lakewoodphone/tesla-lin-chip/hardware/tesla-dual-lin-rev-a/build/quote/jlcpcb-mini-order-2026-05-31/drc-routed-report.txt

** Drc report for tesla-dual-lin-rev-a.kicad_pcb **
** Created on 2026-05-31T14:52:18 **
** Report includes: Errors, Warnings, Exclusions **

** Found 0 DRC violations **

** Found 0 unconnected pads **

** Found 0 Footprint errors **

** Ignored checks **
    - Footprint has no courtyard defined
    - Track endpoint not centered on via
    - Tuning profile track geometries
    - Footprint doesn't match symbol's footprint filters
    - Footprint component type doesn't match footprint pads
    - Footprint doesn't match copy in library

** End of Report **
