lakewoodphone/tesla-lin-chip/BENCH_EVIDENCE.md

# No-Car Bench Evidence

_Updated: May 27, 2026._

This file records the strongest bench-only evidence collected before touching a car. The goal is to prove the APGDT001 -> TJA1021 -> level shifter -> XIAO receive chain, parser, checksum handling, candidate-ID handling, anti-nag replay sequence, and secretary API telemetry path.

**Repository default firmware is passive (`field_passive`).** Active injector firmware with BLE config is explicit via `bench_active_ble` or `chip_lab_active`. In active lab mode, XIAO generates anti-nag frames on UART1 TX with runtime model switching (`model:x`, `model:3`, `model:y`), BLE configuration via "TeslaAntiNag" service, and double-click toggle. See `ACTIVE_INJECTOR.md`.

## Hardware Under Test

- Host: `ZABZ-TECH` desktop
- XIAO: ESP32-C3 on `COM4`, USB VID/PID `303A:1001`
- APGDT001: USB LIN analyzer, VID/PID `04D8:0A04`
- LIN transceiver: TJA1021 module
- Bench LIN baud: `19200`
- Receive path: APG LIN -> TJA1021 LIN/RX -> level shifter -> XIAO D3/GPIO5
- Active TX path: XIAO D2/GPIO4 -> level shifter LV2/HV2 -> TJA1021 TX
- Power: APG VBAT and TJA1021 VIN tied to bench 12V, common ground, SLP high

## Full Evidence Suite

Command:

```powershell
cd C:\Users\ezabz\Code\xiao-lin-bench
.\tools\bench-evidence-suite.ps1 `
  -VehicleId tesla-bench-full-20260526 `
  -ComPort COM4 `
  -Baud 19200 `
  -BootWaitSeconds 2 `
  -PerFrameTimeoutMs 1600 `
  -DelayMs 75
```

Result:

```text
Bench evidence complete: 80/80 exact matches, observed=80, apgFailures=0
```

Phase breakdown:

| Phase | Cases | Observed | Exact Match |
|---|---:|---:|---:|
| baseline | 3 | 3 | 3 |
| candidate | 2 | 2 | 2 |
| checksum | 2 | 2 | 2 |
| id-sweep | 64 | 64 | 64 |
| antinag | 9 | 9 | 9 |

What this proves:

- XIAO receives and decodes every raw LIN ID from `0x00` through `0x3F` on the isolated bench.
- Protected PID parity validates for every sweep case.
- Enhanced checksums validate on normal frames.
- Classic checksum validation is proven on diagnostic `0x3C`.
- Model X control frames on `0x0C` decode correctly for idle, up, down, and neutral.
- Model 3/Y candidate IDs `0x1A` and `0x1B` decode cleanly as bench candidates.
- Anti-nag UP/DOWN replay plus neutral end frame decodes exactly.
- The USB serial fallback path posts parsed frames to the secretary API even while XIAO WiFi is unavailable.

Generated local artifacts are under ignored `logs/`:

```text
logs\bench-evidence-20260526_211956\bench-evidence-20260526_211956.md
logs\bench-evidence-20260526_211956\bench-evidence-20260526_211956.csv
logs\bench-evidence-20260526_211956\bench-evidence-20260526_211956.json
logs\bench-evidence-20260526_211956\xiao-serial-20260526_211956.log
logs\bench-evidence-20260526_211956\apg-send-20260526_211956.log
```

Secretary API verification:

```powershell
curl "http://localhost:8002/api/v1/lin-stats?vehicle=tesla-bench-full-20260526&limit=10000" | python -m json.tool
```

Observed API result:

```text
total_frames=80
bad_checksum=0
bad_parity=0
unique_ids=64
```

## Quick Evidence Suite

Command:

```powershell
.\tools\bench-evidence-suite.ps1 `
  -Quick `
  -VehicleId tesla-bench-quick-20260526 `
  -ComPort COM4 `
  -Baud 19200 `
  -BootWaitSeconds 3 `
  -PerFrameTimeoutMs 1800
```

Result:

```text
Bench evidence complete: 32/32 exact matches, observed=32, apgFailures=0
```

Use the quick suite before field work when time is short. Use the full suite after wiring or parser changes.

## Standalone Anti-Nag Replay

Command:

```powershell
cmd /c %WINDIR%\SysWOW64\WindowsPowerShell\v1.0\powershell.exe `
  -STA -NoProfile -ExecutionPolicy Bypass `
  -File tools\antinag-replay.ps1 `
  -Id 0x0C `
  -Repeat 2 `
  -DelayMs 150 `
  -NeutralFrames 2
```

Result:

```text
Replay complete - 6 frames sent
```

The replay script now launches the APG sender as a fresh 32-bit PowerShell child process per frame. That avoids NetworkAnalyser state leakage and fixes the earlier final-neutral failure.

## New Bench Tools

| Tool | Purpose | Vehicle-safe? |
|---|---|---|
| `tools/bench-evidence-suite.ps1` | Runs baseline, candidate, checksum, raw ID sweep, and anti-nag no-car tests; writes CSV/JSON/Markdown evidence and posts to secretary | No, transmits |
| `tools/serial-to-lin-events.ps1` | Bridges XIAO USB serial decoded frames into `POST /api/v1/lin-events` when WiFi is unavailable | Passive if APG/vehicle is passive |

## Active Injection Status (May 27, 2026)

- Active Model X bench TX is validated on the isolated bench.
- Working firmware break generation: half-baud UART `0x00` break, then normal LIN baud for sync/PID/data/checksum.
- Fixed physical fault: D2 -> level shifter LV2 jumper was disconnected. With `txd:low`, XIAO D2, LV2, and HV2/module TX measured near 0V.
- `model:x` + `antinag:start` produced >100 XIAO self-received/ring-buffer frames on ID `0x0C` with enhanced checksums and parity OK.
- Representative ring evidence:

```text
ID=0x0C PID=0x4C [8B] data: 11 04 00 00 00 00 C0 00 | chk=DD enhanced parity=OK
ID=0x0C PID=0x4C [8B] data: 0F 04 00 00 00 00 C0 02 | chk=DD enhanced parity=OK
ID=0x0C PID=0x4C [8B] data: 10 00 00 00 00 00 C0 0A | chk=D8 enhanced parity=OK
```

NetworkAnalyser event/display passive capture still logged zero rows for XIAO-generated frames during this session, even while XIAO self-receive parsed valid active frames. This is now characterized as a NetworkAnalyser event-layer limitation for externally generated bench frames, not a wiring failure.

`tools/active-bench-proof.ps1` now automates this active self-receive proof and saves a log plus Markdown summary under `logs/`.

### Evening revalidation, 2026-05-27

The latest bench work is summarized in `docs/bench-revalidation-2026-05-27.md`.

- `tools/build-all-envs.ps1` passed for all firmware environments.
- `bench_active_ble` flashed successfully to the physical XIAO on `COM4`.
- BLE advertising was fixed and verified: `cmd: BLE advertising=yes`, with the expected service and characteristic UUIDs. The root cause was an invalid too-fast NimBLE advertising interval that produced `rc=3` / `BLE_HS_EINVAL`.
- Active Model X self-receive proof passed again after APG reseat: `logs\active-bench-proof-20260527_211924.md`.
- Representative proof frames used realistic non-zero payload bytes and validated with enhanced checksum/parity OK:

```text
ID=0x0C PID=0x4C [8B] data: 11 04 10 00 00 00 C0 00 | chk=CD enhanced parity=OK
ID=0x0C PID=0x4C [8B] data: 0F 04 08 02 00 00 C0 02 | chk=D3 enhanced parity=OK
```

- Final XIAO state after the run was safe: `armed=no`, `running=no`, `faults=0`, `lockout=no`, `badChk=0`, `badPid=0`.
- APGDT001 recovered after physical reseat: Windows reports `CM_PROB_NONE`, passive APG transmit works, and raw PICkitS initialization works.
- Quick passive APG -> XIAO validation passed: `logs\xiao-bench-validation-20260527_211238.log`.
- Full passive evidence suite passed again: `logs\bench-evidence-20260527_211310\bench-evidence-20260527_211310.md` with 80/80 exact matches, observed=80, apgFailures=0.
- `tools\active-apg-raw-proof.ps1` now preflights APG raw monitor initialization before active TX, forces `mode:always` during capture to avoid duty-cycle quiet windows, then stops output, runs `safe:off`, and restores `mode:duty`.

## APG Known-ID Raw Observer Proof (May 27, 2026)

The APG does see the XIAO active bench frames at the raw USART buffer layer. `monitor-apg-lin-bus.ps1 -RawFallback` bypasses the NetworkAnalyser event parser, polls `PICkitS.Basic.Retrieve_USART_Data`, scans for 8-byte payload + checksum windows, validates against the assumed raw ID, and writes normal CSV rows with `source=raw`.

Command:

```powershell
powershell -NoProfile -ExecutionPolicy Bypass -File tools\active-apg-raw-proof.ps1 -ComPort COM4 -Baud 19200 -DurationSeconds 6 -MinFrames 8 -ConfirmBenchIsolation
```

Result:

```text
CSV: logs\lin-capture-20260527_212130.csv
XIAO TX lines observed: 41
APG raw rows observed: 11
PASS: APG raw fallback captured 11 checksum-valid known-ID frames.
```

Representative APG raw CSV rows:

```text
ID=0x0C PID=0x4C [8B] data: 0F 04 00 00 00 00 C0 0D source=raw error=0 baud=19200
ID=0x0C PID=0x4C [8B] data: 11 04 00 00 00 00 C0 08 source=raw error=0 baud=19200
ID=0x0C PID=0x4C [8B] data: 0F 04 00 00 00 00 C0 0B source=raw error=0 baud=19200
```

## Remaining No-Car Limits

- The bench can prove parser correctness, checksum behavior, APG send behavior, telemetry plumbing, and XIAO self-received active injection on the isolated bench.
- It cannot identify actual Model 3/Y steering IDs without passive vehicle capture.
- It cannot prove Tesla accepts any anti-nag sequence. Vehicle work must start passive only.
- Generic vehicle discovery still needs normal passive capture because raw fallback requires a known ID. The active Model X bench observer path is proven with APG raw fallback.
- If the APGDT001 returns to Windows failed-start state, recover it before APG-dependent validation; the current post-reseat state is healthy and proven.
