lakewoodphone/tesla-lin-chip/CAPTURE_LOG.md

vehicle_id,model,capture_date,car_day_laptop,notes
tesla-model-x-moti,Model X,2026-05-17,laptop,First successful passive capture - SW white wire seated
tesla-bench-quick-20260526,Bench,2026-05-26,desktop ZABZ-TECH,Quick no-car suite passed 32/32 exact matches and posted 32 USB-serial frames to secretary
tesla-bench-full-20260526,Bench,2026-05-26,desktop ZABZ-TECH,Full no-car suite passed 80/80 exact matches across raw IDs 0x00-0x3F with 0 checksum/parity failures
tesla-model-3-unknown,Model 3,2026-05-26,not-yet,Candidate discovery needed - IDs 0x1A/0x1B suspected
tesla-model-y-unknown,Model Y,2026-05-26,not-yet,Same as 3 - verify IDs independently
