lakewoodphone/tesla-lin-chip/logs/active-bench-proof-20260527_134529.md

# Active Bench Proof 20260527_134529

- Port: COM4
- Model: x
- Duration seconds: 6
- Active acknowledged: True
- Stop acknowledged: True
- TX lines observed: 90
- Valid Model X ring frames: 256
- Bad checksum/parity stats seen: False
- Result: PASS

## Notes

This is isolated-bench evidence only. It uses XIAO self-receive/ring validation because APG passive monitor did not log XIAO-generated active frames during the May 27 validation session.

## Logs

- Text log: C:\Users\ezabz\Code\xiao-lin-bench\logs\active-bench-proof-20260527_134529.log
