lakewoodphone/tesla-lin-chip/logs/sessions/20260528_204047-car-passive-tesla-model-3-20260528/preflight-car-passive-20260528_204050.md

# Hardware Preflight 20260528_204050

- Mode: car-passive
- Created: 2026-05-28T20:40:50
- Result: FAIL
- Failures: slp_high, rx_path, com_port_free, apg_present

| Check | Result |
|---|---|
| 12v_present | 15V |
| common_ground | y |
| slp_high | no |
| lin_idle_voltage | no |
| rx_path | no |
| tx_path | no |
| tx_physical_state | no |
| com_port_free | no |
| apg_present | no |
| notes | no |
