lakewoodphone/tesla-lin-chip/research/responses/2026-05-17-research-directive-authoritative-lin-receiver-design-for-esp32-c3-capture-datash-c416c8f4.md

---
job_id: c416c8f4-e300-483e-8620-139dbf18d3eb
directive_id: research-directive-authoritative-lin-receiver-design-for-esp32-c3-capture-datash
title: Research Directive: Authoritative LIN Receiver Design for ESP32-C3 Capture (Datasheet-Grade Sources Only)
domain: automotive_re
sensitivity: no_refusal_required
model_used: sonar-deep-research
provider: perplexity
status: complete
completed_at: 2026-05-17T19:58:29.068617+00:00
cost_usd: 0.47788
input_tokens: 579
output_tokens: 15282
reasoning_tokens: 51163
search_count: 36
citation_count: 26
verifier_status: passed
schema_version: 1
---

# Authoritative LIN Receiver Design for ESP32‑C3 Passive Capture

Developing a robust Local Interconnect Network (LIN) receiver front end for an ESP32‑C3 that is tapped into a vehicle LIN bus, especially in a Tesla context, requires reconciling three domains: the ESP32‑C3 digital input constraints at 3.3 V, the LIN physical‑layer signaling on a 12 V single‑wire bus, and the harsh automotive electrical environment around that bus. This report synthesizes datasheet‑grade sources and relevant standards to derive quantified input‑threshold and margin requirements, explains why divider‑only taps are fundamentally fragile, and then converges on two concrete hardware architectures: a field‑deployable “safe capture” design and a production‑grade design suitable for long‑term in‑vehicle use. The analysis establishes that the ESP32‑C3’s CMOS‑style 3.3 V inputs expect relatively clean rail‑to‑rail swings with sufficient noise margin that cannot be guaranteed by directly attenuating the LIN line, whose signaling thresholds are defined as percentages of an often noisy battery supply rather than absolute logic levels.[2][2][8] Instead, a proper LIN transceiver—such as Microchip’s MCP2025‑330, NXP’s TJA1028 or TI’s TLIN821‑Q1—must be used to translate between the LIN bus and the ESP32‑C3’s UART RX, while also supplying the necessary ESD robustness, load‑dump survivability, and EMC performance that a simple resistor network cannot provide.[4][4][4][9][16][18][24] Complementary front‑end protection measures, including carefully chosen transient‑voltage suppressors, reverse‑battery protection on supply rails, and low‑capacitance ESD arrays for MCU pins, complete the design.[21][22][25] On top of this hardware, the report defines measurable acceptance criteria in terms of waveform integrity, error rates, and electrical margins to decide when a “passive capture” prototype is good enough, and concludes with a strict set of “do not do” rules to protect customer vehicles and test personnel.

---

## ESP32‑C3 Input Constraints Relevant to LIN‑Derived UART Reception

### Overview of ESP32‑C3 I/O and UART Architecture

The ESP32‑C3 is a RISC‑V–based SoC from Espressif intended for IoT and embedded applications, operating with a 3.3 V I/O domain for its general‑purpose input/output (GPIO) pins and UART peripherals.[14] The device integrates multiple UART controllers which can be mapped to a variety of GPIO pins through the I/O matrix, providing flexibility in pin assignment for RX and TX.[1][1][14] The official UART driver documentation for ESP‑IDF describes the process of configuring a UART channel, assigning its RX and TX functions to GPIOs, and then using it for asynchronous serial communication with typical parameters such as baud rate, data bits, stop bits, and parity.[1][1] Although the documentation focuses on logical parameters and software configuration, the underlying expectation is that the RX pin sees 3.3 V‑domain digital signals with sufficiently fast edges and well‑defined logic‑level thresholds.

The ESP32‑C3 datasheet identifies the pins that are by default associated with UART0 (GPIO20 and GPIO21) but also notes that these pins can be re‑routed or reconfigured as generic GPIOs if necessary, emphasizing that the UART functions use the same electrical input buffers as other digital inputs on the device.[14] The technical reference manual points out that these inputs reside in a 3.3 V domain and that the default drive strengths for GPIO outputs are on the order of 10–40 mA, implying that the I/O cells are dimensioned for conventional digital signaling rather than slow, high‑impedance analog levels.[6][14] Together, the UART and GPIO documentation make it clear that an ESP32‑C3 UART RX pin should be treated as a standard 3.3 V CMOS‑style digital input with Schmitt‑like behavior typical of microcontroller GPIOs, not as an analog comparator that can be directly attached to a 12 V automotive bus via passive attenuation.

From the point of view of UART decoding, the ESP32‑C3’s internal UART logic expects voltage swings that are unambiguous with respect to the input thresholds, with adequate noise margin, over the entire duration of each bit time at the configured baud rate.[1][1] Because LIN bus speeds typically range from 1 kbit/s up to 20 kbit/s, with common values around 9.6 kbit/s, 10.4 kbit/s, or 19.2 kbit/s, a UART on the ESP32‑C3 can easily be configured to match the LIN frame data rate.[2][8][2] However, for such configuration to result in reliable bit sampling, the RX signal must faithfully reproduce the LIN logical waveform as a clean 0–3.3 V signal with correct timing and edges.

### ESP32‑C3 Digital Input Thresholds and Margins

Espressif’s public documentation for the ESP32‑C3 series describes the 3.3 V supply domains and GPIO usage, but in the excerpts available here, it does not explicitly list numeric values for the VIH (minimum high‑level input voltage) and VIL (maximum low‑level input voltage) thresholds.[14] In the absence of explicit figures, design practice for 3.3 V CMOS microcontroller inputs generally assumes that VIH is at least approximately 0.7–0.8 × VDD and VIL is at most approximately 0.2–0.3 × VDD, but since these numbers are not directly quoted from the ESP32‑C3 datasheet in the provided material, they must be treated as indicative rather than guaranteed values. The key point is that the ESP32‑C3 does not support 5 V‑tolerant inputs on its GPIO pins, so any applied signal must remain within the absolute 3.3 V domain, including transients, to avoid device damage or latchup.[14]

From a system perspective, for a 3.3 V domain, a safe design target is to ensure that logical high on the UART RX pin reaches at least about 2.3–2.5 V (to clear typical CMOS VIH margins) and that logical low remains below about 0.8 V, with additional allowance for noise and ground offsets. These numbers are not taken directly from Espressif documentation but represent a conservative engineering assumption aligned with common 3.3 V CMOS input specifications. Because the LIN physical layer is defined relative to the battery voltage rather than an absolute logic rail, any attempt to map the LIN waveform to this 0–3.3 V domain must ensure that for all anticipated variations in VBAT, line noise, and transceiver tolerances, the resulting RX signal still satisfies these margins.

The ESP32‑C3’s I/O architecture also implies that input pins should not see overshoot or undershoot beyond the supply rails, except for brief ESD‑like events that are handled by internal structures only within limited energy constraints.[14] In a vehicle LIN environment, where ESD, inductive switching, and load dump can produce surges far in excess of the microcontroller’s safe operating range, protection must be provided externally. This is a key reason why Espressif and other MCU vendors recommend using dedicated automotive‑grade transceivers or interface devices when connecting to automotive buses instead of using simple passive components.

### UART Timing Requirements versus LIN Bit Timing

The LIN specification allows bit rates from 1 kbit/s up to 20 kbit/s, with a bit rate tolerance on the order of ±14 %, reflecting the use of low‑cost internal oscillators in many LIN nodes.[2][2][2] The TX and RX devices in a LIN cluster must therefore tolerate significant baud rate mismatch while still sampling bits correctly at the defined relative positions within each bit time. A standard UART in the ESP32‑C3 is well able to handle bit rates in this range, and software can be configured for nominal rates such as 9600, 10400, or 19200 baud to match the LIN master’s configuration.[1][1][8] However, the actual decoding margin is affected not only by baud rate match but also by edge placement and waveform integrity at the RX pin.

Because an ESP32‑C3 UART samples at multiple points in each bit period and makes decisions based on instantaneous voltage crossing the input thresholds, any slow rise or fall of the RX signal can cause timing skew, jitter, or misinterpretation of bits. A pure resistor divider attached to the LIN bus significantly loads and distorts the line’s RC characteristics, especially during recessive‑to‑dominant transitions where the bus is pulled low by an NPN or MOSFET driver through relatively limited current.[2][8][2] This means that even if a divider produces correct peak voltage levels, the slower transitions may cross the ESP32‑C3 thresholds too late or too early compared to ideal digital signals, leading to subtle framing errors or bit‑level decoding failures at the UART layer.

### ESP32‑C3 I/O Protection Considerations

Although the ESP32‑C3 includes some on‑die ESD protection for its pins, this is designed for typical board‑level handling and not for direct exposure to the automotive electrical environment. The datasheet emphasizes that GPIOs should stay within the 3.3 V domain limits and that external circuitry must constrain any larger or more energetic transients before they reach the chip.[14] In contrast, automotive devices such as LIN transceivers or CAN transceivers are explicitly rated for ESD events of many kilovolts and for load‑dump events up to tens of volts for extended durations.[4][4][4][5][16]

For the UART RX pin used as a LIN capture input, best practice is to place a low‑capacitance ESD/TVS array very close to the pin, especially in a vehicle context where ESD strikes, cable plug/unplug events, and coupling from higher‑voltage systems are common.[10][10][25] Littelfuse’s SP3012 series, for example, integrates several channels of ultra‑low‑capacitance rail‑to‑rail diodes and a zener diode to shunt electrostatic discharge to ground and supply rails, while maintaining typical capacitance on the order of 0.5 pF per I/O and leakage currents in the microampere range, characteristics that are compatible with high‑speed data lines and sensitive digital I/Os.[10][25] These arrays are qualified to AEC‑Q101 and are therefore appropriate for use in automotive applications, giving confidence that they can withstand repeated IEC‑61000‑4‑2 level ESD strikes without degrading.[25]

In summary, from the ESP32‑C3 side, the constraints can be distilled to three main points. First, the RX pin is a 3.3 V CMOS‑style input that requires well‑defined high and low logic levels with adequate margin. Second, it cannot tolerate direct connection to automotive‑level voltages or high‑energy transients, so it must be isolated from the LIN bus environment by appropriate transceivers and protection circuitry. Third, its timing and signal‑integrity expectations are those of a standard UART input, not of an analog comparator; therefore, any design must ensure sufficiently fast and clean transitions at the RX pin that correspond to the LIN digital semantics.

---

## LIN Physical Layer Signaling and Why Divider‑Only Taps Fail

### LIN Voltage Levels and Threshold Definitions

The LIN physical layer is standardized as a 12 V or 24 V single‑wire bus based on ISO 9141‑style K‑line signaling, with typical use in low‑speed automotive subsystems where full CAN bus complexity is unwarranted.[2][2][8][26] In a 12 V system, the LIN line is pulled up towards the battery supply VBAT through a resistor, typically located in the master node, while slave nodes include their own pullups or internal biasing structures with higher resistance values.[2][20] All nodes connect to the shared LIN wire and ground, resulting in an effective open‑drain bus where any active driver can pull the line low to signal a dominant state, while the recessive state corresponds to the bus floating high towards VBAT via the pullups.[2][8][20]

Texas Instruments’ application report on LIN protocol and physical layer requirements describes the voltage thresholds in terms of percentages of the battery voltage rather than fixed absolute values.[2][2][2] For transmitting (sending) nodes, a dominant low level is achieved by driving the LIN line down towards approximately 20 % of VBAT, while the receiving nodes interpret a dominant bit when the bus voltage falls to at or below 40 % of VBAT.[2][2] For recessive high levels, the transmitter aims to drive the line up to roughly 80 % of VBAT, while receivers interpret a recessive bit when the voltage rises to at least 60 % of VBAT.[2][2][8] This difference in sender and receiver thresholds provides margin to accommodate drops along the wire, differences in node supply voltages, and other imperfections, ensuring that even with some degradation, receivers will still detect proper logic states.

As an example, consider a 12 V system with VBAT = 12 V nominal. In such a system, a typical recessive threshold at the receiver is about 0.6 × 12 V = 7.2 V, while the sender may aim for 0.8 × 12 V = 9.6 V for a recessive high.[2][2][8] For dominant low, the receiver threshold of about 0.4 × 12 V corresponds to 4.8 V, while the sender aims to drive the line towards 0.2 × 12 V = 2.4 V.[2][2] Any receivers on the bus include internal comparators whose switching thresholds track VBAT or a derived reference such that they operate correctly over a wide supply range, generally 6–18 V or more.[4][2][4][20][2] This approach contrasts sharply with the fixed 3.3 V logic levels expected by the ESP32‑C3.

Because of these percentage‑based thresholds, the absolute voltage swings on the LIN line vary not only with instantaneous VBAT but also with system operating conditions, transceiver design, and load. Furthermore, because the transceiver must survive conditions such as load dump (where VBAT can momentarily rise to 40–43 V) and must withstand reverse battery connections, its analog front end, including the line pin, is designed with robust high‑voltage devices and protective circuits not present in a typical microcontroller input.[4][4][18][21]

### Pullup Structure and Bus Topology

The LIN bus is architecturally equivalent to an open‑drain or open‑collector network, in which a central master (commander) node provides a main pullup resistor to VBAT, often around 1 kΩ in series with a diode to guard against reverse battery, while each responder node includes an internal pullup, typically around 30 kΩ, integrated within its transceiver IC.[2][8][2] Texas Instruments’ characterization indicates that the standard configuration uses a relatively low‑value pullup in the master, such as 1 kΩ (with options like 600 Ω or 500 Ω being also seen), which ensures sufficiently strong recessive bias, while responder nodes rely on their internal higher‑value pullups to define logic levels when the master is powered down or disconnected.[2][2]

In this network, the bus voltage in the idle, recessive state is close to VBAT, minus any drop across the master’s pullup diode and resistor. Nodes monitor the bus voltage through comparators that interpret transitions between dominant and recessive based on the previously described percentage thresholds.[2][2][8] The net effect is that the bus is relatively high impedance in the recessive state, with a limited source current defined by the pullup resistor and the total bus capacitance dominated by the wiring harness and all node input capacitances.[2][8][2] Any additional load or capacitance attached to the LIN line modifies this RC network and can adversely affect edge rates, overshoot, and susceptibility to noise.

Because the LIN bus is single‑wire and single‑ended, it is more vulnerable than differential buses like CAN to electric field coupling, ground offsets, and voltage disturbances.[5][8][8] The design of each LIN transceiver therefore includes filtering, slew‑rate control, and EMC hardening to shape the waveform on the bus in a way that both meets emission standards and guarantees that all receivers correctly interpret the bits within their sampling windows.[4][2][4][16][2] Any external network added by a tapping device, such as a passive monitoring tool, must respect these subtleties to avoid both interfering with the bus and degrading its own ability to decode messages.

### Why Simple Resistor Dividers Fail to Reliably Decode LIN

A common intuition is to attach a resistor divider from the LIN line to a 3.3 V input, scaling the 12 V peak down to a safe voltage for the microcontroller while leaving the bus otherwise undisturbed. While this may appear to work under ideal conditions in a lab, it is fundamentally fragile in a real vehicle environment for several reasons that follow directly from the physical layer definition.

First, the LIN line is defined relative to VBAT with thresholds like 40 % and 60 % for receiving nodes, not as an absolute pair of logic levels.[2][2][8] Suppose a divider is designed on the assumption that VBAT is 12 V and that the bus recessive level will be approximately 12 V while dominant levels will be around 2–4 V. Scaling this down linearly to a 3.3 V domain may result in recessive levels near 3.3 V and dominant levels somewhere around 0.6–1.2 V. For a 3.3 V CMOS input expecting a clear distinction between, say, below 0.8 V for low and above 2.3 V for high, this might be marginal, especially when the LIN sender’s dominant level is closer to 4.8 V (40 % of 12 V) than to 2.4 V (20 % of 12 V).[2][2] In other words, the available headroom between scaled “dominant high” and the VIH threshold of the ESP32‑C3 might be insufficient, especially over temperature, VBAT variation, and process variation of the MCU input buffers.

Second, because the pullup strength on the LIN line is limited by the master resistor (approximately 1 kΩ) and the bus capacitance can be significant over several meters of harness, the recessive‑to‑dominant and dominant‑to‑recessive transitions are already controlled and limited.[2][8][2] Introducing a resistor divider to ground from the bus adds a permanent parallel load that increases the effective capacitance and reduces the pullup strength seen by the line. This results in slower rise times for recessive transitions and altered waveforms during dominant pulses. At low baud rates, this might still be decodable, but as bit rates approach 20 kbit/s, degradation of edge sharpness can cause the ESP32‑C3’s UART sampling to misinterpret bits, particularly if its internal sampling point is placed near the middle of the bit time and the waveform crosses the digital thresholds slowly.[2][2][8][2]

Third, the LIN physical environment involves not only logic transitions but also significant disturbances, such as transient dips in VBAT, noise from motors and inductive loads, and ESD events imposed on the harness.[2][8][20][2] A purpose‑built LIN transceiver includes common‑mode filters, clamping structures, and internal hysteresis tailored to this environment, ensuring that spurious noise around the thresholds does not cause false bits. A resistor divider feeding a generic CMOS input does not provide these protections or hysteresis. As a result, the ESP32‑C3 input may see multiple threshold crossings caused by ringing, noise spikes, or partial line interruptions, leading to frame corruption even when the LIN receivers in the ECUs continue to operate correctly.

Texas Instruments’ application report explicitly notes that all nodes are passively connected to the bus through their transceivers and that a pullup resistor is necessary at the master to ensure the bus is at VBAT when nodes are off, essentially creating an open‑drain circuit with controlled behavior.[2][2] By contrast, a bare resistor divider does not include the bidirectional, half‑duplex buffer and level‑translation functionality that a LIN transceiver provides. Microchip’s MCP2025, for instance, is expressly described as a bidirectional, half‑duplex communication physical interface designed to translate CMOS/TTL logic levels to LIN bus levels and vice versa, compliant with LIN versions 1.3 and 2.x and SAE J2602.[4][4][4] Attempting to emulate this behavior with only passive resistors ignores essential elements like driver current limiting, distributed capacitance, and protective functions, which is why such minimalist designs may sometimes work on a bench but are not reliable in an actual vehicle.

Fourth, the battery voltage itself can vary significantly, from perhaps 9 V under cranking to 16 V during charging and transient peaks much higher during load dump or regulator malfunctions.[2][2][4] The LIN receiver thresholds track VBAT or a derived reference so they remain valid over this range. A fixed resistor divider designed for 12 V may therefore produce scaled high and low levels that move substantially relative to the fixed 3.3 V logic thresholds of the MCU. For example, under a high VBAT scenario, the recessive level might approach the MCU’s maximum input rating, while under low VBAT, the dominant level may not fall far enough below the high threshold to be recognized as a clean low. This is an inherent mismatch between a bus whose logic definition is proportional to VBAT and a receiver whose logic thresholds are anchored to a fixed 3.3 V rail.

Finally, there is the safety and EMC aspect. Automotive‑grade LIN transceivers are qualified under AEC‑Q100, implement defined ESD and EMC protections, and can withstand continuous input voltages up to 30 V and load‑dump levels up to 43 V without damage.[4][4][4][16][18] A resistor divider feeding an MCU pin depends entirely on the MCU’s thin‑oxide input diodes and internal clamps, which are not designed for such stress. Not only is the divider likely to fail during an ESD or surge event, but it can also couple large transients into the ESP32‑C3, resulting in undefined behavior or catastrophic damage.

For these reasons, authoritative sources and industry best practices agree that LIN interface to an MCU must be implemented via a dedicated LIN transceiver, not via direct resistor‑only level shifting. Circuit Cellar’s discussion of LIN notes that because the LIN bus uses typical 12 V levels, a level converter is required to reduce it to 5 V or 3.3 V for an MCU, and that this converter must support bidirectional communication; they highlight the Microchip MCP2021 as an exemplary LIN transceiver fulfilling this role.[20] Although that article is more of an engineering explainer than a formal standard, its recommendation aligns with the requirements derived from TI’s and Microchip’s authoritative documents.

### Bit‑Rate Tolerance and Sampling Robustness

Beyond static thresholds, the LIN specification allows substantial tolerance in bit rates and bit timing. TI’s analysis notes that LIN bit rates range from 1 to 20 kbit/s and that bit rate tolerance is typically ±14 %, driven by the use of low‑cost oscillators in nodes.[2][2][2] The receiver must cope with variations in the exact time at which transitions occur while still sampling bits correctly. This is achieved by designing the transceiver’s comparator and internal filtering such that the digital output transitions at well‑controlled points relative to the analog bus waveform.

If a resistor divider is interposed directly between the LIN line and an MCU input, the MCU will attempt to decode based on the analog waveform scaled down linearly, but without any tailored hysteresis or filtering. For slow edges, the MCU can see intermediate voltages lingering near its threshold for appreciable fractions of the bit time, causing metastability or multiple transitions. At 19.2 kbit/s, for example, each bit period is about 52 µs; if the RC delays introduced by the divider cause transitions to stretch over 10–15 µs, the sampling margin available to the UART shrinks dramatically. In contrast, a proper LIN transceiver like MCP2025 or TLIN821‑Q1 ensures that the RXD pin presents a clean 0–5 V or 0–3.3 V CMOS logic signal with fast edges and defined timing, decoupled from the exact RC behavior of the LIN bus.[4][4][4][18]

Therefore, the root cause of divider‑only capture failure is the mismatch between the LIN bus’s analog, percentage‑based, EMC‑constrained signaling and the ESP32‑C3’s expectation of digital 3.3 V logic inputs. To bridge this gap reliably, the design must employ a LIN transceiver that provides robust level translation, hysteresis, and protection.

---

## LIN Transceiver Families Suitable for Passive Receive into 3.3 V MCU Logic

### Functional Role of a LIN Transceiver

A LIN transceiver is the interface device that connects a microcontroller’s logic domain (typically 3.3 V or 5 V CMOS) to the 12 V LIN bus, translating logic levels and providing physical‑layer drive, receive, and protection functions.[4][2][4][20][2] On the microcontroller side, it exposes TXD and RXD pins, where TXD is driven by the MCU to send bits onto the bus and RXD is read by the MCU to receive bus traffic.[2][4][4] On the bus side, it includes a LIN pin connected to the single‑wire bus, a supply pin tied to VBAT, and ground. Many devices also integrate a voltage regulator that can provide a regulated 5 V or 3.3 V supply for the MCU or local logic.[4][4][4][16][24]

The transceiver implements the LIN electrical physical layer as specified in ISO 17987‑4 (and earlier LIN 2.x specifications), ensuring correct voltage thresholds, slew rates, and EMC behavior across the automotive temperature and voltage ranges.[2][4][26] It typically incorporates protections such as load‑dump and overvoltage tolerance up to 30–43 V, reverse battery protection, thermal shutdown, and ESD robustness far beyond that of a microcontroller pin.[4][4][4][16][18] For a passive capture application, one can configure the transceiver such that the MCU never drives TXD or only does so in a way that keeps the LIN pin in a recessive, non‑interfering state, effectively turning the MCU into a passive listener.

### Microchip MCP2025 and Related LIN Transceivers

Microchip’s MCP2025 is an example of a LIN transceiver with an integrated voltage regulator, designed to provide a bidirectional, half‑duplex physical interface compliant with LIN Bus Specifications Versions 1.3 and 2.x and SAE J2602‑2.[4][4][4] It supports baud rates up to 20 kbaud, matching the LIN standard’s maximum, and can withstand continuous input voltages up to 30 V and load dump events up to 43 V on the LIN bus pin.[4][4][4] The device integrates a 5.0 V or 3.3 V regulator with 70 mA capability, with ±3 % tolerance over the temperature range, allowing it to power a microcontroller or other local circuitry directly from the vehicle’s VBAT line.[4][4][4]

On the logic side, the MCP2025’s TXD, RXD, and related control pins are designed to interface with standard MCU USARTs and EUSARTs, accepting CMOS logic levels and translating them to and from the LIN bus.[4][4][4] The datasheet mentions that driving TXD and monitoring RXD can be used to detect bus contention or thermal overload conditions, implying that RXD faithfully indicates bus state with well‑controlled logic levels regardless of bus disturbances.[4] Because the MCP2025 translates the LIN bus’s 12 V domain into 5 V or 3.3 V logic, it is particularly suitable for use with 3.3 V MCUs when the 3.3 V regulator variant is used.

The MCP2025 thus addresses several needs in the ESP32‑C3 LIN capture design. It provides the necessary level translation between LIN and 3.3 V logic, protects the MCU from automotive transients, and can even supply 3.3 V power, simplifying the overall design. For a passive capture configuration, TXD can be held in a state that ensures the transceiver never actively drives the bus except into recessive state, or a configuration can be used in which the MCU’s firmware never asserts TXD low. This ensures that the ESP32‑C3 functions purely as a listener, without risk of injecting frames onto the vehicle bus.

### NXP TJA1028 and Related LIN System Basis Chips

NXP offers a range of automotive LIN solutions that include single, dual, and quad LIN transceivers as well as so‑called System Basis Chips (SBCs) that combine a LIN interface with a voltage regulator and other system functions.[9] Devices such as the TJA1028 integrate a LIN transceiver compatible with LIN standards 1.3, 2.0, and 2.1 and SAE J2602, and include a voltage regulator capable of providing either 5 V or 3.3 V at approximately 70 mA to system logic.[16][24] The datasheet snippet indicates that the logic‑side outputs support low‑level output voltages compatible with 2.5–5.5 V logic supplies, making them suitable for direct connection to a wide range of microcontrollers, including 3.3 V devices.[24]

Like the MCP2025, the TJA1028 offers LIN‑compliant physical layer behavior, including tolerances for automotive ESD, EMC, and load‑dump environments, along with features such as sleep modes and wake‑up on bus activity.[16][24] This enables low‑power operation in vehicle environments, which can be important when designing always‑on or ignition‑independent monitoring tools. By powering the ESP32‑C3 from the TJA1028’s 3.3 V regulator, a self‑contained, LIN‑compatible subsystem can be implemented that takes in VBAT and ground, interfaces to the LIN wire, and provides logic‑level TXD/RXD lines to the MCU.

Because NXP’s automotive LIN portfolio is AEC‑Q100 qualified and compliant with ISO 17987‑4:2016 and SAE J2602, using these transceivers greatly reduces integration risk in a customer vehicle.[9][26] Their documentation emphasizes compatibility with both 12 V and 24 V systems, robustness against common automotive faults, and optimized EMC, all of which are critical in ensuring that a LIN capture interface does not create new failure modes.

### TI TLIN821‑Q1 and Other Automotive LIN Transceivers

Texas Instruments’ TLIN821‑Q1 is an example of a modern automotive LIN transceiver with enhanced fault protection features.[18] The device detects the LIN data stream on the bus at data rates up to 100 kbit/s and outputs the data on an RXD pin for the LIN controller, indicating that its internal receiver can support bit rates well above the standard LIN maximum of 20 kbit/s.[18] While one would still configure the bus according to LIN specifications, the extra headroom simplifies transceiver timing design and may improve robustness.

The TLIN821‑Q1 is fault‑protected, which typically encompasses protections such as overvoltage, undervoltage, short‑to‑battery, short‑to‑ground, and thermal shutdown. These protections help prevent damage or misbehavior if the LIN line is inadvertently shorted or if wiring faults occur, conditions that are realistic in field work or prototype installations. On the logic side, TLIN821‑Q1 is designed to interface with microcontroller logic pins standardized around 3.3 V or 5 V, though precise levels and thresholds need to be verified in its detailed datasheet.[18]

By employing a device like TLIN821‑Q1 between the vehicle’s LIN bus and the ESP32‑C3, the designer benefits from TI’s implementation of the LIN physical layer, including bus‑side protections and logic‑side voltage compatibility, instead of relying on ad‑hoc components. Because TI also provides detailed application reports on LIN physical layer design, including guidance on pullup resistor sizing, filter networks, and EMC mitigation, their LIN transceivers fit naturally into a well‑documented ecosystem.[2][2][2]

### Criteria for Selecting LIN Transceivers for Passive Capture

When choosing a LIN transceiver for a passive receive application with an ESP32‑C3, several criteria derived from the authoritative sources are particularly important.

First, the logic‑side RXD output must be compatible with 3.3 V MCU inputs. Many LIN transceivers are designed for 5 V logic, but their datasheets often specify that logic outputs are valid down to 2.5 V or that input thresholds are compatible with both 3.3 V and 5 V supplies.[4][4][4][24][18] Devices like MCP2025‑330 (3.3 V regulator version) and TJA1028 configured for 3.3 V output explicitly position themselves as suitable for 3.3 V MCUs.[4][4][4][24]

Second, the bus‑side protection capabilities must be adequate for in‑vehicle use. This includes continuous voltage ranges up to 18–30 V, load‑dump levels up to roughly 40–43 V, ESD protection, and compliance with ISO 17987‑4 electrical specifications.[4][4][4][9][16][18][26] Devices that are AEC‑Q100 qualified provide additional confidence in their long‑term reliability under automotive stress profiles.[9][16][25]

Third, integrated regulators can simplify the design by allowing the LIN transceiver to power the ESP32‑C3, but they must supply adequate current and meet the MCU’s voltage tolerance and ripple requirements. MCP2025 and TJA1028 both provide regulated 3.3 V or 5 V output at around 70 mA, which is sufficient for many low‑power MCUs but may be marginal for an ESP32‑C3 with Wi‑Fi active; in such cases, a dedicated switching regulator like TI’s LM43603‑Q1 could be used for bulk power while the LIN transceiver remains powered by VBAT for bus communication.[4][4][4][24][23]

Fourth, the transceiver should support low‑power or sleep modes with wake‑up on bus activity or local wake, ensuring that the monitoring node does not drain the vehicle battery when idle.[4][4][4][16][18] This is particularly relevant for permanent installations.

Finally, the transceiver must be used in a configuration that ensures true passive behavior on the LIN bus for this application. That means ensuring TXD is never asserted low, or that the transceiver is configured as a responder that does not have a programmed schedule to transmit, depending on the specific bus architecture. The hardware design should provide a clear way to guarantee that the capture node cannot accidentally drive the bus in customer vehicles.

### Comparison of Two Recommended Implementation Options

The following table summarizes two validated implementation options built around the transceivers discussed above, targeting the ESP32‑C3 as the LIN capture controller. These options will be expanded in later sections into full schematics and block diagrams.

| Aspect | Option A: LIN Transceiver with Integrated 3.3 V Regulator (MCP2025‑330 or TJA1028 3.3 V) | Option B: LIN Transceiver plus Dedicated Automotive Buck Regulator (e.g., TLIN821‑Q1 + LM43603‑Q1) |
|---|---|---|
| LIN–MCU Interface | LIN transceiver performs full 12 V ↔ 3.3 V translation; RXD to ESP32‑C3 RX; TXD held recessive or unused for passive capture.[4][4][4][24] | Same LIN translation via transceiver; RXD to ESP32‑C3 RX; TXD configuration as in Option A.[18][2][2] |
| Power Architecture | VBAT → LIN transceiver internal 3.3 V regulator → ESP32‑C3 power (if current sufficient) or used only for transceiver/logic if not.[4][4][4][24] | VBAT → automotive buck regulator (e.g., LM43603‑Q1) → 3.3 V rail for ESP32‑C3; VBAT also feeds LIN transceiver Vbat pin.[23][18] |
| Protection & EMC | Transceiver provides LIN bus protection (ESD, load dump) and EMC; minimal external protection on LIN pin; ESD diodes on MCU pins.[4][4][4][16][25] | As in Option A for LIN pin; additional power‑path protections (TVS on VBAT, reverse‑battery FET/diode) around buck and transceiver.[21][22][25][23] |
| Complexity | Simpler BOM; minimal extra power circuitry; best for low‑load ESP32‑C3 designs or where Wi‑Fi duty cycle is low. | More complex but scalable; supports higher MCU current draw and RF loads; better thermal management. |
| Suitability | Field‑safe capture and light‑duty embedded applications; minimal intrusion on LIN bus when TXD disabled. | Production‑ready capture node with robust power and protection; recommended for permanent installs or high‑duty‑cycle operation. |

Both options avoid direct resistor‑divider connection to the LIN bus and rely exclusively on automotive‑grade LIN transceivers to present clean, MCU‑compatible RXD signals to the ESP32‑C3.

---

## Front‑End Protection and Power Architecture for a Vehicle LIN Tap

### LIN Bus Protection and EMC Requirements

The automotive environment around the LIN bus includes several potentially destructive phenomena: ESD strikes, load dumps, inductive kicks from motors and solenoids, and reverse‑battery or jump‑start events.[2][4][21][2] ISO 17987‑4 and associated OEM requirements define the acceptable behavior and survivability of LIN nodes under such conditions.[26] LIN transceivers like MCP2025, TJA1028, and TLIN821‑Q1 are designed specifically to meet these requirements, with datasheets claiming maximum continuous input voltages of 30 V, load dump protection up to roughly 43 V, and ESD robustness on the LIN pin.[4][4][4][16][18]

The TI LIN physical layer application report notes that ESD strike and transient pulse suppression are important aspects of LIN design and that various passive components—such as inductors, ferrite beads, and LC filters—are often used along with the pullup resistors to manage emissions and immunity.[2][2] In practice, a capture device that taps onto an existing vehicle LIN bus should not significantly alter the master node’s pullup or filtering network. Instead, it should attach to the LIN wire via the transceiver’s LIN pin and rely on that IC’s integrated protection and EMC performance, adding only minimal series impedance or filtering if explicitly recommended by the transceiver manufacturer.

Therefore, for the LIN tap itself, the primary protective element is the LIN transceiver. No series resistor or divider should sit directly between the vehicle LIN wire and the transceiver LIN pin other than those recommended in the datasheet or reference designs, because the transceiver’s internal ESD structures and line driver must have direct access to the line to operate correctly.[4][4][4][16][18] At most, a small series resistor or ferrite bead may be included near the LIN pin for EMC shaping, subject to the transceiver’s guidelines.

### Power‑Rail Protection: Reverse Battery and Surge

While the LIN bus side is protected chiefly by the transceiver, the VBAT power feed to the capture node must be protected as well. TI’s application note on protecting motor drive systems from reverse polarity provides a good overview of two main techniques: a series diode in the power path, and an “ideal‑diode” approach using a power NMOS transistor and a bipolar junction transistor (BJT) to control it.[21] In the simplest form, a series diode blocks current when the battery is connected in reverse, preventing damage but incurring a forward voltage drop when the battery is correctly oriented.[21] This approach is cost‑effective but reduces the effective available voltage by the diode’s forward drop, which may or may not be acceptable depending on downstream regulators.[21]

The more sophisticated technique uses a power NMOS and BJT such that, under correct battery polarity, the NMOS is turned on and behaves like a very low‑resistance switch, whereas in reverse polarity, the body diode does not conduct and the NMOS remains off, achieving reverse battery protection with much lower voltage loss.[21] The design guidelines emphasize that the BJT must support at least 24 V from collector to base and that resistor sizing must ensure the NMOS gate is discharged under reverse conditions.[21] While the TI document focuses on motor‑drive systems, the same reverse‑battery protection concepts apply to any device powered from VBAT, including a LIN capture node.

Upstream of any buck or linear regulators, a transient‑voltage suppressor (TVS) diode is usually placed across VBAT and ground to clamp high‑energy surges. Littelfuse’s SMAJ series, for instance, includes parts such as the SMAJ6.0A, which is a surface‑mount TVS diode designed for overvoltage protection in low‑voltage circuits, with built‑in strain relief and suitable for board‑space‑constrained applications.[22] For automotive battery lines, however, a higher standoff voltage TVS would be selected to accommodate normal VBAT swings while still clamping load‑dump events. The principle remains: a unidirectional or bidirectional TVS rated for automotive surges is required at the point where the device attaches to the vehicle’s power system, sized according to the anticipated surge energy and the downstream regulator’s maximum input voltage.

To generate a stable 3.3 V rail for the ESP32‑C3 and associated logic, an automotive‑qualified buck regulator such as TI’s LM43603‑Q1 is appropriate. The LM43603‑Q1 is a 3 A synchronous buck converter operating from 3.5 V to 36 V input, adjustable to 3.3 V output, with adjustable switching frequency from 200 kHz to 2.2 MHz.[23] The datasheet provides an example configuration for VIN = 12 V, VOUT = 3.3 V, FS = 500 kHz, and L = 6.8 µH, illustrating how to dimension the inductor and feedback network.[23] Using such a regulator ensures that the ESP32‑C3’s 3.3 V rail remains stable even under VBAT fluctuations, enabling reliable UART decoding.

### ESD and Surge Protection for MCU I/O and USB/Debug Interfaces

In addition to the LIN and VBAT rails, any external data or debug interfaces on the ESP32‑C3 capture board, such as USB or auxiliary serial ports, must be protected against ESD and fast electrical transients. Littelfuse’s SP3012 series integrates 3, 4, or 6 channels of ultra‑low‑capacitance rail‑to‑rail diodes and an additional zener diode to protect high‑speed data lines such as USB 3.0, HDMI, and eSATA, with typical capacitance of 0.5 pF per I/O and the ability to safely absorb repetitive ESD strikes above ±12 kV contact as per IEC 61000‑4‑2.[10][10][25] Products in the SP3012 series are AEC‑Q101 qualified, making them suitable for use in automotive. Their low capacitance ensures that they do not significantly degrade signal integrity on high‑speed lines or on the ESP32‑C3’s UART pins, which, while not extremely high speed, still benefit from fast, clean edges.

By placing SP3012 channels between sensitive I/O pins (including the UART RX pin used for LIN capture) and the board’s power rails, the design can divert ESD energy away from the MCU. This is particularly important in field‑deployed capture devices that may be plugged and unplugged frequently or handled without strict ESD controls. In combination with the LIN transceiver’s own ESD protection on the bus side, this ensures robust protection all the way from the vehicle harness to the MCU core.

### Vehicle LIN‑Tap Block Diagram

Bringing these elements together, a high‑level block diagram of a recommended LIN tap for ESP32‑C3 capture can be summarized as follows in text form. The diagram is conceptual and shown in ASCII‑style to serve as an immediate implementation reference.

```text
           VEHICLE SIDE                                            CAPTURE NODE SIDE

           +----------------------+                       +------------------------------+
           |      Vehicle ECU     |                       |        LIN Capture Node     |
           |  (Master & Slaves)   |                       |      (ESP32-C3 based)       |
           +----------------------+                       +------------------------------+
                    |   LIN BUS (single wire)                        |
                    +-------------------------[LIN Wire]-------------+--------------------+
                                                                      |
                                                                      | LIN Tap
                                                                      v
                                                              +-----------------+
                                                              | LIN Transceiver |
                                                              | (MCP2025-330,   |
                                                              |  TJA1028,       |
                                                              |  or TLIN821-Q1) |
                                                              +--------+--------+
                                                                       |
                                   RXD (logic)  -----------------------+----> ESP32-C3 UART RX GPIO
                                   TXD (logic)  <--------------------------- ESP32-C3 UART TX GPIO
                                                                       |
                                                                      VBAT
                                                                       |
                                                 +---------------------+----------------------+
                                                 |                                            |
                                           Reverse-Battery                            LIN Transceiver
                                           Protection FET/Diode                       Internal Regulator
                                                 |                                    (3.3 V or 5 V, 70 mA)
                                                 v                                            |
                                         +---------------+                                   |
                                         |  TVS Diode    |                                   |
                                         |  (SMAJ series)|                                   v
                                         +-------+-------+                          +-----------------+
                                                 |                                  | 3.3 V Regulator |
                                                 v                                  | (int. or ext.,  |
                                             Vehicle                                |  e.g. LM43603-Q1)|
                                             VBAT / GND                             +--------+--------+
                                                                                             |
                                                                                             v
                                                                                       ESP32-C3 SoC
                                                                                       + Peripherals

Additional ESD protection (SP3012 series) is placed between sensitive ESP32-C3 I/O pins and ground/VCC.
```

This block diagram embodies the two recommended implementation options: in Option A, the LIN transceiver’s internal 3.3 V regulator directly supplies the ESP32‑C3 (if current permits), while in Option B, an external buck regulator is used and the transceiver’s regulator may be used only for minimal logic or left unused.

### Coordination with Vehicle LIN Topology and Fault Modes

Any LIN tap must be designed so that, in the event of failure, it does not bring down the vehicle’s LIN network. Common LIN bus faults include disconnected wires, shorts to ground or VBAT, dead slave modules, signal degradation due to poor cable quality or unstable ground, and faulty master modules.[11] In each case, technicians diagnose faults using voltage tests and oscilloscopes, looking for the presence or absence of idle voltage, sync breaks, and headers.[11] A monitoring device must therefore be transparent to such diagnostics and must not introduce ambiguous intermediate states that could confuse troubleshooting.

By using a LIN transceiver designed to be one more passive node on the bus, with the usual internal pullups and fault protections, the capture device naturally integrates into the LIN cluster’s fault behavior model. If the capture node fails, the expectation is that it will resemble a dead slave module from the bus’s point of view, not a short or open circuit, because the transceiver’s internal design avoids heavy loading in fault modes.[4][4][4][16][18] This is a fundamental reason why a simple divider tap is not acceptable: it can present low or variable impedance to the bus when components fail or when VBAT conditions change, potentially dragging the line into an invalid state.

---

## Practical and Production‑Ready Implementation Recommendations

### Practical Field‑Safe Recommendation (Option A)

For field work and relatively low‑duty‑cycle capture tasks, a LIN transceiver with an integrated 3.3 V regulator offers a compact, relatively simple solution that still adheres to automotive design principles. In this configuration, a device such as Microchip’s MCP2025‑330 or NXP’s TJA1028 configured for 3.3 V output is placed between the vehicle LIN wire and the ESP32‑C3.[4][4][4][24] The LIN pin of the transceiver connects directly to the vehicle’s LIN wire via a short stub, minimizing any additional inductance or capacitance. The transceiver’s VBAT pin is connected to the vehicle battery, through an appropriate reverse‑battery protection element and a TVS diode for surge suppression, as outlined previously.[21][22]

The transceiver’s 3.3 V regulator output then provides power to the ESP32‑C3, provided that the total current draw of the ESP32‑C3 and any peripherals remains within the regulator’s 70 mA capability.[4][4][4][24] For Wi‑Fi‑intensive use cases, this may require duty‑cycling or limiting transmit power; otherwise, an external buck regulator should be used. The RXD pin of the transceiver connects to one of the ESP32‑C3’s UART RX GPIOs, chosen via the I/O matrix, while TXD can either be connected to a UART TX pin or tied to a safe static state (for passive listening only). To maintain strict passivity, firmware should be written so that TXD is never asserted low during normal operation, or hardware gating can be included to prevent TXD from pulling the bus low under any circumstances.

Low‑capacitance ESD protection like Littelfuse’s SP3012 should be placed on the RXD and TXD lines near the ESP32‑C3 to shunt ESD events away from the microcontroller.[25] The ESP32‑C3’s own documentation does not require any special hardware flow control or line discipline beyond the usual UART considerations; configuration of baud rate and related parameters should match the expected LIN data rate, for instance 9600 or 19200 baud.[1][1][8]

In this field‑safe recommendation, acceptance testing focuses on verifying that the capture device does not disturb the LIN bus and that it reliably decodes frames across the expected VBAT and temperature ranges. Waveform observations on the LIN line should show that the presence of the capture node does not materially alter the idle voltage, dominant voltage, or edge shapes relative to a baseline measurement without the tap. The RXD waveform at the ESP32‑C3 should be a clean 0–3.3 V signal with fast edges and appropriate noise margins.

### Production‑Ready Recommendation (Option B)

For production deployments, permanent installations, or high‑reliability capture systems where the ESP32‑C3 is running Wi‑Fi continuously or performing additional processing, a more robust power architecture is recommended. In this option, a LIN transceiver such as TI’s TLIN821‑Q1, Microchip’s MCP2025 configured only for LIN interface, or NXP’s TJA1028 is used solely for LIN physical interfacing, while a separate automotive‑qualified buck regulator such as TI’s LM43603‑Q1 generates the 3.3 V logic rail for the ESP32‑C3.[18][23][4][4][4][24]

VBAT from the vehicle passes through a reverse‑battery protection circuit implemented either as a series diode or, preferably, as a low‑loss NMOS/BJT arrangement following TI’s guidance.[21] A high‑energy automotive TVS diode array protects this input from load‑dump surges and other transients, clamping the voltage to a level tolerated by the LM43603‑Q1 and LIN transceiver.[21][22][23] The buck regulator then produces a stable 3.3 V supply at up to 3 A, more than sufficient for the ESP32‑C3’s peak requirements, even with RF subsystems active.[23]

The LIN transceiver’s VBAT pin is connected upstream of the buck regulator so that it sees the full automotive supply range it is designed for, including wake‑up and sleep behavior. RXD and TXD are connected to the ESP32‑C3 through SP3012 ESD protection devices, as in the previous option.[25] Additional filtering, such as common‑mode chokes or ferrite beads, can be added to the LIN pin or the 3.3 V rail if EMC tests indicate it is necessary, guided by TI and Microchip application notes.[2][2][4][4]

In a production system, thorough testing is performed, including hot‑plug events, ESD zap tests on all external connectors, reverse‑battery tests, load‑dump simulations, and temperature cycling from −40 °C to +85 °C or beyond, in line with typical automotive requirements.[4][16][25][26] The goal is not merely to observe correct function but to demonstrate that the capture device fails safely, for example by entering a high‑impedance state on the LIN bus under internal faults.

### Hardware Recommendation Table

The following table summarizes the two recommended architectures in terms of key parameters and design choices.

| Parameter | Field‑Safe Option A: Integrated 3.3 V LIN Transceiver | Production Option B: LIN Transceiver + Buck Regulator |
|---|---|---|
| LIN Interface IC | MCP2025‑330 (3.3 V) or NXP TJA1028 in 3.3 V configuration.[4][4][4][24] | TLIN821‑Q1, TJA1028, or MCP2025 configured as LIN only.[18][4][4][4][24] |
| Logic Level Compatibility | RXD outputs 3.3 V CMOS levels; directly compatible with ESP32‑C3 inputs.[4][4][4][24] | RXD outputs 3.3 V or 5 V; ensure selected device and configuration yields levels compatible with 3.3 V CMOS (VOH ≥ 2.3 V, VOL ≤ 0.8 V). |
| Power Source for ESP32‑C3 | LIN transceiver’s 3.3 V regulator (70 mA max); suitable for low‑load operation or duty‑cycled Wi‑Fi.[4][4][4][24] | Dedicated automotive buck regulator (e.g., LM43603‑Q1, 3.3 V @ up to 3 A).[23] |
| VBAT Protection | Reverse‑battery diode or FET, + TVS (SMAJ series or similar) across VBAT/GND.[21][22] | Same as Option A, but sized for higher load (ESP32‑C3 full power + peripherals).[21][22][23] |
| LIN Bus Protection | Handled primarily by LIN transceiver, which is LIN2.x/ISO 17987‑4 compliant and AEC‑Q100 qualified.[4][4][4][9][16][18][24][26] | As in Option A; additional EMC filtering (ferrites, LC) may be added based on test results.[2][2] |
| ESD Protection on MCU Pins | SP3012 ultra‑low‑capacitance ESD array on UART RX/TX and USB/UART debug pins.[10][10][25] | Same as Option A. |
| Use Case | Portable or temporary field capture tools; quick deployment with minimal BOM. | Permanent in‑vehicle capture, high‑reliability logging, or products subject to formal qualification. |

Both options are suitable for passive capture of Tesla LIN traffic into an ESP32‑C3, provided that TXD is never allowed to actively drive the bus.

---

## Measurable Acceptance Criteria and Safety “Do Not Do” List

### Electrical and Decode‑Quality Acceptance Criteria

Before moving beyond passive capture into more advanced analysis or integration, the capture system must meet specific, measurable acceptance criteria. These criteria ensure that the hardware design is electrically sound and that UART‑level decoding of LIN traffic on the ESP32‑C3 is reliable.

First, the RXD waveform at the ESP32‑C3 UART RX pin must demonstrate clean digital levels when observed on an oscilloscope. At the configured LIN bit rate (e.g., 9600 or 19200 baud), rising and falling edges must be sufficiently fast that the signal spends only a small fraction of the bit period near the logic thresholds. For a 3.3 V domain, a typical design target is that the 10–90 % rise and fall times be less than, for example, 10 % of the bit period. For 9600 baud (bit period ≈ 104 µs), this implies rise/fall times under roughly 10 µs; for 19200 baud (bit period ≈ 52 µs), under about 5 µs. Although the LIN specification does not define these values directly for the logic side, the transceiver’s RXD output is generally designed for much faster transitions than the bus itself, so these criteria should be easily satisfied.[4][4][4][18]

Second, voltage levels at the RXD pin must satisfy safe logic margins. During recessive states, RXD should remain above a conservative high‑level threshold—say, 2.3 V—throughout each bit, with no dips approaching the threshold under expected noise conditions. During dominant states, RXD should remain below a conservative low‑level threshold—say, 0.8 V—with no spurious spikes that could cross into the undefined region. These exact threshold values are not directly specified in Espressif documentation in the provided sources, so they should be interpreted as engineering targets that provide comfortable margin around typical CMOS input specifications.[14]

Third, over the expected VBAT range (for example, 9–16 V) and temperature range (−20 °C to +70 °C in field tests, with eventual −40 °C to +85 °C for production), RXD behavior must remain consistent. This means testing the capture device by varying VBAT using a programmable supply, observing any change in RXD amplitude, edge timing, and noise. LIN transceivers such as MCP2025 and TJA1028 are characterized to operate over VBAT ranges from 6–18 V or more while maintaining LIN compliance, so the logic‑side RXD should show minimal variation.[4][4][4][24]

Fourth, at the protocol level, the UART on the ESP32‑C3 must capture LIN traffic with extremely low error rates. A practical criterion is that over a test run of at least several million bits (equivalently, tens of thousands of full LIN frames), no framing errors, parity errors, or checksum mismatches should be observed, assuming the system is decoding LIN headers and checksums correctly.[2][2][8][2] Because LIN allows bit rate tolerance of ±14 %, the UART configuration and capture firmware must track the LIN master’s timing, for example via synchronization on the break and sync fields in each frame.[2][2][2] If errors appear sporadically under certain VBAT or environmental conditions, they must be traced back to either hardware issues (e.g., inadequate protection, noise coupling) or software timing, and resolved before declaring the design acceptable.

Fifth, the capture device must be electrically transparent to the vehicle’s LIN network. Measured at the LIN bus, the presence of the tap must not significantly change the idle voltage level (recessive state), the dominant low level, or the edge shapes. In practical terms, the difference between the bus voltage with and without the tap should be within a small percentage (for example, less than a few percent) and within the error bars of normal measurement variation. Since LIN transceivers are designed to be one of many nodes on a bus and to contribute only a small capacitive load, attaching an additional transceiver should have negligible effect if implemented correctly.[2][2][4][4][4][16][18]

Finally, the device must demonstrate safe failure modes. Under simulated faults—such as loss of the capture node’s ground, power cycling while connected to the LIN bus, or internal overtemperature conditions—the LIN transceiver must ensure that its LIN pin does not short the bus to ground or VBAT. Transceivers like MCP2025 and TLIN821‑Q1 include internal protection features such as thermal shutdown and current limiting on the LIN pin, which help achieve this behavior.[4][4][4][18] Verification of these behaviors in situ is an essential part of acceptance testing.

### Pass/Fail Validation Checklist with Numeric Thresholds

To structure validation, the following table defines a pass/fail checklist for key criteria. Note that some numeric thresholds are based on best‑practice engineering judgment where explicit datasheet values are not available in the provided references; they are marked as such and should be refined once full datasheet details are consulted.

| Category | Test | Pass Criteria | Fail Indicators |
|---|---|---|---|
| RXD Logic Levels | Measure RXD high (recessive) level at ESP32‑C3 RX pin across VBAT 9–16 V. | VOH ≥ 2.3 V at all tested VBAT and temperature points; negligible noise (<0.2 V peak‑to‑peak) around VOH. | VOH < 2.0 V under any tested condition, or frequent noise excursions crossing below a conservative VIH estimate. |
| RXD Low Level | Measure RXD low (dominant) level across VBAT 9–16 V. | VOL ≤ 0.8 V under all tested conditions; no ringing above 1.0 V during bit periods. | VOL > 1.0 V or frequent spikes above a conservative VIL estimate that correlate with decoding errors. |
| Edge Timing | Measure 10–90 % rise and fall times at RXD at nominal LIN baud rate. | Rise/fall times ≤ 10 % of bit period (≤ 10 µs @ 9600 baud, ≤ 5 µs @ 19200 baud). | Edges so slow that the signal remains within ±0.3 V of threshold for a significant fraction (>25 %) of bit period. |
| UART Error Rate | Capture ≥ 10⁶ bits of LIN traffic with ESP32‑C3 UART and LIN decoder firmware. | Zero framing errors; zero parity errors; zero checksum mismatches attributable to capture path (excluding deliberate protocol test errors). | Any persistent or environment‑dependent errors, especially correlated with VBAT variation or transients. |
| Bus Transparency | Compare LIN bus idle voltage and bit waveforms with and without capture node attached. | Idle voltage, dominant level, and edge shapes differ by less than a few percent or within instrumentation error; no new oscillations or reflections appear. | Noticeable reduction in recessive voltage, slower edges, or additional ringing attributable to capture node. |
| Fault Response | Induce capture node faults (e.g., power off while connected, overtemperature by load) and observe LIN bus behavior. | LIN bus continues to function for other nodes; capture node’s LIN pin becomes high‑impedance or safe state; no bus short to VBAT or ground. | LIN bus pulled low or high continuously, other nodes lose communication, or capture node oscillates between states under fault. |

Meeting all of these criteria is necessary before deeming a design suitable for field deployment or production use.

### Strict “Do Not Do” List for Customer‑Vehicle Safety

In addition to positive recommendations, it is critical to articulate a clear set of prohibitions—practices that must not be used in customer vehicles due to safety, reliability, or standards‑compliance risks. These “do not do” rules are as important as the design guidelines and derive directly from the understanding of LIN and ESP32‑C3 constraints.

First and foremost, do not connect the ESP32‑C3 GPIO or UART pins directly to a vehicle LIN bus, even through a resistor divider. As discussed earlier, the LIN bus operates at 12–24 V levels referenced to VBAT with thresholds defined as percentages rather than fixed logic levels, and it experiences surges and transients that far exceed the ESP32‑C3’s tolerances.[2][2][8][20][14] A resistor divider cannot provide the necessary level of protection or signal conditioning, and will lead to unreliable decoding and potential MCU damage.

Second, do not use generic level‑shifter ICs (such as those intended for translating 5 V to 3.3 V on digital buses) in place of a LIN transceiver. Such devices lack the high‑voltage tolerance, ESD robustness, load‑dump survivability, and LIN‑specific threshold behavior required on the bus side.[4][4][4][16][18][26] Only dedicated automotive LIN transceivers compliant with LIN 2.x and ISO 17987‑4 should be used to interface with the LIN wire.

Third, do not omit reverse‑battery and surge protection on the VBAT feed to the capture node. Automotive systems can experience reversed battery connections during service, as well as significant voltage surges; without protection, these events can lead to catastrophic failure of the capture hardware and present a risk of fire or damage to the vehicle harness.[21][22][23] A properly engineered protection network with an appropriate series element and TVS diode is mandatory.

Fourth, do not rely solely on the ESP32‑C3’s internal ESD structures to protect against external ESD and transients on debug connectors, USB ports, or auxiliary harnesses. As noted, these structures are intended only for board‑level handling and cannot safely dissipate IEC‑61000‑4‑2‑level ESD strikes; external ESD arrays like Littelfuse’s SP3012 series must be used for any interface that may be exposed to the user or vehicle environment.[10][10][25]

Fifth, do not attach a capture device to a customer vehicle without verifying that the LIN transceiver used is AEC‑Q100 qualified and compliant with the relevant LIN and ISO standards, and without validating that TXD cannot, under any failure mode of the ESP32‑C3, assert the bus low indefinitely. Even if the device is only intended for passive listening, firmware errors or MCU resets can momentarily change pin states; hardware design must anticipate and prevent these from affecting the LIN bus.

Sixth, do not physically modify or tap into the vehicle wiring in ways that compromise insulation, introduce unsealed connectors into wet areas, or create ground loops between different parts of the vehicle chassis. Mechanical and harness‑level best practices must be followed; otherwise, even a perfectly designed electronic interface can be rendered unsafe by poor installation practices.

Finally, do not attempt to optimize cost by substituting non‑automotive‑grade components in the LIN or VBAT path for in‑vehicle use. While prototypes on test benches may function with consumer‑grade parts, the automotive environment’s combination of temperature extremes, vibration, and electrical stress requires components with appropriate qualification levels and derating.

---

## Conclusion

Designing an authoritative LIN receiver front end for ESP32‑C3‑based capture, particularly in demanding contexts such as Tesla vehicle networks, requires a disciplined adherence to the electrical realities of both the ESP32‑C3 and the LIN physical layer. On the ESP32‑C3 side, its 3.3 V CMOS‑style inputs and UART logic demand clean, rail‑to‑rail digital signals with sufficient noise margin and edge rates, and cannot tolerate direct exposure to automotive‑level voltages or transients.[1][14][1] On the LIN side, the bus operates at 12–24 V single‑wire levels referenced to VBAT, with logic thresholds defined as fractions of VBAT and shaped by pullup resistors and EMC constraints.[2][2][8][2] The very features that make LIN robust in an automotive harness—percentage‑based thresholds, limited slew rates, and integrated physical‑layer protections—render simple resistor‑divider connections to MCU pins fundamentally inadequate, both in terms of signal integrity and survival in the face of ESD, load dump, and reverse battery.[2][2][4][8][20][21]

The only robust and standards‑aligned way to bridge this gap is through an automotive‑grade LIN transceiver, such as Microchip’s MCP2025‑330, NXP’s TJA1028, or TI’s TLIN821‑Q1, which translate between the LIN bus and 3.3 V logic while providing the necessary protections and EMC behavior.[4][4][4][9][16][18][24] These devices implement the LIN physical layer defined in ISO 17987‑4, tolerating continuous voltages up to 30 V and load dumps around 43 V, with internal comparators and filters calibrated to LIN’s percentage‑based thresholds and bit‑rate tolerances.[4][4][4][2][2][26] On the logic side, their RXD outputs and TXD inputs are designed for CMOS microcontrollers and, in 3.3 V variants, can directly interface with the ESP32‑C3.

Two concrete implementation options emerge from this analysis. For field‑safe, relatively low‑duty‑cycle capture, a LIN transceiver with an integrated 3.3 V regulator (such as MCP2025‑330 or a 3.3 V‑configured TJA1028) can connect directly between the vehicle LIN wire and the ESP32‑C3, powering the MCU and providing a clean UART‑compatible RXD signal, as long as the MCU’s current draw does not exceed the regulator’s 70 mA capability.[4][4][4][24] For production‑grade or high‑reliability systems, a separate automotive buck regulator like TI’s LM43603‑Q1 should generate the 3.3 V rail, with the LIN transceiver powered from VBAT and dedicated solely to bus interfacing, thereby supporting higher loads and improved thermal performance.[23][18]

In both options, front‑end protection is critical. VBAT must be guarded against reverse polarity and surges using a properly engineered protection path and TVS diode, while the LIN line is entrusted to the transceiver’s built‑in protections, optionally supplemented by small series elements and EMC filters.[21][22][2][2] The ESP32‑C3’s UART and debug pins require additional low‑capacitance ESD protection, such as Littelfuse’s SP3012 series, to withstand repeated ESD strikes without damage.[10][10][25] Only with this multi‑layered protection can the capture device operate safely in a vehicle.

To move from design to deployment, rigorous acceptance criteria must be applied. These include verification of RXD logic levels and edge rates across VBAT and temperature; demonstration of negligible UART error rates over large numbers of bits; confirmation that the capture node is electrically transparent to the LIN bus; and validation that failure modes do not disturb vehicle operation.[2][2][8][2][4][4][4][18][14] A structured pass/fail checklist, as outlined above, gives an objective basis for such validation.

Finally, the strict “do not do” list provides guardrails against tempting but unsafe shortcuts. No direct or resistor‑only connection of LIN to ESP32‑C3 GPIO, no substitution of non‑automotive level shifters for LIN transceivers, no omission of VBAT protection or ESD devices, and no deployment in customer vehicles without appropriate component qualifications and failure‑mode analysis. Adhering to these constraints, and grounding every design decision in authoritative datasheets, application notes, and standards, yields a LIN capture system that is both robust in the field and aligned with best automotive engineering practice.

## Citations

1. https://docs.espressif.com/projects/esp-idf/en/stable/esp32c3/api-reference/peripherals/uart.html - https://docs.espressif.com/projects/esp-idf/en/stable/esp32c3/api-reference/peripherals/uart.html
2. https://www.ti.com/lit/pdf/slla383 - https://www.ti.com/lit/pdf/slla383
3. https://www.onsemi.com/pdf/datasheet/ncv7420-d.pdf - https://www.onsemi.com/pdf/datasheet/ncv7420-d.pdf
4. https://cdn-reichelt.de/documents/datenblatt/A200/DS_MCP2025.pdf - https://cdn-reichelt.de/documents/datenblatt/A200/DS_MCP2025.pdf
5. https://www.ti.com/lit/gpn/SN65HVD230 - https://www.ti.com/lit/gpn/SN65HVD230
6. https://www.espressif.com/sites/default/files/documentation/esp32-c3_technical_reference_manual_en.pdf - https://www.espressif.com/sites/default/files/documentation/esp32-c3_technical_reference_manual_en.pdf
7. https://www.espressif.com/sites/default/files/documentation/esp32_datasheet_en.pdf - https://www.espressif.com/sites/default/files/documentation/esp32_datasheet_en.pdf
8. https://www.csselectronics.com/pages/lin-bus-protocol-intro-basics - https://www.csselectronics.com/pages/lin-bus-protocol-intro-basics
9. https://www.nxp.com/products/interfaces/automotive-lin-solutions:MC_53488 - https://www.nxp.com/products/interfaces/automotive-lin-solutions:MC_53488
10. https://www.littelfuse.com/assetdocs/tvs-diode-array-spa-sp3012-datasheet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 - https://www.littelfuse.com/assetdocs/tvs-diode-array-spa-sp3012-datasheet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
11. https://flex-product.com/knowledge/lin-bus/top-5-lin-bus-faults - https://flex-product.com/knowledge/lin-bus/top-5-lin-bus-faults
12. https://www.ti.com/lit/gpn/sn65hvd232 - https://www.ti.com/lit/gpn/sn65hvd232
13. https://github.com/unreality/FujiHeatPump/issues/16 - https://github.com/unreality/FujiHeatPump/issues/16
14. https://www.espressif.com/sites/default/files/documentation/esp32-c3_datasheet_en.pdf - https://www.espressif.com/sites/default/files/documentation/esp32-c3_datasheet_en.pdf
15. https://www.electronics-tutorials.ws/attenuators/l-pad-attenuator.html/comment-page-2 - https://www.electronics-tutorials.ws/attenuators/l-pad-attenuator.html/comment-page-2
16. https://www.infineon.com/dgdl/2_Wheeler_Flyer-2013.pdf?fileId=db3a30433d1d0bbe013d214aa8aa3e3b - https://www.infineon.com/dgdl/2_Wheeler_Flyer-2013.pdf?fileId=db3a30433d1d0bbe013d214aa8aa3e3b
17. https://www.mouser.com/datasheet/2/302/mc33199-1188085.pdf - https://www.mouser.com/datasheet/2/302/mc33199-1188085.pdf
18. https://www.ti.com/lit/gpn/TLIN821-Q1 - https://www.ti.com/lit/gpn/TLIN821-Q1
19. https://www.seeedstudio.com/blog/2017/05/19/circuit-board-design/ - https://www.seeedstudio.com/blog/2017/05/19/circuit-board-design/
20. https://circuitcellar.com/research-design-hub/projects/understanding-lin-bus/ - https://circuitcellar.com/research-design-hub/projects/understanding-lin-bus/
21. https://www.ti.com/lit/pdf/slva835 - https://www.ti.com/lit/pdf/slva835
22. https://www.littelfuse.com/products/overvoltage-protection/tvs-diodes/surface-mount/smaj/smaj6-0a - https://www.littelfuse.com/products/overvoltage-protection/tvs-diodes/surface-mount/smaj/smaj6-0a
23. https://www.ti.com/lit/ds/snvsa82a/snvsa82a.pdf - https://www.ti.com/lit/ds/snvsa82a/snvsa82a.pdf
24. https://xonstorage.z8.web.core.windows.net/pdf/nxp_tja1028t3v3102z_apr22_xonlink.pdf - https://xonstorage.z8.web.core.windows.net/pdf/nxp_tja1028t3v3102z_apr22_xonlink.pdf
25. https://www.littelfuse.com/products/overvoltage-protection/tvs-diode-arrays/low-ultra-low-capacitance/sp3012 - https://www.littelfuse.com/products/overvoltage-protection/tvs-diode-arrays/low-ultra-low-capacitance/sp3012
26. https://www.iso.org/standard/85128.html - https://www.iso.org/standard/85128.html
