lakewoodphone/tesla-lin-chip/research/directives/046-esp32c3-native-usb-cdc-platformio-windows-reliability.md

# Research Directive: ESP32-C3 Native USB CDC Reliability on Windows (PlatformIO Field Workflow)

**Directive ID**: 046-esp32c3-native-usb-cdc-platformio-windows-reliability  
**Date Issued**: 2026-05-17  
**Requestor**: ezabz  
**Priority**: High  
**Category**: embedded-tooling / platformio / windows / esp32

---

## Context

Device: Seeed Studio XIAO ESP32-C3 (native USB-Serial/JTAG), COM6 (`VID_303A PID_1001`).

Observed behavior during field debug:

- firmware sometimes flashes but monitor initially shows no Serial
- reset triggers CDC re-enumeration and monitor disconnect behavior
- PlatformIO stub upload path can be unreliable in this setup
- direct esptool `--no-stub` at 115200 is currently the stable flashing path

Current known-good configuration includes:

- `-DARDUINO_USB_MODE=1`
- `-DARDUINO_USB_CDC_ON_BOOT=1`
- `monitor_dtr = 0`
- `monitor_rts = 0`

Need formalized best-practice for repeatable field operations on Windows.

---

## Questions

1. What are the canonical PlatformIO + Arduino-ESP32 settings for ESP32-C3 native USB CDC logging and reset/upload stability on Windows?
2. What are known failure modes with monitor open/close, DTR/RTS toggles, and COM re-enumeration for native USB ESP32-C3 boards?
3. What is the recommended upload fallback sequence when normal upload fails (including BOOT/RST procedure and no-stub esptool)?
4. Should applications log through `Serial`, `USBSerial`, or another API under current Arduino-ESP32 versions, and under which compile flags?
5. What field-safe logging fallback should be used if native USB CDC is temporarily unreliable?

---

## Required Output

Return:

1. A "known-good" `platformio.ini` template for XIAO ESP32-C3 on Windows.
2. A failure-mode troubleshooting ladder in strict operator order.
3. A standard flashing command recipe (normal and fallback).
4. Firmware-side logging patterns that survive reconnect churn.
5. A compact runbook that a technician can execute under time pressure.

Prefer official docs/issues from Espressif, PlatformIO, and Seeed.
