lakewoodphone/tesla-lin-chip/research/directives/054-nrf5340-firmware-protection-anti-cloning-anti-abuse.md

---
title: nRF5340 firmware protection, anti-cloning, and anti-abuse architecture for compact dual-LIN BLE board
date: 2026-05-29
requester: Eliyahu Zabrowsky
status: draft
---

# Research Directive: nRF5340 Firmware Protection, Anti-Cloning, and Anti-Abuse Architecture

## Context

We are designing a compact single-board bench-only dual-LIN BLE research fixture for Tesla Model 3/Y steering-wheel LIN work. The preferred hardware path is a custom PCB around a certified nRF5340 module, primarily u-blox NORA-B106/NORA-B1, with Ezurio BL5340 as the main alternate. The board includes two automotive LIN transceivers, protected 12V input, keyed connectors, USB-C, SWD, physical mode/arm controls, BLE provisioning, signed DFU, and VIN/test-fixture binding.

The owner has a new hard safety and product-security requirement:

- A third party must not be able to simply plug into the board and read/copy the firmware.
- The board must require activation/provisioning over BLE/USB with the right codes.
- It should bind to an authorized fixture/car label and be hard to clone or repurpose.
- It must be difficult to abuse on public roads or use as a generic active vehicle-control device.
- Safety controls should be realistic and layered, not hand-wavy.

The system is bench-only. Do not research or propose ways to bypass Tesla security, unlock vehicles, or attack vehicle networks. Focus on legitimate embedded product protection, firmware IP protection, anti-cloning, signed update, secure provisioning, and anti-abuse controls.

Use exactly two analysis lenses:

1. Compass: embedded security/product architecture lens focused on realistic threat model, MCU protections, secure boot/DFU, key lifecycle, manufacturing provisioning, and clone resistance.
2. Gemini: hardware/manufacturing/safety lens focused on physical debug access, SWD locks, service/recovery flow, tamper evidence, physical arm gates, connector strategy, bench-only limits, and operational safety.

## Questions To Answer

1. What nRF5340 security features are available and relevant for firmware readout protection and clone resistance?
   - SWD/JTAG/debug lock/readout protection mechanisms.
   - APPROTECT / ERASEPROTECT / CTRL-AP behavior if applicable.
   - Secure boot support, MCUboot, TF-M/Trusted Firmware-M, CryptoCell, KMU, UICR, OTP or device identity options.
   - Whether u-blox NORA-B1 and Ezurio BL5340 expose/support these features.

2. What is the practical threat model?
   - Casual user plugging in USB/SWD.
   - Competent electronics hobbyist with SWD tools.
   - Firmware update package extraction.
   - Cloning one board to another.
   - Physical invasive lab attacks/glitching/decap.
   - Malicious road-use repurposing.

3. What controls should Rev A implement?
   - Production provisioning sequence.
   - Per-device keys and secrets.
   - Signed firmware and signed config/profile packages.
   - BLE proof-of-possession and admin bonding.
   - VIN/test-fixture binding design.
   - Debug lock and service unlock policy.
   - Secure logs/event counters.
   - Hardware TX default-off gates.
   - Physical mode/arm/service interlocks.
   - Bench-only enforcement.

4. What controls are not realistic or not enough?
   - Why encryption alone is not sufficient.
   - Why readout protection is not absolute against invasive attacks.
   - Why VIN binding must be operator-provisioned and should not scrape vehicle networks.
   - Why no software lock can guarantee road-use prevention without physical/operational constraints.

5. Produce a concrete architecture recommendation for Rev A and Rev B.
   - Required board features.
   - Required bootloader/security configuration.
   - Manufacturing/provisioning steps.
   - BLE/USB activation flow.
   - Binding/rebinding flow.
   - Recovery/unbrick flow without weakening protection.
   - Test checklist.

## Desired Output

Return a concise but thorough report with:

- Executive recommendation.
- Threat model table.
- nRF5340/NORA-B1/BL5340 feature summary with citations.
- Required Rev A security controls.
- Recommended provisioning and activation flow.
- Bench-only anti-abuse controls.
- Limits/residual risk.
- Concrete doc-ready requirements that can be copied into the board architecture docs.
