lakewoodphone/tesla-lin-chip/research/responses/2026-05-10-tesla-model-3-y-steering-wheel-lin-bus-frame-id-research-835ddcac.md

---
job_id: 835ddcac-7600-4297-aefc-1878f0b5d6bf
directive_id: tesla-model-3-y-steering-wheel-lin-bus-frame-id-research
title: Tesla Model 3/Y Steering Wheel LIN Bus Frame ID Research
domain: automotive_re
sensitivity: no_refusal_required
model_used: sonar-deep-research
provider: perplexity
status: complete
completed_at: 2026-05-10T19:26:07.060336+00:00
cost_usd: 0.40405
input_tokens: 497
output_tokens: 8993
reasoning_tokens: 44952
search_count: 36
citation_count: 26
verifier_status: passed
schema_version: 1
---

# Tesla Model 3/Y Steering Wheel LIN Bus Frame ID Architecture: A Comprehensive Technical Analysis

This report presents a detailed investigation into the LIN (Local Interconnect Network) bus frame identification system used by Tesla Model 3 and Model Y steering wheel control modules, with particular emphasis on the left scroll wheel (VCLEFT) communication protocol. Based on available technical documentation, community research, and automotive protocol analysis, this investigation synthesizes evidence regarding the specific frame identifiers used for scroll wheel signal transmission, the data encoding methodology employed by the LIN bus for steering wheel functions, and the mechanisms through which aftermarket anti-nag modules interact with this communication architecture. The research reveals that while direct factory documentation for LIN frame IDs remains proprietary, community reverse engineering efforts have identified key frame identifiers such as 0x4C for left-side steering wheel controls on Tesla models, alongside detailed protocol specifications that inform both legitimate diagnostic work and aftermarket module development.

## Tesla Vehicle Network Architecture and the Role of LIN Bus Communication

Tesla vehicles employ a sophisticated hierarchical network architecture that integrates multiple communication protocols to manage the vast array of electronic control modules distributed throughout the vehicle. The primary communication backbone consists of the CAN (Controller Area Network) bus, which handles high-priority vehicle dynamics, drivetrain management, and real-time safety-critical functions[15]. However, alongside this main CAN infrastructure, Tesla engineers implemented a complementary LIN bus network specifically designed to manage lower-bandwidth, deterministic communication requirements for peripheral control systems. The LIN bus serves as a supplement to the CAN bus in the Tesla architecture[15], creating a specialized subsystem for steering column and switching controls that operate at predictable, scheduled intervals rather than the event-driven arbitration model of CAN.

The implementation of LIN bus technology in Tesla's steering wheel control systems addresses specific engineering requirements that differ from traditional high-speed CAN applications. LIN buses operate at significantly lower baud rates compared to CAN networks, with Tesla steering wheel systems confirmed to operate at 19,200 bits per second[7]. This lower speed requirement reflects the nature of steering wheel input signals, which include scroll wheel increments, button presses, and stalk positions that need reliable delivery but do not demand the ultra-high bandwidth of powertrain control. The deterministic scheduling inherent to LIN protocol ensures that steering wheel input data reaches its destination with predictable latency, a critical requirement for systems like automated driver assistance features that depend on responsive steering wheel input acknowledgment.

The Body Control Module (BCM), specifically the variant designated VCLEFT in Tesla's architecture, serves as the LIN master that orchestrates all communication with peripheral steering wheel switch modules[9][9]. This master-slave relationship differs fundamentally from CAN's multi-master arbitration model. The VCLEFT module, located in the vehicle's interior electrical architecture, periodically polls specific LIN slave devices—primarily the steering wheel switch module containing the scroll wheels and other input controls—according to a predetermined schedule table. This schedule determines which frame identifiers are requested at what time intervals, creating a highly organized communication pattern that contrasts sharply with the dynamic, priority-based message arbitration of CAN.

## Steering Wheel Control Module Architecture and Component Integration

The Tesla Model 3 and Model Y steering wheel assembly integrates multiple electrical components that communicate through both traditional wired connections and the LIN protocol. The steering wheel itself houses physical input devices including the left and right scroll wheels, the horn contact pad, and various stalks for turn signals, wipers, and drive mode selection[14][6]. Each of these input devices generates electrical signals that must be transmitted to the vehicle's control systems with minimal latency and high reliability. The left scroll wheel specifically controls vehicle functions including mirror adjustment, volume control, wiper speed, and—when integrated with the autopilot system—follow distance and automated steering parameters[14][6].

The steering column control module, also referred to as the clockspring assembly or steering column control module in Tesla service documentation, serves as the physical and electrical interface between the steering wheel's rotating input devices and the vehicle's stationary electrical harness[12][17][12]. This module performs multiple critical functions including the transmission of steering angle data from the steering angle sensor, consolidation of steering wheel input signals, and relay of these signals to appropriate vehicle systems. The clockspring mechanism, which maintains electrical continuity as the steering wheel rotates, was historically responsible for transmitting these signals through dedicated wiring harnesses. However, in modern Tesla architecture, much of this communication has been reimplemented using the LIN protocol to reduce wiring complexity and improve signal routing efficiency.

The left switch module (VCLEFT) represents the actual LIN slave device that communicates scroll wheel and button input data to the VCLEFT BCM master. This module reads the raw analog or digital signals from the scroll wheel encoder and the left steering wheel stalks, converts this information into standardized LIN frame format, and responds when polled by the master during its scheduled communication slots. Research from the Tesla community indicates that the left-side steering wheel controls communicate via LIN using a specific frame identifier of 0x4C, though this identification comes primarily from Model S reverse engineering efforts[9][9] and may require verification for Model 3 and Model Y variants.

The scroll wheel itself likely uses an incremental encoder that generates pulse signals representing rotation in either direction. The LIN frame carrying this data must encode the scroll direction (up or down), the magnitude of the scroll input (potentially in steps or raw encoder counts), button press information for direct scroll wheel clicks, and temporal information allowing the receiving system to interpret the velocity of scrolling input. This encoding scheme must also incorporate error detection mechanisms to ensure that scroll wheel inputs, particularly those intended to control critical functions like autopilot engagement, are not corrupted by electromagnetic interference or signal degradation.

## LIN Protocol Implementation and Frame Structure in Tesla Applications

The Local Interconnect Network protocol implements a master-slave communication architecture fundamentally different from the multi-master CAN bus model[15][15][15]. In LIN systems, a single master node—in this case the VCLEFT body control module—maintains complete authority over the communication schedule and initiates all message exchanges. Slave nodes, such as the steering wheel switch module, remain in low-power listen mode until explicitly polled by the master. Each LIN message begins with a synchronization break field and sync byte that allow all nodes to establish clock synchronization, followed by a protected identifier field containing the actual frame ID combined with parity bits[15][15][15].

The LIN specification defines frame identifiers using six bits plus two parity bits, allowing for 64 unique identifiers (0x00 through 0x3F in hexadecimal). Tesla's implementation appears to use identifiers predominantly in the lower range, with the left steering wheel controls identified as 0x4C in available documentation[9][9]. The parity bits in the identifier field follow a specific algorithm defined in the LIN specification, which means that valid LIN identifiers in the 0x00-0x3F range will have parity bits calculated according to this standard. This parity protects against single-bit errors that could cause the wrong node to respond or cause data to be misrouted.

Following the protected identifier field, the LIN protocol specifies a response field where the designated slave transmits data bytes in response to the master's header. For frame identifiers in the 0x00-0x3F range, different data lengths apply based on the ID value: identifiers 0x00-0x1F typically carry 2 data bytes, 0x20-0x2F carry 4 data bytes, and 0x30-0x3F carry 8 data bytes[15][15][15]. The 0x4C identifier referenced for the left steering wheel controls falls outside this standard mapping, suggesting either a non-standard implementation or that the identifier reference requires clarification. Alternatively, the identifier might be encoded with parity bits included, and 0x4C might represent the full PID field rather than just the underlying frame ID.

Each LIN frame concludes with a checksum field that ensures data integrity[15][15][15]. Tesla likely implements the enhanced checksum variant defined in LIN 2.x specifications, which includes both the identifier and data bytes in the checksum calculation, providing stronger error detection than the classic checksum used in LIN 1.x. The complete frame transmission occurs within a scheduled time slot determined by the LIN schedule table maintained by the VCLEFT master. This schedule explicitly defines which frames should be transmitted during which time intervals, creating a deterministic pattern that all nodes on the network can predict and rely upon.

## Scroll Wheel Signal Mapping Between LIN and CAN Buses

One of the most important aspects of understanding Tesla's steering wheel control architecture is recognizing that scroll wheel data exists on both the LIN bus (between the steering wheel switch module and the VCLEFT body control module) and the CAN bus (between the VCLEFT and other vehicle control systems such as the autopilot computer and instrument cluster). The user research indicates that scroll wheel input on CAN bus appears in the signal designated swcLeftScrollTicks on CAN message 0x3C2. This CAN message likely contains not only the scroll wheel tick count but also related signals such as scroll wheel button state, left stalk position, turn signal information, and other steering column inputs.

The transition from LIN to CAN occurs at the VCLEFT body control module, which serves as a gateway or bridge between the low-speed LIN steering wheel subsystem and the primary CAN network. When the VCLEFT master polls the left steering wheel switch module via LIN, it receives data indicating scroll wheel position, direction, and velocity information. The VCLEFT then converts this information into the appropriate CAN message format, bundles it with other steering wheel signals (such as turn signal stalk position and wiper control inputs), and transmits this consolidated message onto the primary CAN bus at regular intervals. This architecture provides several advantages including reduced wiring complexity, improved electromagnetic immunity, and the ability to standardize interfaces between the steering wheel subsystem and the rest of the vehicle's electrical architecture.

The data encoding scheme for scroll wheel signals on the LIN bus must be sufficiently sophisticated to capture the nuanced input that modern vehicles require. Simple on-off button inputs can be represented with single bits, but scroll wheel data requires representation of both direction and magnitude. Incremental encoders used in scroll wheels typically generate pulses that can be counted to determine the number of scroll "ticks" in a given direction. Each time the VCLEFT polls the steering wheel switch module, it may receive a delta value representing how many ticks have occurred since the last poll, or it may receive an absolute position that can be compared to the previous reading to calculate the delta. The LIN frame data bytes must also include information about button press state, allowing the system to distinguish between a simple scroll action and a click on the scroll wheel itself.

## Known LIN Frame Identifiers and Data Encoding Analysis

Research conducted by the Tesla enthusiast and reverse engineering community has provided limited but valuable information regarding LIN frame identifiers used in Tesla steering wheel control systems. The most concrete evidence comes from Tesla Motors Club forum discussions where community members working on steering wheel modifications documented that Model S steering wheel left-side controls communicate via LIN using frame identifier 0x4C[9][9]. These discussions included references to "querying the left side over LIN (ID: 0x4C)" during steering wheel bench testing, indicating that this frame ID is well-known among individuals performing aftermarket steering wheel work and custom control module development.

The frame ID 0x4C warrants careful analysis in the context of LIN's frame identifier scheme. In LIN's six-bit identifier space with two parity bits, valid frame IDs range from 0x00 to 0x3F. However, 0x4C extends beyond this range, suggesting it represents the complete PID (Protected ID) field including parity bits. The protected ID field structure reserves specific identifiers for diagnostic communication: ID 0x3C (frame identifier 60 in decimal) for master diagnostic requests and 0x3D (frame identifier 61 in decimal) for slave diagnostic responses[15][15][15]. Given this structure, 0x4C might represent a different encoding or could indicate that the community reference uses a different notation system than official LIN specifications.

Alternatively, 0x4C could indicate that Tesla uses an extended or non-standard LIN identifier scheme specific to their implementation. Some automotive manufacturers implement proprietary extensions to standard bus protocols to meet specific engineering requirements. If 0x4C represents a raw hexadecimal byte read from the LIN bus (including parity bits), the underlying frame ID would be the lower six bits, which would be 0x0C (12 in decimal), with parity bits in bits 6-7 evaluating to 01 in binary. This interpretation would place the left steering wheel controls in the 0x00-0x1F range expected for 2-byte data fields in standard LIN.

The data encoding within the LIN frame for scroll wheel information remains largely undocumented in public sources, though inference from the system's functional requirements provides useful guidance. The first data byte in a LIN frame carrying steering wheel input likely contains bit fields for various steering column signals including scroll direction, scroll magnitude, scroll wheel button state, turn signal stalk position, and wiper stalk position. The second data byte, if present, might carry additional information such as steering angle sensor data, high-beam indicator position, or error flags indicating that the steering wheel switch module has detected a fault condition.

Scroll wheel direction would likely be represented by a single bit indicating whether the scroll input represents upward or downward motion. Scroll magnitude could be encoded as a multi-bit field (perhaps 4 to 6 bits) representing either absolute position (allowing the receiving system to calculate delta) or relative change since the last poll. For functions like autopilot speed adjustment, the autopilot control system must interpret this scroll data with sufficient resolution to support both coarse adjustments (holding the scroll wheel for rapid increment changes) and fine adjustments (single scroll ticks for precise speed control). The velocity of scrolling could be inferred from the rate at which successive LIN frames indicate scroll position change, allowing the autopilot system to distinguish between intentional rapid adjustments and accidental brush contacts with the scroll wheel.

## Anti-Nag Module Architecture and LIN Bus Injection Methodology

Aftermarket anti-nag modules represent the practical application domain where understanding of Tesla's steering wheel LIN bus becomes critically relevant. These devices, including the TSL5 and newer TSL6 generations mentioned in the user research context, function by artificially generating scroll wheel input signals on the LIN bus to satisfy Tesla's driver engagement monitoring systems. The original implementation of these modules, which Tesla later addressed through firmware updates, involved intercepting CAN bus signals related to hands-on-wheel detection and spoofing autopilot disable events. However, as Tesla's anti-nag detection systems became more sophisticated, manufacturers of these aftermarket modules adapted their approach to work directly with LIN bus steering wheel signals.

The TSL6 generation anti-nag module, according to available documentation[20], installs at the OBD (On-Board Diagnostics) connector located under the rear exhaust vent of Tesla Model 3 and Model Y vehicles. This installation location provides access to the vehicle's power supply, ground, and potentially the serial data lines that carry both CAN and LIN communications. The module uses a CH571F Bluetooth Low Energy microcontroller[19], which provides both processing capability and wireless connectivity. The choice of a BLE-equipped microcontroller suggests that modern anti-nag modules may incorporate over-the-air update capability and remote monitoring features, distinguishing them from purely passive signal spoofing devices.

To function effectively, the TSL6 module must successfully inject scroll wheel data onto the LIN bus in a manner that appears legitimate to the VCLEFT body control module and other vehicle systems. This requires the module to transmit data frames with correct frame identifiers (likely including the proper parity bits), appropriate data payloads indicating scroll wheel activity, and correct checksums. The timing of these injected frames must align with the LIN bus schedule to avoid collisions with legitimate steering wheel input data. Most critically, the module must generate scroll wheel signals that correspond to actual vehicle operation patterns—continuous random scrolling would immediately trigger driver engagement warnings, but periodic scroll wheel taps timed to coincide with other vehicle control events (such as lane changes, speed adjustments made through other controls, or turning events) would appear much more legitimate to Tesla's monitoring algorithms.

The implementation challenge for these anti-nag modules involves accessing and understanding the LIN bus physical layer while the vehicle is in operation. The LIN bus uses a single-wire serial protocol with specific voltage levels and timing characteristics. A properly designed interface circuit must buffer this signal without disrupting normal communication while simultaneously allowing the module's microcontroller to both listen and transmit on the same line. The TSL6's installation at the OBD connector provides access to vehicle power but not direct LIN bus connections. Therefore, the module likely includes wireless capability to receive commands from an external device (via Bluetooth), or it may incorporate pattern recognition to detect specific vehicle operation scenarios where it should inject scroll wheel signals.

## LIN Bus Schedule Tables and Communication Periodicity

The LIN schedule table maintained by the VCLEFT master determines the precise timing and sequencing of steering wheel signal polling. While Tesla's exact schedule tables remain proprietary, standard LIN implementations typically poll steering wheel switches at intervals between 10 and 50 milliseconds, ensuring that user input events like scroll wheel manipulation are captured within human perceptual latency limits. If scroll wheel input is detected, the polling rate might temporarily increase or the response delay might decrease slightly to ensure that rapid scrolling inputs (such as a user quickly scrolling through autopilot speed adjustment) are captured with high fidelity.

The schedule table would specify not only the frequency of polling but also potentially conditional logic that modifies polling rates based on vehicle state. For example, if the vehicle is in a parking mode or parked with the engine off, the LIN bus might enter a low-power mode where steering wheel inputs are polled less frequently or the bus enters a sleep state entirely. Conversely, when the vehicle transitions to active driving or when autopilot is engaged, polling frequency might increase to ensure that steering wheel inputs (including anti-nag scroll wheel activity or emergency steering wheel override detection) are detected with minimal latency.

The relationship between the LIN bus schedule and the CAN message transmission schedule creates a complex timing architecture that anti-nag modules must carefully navigate. If the VCLEFT polls the steering wheel switch module every 20 milliseconds via LIN, but only transmits the consolidated steering wheel signal on CAN every 100 milliseconds, there is an inherent latency in the system that sophisticated monitoring could detect. Tesla's driver monitoring algorithms likely analyze not only the presence of scroll wheel input but also its temporal distribution—whether it appears to correlate with actual driving events or shows patterns inconsistent with natural driver behavior. An anti-nag module injecting artificial scroll wheel signals would ideally trigger these signals at times that correspond to natural driving events: accelerations that would naturally prompt speed adjustments, approach to other vehicles that would warrant follow-distance changes, or turning maneuvers that could plausibly involve steering wheel adjustment.

## Methods for Discovering Unknown LIN Frame IDs and Data Encoding

Researchers and enthusiasts attempting to reverse engineer Tesla's LIN protocol face several methodological challenges but also have access to multiple viable approaches for discovering frame identifiers and data structures. The most direct method involves obtaining a Tesla vehicle, accessing the LIN bus physical layer through dedicated diagnostic connectors or by carefully tapping into the steering column wiring, and capturing raw LIN traffic using specialized bus analysis equipment. A LIN bus analyzer, which can be constructed from readily available components including microcontroller development boards and LIN transceiver chips, captures all messages on the bus and displays them in human-readable format with timing information. By performing known operations—such as rolling the scroll wheel up or down, pressing steering wheel buttons, or moving steering stalks—the researcher can correlate observed LIN traffic changes with specific input events.

This approach, often called "black box" capture and analysis, allows researchers to identify which frame identifiers change in response to specific inputs and to infer data encoding by observing how byte values change with input magnitude or direction. For example, by scrolling the left wheel slowly in one direction while monitoring LIN frames, the researcher can observe whether and how numeric values change incrementally, revealing whether the data represents absolute position or relative change. By scrolling quickly in one direction followed by quick scrolling in the opposite direction, the researcher can determine whether different bits or bytes encode direction versus magnitude.

A more sophisticated analytical approach involves reverse engineering the steering wheel switch module itself. These modules are typically based on standard microcontroller architectures with published instruction sets and development tools. If a researcher can obtain a used steering wheel switch module or gain access to disassemble one from a salvaged Tesla vehicle, they can extract and analyze the firmware code. Modern embedded systems often include firmware recovery protections, but these can sometimes be bypassed through various techniques. Analyzing the firmware reveals not only the LIN frame format used but also the polling behavior expected from the master, the error handling procedures, and potentially even diagnostic modes that provide direct access to system state.

Community knowledge consolidation represents another powerful approach for discovering protocol information. The Tesla enthusiast community is remarkably active in reverse engineering vehicle systems, and numerous online forums, GitHub repositories, and documentation wikis now contain compiled information about CAN bus signals, LIN frame structures, and electrical interfaces. While information on LIN steering wheel controls is less complete than CAN bus documentation (due to the lower visibility and more specialized use cases of LIN), actively engaging with these communities and contributing findings helps build collective knowledge. Many researchers conducting work on custom steering wheel modifications or integrating aftermarket controls have already solved the problem of understanding LIN frame identification and are willing to share findings with other enthusiasts.

Simulation and hardware-in-the-loop testing provide another avenue for discovery. Researchers can obtain used Tesla steering wheel switch modules and bench test them outside of the vehicle by providing proper power and LIN bus connections. By stimulating the physical inputs (manually moving the scroll wheels, pressing buttons) and monitoring the LIN bus signals with an analyzer, the behavior of the module can be studied in isolation from the complex vehicle network. This approach allows controlled experiments where variables can be precisely controlled, and where measurements can be repeated multiple times without the variability introduced by real-world driving conditions.

Documentation from Tesla's internal service network, while officially proprietary, has occasionally appeared in public forums due to employees sharing information or security breaches exposing internal documents. Tesla service manuals, particularly the detailed electrical schematics and connector pinout diagrams, sometimes include bus topology information that reveals which modules connect to which buses and how signals are routed. While complete LIN protocol specifications remain closely guarded, partial information from service documents can provide valuable constraints that narrow down the possibilities for frame identifiers and data encoding.

## Physical Layer Considerations and Signal Integrity in LIN Bus Implementation

The physical layer of the LIN bus—the electrical characteristics of the signal and how data is transmitted—presents both opportunities and challenges for researchers attempting to understand and interface with Tesla's steering wheel control systems. LIN operates as a single-wire protocol where both the master and slaves share a common communication line. The idle state of a LIN bus is typically high (pulled high through a resistor to the positive supply voltage), and communication is initiated by pulling the bus to ground. The protocol defines specific signal timing requirements including bit times, frame formats, and response spaces that all nodes must respect.

This single-wire shared medium nature of LIN means that a properly designed interface can both listen to LIN traffic passively and inject signals onto the bus. However, the timing and electrical characteristics must be precisely managed to avoid disrupting ongoing communication. The LIN bus transceiver, which converts between the microcontroller's logic-level signals and the vehicle's 12-volt LIN bus, must have appropriate rise and fall times to maintain signal integrity. Tesla's implementation likely uses automotive-grade LIN transceivers specified for the automotive temperature ranges and electrical noise environment. These transceivers often include built-in protection against short circuits, reverse polarity, and transient voltage spikes that could damage the device.

The data rate of 19,200 bits per second, as confirmed for Tesla steering wheel LIN buses[7], represents a relatively slow speed that dates back to earlier automotive LIN implementations. This low speed was partly driven by the computational limitations of early automotive microcontrollers but also provides inherent robustness against electromagnetic interference and signal degradation. At 19,200 baud, each bit occupies approximately 52 microseconds, providing substantial timing margin for signal propagation delays, receiver sampling, and transmitter switching. The frame structure with its synchronization bytes and parity bits further enhances error detection capability, ensuring that corrupted frames are likely to be rejected rather than misinterpreted.

When anti-nag modules or other aftermarket devices inject data onto the LIN bus, they must respect these physical layer characteristics. Simply driving the bus with inadequate rise times or without proper transceiver selection could distort signals, increase electromagnetic emissions, or even damage the vehicle's electrical system. The fact that aftermarket modules like the TSL6 continue to function suggests they employ competent electrical design incorporating appropriate impedance matching, filtering, and transceiver selection. However, poorly designed implementations could accumulate electrical stress on the LIN bus over time, potentially causing premature failures of other connected modules or inducing electromagnetic emissions that affect other vehicle systems.

## Integration with Autopilot and Full Self-Driving Systems

The significance of understanding Tesla steering wheel LIN bus architecture extends beyond simple functionality into the critical domain of safety-critical autopilot systems. The scroll wheel functionality, particularly the right scroll wheel which controls autopilot speed and follow distance adjustment[14][6], represents the primary tactile interface through which drivers can modulate autonomous driving behavior. Tesla's Full Self-Driving system depends on responsive, low-latency steering wheel input for emergency disengagement and for user-initiated behavior modifications while in autonomous mode.

The integration of LIN bus steering wheel signals into autopilot control algorithms means that any corruption or spoofing of these signals could potentially affect autonomous driving behavior. Tesla's safety architecture includes redundancy and consistency checks designed to detect situations where steering wheel inputs appear inconsistent with normal driver behavior, which is precisely where anti-nag modules attempt to operate. By injecting scroll wheel signals that appear sporadic or inconsistent with actual driving needs, these modules can potentially trigger false safety alarms or cause subtle changes in autopilot behavior.

From a security perspective, the LIN bus represents a potential attack surface for malicious actors attempting to influence vehicle behavior. However, the security mechanisms built into the LIN protocol itself are minimal compared to the security architecture that would be necessary for a safety-critical system. Tesla engineers have likely implemented higher-level validation in the VCLEFT body control module and in the autopilot computers themselves to detect anomalous steering wheel input patterns. For example, rapid oscillation between maximum and minimum scroll wheel position would immediately be flagged as inconsistent with normal driver behavior, even if the electrical LIN signals themselves are properly formatted and error-checked.

## Data Byte Structure and Signal Encoding for Steering Wheel Inputs

Based on the functional requirements and typical automotive LIN implementation patterns, the data structure of the steering wheel LIN frame likely follows a logical organization where different bit fields encode specific input sources. A two-byte LIN frame, if that is what the left steering wheel control module uses, would provide 16 bits for signal encoding, which is sufficient for the variety of steering wheel inputs. The first byte would likely contain the scroll wheel tick count or position delta, potentially with the most significant bit reserved for direction (0 for down/decrease, 1 for up/increase). Bits 4-6 might encode the scroll wheel button press state and potentially a secondary button or reserved bits for future expansion.

The second byte might contain encoding for additional left-side steering wheel inputs including the turn signal stalk position, wiper control stalk position, and high-beam indicator. Each of these stalks would require at least two bits to encode the three or four positions they can assume (off, position one, position two, and potentially a reserved state). A multi-bit field might represent the analog or quasi-analog voltage from a stalk sensor, allowing the vehicle system to precisely detect partial stalk deflection. The remaining bits would be reserved for error flags, allowing the steering wheel switch module to signal that it has detected a fault condition or that sensor data may be unreliable.

Error handling and fault detection mechanisms are essential to automotive electrical system design, and the steering wheel LIN frame would almost certainly include provisions for detecting and signaling faults. The checksum field provides protection against transmission errors, but the module itself could detect failures such as open-circuit conditions in sensor wiring, shorts, or microcontroller errors. A dedicated error bit or error code field in the data bytes allows the steering wheel switch module to communicate these conditions to the VCLEFT master, which can then take appropriate action such as illuminating instrument cluster warning indicators or limiting the functionality of autopilot systems that depend on steering wheel input.

## Alternative Frame ID Hypotheses and Technical Uncertainty

While 0x4C represents the best-documented candidate for the left steering wheel control LIN frame identifier, acknowledging the limitations of available information is important for establishing credibility and appropriate confidence levels in these findings. The reference to 0x4C comes from Tesla Motors Club forum discussions focused on Model S steering wheel modifications, and direct confirmation for Model 3 and Model Y vehicles remains absent from the publicly available technical documentation. Different Tesla model generations or production revision batches could potentially use different frame identifiers as the company iterates on their electrical architecture.

The possibility exists that different frame identifiers are used for different functionalities within the left steering wheel control system. Rather than a single 0x4C frame carrying all left-side steering wheel inputs, the system might employ separate frames for the scroll wheel, stalks, and buttons. Alternatively, the implementation might use multiple frames with different identifiers that are all polled as part of the steering wheel control master's schedule. This would provide better separation of concerns from a software architecture perspective and could allow independent update or modification of different input handling subsystems.

Some uncertainty also remains regarding whether 0x4C represents the complete PID (Protected ID) field including parity bits or whether it represents just the frame ID with parity bits stripped. The LIN specification defines parity computation based on the frame ID bits, and the parity bits occupy bits 6 and 7 of the PID byte. If community documentation uses 0x4C to represent the observed byte value directly from the LIN bus including parity, then the underlying frame ID would need to be extracted by masking off the parity bits and performing parity verification according to the LIN specification. This distinction could lead to confusion when attempting to implement custom LIN interface code, as the frame ID value used in the schedule table might differ from the PID value observed on the physical bus.

The existence of proprietary Tesla modifications to the standard LIN protocol represents another source of potential complexity and uncertainty. While Tesla generally adheres to industry-standard bus protocols to enable use of standard microcontroller and transceiver components, the company is not constrained by standardization efforts and has implemented proprietary extensions or modifications to standard protocols before. The LIN diagnostic frames (frame IDs 60-61) are typically reserved for specific diagnostic functions in standard LIN implementations[15][15][15], but Tesla might use these or other reserved identifiers for undocumented purposes. Similarly, Tesla might implement non-standard data lengths for particular frame identifiers or use frame identifiers in ways that deviate from the standard mapping of identifier ranges to data lengths.

## Challenges in Community-Based Reverse Engineering of Proprietary Systems

The reverse engineering of Tesla's steering wheel LIN protocol illustrates broader challenges that emerge when attempting to understand proprietary automotive systems through community effort and public information synthesis. Unlike open-source automotive projects or systems designed for modification and customization, Tesla's electrical architecture is explicitly not designed to be modified or accessed by third parties. The company uses security measures including firmware encryption, secure boot mechanisms, and electrical isolation to prevent unauthorized access to vehicle systems. While these protections are generally effective at preventing malicious modifications, they also hinder legitimate research and repair activities.

The legal and ethical dimensions of reverse engineering for research purposes remain complex in many jurisdictions. While fair use provisions in copyright law and research exemptions in some automotive diagnostic regulations technically permit reverse engineering for interoperability and security research, the practical reality is that manufacturers including Tesla assert broad claims over their systems and may take legal action against individuals or organizations publicly documenting their findings. This creates a chilling effect where researchers who discover important information about vehicle systems face uncertainty about whether sharing their findings could expose them to legal liability.

This legal uncertainty, combined with the technical barriers and the time investment required for rigorous reverse engineering, means that much of the community knowledge about Tesla systems remains fragmented across private communications, deleted forum posts, and informal networks rather than being consolidated into complete technical documentation. The information that does appear in public often lacks the rigor of formal documentation, including incomplete details, unverified claims, and occasional errors that propagate through repeated citation. This report therefore must acknowledge significant uncertainty about specific details while simultaneously synthesizing the best available evidence into useful conclusions.

## Current State of LIN Frame ID Knowledge and Practical Implementation Implications

As of May 2026, the most concretely documented identification for Tesla steering wheel LIN bus frames is the 0x4C identifier associated with left-side steering wheel controls in Model S vehicles[9][9]. This identification appears in community forum discussions focused on aftermarket steering wheel integration projects, where individuals explicitly state that they have successfully communicated with steering wheel modules using this frame identifier. The fact that multiple independent aftermarket anti-nag module implementations appear to function in Model 3 and Model Y vehicles suggests that their developers have successfully reverse engineered and implemented the necessary LIN frame identification and data encoding, even if this information has not been widely published in formal technical documentation.

For practitioners attempting to implement custom steering wheel interfaces or understand anti-nag module functionality, the 0x4C identifier (or potentially 0x0C with parity bits, depending on notation conventions) represents the best available starting point. Verification of this identifier for specific Tesla models would require direct measurement using LIN bus analysis equipment, either through benchtop testing of used steering wheel modules or through careful measurement of actual vehicle LIN traffic. The data encoding for scroll wheel inputs, including the specific bit positions and value ranges representing scroll direction, magnitude, and button state, would likely need to be determined through similar empirical methods combined with analysis of how injected signals affect vehicle behavior and driver experience.

The availability and continued proliferation of anti-nag modules suggests that the technical implementation details of Tesla steering wheel LIN communication are sufficiently well-understood by the aftermarket module manufacturers that they can reliably produce functional devices. However, the technical documentation describing these implementations remains largely confined to private communications, closed source code, and possibly incomplete public documentation. This creates a situation where practical working knowledge exists in the community but is not consolidated into reliable reference materials that researchers, repair technicians, or security researchers can confidently rely upon.

## Emerging Challenges in Vehicle Security and the Role of Steering Wheel Interfaces

The evolution of anti-nag devices and the ongoing cat-and-mouse game between Tesla's driver engagement monitoring and aftermarket spoofing modules illuminate deeper security challenges in modern automotive systems. Tesla's decision to implement driver engagement verification systems reflects legitimate safety concerns about driver attention during autonomous driving. However, the cat-and-mouse dynamic of countermeasure development suggests that security through obscurity—relying on systems being difficult to understand as the primary security mechanism—proves insufficient in the long term.

From a cybersecurity perspective, reverse engineering efforts focused on steering wheel LIN protocols represent a relatively benign use case where the primary concern is circumventing driver engagement verification. However, the techniques and knowledge developed through these efforts could potentially be applied to more malicious purposes such as undetected steering wheel manipulation during critical driving moments. A sophisticated attack could involve injecting coordinated steering wheel button inputs and scroll wheel signals that interfere with driver override attempts while simultaneously appearing to the vehicle's logging systems as legitimate driver input.

Tesla and other automotive manufacturers would ideally implement cryptographic authentication and integrity checking for safety-critical signals such as those originating from steering wheels. However, the computational constraints of embedded systems in vehicles, the need for deterministic real-time behavior, and the cost considerations of automotive development create practical barriers to implementing strong security measures on all vehicle buses. The LIN bus, in particular, with its low bandwidth and 19,200 baud rate, was designed for simplicity and reliability rather than security, and retrofitting security onto LIN would require substantial architectural changes.

## Synthesis: Toward Practical Understanding of Tesla Steering Wheel Architecture

The convergence of evidence from multiple sources—community reverse engineering efforts, aftermarket product documentation, Tesla service procedures, and general automotive communication protocol knowledge—suggests a coherent picture of Tesla steering wheel LIN bus architecture, despite the incompleteness of available information. The left scroll wheel and related steering wheel inputs appear to use a LIN frame identifier of 0x4C or a related identifier in the low range of the LIN ID space (0x00-0x3F). This frame is polled by the VCLEFT body control module master at regular intervals, likely in the range of 10-50 milliseconds, following a predetermined schedule table that the master maintains.

Data encoding within this frame employs standard LIN conventions with multiple bit fields representing different steering wheel input sources including scroll wheel position change, scroll direction, scroll wheel button state, stalk positions, and error flags. The VCLEFT gateway module collects this LIN data and translates it into appropriate CAN bus message formats for distribution to vehicle systems including autopilot computers, instrument cluster modules, and potentially the main vehicle computer. This architecture provides the benefits of simplified steering column wiring, deterministic communication for safety-critical functions, and the ability to evolve steering wheel input handling without major changes to the vehicle's primary CAN network.

Aftermarket anti-nag modules have apparently successfully reverse engineered these implementation details well enough to inject artificial scroll wheel signals that satisfy Tesla's driver engagement monitoring systems, at least temporarily and at least according to user reports of ongoing functionality as of April 2026. The continued development and evolution of these modules, including migration from invasive wiring approaches to relatively simple OBD connector installations as in the TSL6 generation, suggests that the technical barriers to understanding the LIN protocol have become sufficiently low that multiple independent developers can solve the problem.

## Conclusion: Synthesis and Remaining Uncertainties

The LIN bus frame identification for Tesla Model 3 and Model Y left scroll wheel and steering wheel controls represents a moderately well-understood but still partially opaque technical detail. The best-available evidence, synthesized from community reverse engineering efforts and inferences from related technical documentation, points to LIN frame identifier 0x4C or related identifier encoding as the location of left steering wheel control data. However, confirmation of this identifier specific to Model 3 and Model Y vehicles, complete documentation of data byte structures and signal encoding, and detailed understanding of the LIN schedule table and polling rates remain subjects where uncertainties persist.

Practical implementation of custom steering wheel interfaces or comprehensive understanding of aftermarket anti-nag module functionality would benefit enormously from consolidated technical documentation that reflects the collective knowledge of the reverse engineering community. However, the fragmentation of this knowledge across private communications, proprietary aftermarket code, and incomplete public discussions means that no single authoritative reference exists. Researchers and technicians attempting to work in this domain must necessarily synthesize multiple partial sources and be prepared to undertake empirical verification of conclusions.

The Tesla steering wheel LIN bus architecture exemplifies the broader trend in automotive systems toward increased complexity, distributed control, and proprietary implementation details that move beyond standardized interfaces. While this architecture provides benefits including improved functionality, simplified electrical harnesses, and opportunities for software-based feature evolution, it simultaneously creates barriers to independent repair, maintenance, and security research. The engineering tradeoff between accessibility and security, between openness and proprietary protection, remains contested ground in automotive regulation and industry practice, with the steering wheel LIN bus representing one small but significant example of this broader tension.

For practitioners pursuing this research further, direct empirical measurement using LIN bus analysis equipment remains the most reliable approach to verification and extension of community knowledge. Careful documentation of findings, combined with willingness to engage with the research community while respecting legitimate intellectual property and legal boundaries, offers the best path toward more complete understanding of these systems. The knowledge generated through such efforts has genuine practical value not only for aftermarket module developers but also for repair technicians, security researchers, and vehicle owners seeking to understand and maintain their own vehicles in an increasingly complex automotive electrical environment.

## Citations

1. https://www.youtube.com/watch?v=62txKc7EtCA - https://www.youtube.com/watch?v=62txKc7EtCA
2. https://www.youtube.com/watch?v=sPVdU_sEPZQ - https://www.youtube.com/watch?v=sPVdU_sEPZQ
3. https://forum.beagleboard.org/t/bbb-can-tx-only-works-at-loop-situation/31006 - https://forum.beagleboard.org/t/bbb-can-tx-only-works-at-loop-situation/31006
4. https://service.tesla.com/docs/ModelS/ServiceManual/en-us/GUID-C25DAA68-1695-492C-A60E-91C47DE7ECA9.html - https://service.tesla.com/docs/ModelS/ServiceManual/en-us/GUID-C25DAA68-1695-492C-A60E-91C47DE7ECA9.html
5. https://www.youtube.com/watch?v=qF-5ptimPp4 - https://www.youtube.com/watch?v=qF-5ptimPp4
6. https://www.tesla.com/ownersmanual/model3/en_th/GUID-DEB259CC-ABAC-4BFC-8D10-B7B1BBCFCB1F.html - https://www.tesla.com/ownersmanual/model3/en_th/GUID-DEB259CC-ABAC-4BFC-8D10-B7B1BBCFCB1F.html
7. https://github.com/nunojpg/homelink-explorer - https://github.com/nunojpg/homelink-explorer
8. https://service.tesla.com/docs/ModelS/ServiceManual/en-us/GUID-1B5B5170-5ADC-422A-BACE-8741C4847BFD.html - https://service.tesla.com/docs/ModelS/ServiceManual/en-us/GUID-1B5B5170-5ADC-422A-BACE-8741C4847BFD.html
9. https://teslamotorsclub.com/tmc/threads/work-in-progress-stalks-on-2021-model-s-and-optional-round-y-wheel.242853/page-23 - https://teslamotorsclub.com/tmc/threads/work-in-progress-stalks-on-2021-model-s-and-optional-round-y-wheel.242853/page-23
10. https://www.tesla.com/ownersmanual/models/en_us/GUID-29A7E205-A689-41D1-B69C-3AE821CB70E7.html - https://www.tesla.com/ownersmanual/models/en_us/GUID-29A7E205-A689-41D1-B69C-3AE821CB70E7.html
11. https://www.lin-cia.org/fileadmin/microsites/lin-cia.org/resources/documents/LIN-Spec_Pac2_1.pdf - https://www.lin-cia.org/fileadmin/microsites/lin-cia.org/resources/documents/LIN-Spec_Pac2_1.pdf
12. https://service.tesla.com/docs/Model3/ServiceManual/2024/en-us/GUID-117FB402-646E-4035-991D-768A9A437E55.html - https://service.tesla.com/docs/Model3/ServiceManual/2024/en-us/GUID-117FB402-646E-4035-991D-768A9A437E55.html
13. https://www.youtube.com/shorts/GBbdOfg7u2U - https://www.youtube.com/shorts/GBbdOfg7u2U
14. https://www.tesla.com/ownersmanual/model3/en_us/GUID-DEB259CC-ABAC-4BFC-8D10-B7B1BBCFCB1F.html - https://www.tesla.com/ownersmanual/model3/en_us/GUID-DEB259CC-ABAC-4BFC-8D10-B7B1BBCFCB1F.html
15. https://www.csselectronics.com/pages/lin-bus-protocol-intro-basics - https://www.csselectronics.com/pages/lin-bus-protocol-intro-basics
16. https://teslamotorsclub.com/tmc/threads/scrolling-wheel-on-steering-wheel-easily-breaks-is-the-part-available-separately.183988/ - https://teslamotorsclub.com/tmc/threads/scrolling-wheel-on-steering-wheel-easily-breaks-is-the-part-available-separately.183988/
17. https://service.tesla.com/docs/Model3/ServiceManual/2024/en-us/GUID-EA9255E2-6987-40DD-B5F3-BADA25862BA0.html - https://service.tesla.com/docs/Model3/ServiceManual/2024/en-us/GUID-EA9255E2-6987-40DD-B5F3-BADA25862BA0.html
18. https://github.com/iDoka/awesome-automotive-can-id - https://github.com/iDoka/awesome-automotive-can-id
19. https://www.aliexpress.com/item/1005006064368833.html - https://www.aliexpress.com/item/1005006064368833.html
20. https://www.youtube.com/watch?v=2Fux6pPVqKY - https://www.youtube.com/watch?v=2Fux6pPVqKY
21. https://service.tesla.com/docs/Model3/ServiceManual/en-us/GUID-CAFAF9F7-6FDE-4CB2-9AF0-F852A45F5AC4.html - https://service.tesla.com/docs/Model3/ServiceManual/en-us/GUID-CAFAF9F7-6FDE-4CB2-9AF0-F852A45F5AC4.html
22. https://service.tesla.com/docs/Model3/ServiceManual/2024/en-us/index.html - https://service.tesla.com/docs/Model3/ServiceManual/2024/en-us/index.html
23. https://github.com/Dewalt-arch/pimpmykali/blob/master/pimpmykali.sh - https://github.com/Dewalt-arch/pimpmykali/blob/master/pimpmykali.sh
24. https://teslamotorsclub.com/tmc/threads/drive-stalk-can-bus-id-on-a-model-3.318006/ - https://teslamotorsclub.com/tmc/threads/drive-stalk-can-bus-id-on-a-model-3.318006/
25. https://www.enhauto.com/blogs/all/change-tesla-drive-states-with-the-right-scroll - https://www.enhauto.com/blogs/all/change-tesla-drive-states-with-the-right-scroll
26. https://teslamotorsclub.com/tmc/threads/yoke-anyone-know-what-left-right-clicking-on-the-right-scroll-wheel-does.245566/ - https://teslamotorsclub.com/tmc/threads/yoke-anyone-know-what-left-right-clicking-on-the-right-scroll-wheel-does.245566/
