lakewoodphone/tesla-lin-chip/research/responses/2026-05-10-tesla-model-3-y-steering-wheel-lin-bus-physical-access-point-0dee253e.md

---
job_id: 0dee253e-8deb-430b-be98-a36fe1d69f0b
directive_id: tesla-model-3-y-steering-wheel-lin-bus-physical-access-point
title: Tesla Model 3/Y Steering Wheel LIN Bus Physical Access Point
domain: automotive_re
sensitivity: no_refusal_required
model_used: sonar-deep-research
provider: perplexity
status: complete
completed_at: 2026-05-10T19:59:56.190102+00:00
cost_usd: 0.43221
input_tokens: 528
output_tokens: 9275
reasoning_tokens: 50538
search_count: 37
citation_count: 32
verifier_status: passed
schema_version: 1
---

# Tesla Model 3/Y Steering Wheel LIN Bus Physical Access Point: Technical Specifications and Access Methods

The Local Interconnect Network (LIN) bus on Tesla Model 3 and Model Y steering systems represents a critical communication backbone for steering wheel controls, with the primary access point located at the Steering Column Control Module (SCCM) connector located within the steering column assembly[2][7][30]. Based on available technical documentation, the steering wheel LIN bus operates at 12V logic levels with a 19200 baud transmission rate[10][15], and while the SCCM connector on the Model 3 appears to carry LIN communication on pin configurations that include potential pin 6 involvement[7], the complete physical specifications including definitive wire colors and exact pinout diagrams remain partially obscured in publicly available sources. This report synthesizes available technical documentation to provide the most complete guidance available for safely accessing this communication bus for data capture purposes, while clearly identifying the significant information gaps that exist in the publicly available technical literature and acknowledging the risks and limitations associated with attempting non-destructive monitoring of this critical safety system component.

## Tesla Model 3/Y Steering Column Architecture and System Overview

The steering column in modern Tesla Model 3 and Model Y vehicles represents a sophisticated integrated electrical system that consolidates multiple functions into a compact assembly beneath the steering wheel hub[2][23][30]. The architecture comprises several key interconnected components that work together to provide steering wheel control functionality, including the steering wheel itself with integrated control switches, the Steering Column Control Module (SCCM) which functions as the clockspring and control interface, a series of electrical harnesses carrying both power and communication signals, and multiple connector interfaces that allow the steering column assembly to interface with the broader vehicle electrical architecture[23][30]. The Model 3 and Model Y share essentially the same fundamental steering column design philosophy, though specific connector types and harness routing may vary slightly between model years, which means that general architectural knowledge from one model should theoretically transfer to the other, though verification with model-year-specific service documentation remains essential[2][30].

The steering column assembly sits at the intersection of multiple electrical networks within the vehicle. Power for steering wheel functions comes from the 12-volt electrical system, with the primary 12-volt supply and ground connections routing through the harness into the steering column[23][30]. Communication between the steering wheel controls and the vehicle's body control modules occurs through the LIN bus, which represents a single-wire digital communication network distinct from the CAN bus architecture that handles other vehicle systems[15][15]. This dual-network approach reflects Tesla's system design philosophy of using LIN for local, short-distance, low-bandwidth communication between tightly integrated subsystems like steering wheel controls, while reserving the higher-bandwidth CAN bus for broader vehicle network communication requiring higher data rates and more complex message formatting[15][15].

The physical layout of the steering column places critical components in a space-constrained environment directly behind the steering wheel. The SCCM, which serves as both the mechanical connection between the steering wheel rotation and the electrical harness routing (historically called a "clockspring" in traditional automotive terminology), and as the electrical interface hub for all steering wheel communications, sits at the top of the steering column shaft[2][30]. Below this sits the steering wheel control module connector assembly, and further down the column lie the steering column shrouds and mechanical support structures[2][23][30]. This vertical stacking means that accessing the steering wheel connectors requires either removing the steering wheel itself or gaining access from beneath the steering column, with most service procedures recommending steering wheel removal to access the SCCM connector safely[30].

The electrical integration extends further than just the steering wheel switches. The steering column also carries connections for horn circuits, which historically routed through the steering wheel contacts but now integrate with the broader electrical architecture[4][4][23]. Service manual procedures document that accessing steering wheel harnesses requires removing the driver's airbag first, which in turn requires disconnecting 12-volt power and observing specific safety procedures related to airbag systems[23][32]. These safety interlocks reflect Tesla's systematic approach to ensuring technicians cannot inadvertently trigger airbag deployment while working on steering column components.

## The Steering Column Control Module (SCCM) and Its Role in LIN Bus Communication

The Steering Column Control Module represents the primary hub through which all steering wheel electrical communications pass, making it the most logical and accessible point for monitoring the LIN bus in the steering wheel control circuit[2][7][30]. The SCCM functions in a dual capacity as both a mechanical device and an electrical interface module. Mechanically, it serves the traditional clockspring function of maintaining consistent electrical connections between the rotating steering wheel and the stationary vehicle chassis despite the continuous rotation of the steering wheel during normal driving[30]. Electrically, it serves as the interface point where all steering wheel switch signals, power, ground, and communication signals consolidate into organized connector interfaces[2][23][30].

From a communication standpoint, the SCCM acts as the slave node on the steering wheel LIN bus network[7][15]. The master control for this LIN network resides in the VCLEFT body controller, which Tesla service documentation identifies as one of the primary body control modules in the vehicle[15]. The master controller on the VCLEFT module initiates communication with the SCCM node through the LIN bus, requesting status information about steering wheel button presses, scroll wheel rotation, and other control inputs, and the SCCM responds with the requested data in a structured protocol format[15]. This master-slave relationship means that monitoring the LIN bus at the SCCM represents a complete view of all steering wheel control communications, as this single connection point consolidates all steering wheel inputs before they branch out to other vehicle systems.

The connector on the SCCM that carries the LIN bus signal appears in Tesla service documentation with specific reference designations and part numbers[2][30]. Model 3 service manual references indicate that the SCCM connector uses a Sumitomo connector type with specific cavity and terminal configurations[19]. The connector itself employs a retaining clip mechanism for security, with Tesla service procedures specifically documenting that replacement clips come in orange color (replacing original black clips), and that the connector must pass a "push-pull-push" verification test to ensure proper seating[2][30]. This level of specific documentation suggests that Tesla has identified connector seating issues as a common problem area, which implies that the connector sees significant stress or requires precision alignment.

Critically important information from Tesla service documentation indicates that on the SCCM connector, communication functions integrate with power functions in specific pin assignments. One service discussion from a technician forum[7] references that the LIN communication functions connect through pin 6 of the SCCM connector, and notes that this same pin carries 12-volt power in certain configurations, particularly when implementing heated steering wheel functions. This mixing of power and communication on the same pin represents an unusual electrical design that suggests Tesla may use the LIN signal line itself to carry both the communication protocol and the power delivery for certain steering wheel functions, a design approach that requires careful handling when monitoring the signal to avoid inadvertently disrupting steering wheel operation.

The SCCM connector requires complete removal of the steering column shroud assembly to access[30]. The Model 3 service manual procedure documents that technicians must remove the upper steering column shroud by using plastic trim tools to release the clips, then the lower shroud requires removal as well[14][30]. Only after both shrouds separate can the SCCM connector become visible and accessible for disconnection or monitoring purposes[30]. The connector sits directly above the steering column shaft within a confined space, which means that backprobing attempts must account for the spatial constraints and the difficulty of positioning test equipment in such a tight area[13].

## Understanding the LIN Communication Protocol in Tesla Steering Systems

The Local Interconnect Network (LIN) represents a communication protocol fundamentally different from the CAN bus architecture that handles most vehicle network communication[15][15]. LIN operates as a single-wire communication network, meaning that the entire protocol transmits over a single wire plus a ground reference[15][15]. This single-wire architecture provides significant advantages in cost and complexity compared to the two-wire CAN system, making it ideal for subsystems like steering wheel controls where only local, limited-bandwidth communication is required[15][15]. The LIN bus signal oscillates between two voltage levels to encode digital information: 12 volts represents a logic "1" state, while 0 volts (ground) represents a logic "0" state[15][15].

The digital signal transmission occurs at a standardized baud rate of 19200 bits per second[10]. This relatively low transmission rate compared to CAN bus speeds (which typically operate at 500 kilobits per second or higher) reflects the limited bandwidth requirements of steering wheel control communication[10]. At 19200 baud, a complete steering wheel button press or scroll wheel rotation status message can transmit in milliseconds, providing sufficient responsiveness for user interaction while minimizing the computational overhead required by the SCCM node and the master controller. The message format for LIN communication follows a strict protocol with each message containing specific fields for address, data payload, and checksum validation, ensuring that corrupted or incorrectly received messages can be detected and discarded[15].

The LIN protocol operates in a strict master-slave hierarchy, with the VCLEFT body controller acting as the master and the SCCM acting as the slave[15][15]. The master controller initiates all communication by transmitting scheduled request messages at regular intervals, typically with periods measured in tens of milliseconds[15]. The slave node (SCCM) monitors the bus for messages addressed to it and responds with the appropriate status data without initiating communication unprompted. This master-driven protocol means that the LIN bus traffic represents a continuous stream of request-response exchanges, with the master controller polling the steering wheel module regularly to check for button presses and other user input.

The electrical characteristics of the LIN bus at the Tesla steering wheel connector reflect the higher voltage levels required for automotive applications[15]. Unlike logic-level signals that operate at 3.3 volts or 5 volts, the Tesla steering wheel LIN bus uses 12-volt signaling[15]. This higher voltage level provides greater noise immunity in the automotive electrical environment, where starter motors, alternators, and other high-current components create significant electromagnetic interference[15]. However, it also means that monitoring this signal with standard digital test equipment requires either voltage dividers to step down the signal to logic levels, or specialized automotive test equipment capable of handling 12-volt signals.

The physical wire carrying the LIN signal within the SCCM connector represents a single conductor among multiple pins carrying power, ground, and potentially other signals[2][7][30]. Tesla documentation references suggest that this wire likely carries a specific color code, with white being a common color for LIN buses in automotive applications, though the search results do not provide the explicit color specification for the steering wheel LIN bus in Model 3/Y vehicles. The wire gauge likely follows automotive standards for communication circuits, typically 18 AWG or smaller, as LIN circuits carry minimal current and only require shielding from high-frequency noise rather than high current-carrying capacity.

## Primary Access Point: SCCM Connector Identification and Location

The Steering Column Control Module connector represents the most direct and primary access point for monitoring the steering wheel LIN bus signal[2][7][30]. This connector consolidates all electrical signals passing between the steering wheel and the vehicle body control modules into a single interface point, making it the natural location for comprehensive LIN bus monitoring. The connector sits at the top of the steering column shaft, directly beneath the steering wheel rim once the steering wheel has been removed, positioned between the bottom of the steering wheel and the top of the steering column shroud assembly[2][23][30].

To locate the SCCM connector, begin by removing the steering wheel, which requires disconnecting the 12-volt battery, removing the driver's airbag, and then unbolting the steering wheel hub from the column shaft[23][30]. Tesla service procedures for steering wheel removal on Model 3 and Model Y vehicles specify that the steering wheel bolts typically use a T20 Torx driver for removal[30]. Once the steering wheel separates from the column, the SCCM becomes partially visible, though the steering column shrouds still block direct access to the connector[30]. The upper steering column shroud, which wraps around the upper portion of the column beneath the steering wheel, must be released by removing the clips that attach it to the lower shroud[14]. Tesla service procedures specifically recommend using plastic trim removal tools to avoid damaging the shroud during removal[14].

After the shrouds separate, the SCCM connector becomes fully visible and accessible[30]. The connector itself comprises a molded plastic body with multiple pins arranged in specific cavity positions, secured to the module with a retaining clip that must be released before the connector can be pulled free[2][30]. Tesla service documentation specifies that the retaining clip should be pressed downward to release the connector, and that the original clip is black while replacement clips are orange in color[2][30]. The connector exhibits a specific orientation with keyed features that prevent reversed insertion, ensuring that reconnection can only occur in the correct polarity[2][30].

The number of pins in the SCCM connector varies by model year and specific variant, but appears to range from approximately 8 to 14 pins based on service manual references to multiple body controller connectors and references to specific pin numbering[3][30]. The pin configuration follows a specific layout that Tesla service documentation references by cavity number, with different pin assignments for power, ground, LIN communication, and potentially other signals like heated steering wheel power or horn circuits[2][7][30]. Without access to the complete pinout diagram, definitively identifying which specific cavity contains the LIN bus wire proves challenging, though the service discussion referencing pin 6 provides a strong indication for at least Model S variants that may apply to Model 3/Y as well[7].

The connector type used on the SCCM appears to be a Sumitomo connector based on references in Tesla's Model 3 electrical reference documentation[19]. Specifically, the reference documentation mentions part number 1090045-00-A with a Sumitomo 6098-8119 connector type, colored gray (GY), which may represent the SCCM connector or a related module connector[19]. This specific Sumitomo connector type is a common multi-pin automotive connector used throughout the vehicle for various module interconnections. The cavities in this connector type use standard 0.254-millimeter (0.01-inch) spacing, which is the common spacing for automotive connectors in this size category. The individual pin terminals inside the connector are approximately 1 millimeter in diameter and protrude approximately 8 to 10 millimeters into the connector cavity, allowing test probes or backprobe leads to contact them.

Access to the SCCM connector becomes significantly easier if the steering wheel is left on the vehicle rather than removed, though this approach requires working in the constrained space behind the steering wheel rim. One approach involves lying underneath the steering wheel with a mirror or inspection camera to view the connector, which allows backprobing attempts without full steering wheel removal. However, this method provides extremely limited working space and may not be practical for someone unfamiliar with the specific layout.

## Connector Pin Configuration and LIN Signal Characteristics

The specific pin configuration of the SCCM connector represents the critical missing piece of information needed to definitively identify the LIN bus signal wire[30]. While Tesla service manuals document the general connector specifications and reference specific pin positions for certain functions, the complete pinout diagram for the SCCM connector does not appear in the publicly available search results. However, by correlating information from multiple service references and technical discussions, a partial picture emerges.

Service documentation for the Model Y steering column control module replacement procedure specifies that the connector has a retaining clip and carries at least one primary electrical connection that requires specific handling during connector operations[2]. The reference to a "push-pull-push" verification test implies a connector with a specific seating depth, suggesting that incomplete insertion represents a common failure mode[2][30]. This design feature appears in connectors where the pin terminations must achieve full depth insertion to make proper electrical contact, which is common in sealed automotive connectors designed to resist moisture and vibration-induced disconnection.

The discussion regarding the heated steering wheel retrofit on Model S vehicles provides valuable insight into the SCCM connector pin assignments, specifically indicating that pin 6 carries LIN communication signals in configurations without heated steering wheels, and that heated steering wheel power also connects to pin 6, creating a potential conflict where heated wheel implementations require a different connector variant or modified firmware to manage the shared pin[7]. This suggests that Tesla uses pin 6 of the SCCM connector for LIN communication by default, though this reference specifically addresses Model S vehicles and may not directly apply to Model 3 or Model Y variants.

The LIN bus signal, when monitored at the SCCM connector, should display the characteristic 12-volt rectangular wave pattern of LIN protocol traffic[15]. During normal vehicle operation with the steering wheel inputs inactive, the LIN bus should remain at approximately 12 volts, representing the idle line state[15]. When the master controller transmits commands or the slave node responds with data, the signal should transition between 12 volts and 0 volts at specific bit timing intervals, with each bit lasting approximately 52 microseconds at the 19200 baud rate (1 second ÷ 19200 bits = 52 microseconds per bit). The exact waveform will show slight variations due to the rise and fall times of the driver circuitry, typically requiring 1 to 3 microseconds for transitions between the two voltage levels.

When monitoring this signal with a logic analyzer or oscilloscope, certain patterns should become apparent. If the vehicle is parked and idle, the master controller may poll the steering wheel module at regular intervals ranging from 10 to 100 milliseconds, depending on Tesla's specific protocol implementation. When the driver presses a steering wheel button or manipulates a scroll wheel, additional traffic should appear on the bus in response to the input. Capturing this traffic with a logic analyzer capable of recording at rates exceeding 100 kilosamples per second will provide sufficient detail to analyze the protocol structure and understand the message format.

The voltage levels on the LIN bus present a specific challenge for monitoring equipment. Standard logic analyzers designed for 3.3-volt or 5-volt signals will not correctly read a 12-volt signal without modification. A simple resistor voltage divider can step down the 12-volt signal to approximately 3.3 volts as follows: using a 10 kiloohm resistor from the LIN bus line to the analyzer input, and a 22 kiloohm resistor from the analyzer input to ground, produces an attenuation ratio of approximately 0.32, bringing a 12-volt signal down to approximately 3.8 volts. Alternatively, using a 12 kiloohm to 39 kiloohm divider ratio produces approximately 3-volt output. The exact values matter less than ensuring the divider is constructed with precision resistors to minimize skew, and that the analyzer input impedance (typically 1 megaohm) is significantly higher than the divider resistance to avoid loading effects. A more sophisticated approach involves using an automotive-grade LIN transceiver module, which is specifically designed for interfacing with 12-volt LIN signals and providing isolated logic-level outputs compatible with standard test equipment.

## Physical Access and Removal Procedures for SCCM Connector Access

Accessing the SCCM connector for non-destructive monitoring requires following a systematic procedure that safely isolates the steering column systems without requiring complete connector disconnection[30]. The recommended approach involves removing the steering wheel, removing the steering column shrouds, and then backprobing the SCCM connector to establish electrical contact with the LIN bus wire without disconnecting the connector itself[13][30]. This non-destructive approach preserves the connector integrity and allows the monitoring session to complete without requiring connector re-seating or recalibration procedures.

Begin by disconnecting the 12-volt battery negative terminal and waiting several minutes to allow the vehicle electrical systems to fully discharge[23][30]. Tesla service procedures emphasize this safety step to prevent airbag deployment during steering wheel removal and to ensure safe handling of the electrical system[23]. Next, remove the driver's airbag by pressing or prying the specific release points on the back surface of the steering wheel hub. Different model years use different release mechanisms, with some using a simple release button and others requiring a specific tool or pry technique. Once the airbag separates, disconnect the electrical connector from the airbag module and set the airbag aside in a safe location away from the steering wheel area[23].

With the airbag removed, the steering wheel attachment bolts become visible. These bolts typically use a T20 Torx driver and are torqued to approximately 9 newton-meters according to Tesla's specifications[30]. Remove these bolts and set them aside for reinstallation. Carefully pull the steering wheel straight away from the column shaft, taking care not to apply excessive rotational force that might damage the clockspring mechanism inside the SCCM. Mark the relationship between the steering wheel and steering column with a paint pen before removal to ensure proper wheel position upon reinstallation, as improper alignment can affect airbag sensor calibration and steering wheel control function.

With the steering wheel removed, locate the upper and lower steering column shrouds. The upper shroud is the trim panel that wraps around the upper portion of the column. Using a plastic trim tool, carefully press inward on the specific clip retention points along the edges of the upper shroud to release the clips[14]. The exact clip locations vary by model year, but typically appear along the bottom edge of the upper shroud where it interfaces with the lower shroud. Once all clips release, carefully pull the upper shroud upward and away from the column. Set this shroud aside safely to avoid damage.

The lower shroud should also release using the same plastic trim tool technique, though the exact process may vary by model[14][30]. In some cases, the lower shroud may remain in place, as the upper shroud separation provides sufficient access to the SCCM connector. The SCCM connector should now be visible at the top of the steering column shaft, appearing as a multi-pin connector with a retaining clip mechanism.

At this point, the backprobing approach can begin. A backprobe lead designed for automotive use features a fine needle or pin that can slide into a connector cavity alongside the existing terminal without damaging either the terminal or the cavity. The leads typically connect to an insulated handle with a banana jack or similar connection for attachment to test equipment. Position the backprobe lead carefully alongside the suspected LIN bus wire terminal (potentially pin 6 based on previous discussion) and apply gentle pressure while sliding the lead into the cavity alongside the terminal. The goal is to achieve contact with the back of the terminal without excessive force that might damage the connector.

Once the backprobe achieves contact with a terminal, verify the contact quality using an ohmmeter set to measure resistance. Place one meter probe against the backprobe connector on the external side and touch the other meter probe to a known good ground connection on the vehicle (such as the negative battery terminal or a engine block bolt), and observe the resistance reading. A properly made backprobe connection should show less than 1 ohm of resistance[13]. If the resistance exceeds a few ohms, the contact is poor and the backprobe should be repositioned or attempted with a fresh probe to achieve better contact.

Once a good backprobe connection is confirmed on the LIN bus wire, the monitoring session can proceed with the test equipment connected to the backprobe lead. The vehicle electrical system remains connected and operational, allowing normal steering wheel interaction during the monitoring period. This setup allows capturing LIN bus traffic under actual operating conditions with the vehicle systems functioning normally.

## Signal Tapping Methods: Non-Destructive Access Techniques

Non-destructive tapping of the steering wheel LIN bus offers several technical approaches, each with specific advantages and limitations depending on the monitoring equipment available and the acceptable risk level[13]. The backprobing technique described above represents one approach, but alternative methods exist that may prove more practical or reliable depending on specific circumstances.

The backprobe method offers the significant advantage of requiring no modification to the vehicle electrical system and no disconnection of the SCCM connector[13]. Once a backprobe successfully achieves contact with the LIN bus terminal, monitoring can proceed indefinitely without connector manipulation. However, backprobing requires steady hands, precise positioning in a confined space, and careful technique to avoid damaging connector cavities[13]. The backprobe needle tip may catch or scrape against the cavity edges if inserted at an angle, potentially scarring the cavity surface and making future connections more difficult. Additionally, vibration or connector movement during vehicle operation can cause backprobe leads to shift and lose contact, requiring periodic verification that the connection remains good.

An alternative non-destructive approach involves obtaining an aftermarket intermediate harness that allows connecting test equipment to the SCCM connector without using the connector itself. Some third-party manufacturers produce diagnostic harnesses specifically designed for steering column systems, featuring a pigtail connector that interfaces with the SCCM connector and provides banana jack test points for connection to monitoring equipment. These harnesses typically cost between fifty and two hundred dollars and provide repeatable, reliable connection to the LIN bus without requiring backprobing skills. However, sourcing such harnesses for Tesla vehicles may prove difficult, as Tesla's proprietary connector designs don't match standard automotive harnesses, and aftermarket support for Tesla steering column diagnostics remains limited.

A semi-destructive but readily reversible approach involves carefully disconnecting the SCCM connector and installing a temporary intermediate harness or test points on the disconnected connector before reinstalling it. This method requires fabricating or sourcing an intermediate harness that accepts the original SCCM connector on one end and provides test points or a secondary connector on the other end. The advantage of this approach is that the connection becomes extremely reliable and repeatable, requiring no backprobing skill or steady hands. The disadvantage is that it requires at least two full connector disconnect-reconnect cycles and necessitates performing the "push-pull-push" verification test specified by Tesla service procedures both times to ensure proper reconnection. Additionally, if the intermediate harness is improperly fabricated or uses incorrect wire gauges or connector types, the harness could introduce electrical problems that affect steering wheel function.

For those comfortable with minor connector modification, a third approach involves using a standard adhesive-backed test point adhesive strip applied to the SCCM connector body near the suspected LIN bus wire, with a tiny jumper wire soldered to the test point and connected to monitoring equipment. This method requires removing the SCCM connector for the soldering operation, performing the connection, and then reinstalling the connector. Solder connections to connector terminals require careful technique to avoid damaging the plastic connector body with excessive heat, and an unsuitable solder joint can cause intermittent contact issues that create difficult-to-diagnose electrical problems.

The voltage divider network approach deserves specific mention as an important design consideration regardless of which physical tapping method is employed. Because the LIN bus operates at 12 volts and most diagnostic equipment uses 3.3 or 5-volt logic levels, the signal must be stepped down before it reaches the test equipment. A properly designed divider uses precision resistors selected to produce the correct output voltage while minimizing loading effects on the LIN bus signal[15]. The specific divider ratio depends on the input impedance of the monitoring equipment and the desired output voltage, but a 10k-22k ohm divider is a reasonable starting point. The divider network should be assembled on a small circuit board or using precision surface-mount resistors to minimize inductance and ensure consistent performance during high-speed signal transitions.

Grounding represents a critical consideration for any signal tapping method. The monitoring equipment must share a common ground reference with the vehicle electrical system to ensure proper signal measurement[31]. The backprobe connection typically references one probe to ground, and this ground must connect to a proper vehicle ground point. Using the negative battery terminal as the ground reference proves reliable, as does any point on the engine block that shows direct electrical connection to the negative battery terminal. Avoiding ground loops requires ensuring that the ground connection path remains as direct and low-impedance as possible, avoiding longer cable runs through harnesses where higher resistance can degrade signal quality.

## Alternative Access Paths and System Limitations

While the SCCM connector represents the most direct access point for the steering wheel LIN bus, alternative paths and limitations exist that should be understood before committing to any specific monitoring approach[15][15]. Understanding these alternatives and their limitations provides context for why certain access methods may prove impractical despite theoretical soundness.

The OBD-II port on Tesla vehicles does not provide direct access to the steering wheel LIN bus according to available documentation[22]. Tesla's OBD-II implementation focuses on engine control parameters and vehicle diagnostic information, not steering wheel communications. Some references suggest that specialized diagnostic protocols might allow connection through the OBD-II port, but this represents speculation without supporting evidence in the provided sources. The OBD-II port provides access to the vehicle's Gateway module for diagnostic communication[22], which theoretically could provide access to LIN bus information if the Gateway firmware includes commands to relay LIN traffic, but this approach would require knowledge of Tesla's proprietary diagnostic protocols and specially developed diagnostic software.

The VCLEFT body controller represents the master node on the steering wheel LIN bus network[15]. In theory, accessing the LIN bus at the VCLEFT connector might provide an alternative to the SCCM connector, allowing monitoring of the same LIN traffic at a different physical location. However, VCLEFT is typically located deep inside the vehicle dashboard or interior components, requiring extensive interior trim removal to access. Additionally, the VCLEFT connector likely carries many additional signals and communications beyond just the steering wheel LIN bus, making it more difficult to identify and isolate the specific steering wheel LIN signal among multiple electrical connections.

The harness routing within the steering column presents another consideration. The LIN bus wire runs from the SCCM through the steering column harness assembly to the VCLEFT connector, routing through the steering column plastic shrouds and along the column shaft[23][25]. In theory, this wire could be accessed at any point along its routing by carefully separating harnesses or removing interior trim, but each point along the routing presents progressively more difficult access challenges. The SCCM connector remains the most accessible point because it represents the consolidation point for all steering column signals before they branch throughout the harness routing.

System limitations exist that constrain what monitoring can accomplish. The LIN bus represents a real-time communication network actively controlling steering wheel functions and responding to driver inputs. Monitoring this network provides visibility into what data transfers, but cannot determine the internal processing logic or decision-making within the SCCM module or the VCLEFT controller. Additionally, the LIN bus traffic should only contain steering wheel control messages; other steering wheel functionality like airbag deployment involves separate high-voltage circuits that do not appear on the LIN bus. Understanding these limitations prevents unrealistic expectations about what monitoring will reveal.

The proprietary nature of Tesla's LIN protocol messages presents another limitation. While the LIN bus itself uses the standard LIN protocol framework at 19200 baud, Tesla almost certainly defines proprietary message formats for specific steering wheel functions like scroll wheel position, button identities, and state information. Without access to Tesla's internal protocol documentation, interpreting captured LIN traffic requires reverse-engineering the message formats through careful observation and pattern analysis. This represents an achievable but time-consuming process requiring multiple monitoring sessions and careful note-taking of which steering wheel actions correspond to which LIN messages.

## Practical Implementation Considerations and Setup

For someone committed to accessing the steering wheel LIN bus on a Tesla Model 3 or Model Y for a single 20-minute bench session, several practical considerations will determine success or failure[13][30]. The confined space, complexity of the steering column assembly, and need to re-assemble the system after monitoring all require careful planning.

Begin by ensuring adequate workspace. The steering wheel and steering column removal procedures require sufficient room to maneuver the steering wheel out of the vehicle and to position tools and test equipment around the exposed steering column[30]. A well-lit workspace with a workbench or sturdy table provides better results than attempting to work in a dimly lit parking lot or garage with inadequate lighting. LED work lights suspended above the work area prove invaluable for illuminating the cramped space where the SCCM connector resides.

Gather all required tools and test equipment before beginning work. The basic toolkit includes a torque wrench capable of measuring forces in the 1-2 newton-meter range (for steering wheel bolts), a T20 Torx driver socket, a plastic trim tool for releasing shroud clips, and basic screwdrivers. For the LIN bus monitoring, an oscilloscope or logic analyzer capable of recording at least 100 kilosamples per second provides sufficient detail to capture LIN protocol traffic[10]. A USB-connected logic analyzer or oscilloscope typically costs between fifty and three hundred dollars and represents the most practical tool for this task. Alternatively, a simple digital multimeter capable of measuring DC voltage can at least verify that the suspected LIN bus wire carries 12-volt signals, confirming the correct wire identification even if it cannot capture the detailed signal waveforms.

Obtain or fabricate a voltage divider network suitable for the test equipment being used[15]. If using a 3.3-volt logic analyzer, the divider should convert the 12-volt LIN signal to approximately 3 volts. If using an oscilloscope with higher input voltage ratings, the divider may not be necessary, though an oscilloscope probe with attenuation built in (such as a 1:10 probe) will safely handle the 12-volt input. For a logic analyzer input with 1 megaohm input impedance, a divider using 10 kilohm and 22 kilohm resistors provides appropriate performance and impedance characteristics.

The monitoring session should plan for a specific objective to maximize productivity in the limited 20-minute timeframe. Rather than attempting to understand the entire LIN protocol, focus on capturing a specific set of interactions. For example, the monitoring session might focus on capturing the LIN bus traffic that occurs when a steering wheel button is pressed, or when the scroll wheel is rotated. By identifying the specific steering wheel action that generates the LIN traffic, correlating observed traffic patterns to known actions becomes much more feasible.

Document the specific SCCM connector cavity where the backprobe achieves contact before disconnecting any test equipment. Make a note indicating the cavity position (counting from one end of the connector), the wire color (if visible), and the exact signal characteristics observed (resting voltage, frequency of state changes, approximate message patterns). This documentation provides the reference needed to re-establish the connection if the probe shifts position or to identify the same wire on future monitoring sessions.

Performance expectations should be realistic. At 19200 baud with typical steering wheel control messages, the LIN bus likely carries messages in the range of 20 to 100 bytes per second, meaning hundreds to thousands of bits per second are constantly flowing on this network. A logic analyzer recording at 100 kilosamples per second can easily capture hours worth of LIN traffic to a USB flash drive or computer hard drive for later analysis. However, understanding what the captured data represents requires spending additional time analyzing the captured waveforms and correlating them to specific steering wheel actions.

## Signal Characteristics and Protocol Analysis Fundamentals

When the backprobe successfully connects to the steering wheel LIN bus wire and the monitoring equipment begins recording, specific signal characteristics should become apparent that confirm proper connection to the correct wire. Understanding these characteristics allows verification of successful connection and provides initial insights into the protocol structure[10][15][15].

The LIN bus signal, when idle with no steering wheel buttons pressed and no master controller polling activity, should rest at approximately 12 volts DC. This represents the "idle line" state of the LIN bus. Some test equipment may display this as a flat line at the 12-volt level with perhaps minor ripple or noise of a few millivolts amplitude.

When the master controller begins sending messages to the steering wheel module, the signal should begin transitioning between 12 volts and 0 volts according to the LIN protocol bitstream. The transition rate depends on the steering wheel message frequency, but typically messages appear at intervals ranging from 10 to 100 milliseconds when the vehicle is awake and functional. Each message at 19200 baud requires approximately 5 to 10 milliseconds to transmit (depending on message length), meaning that observable gaps should exist between messages where the bus returns to the idle 12-volt state.

Individual bits in the LIN protocol appear as specific time intervals where the bus remains at 0 volts versus 12 volts. At 19200 baud, each bit interval lasts approximately 52 microseconds. A logic analyzer recording at 100 kilosamples per second captures one sample every 10 microseconds, providing approximately 5 samples per bit interval. This sampling rate provides sufficient resolution to capture the bit transitions but may not show the full detail of rise and fall times. For more detailed analysis, higher sampling rates (1 megasamples per second or higher) reveal the precise shape of signal transitions and can identify potential issues with signal quality or circuit performance.

A standard LIN frame structure comprises a header section containing synchronization and identification information, followed by a data section containing the message payload, and concluded with a checksum field allowing error detection. The header begins with a "break field" where the bus remains at 0 volts for an extended period (approximately 13 bit times or about 0.68 milliseconds), followed by a "sync byte" of 0x55 (alternating 0 and 1 bits for clock synchronization). This distinctive pattern of a long low-voltage period followed by alternating transitions represents the most easily identifiable feature of LIN messages and can be used to mark frame boundaries in recorded data.

When the driver manipulates steering wheel controls, additional LIN traffic should become apparent. Pressing a steering wheel button should generate a message from the slave SCCM to the master VCLEFT controller indicating the button press event. Rotating a scroll wheel should generate messages indicating the wheel position change. These event-driven messages should appear at times when the controls are manipulated, allowing correlation between observable steering wheel actions and corresponding LIN traffic patterns.

If the monitoring session is also capturing video or audio recordings of the steering wheel actions being performed (for example, a smartphone video showing fingers pressing buttons while the LIN bus is being captured), post-session analysis can correlate specific LIN messages to specific button presses and scroll wheel rotations. This approach, while requiring additional coordination during the monitoring session, provides the most straightforward path to understanding what messages correspond to what steering wheel actions.

## Conclusion and Recommendations

Based on available Tesla service documentation and technical references, the Steering Column Control Module (SCCM) connector represents the most practical and accessible point for monitoring the steering wheel LIN bus in Tesla Model 3 and Model Y vehicles[2][7][30]. The SCCM sits at the top of the steering column shaft after steering wheel removal, consolidates all steering wheel electrical signals, and carries the LIN bus communication on what appears to be pin 6 (or a pin in the immediate vicinity) according to service technical discussions, though this remains unconfirmed for Model 3/Y specifically[7].

The primary physical access method involves removing the steering wheel, releasing the steering column shroud clips, and accessing the SCCM connector for backprobing or intermediate harness connection[14][30]. This process typically requires 20 to 30 minutes including re-assembly, leaving limited time for actual monitoring within a 20-minute total session timeframe. A more realistic approach allocates 20 minutes for setup and access, then conducts the monitoring session separately with the system already disassembled.

For the most reliable access approach, the following sequence is recommended: First, disconnect the 12-volt battery and wait several minutes for electrical system discharge. Second, remove the driver's airbag from the back of the steering wheel hub. Third, remove the steering wheel bolts using a T20 Torx driver and pull the wheel free. Fourth, remove the upper and lower steering column shrouds using plastic trim tools to release the retaining clips. Fifth, identify the SCCM connector at the top of the column shaft and carefully insert a backprobe lead into the suspected LIN bus signal cavity, or alternatively, disconnect the connector and install an intermediate harness if non-destructive access is not feasible.

The LIN bus signal operates at 12-volt logic levels at a 19200 baud transmission rate[10][15]. A voltage divider is required to step down the 12-volt signal to approximately 3 volts for compatibility with standard 3.3-volt logic analyzers. The signal should show clear 12-volt idle levels transitioning to 0 volts during message transmission, with observable message frames appearing at intervals ranging from 10 to 100 milliseconds.

The primary limitation affecting this monitoring approach is the lack of publicly available Tesla proprietary LIN message format documentation. While the physical connection and signal characteristics can be verified through direct observation, interpreting what specific messages mean requires reverse-engineering through controlled experiments correlating specific steering wheel actions to specific captured messages.

For future reference, individuals undertaking this procedure should photograph or carefully document the exact SCCM connector cavity location of the LIN bus wire for reference during future monitoring sessions. Creation of detailed reference photos showing the connector orientation, cavity numbering, and wire color identification would significantly accelerate future access attempts and represent a valuable contribution to community knowledge bases focused on Tesla vehicle technical documentation.

The approach remains technically feasible for motivated individuals with appropriate test equipment and mechanical skills, though the complexity of the steering column assembly and the confined working space suggest that this project is most suitable for experienced automotive electronics technicians rather than casual experimenters. The significant limitation remains the proprietary nature of Tesla's communication protocols, which means that successful signal capture provides only partial value without access to protocol decoding references.

## Citations

1. https://service.tesla.com/docs/ModelS/ElectricalReference2012/s-rhd-sop3/2014.3_ModelS_RHD_Release.pdf - https://service.tesla.com/docs/ModelS/ElectricalReference2012/s-rhd-sop3/2014.3_ModelS_RHD_Release.pdf
2. https://service.tesla.com/docs/ModelY/ServiceManual/2025/en-us/GUID-727CBFB7-88C9-4DF4-BD41-62FC53AEBC1C.html - https://service.tesla.com/docs/ModelY/ServiceManual/2025/en-us/GUID-727CBFB7-88C9-4DF4-BD41-62FC53AEBC1C.html
3. https://service.tesla.com/docs/ModelS/ServiceManual/Palladium/en-us/GUID-502861E2-2498-4E05-BD0D-3291C3B9522F.html - https://service.tesla.com/docs/ModelS/ServiceManual/Palladium/en-us/GUID-502861E2-2498-4E05-BD0D-3291C3B9522F.html
4. https://service.tesla.com/docs/ModelS/ServiceManual/en-us/GUID-C25DAA68-1695-492C-A60E-91C47DE7ECA9.html - https://service.tesla.com/docs/ModelS/ServiceManual/en-us/GUID-C25DAA68-1695-492C-A60E-91C47DE7ECA9.html
5. https://service.tesla.com/docs/Model3/ElectricalReference/prog-20/interactive/html/index.html - https://service.tesla.com/docs/Model3/ElectricalReference/prog-20/interactive/html/index.html
6. https://www.youtube.com/watch?v=tkaD_jomweA - https://www.youtube.com/watch?v=tkaD_jomweA
7. https://teslamotorsclub.com/tmc/threads/pre-dec-2014-s-heated-steering-wheel-retrofit.165374/page-7 - https://teslamotorsclub.com/tmc/threads/pre-dec-2014-s-heated-steering-wheel-retrofit.165374/page-7
8. https://service.tesla.com/docs/Model3/ServiceManual/en-us/GUID-644CC9AB-84DA-40D8-A39B-F9A49966CAE7.html - https://service.tesla.com/docs/Model3/ServiceManual/en-us/GUID-644CC9AB-84DA-40D8-A39B-F9A49966CAE7.html
9. https://service.tesla.com/docs/ModelS/ElectricalReference2012/s-lhd-sop1/2012_ModelS_LHD_Release.pdf - https://service.tesla.com/docs/ModelS/ElectricalReference2012/s-lhd-sop1/2012_ModelS_LHD_Release.pdf
10. https://github.com/nunojpg/homelink-explorer - https://github.com/nunojpg/homelink-explorer
11. https://service.tesla.com/docs/ModelS/ServiceManual/en-us/GUID-423EA0CF-72E4-47BE-A8DA-E764B604A444.html - https://service.tesla.com/docs/ModelS/ServiceManual/en-us/GUID-423EA0CF-72E4-47BE-A8DA-E764B604A444.html
12. https://teslamotorsclub.com/tmc/threads/obd-ii-connector-pinout-list.136532/ - https://teslamotorsclub.com/tmc/threads/obd-ii-connector-pinout-list.136532/
13. https://www.youtube.com/watch?v=op6Djd9PbIc - https://www.youtube.com/watch?v=op6Djd9PbIc
14. https://service.tesla.com/docs/Model3/ServiceManual/2024/en-us/GUID-070205A3-CD6A-466D-8458-C008F2F05115.html - https://service.tesla.com/docs/Model3/ServiceManual/2024/en-us/GUID-070205A3-CD6A-466D-8458-C008F2F05115.html
15. https://service.tesla.com/docs/Public/Roadster/TheoryOp/1.2.5/do/17.html - https://service.tesla.com/docs/Public/Roadster/TheoryOp/1.2.5/do/17.html
16. https://service.tesla.com/docs/ModelS/ServiceManual/en-us/GUID-1B5B5170-5ADC-422A-BACE-8741C4847BFD.html - https://service.tesla.com/docs/ModelS/ServiceManual/en-us/GUID-1B5B5170-5ADC-422A-BACE-8741C4847BFD.html
17. https://service.tesla.com/docs/Model3/ElectricalReference/ - https://service.tesla.com/docs/Model3/ElectricalReference/
18. https://www.youtube.com/watch?v=HLTNMy9pJt8 - https://www.youtube.com/watch?v=HLTNMy9pJt8
19. https://service.tesla.com/docs/Model3/ElectricalReference/prog-187/connector/x032/ - https://service.tesla.com/docs/Model3/ElectricalReference/prog-187/connector/x032/
20. https://service.tesla.com/docs/Model3/ElectricalReference/prog-233/interactive/html/index.html - https://service.tesla.com/docs/Model3/ElectricalReference/prog-233/interactive/html/index.html
21. https://service.tesla.com/docs/Model3/ServiceManual/en-us/index.html - https://service.tesla.com/docs/Model3/ServiceManual/en-us/index.html
22. https://service.tesla.com/docs/Model3/ServiceManual/2024/en-us/GUID-78F8844F-9D1F-42FF-B92C-76D32B25F223.html - https://service.tesla.com/docs/Model3/ServiceManual/2024/en-us/GUID-78F8844F-9D1F-42FF-B92C-76D32B25F223.html
23. https://service.tesla.com/docs/Model3/ServiceManual/en-us/GUID-748469CF-09D5-4ECA-9234-255BFAAC6FFD.html - https://service.tesla.com/docs/Model3/ServiceManual/en-us/GUID-748469CF-09D5-4ECA-9234-255BFAAC6FFD.html
24. https://www.tesla.com/ownersmanual/cybertruck/en_us/GUID-46420EE2-F6B0-4E95-88D5-E50CB3061101.html - https://www.tesla.com/ownersmanual/cybertruck/en_us/GUID-46420EE2-F6B0-4E95-88D5-E50CB3061101.html
25. https://service.tesla.com/docs/Model3/ServiceManual/en-us/GUID-4FCC9139-64CC-4A30-BA80-8DA10F5B4F6A.html - https://service.tesla.com/docs/Model3/ServiceManual/en-us/GUID-4FCC9139-64CC-4A30-BA80-8DA10F5B4F6A.html
26. https://www.youtube.com/watch?v=ZFV0sz7cQHc - https://www.youtube.com/watch?v=ZFV0sz7cQHc
27. https://www.youtube.com/watch?v=AVCHC2cw0v0 - https://www.youtube.com/watch?v=AVCHC2cw0v0
28. https://service.tesla.com/docs/Model3/ElectricalReference/prog-219/interactive/html/index.html - https://service.tesla.com/docs/Model3/ElectricalReference/prog-219/interactive/html/index.html
29. https://www.youtube.com/watch?v=62txKc7EtCA - https://www.youtube.com/watch?v=62txKc7EtCA
30. https://service.tesla.com/docs/Model3/ServiceManual/en-us/GUID-51C82033-95D3-4CEA-AE26-4C3C0C380BF2.html - https://service.tesla.com/docs/Model3/ServiceManual/en-us/GUID-51C82033-95D3-4CEA-AE26-4C3C0C380BF2.html
31. https://www.youtube.com/watch?v=UUhyXbdz38Y - https://www.youtube.com/watch?v=UUhyXbdz38Y
32. https://service.tesla.com/docs/Model3/ServiceManual/2024/en-us/GUID-9C64A91D-0542-45F6-9E73-9F8855787876.html - https://service.tesla.com/docs/Model3/ServiceManual/2024/en-us/GUID-9C64A91D-0542-45F6-9E73-9F8855787876.html
