lakewoodphone/tesla-lin-chip/research/responses/2026-05-17-2025-tesla-model-x-sccm-lin-passive-capture-access-physical-access-points-lin-wi-03cb52ea.md

---
job_id: 03cb52ea-7cf1-4930-b56e-e6f3e96decdb
directive_id: 2025-tesla-model-x-sccm-lin-passive-capture-access-physical-access-points-lin-wi
title: 2025 Tesla Model X SCCM LIN passive capture access: physical access points, LIN wire identification, and safety constraints for passive capture.
domain: general
sensitivity: standard
model_used: sonar-deep-research
provider: perplexity
status: complete
completed_at: 2026-05-17T16:47:39.445242+00:00
cost_usd: 0.43601
input_tokens: 178
output_tokens: 12528
reasoning_tokens: 53596
search_count: 30
citation_count: 25
verifier_status: passed
schema_version: 1
---

# Passive LIN-Bus Capture on a 2025 Tesla Model X Steering Column Control Module: Architecture, Access Points, Signal Identification, and Safety Constraints

The 2025 Tesla Model X employs a networked electronics architecture in which the Steering Column Control Module (SCCM) is integrated into a broader low‑voltage communication system that includes Controller Area Network (CAN) and Local Interconnect Network (LIN) segments.[9][1][23] For an engineer or researcher seeking to passively observe LIN communication to or from the SCCM—without transmitting onto the bus—the problem decomposes into three tightly coupled questions: where one can physically access the wiring in a modern Tesla, how to determine which conductor actually carries LIN traffic, and what electrical, functional‑safety, and cybersecurity constraints must govern such a measurement so that it remains both technically valid and safe. This report synthesizes open Tesla service documentation, generic LIN‑bus physical‑layer references, and safety/security literature to provide a structured, technically detailed view of passive SCCM‑LIN capture on a late‑model Tesla Model X. The discussion is framed explicitly for legitimate diagnostic, research, and validation use in a controlled environment, and emphasizes that any practical implementation must be anchored in vehicle‑specific schematics and formal safety practices rather than informal experimentation.[6][10][15]  

## 1. Architectural Context: LIN in Tesla and the Role of the SCCM

### 1.1 LIN as a subordinate network in modern vehicles

Local Interconnect Network is a low‑cost, low‑speed serial bus standardized in ISO 17987 and widely used in modern vehicles to connect simple actuators and sensors such as door locks, window lifts, mirror modules, and seat controls.[1][1][23] In contrast to CAN’s multi‑master differential bus, LIN has a single master node that schedules all communication and up to fifteen slave nodes, forming what is typically described as a LIN cluster.[1][1][23] Each node contains at least a microcontroller with a serial interface and a LIN transceiver; the master node is usually a larger ECU that also acts as a gateway to the vehicle’s main CAN backbone.[1][9][1] The physical layer is notably simple: a single communication conductor plus ground, operated at the vehicle’s low‑voltage supply level, usually 12 V, with bitrates from 1 to 20 kbit/s and typical lengths on the order of a few meters.[1][9][1][23]  

The single‑wire, battery‑referenced signaling of LIN brings substantial cost and complexity reductions in body electronics compared with CAN, because it eliminates the need for twisted pairs and termination resistors and allows a large number of low‑pin‑count devices to share one shared line.[1][1][22][23] However, the same attributes that reduce cost also constrain LIN’s domain of application: the protocol’s single‑master architecture introduces a single point of failure, the single‑ended line is more susceptible to electromagnetic interference than CAN’s differential pair, and the error‑handling and diagnostic capabilities are comparatively modest.[1][1][22][23] Consequently, LIN is deliberately confined to systems whose failure is considered inconvenient rather than safety‑critical, such as windows, mirror actuation, interior climate control flaps, or seat adjustment, while braking, powertrain, and airbag systems remain on higher‑integrity networks.[1][19][23]  

From a signaling standpoint, LIN uses dominant and recessive levels that correspond to low and high voltages on the single bus line relative to ground, rather than complementary levels on a pair of wires.[9][1][22] The master node side of the bus includes an external pull‑up resistor on the LIN line, typically near 1 kΩ in series with a diode to the vehicle battery, that biases the bus high when no node is driving it.[1][22][23] Each slave node integrates a much weaker internal pull‑up, around 20–30 kΩ, to avoid excessive current draw while still ensuring the node’s input stages have a defined bias.[1][22] When any node transmits a dominant bit, the LIN transceiver effectively pulls the bus down toward ground, overriding the pull‑up and thus encoding a logic 0. When no node drives the line, the pull‑up returns the bus to a high, recessive level, encoding a logic 1.[1][22]
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
