lakewoodphone/tesla-lin-chip/photos/IMG_0225.jpg

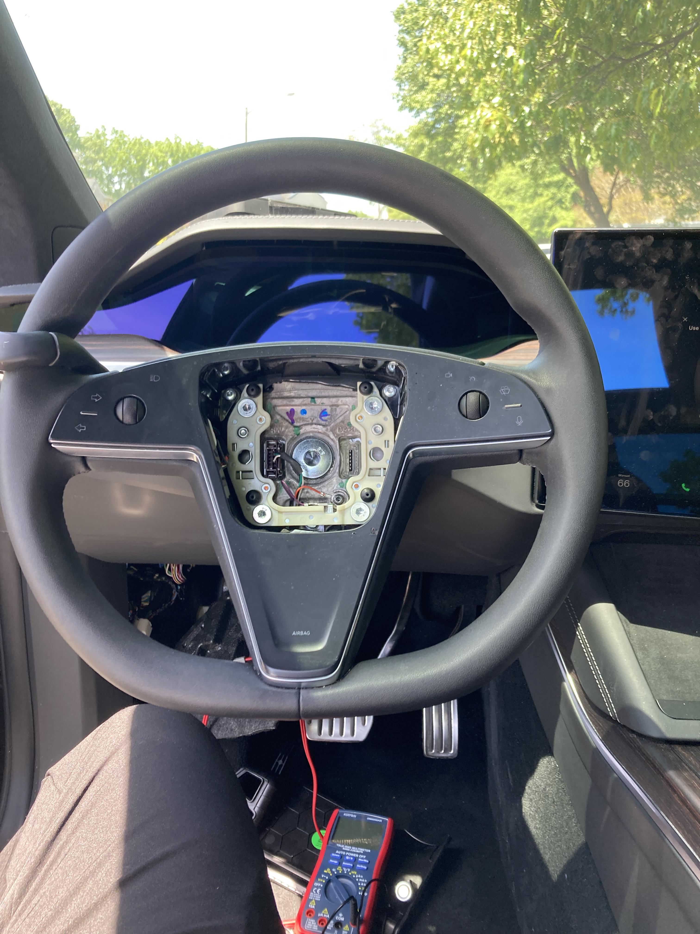
photos/IMG_0225.jpg
