lakewoodphone/tesla-lin-chip/photos/IMG_0227.jpg

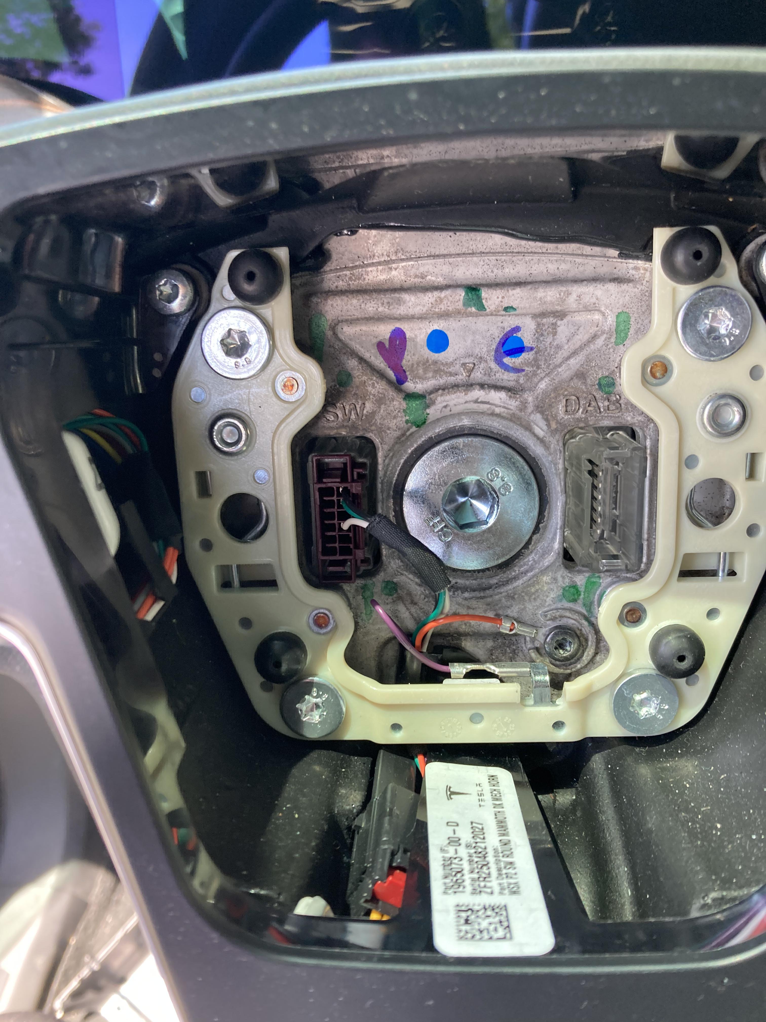
photos/IMG_0227.jpg
