lakewoodphone/tesla-lin-chip/photos/IMG_0229.jpg

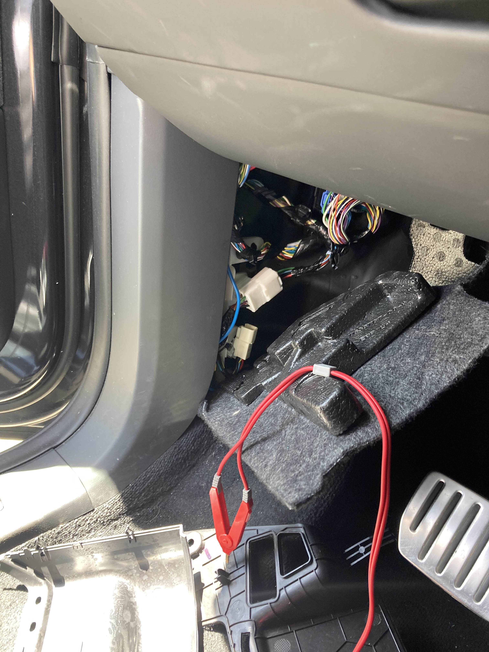
photos/IMG_0229.jpg
