lakewoodphone/tesla-lin-chip/photos/IMG_0230.jpg

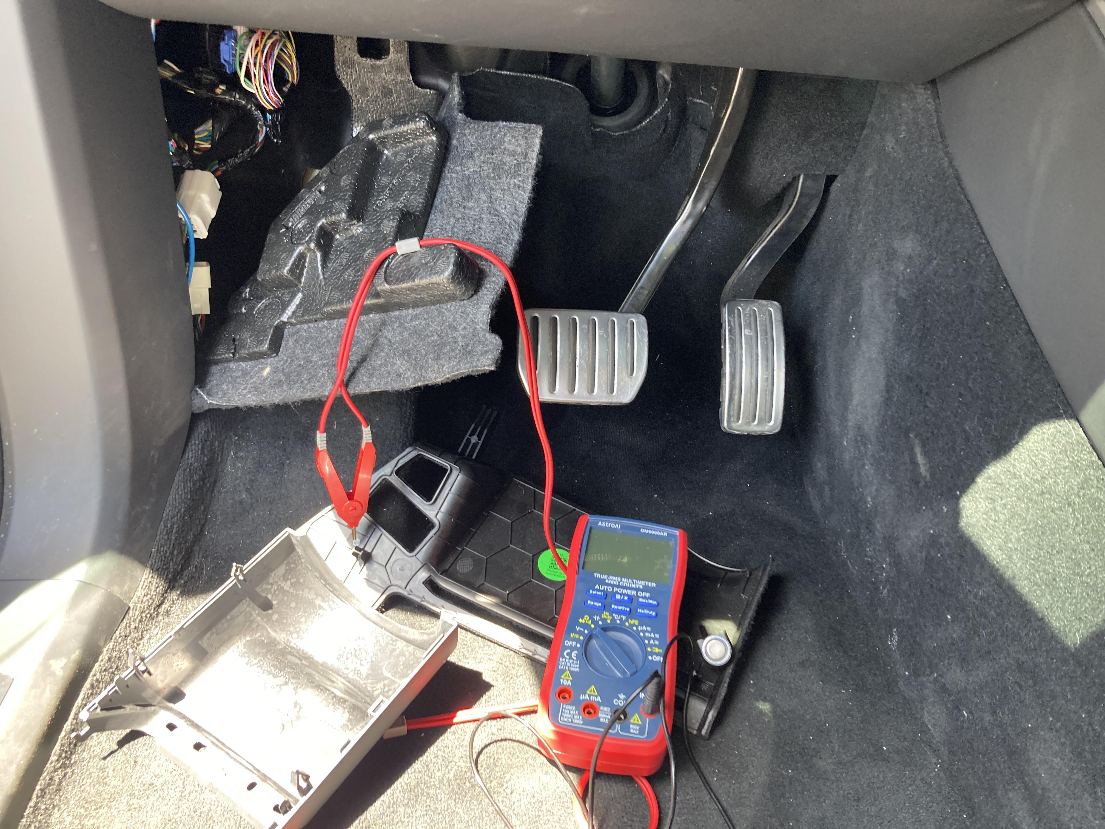
photos/IMG_0230.jpg
