lakewoodphone/tesla-lin-chip/photos/IMG_0231.jpg

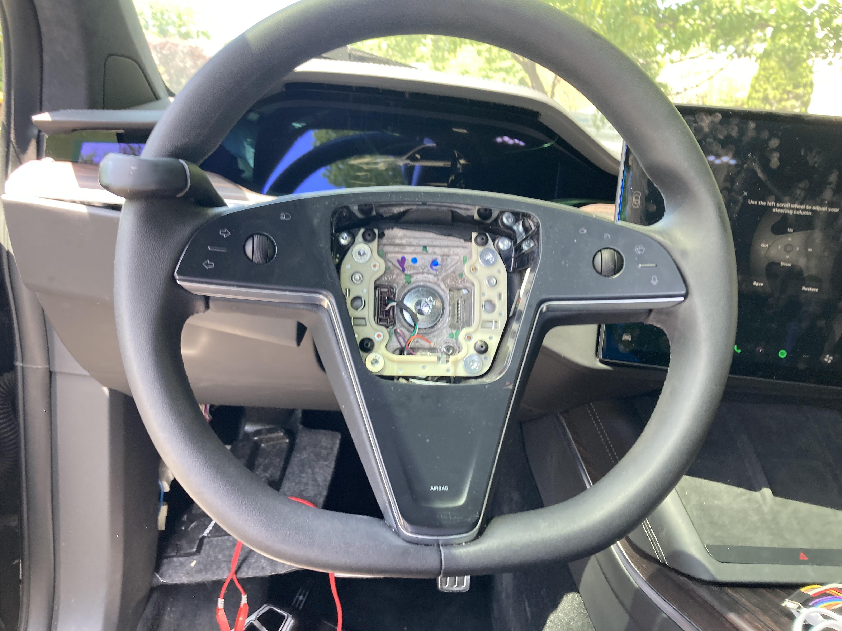
photos/IMG_0231.jpg
