lakewoodphone/tesla-lin-chip/photos/IMG_0232.jpg

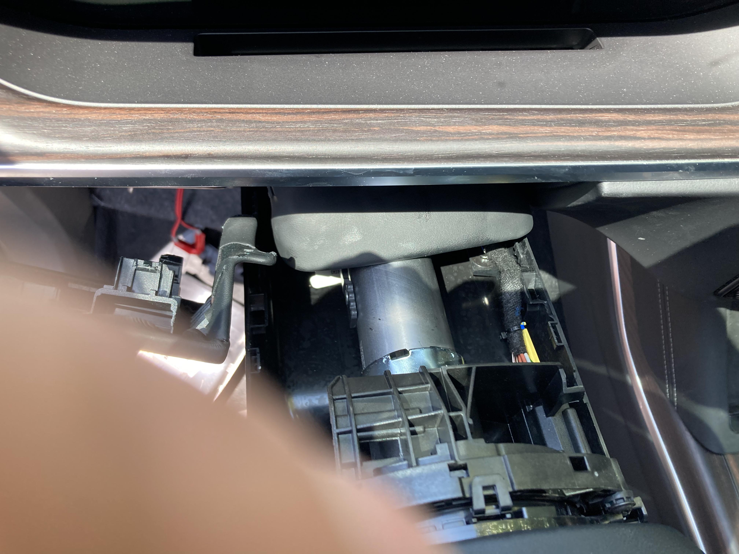
photos/IMG_0232.jpg
