lakewoodphone/tesla-lin-chip/research/directives/019-tesla-purchase-due-diligence.md

# Research Directive 019: Tesla Model 3 Purchase Due Diligence

**Date:** 2026-04-27
**Priority:** URGENT — same-day car purchase decision support
**Decision Window:** The owner is trying to buy a car this week and may proceed today if the target passes due diligence.
**Research Mode:** External research team, independent analysis. Teams have no prior context; this directive is self-contained.
**Primary Question:** Should the owner buy Easterns stock `169193`, a 2020 Tesla Model 3 Standard Range Plus with Enhanced Autopilot listed, and what must be verified before purchase?

---

## Executive Summary

The owner wants a Tesla and is excited by the Tesla driver-assistance stack. This preference is real value, not a novelty. A cheap mainstream sedan should not automatically outrank a viable Tesla unless the Tesla has material hidden risk.

The current target is a **2020 Tesla Model 3 Standard Range Plus** at Easterns Automotive Group of Temple Hills:

- **VIN:** `5YJ3E1EA2LF805901`
- **Stock:** `169193`
- **Dealer:** Easterns Automotive Group of Temple Hills, 4809 St Barnabas Road, Temple Hills, MD 20748
- **Listing / Roadster URL:** `https://express.easterns.com/express/used/5YJ3E1EA2LF805901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`
- **Roadster checkout state:** Account is created and MFA verified; checkout deal `51566497` reached pickup/delivery. Do not proceed into credit, ID, payment, or final purchase commitment without owner approval.
- **Price signal as of 2026-04-27 17:15 UTC:** `$20,750` Easterns special price; `$23,298` Roadster pay-cash total on the vehicle page.
- **Mileage:** `42,888 mi`
- **History shown by Roadster:** Clean CARFAX, CARFAX One-Owner.
- **Software/features shown by listing:** Enhanced Autopilot, Active Cruise Control, Navigation System, heated front seats, memory seat, 18-inch Aero wheels.
- **Dealer text on page:** Advertised price valid for 24 hours starting 6:00 AM Monday, April 27, 2026. Processing fee is `$799` in Virginia and Maryland and is not required by law. Website listings may not reflect real-time availability.
- **Dealer warranty claim:** Easterns mentions a 7-day return policy and complimentary 30 day / 1,000 mile warranty, but terms need verification.

The team’s job is to give a fast, evidence-based buy/no-buy recommendation and a checklist of final gates. Focus on what could make this a good buy, what could make it a trap, what credits/incentives are actually available in April 2026, whether the Tesla software package should have resale value, and whether the price is strong enough without assuming credits that no longer exist.

---

## Current State And Constraints

### Current Purchase State

The car is not bought yet. The account/checkout path is staged, but the final gates remain unresolved.

The owner’s buying system has already sent Easterns/Alex Salazar a written serious-buyer follow-up saying the buyer is in checkout and ready to continue if Easterns confirms:

1. Enhanced Autopilot is a paid package on the car and will remain after ownership/Tesla-account transfer.
2. There are no mandatory add-ons/protection plans beyond listed tax/title/registration/fees.
3. Easterns can process any available used clean vehicle credit at point of sale if the car and buyer qualify.

As of the latest refresh, Easterns has not yet answered those gates.

### Communication Constraints

- No live phone call with Easterns has happened.
- No completed voice conversation with any Tesla seller/dealer has happened in this current Tesla buy lane.
- Do not assume any phone-call representations exist. All usable evidence is from listings, Roadster checkout/page text, Gmail, Google Voice text, or future written dealer confirmation.
- The operating rule is written-first only. The AI assistant must not call dealers because a voice call could reveal that it is an AI. A human/owner call is allowed only if the lane is already qualified and worth live human time.
- External research teams should **not contact dealers or submit forms**. Research only. The owner’s buying agent will handle dealer communication.

### Owner Preferences

- The owner would be genuinely excited to buy a Tesla.
- Tesla Full Self-Driving / Enhanced Autopilot / Tesla driving-stack value should be treated as real value in the recommendation.
- The owner still cares about not getting trapped by hidden fees, software that disappears after transfer, warranty/battery issues, or weak resale.
- The owner wants a practical buy recommendation, not a generic EV essay.

---

## Critical Credit / Incentive Issue To Verify First

The research team must verify current federal, state, utility, and dealer incentives before making any net-price recommendation.

Initial IRS baseline found on 2026-04-27:

- IRS Used Clean Vehicle Credit page says the **Previously-Owned Clean Vehicle Credit is not available for vehicles acquired after Sept. 30, 2025**.
- The same IRS page says that, for eligible purchases acquired on or before Sept. 30, 2025, the credit was 30% of sale price up to `$4,000`, for a used EV bought from a licensed dealer for `$25,000` or less, subject to buyer income and other restrictions.
- IRS seller/dealer requirements page says clean vehicle credits are not available for vehicles acquired after Sept. 30, 2025, while some reporting remains open for prior eligible transactions.

Because today is **April 27, 2026**, do **not** assume the federal used clean vehicle credit exists. Treat the `$4,000` used EV credit as likely unavailable unless the team finds a legally reliable current exception that applies to this exact purchase date.

Research must answer:

1. Is any federal used clean vehicle credit available for a used Tesla acquired in April 2026?
2. If not, what exact law/change ended it, and what source proves it?
3. Are there any New Jersey, Maryland, utility, insurance, charging, registration, sales-tax, or dealer-specific incentives available for a **used** EV purchase in April 2026?
4. Does New Jersey impose normal sales tax on this used EV in April 2026, or is there still any zero-emission sales tax exemption/phase-out benefit?
5. Does the sale price test, if any credit exists, include dealer doc/processing fees such as Easterns’ `$799` fee?
6. If the federal credit is gone, does this car still look like a strong buy at approximately `$23,298` pay-cash total?

---

## Vehicles To Analyze

### Primary Target: Easterns Stock `169193`

**2020 Tesla Model 3 Standard Range Plus**
VIN `5YJ3E1EA2LF805901`, stock `169193`, Easterns Temple Hills.

Known facts from Roadster page:

- `$20,750` Easterns special price
- `$23,298` pay-cash total shown on refreshed vehicle page
- `42,888 mi`
- Clean CARFAX
- CARFAX One-Owner
- Enhanced Autopilot listed
- RWD, 1-speed automatic
- White exterior, black interior
- EPA estimate shown: 148 city / 132 highway / 141 average MPGe
- Processing fee disclosure: `$799` in Virginia and Maryland, not required by law
- Pickup at Easterns Temple Hills; delivery options vary by ZIP
- Optional protection plans visible: vehicle service contract, GAP, ceramic protection. These must remain optional.

Open gates:

- Confirm paid Enhanced Autopilot remains after Tesla-account transfer.
- Confirm no mandatory add-ons/protection plans.
- Confirm exact itemized out-the-door total for Lakewood, NJ `08701`.
- Confirm whether any current credit/incentive exists and whether dealer can process it.
- Confirm current availability and ability to hold/claim the car.
- Confirm battery/drive-unit warranty dates and remaining coverage.
- Confirm battery health/range estimate and whether any high-voltage battery, drive-unit, charging, water intrusion, suspension, or title/service issues exist.

### Backup Target: Easterns Stock `169314`

**2023 Tesla Model 3 Standard Range / Standard Range Plus**, Easterns Laurel.
VIN `5YJ3E1EA8PF508735`, stock `169314`.

Known facts:

- Roadster total purchase price previously extracted: `$26,844.65` to `08701`
- Breakdown included `$23,950` price, `$1,641.15` NJ tax, `$391.50` DMV, `$20` electronic filing, `$23` lien, `$799` processing, `$20` temp tag
- Listing and Easterns page say Enhanced Autopilot
- Lower mileage/newer than `169193`
- Worse value unless the primary car fails or there are major battery/resale advantages

### Other Easterns Inventory To Consider If Relevant

- `169302` / VIN `5YJ3E1EA5MF977163`: 2021 Model 3 SR+, Enhanced Autopilot listed, `$20,590` list, `$23,262` online pay-cash total, `46,417 mi`, gray interior. Could be a serious alternative if 2021 refresh/LFP/heat pump/battery chemistry materially improves value versus `169193`.
- `168439` / VIN `5YJ3E1EA2LF741214`: 2020 Model 3 SR+, `$19,490` list, `$22,089` pay-cash total, `53,427 mi`, but does not list Enhanced Autopilot. Lower priority unless software package on `169193` fails.
- `169130` / VIN `5YJ3E1EA1PF661716`: 2023 Model 3 SR+, Enhanced Autopilot listed, `$21,950` list, `$24,712` online pay-cash total, `58,659 mi`. Higher miles than `169314`; evaluate only if it has a better confirmed software/credit situation.

### Non-Easterns Tesla Backup

Automotive Avenues stock `61610A`, VIN `5YJ3E1EB4LF790696`: 2020 Tesla Model 3 Long Range AWD, listed `$22,995`, available per Melissa Dixon, costs are listed price plus `$799` title/doc plus tax and DMV. Dealer reply indicates this vehicle does **not** have FSD and that FSD generally must be bought by the new buyer / subscriptions do not transfer. It is a practical Long Range AWD backup, not the primary software-stack deal.

---

## Research Questions

### 1. Is Stock `169193` A Good Buy At The Current Price?

Provide a market-comps analysis for a 2020 Tesla Model 3 Standard Range Plus with about 43k miles, clean one-owner history, and Enhanced Autopilot listed.

Use current sources such as Cars.com, Autotrader, CarGurus, Edmunds, KBB, Tesla used inventory, Recurrent, Carfax listings, and any wholesale/auction indicators you can access. Separate retail ask, dealer retail, private party, trade-in, and wholesale signals when possible.

Answer:

- Is `$20,750` list / approximately `$23,298` pay-cash total objectively strong, average, or weak?
- What is a fair buy price and a walk-away price?
- How much should Enhanced Autopilot add to market value, if it truly transfers?
- How much should one-owner / Clean CARFAX / 42,888 miles add or subtract?
- What comparable cars are better buys within 250 miles of Lakewood, NJ right now?

### 2. What Credits, Incentives, Tax Treatment, Or Rebates Are Available In April 2026?

Answer with citations and exact eligibility rules:

- Federal used clean vehicle credit: available or ended?
- Federal new clean vehicle credit: irrelevant to used purchase, but mention if there is any edge case.
- New Jersey EV incentives/rebates/sales-tax exemptions for used EVs in April 2026.
- Maryland/DC/Virginia dealer-side or registration incentives that could matter for an NJ buyer purchasing from a Maryland dealer.
- Utility, insurance, charging, toll, registration, or local incentives that matter for ownership cost.
- Whether any incentive requires the buyer to take delivery by a deadline, register in a specific state, or use a participating dealer.
- Whether any dealer fee or add-on could destroy eligibility if a credit exists.

### 3. Will Enhanced Autopilot Transfer And Retain Value?

This is the highest-risk non-price issue. The listing says Enhanced Autopilot, but buyer value depends on it remaining after ownership/Tesla-account transfer.

Research:

- Tesla policy and observed real-world behavior for Enhanced Autopilot and Full Self-Driving transfer on used Teslas sold by non-Tesla dealers.
- Difference between paid EAP/FSD attached to the vehicle, subscription status, trial status, and listing mistakes.
- How a buyer can verify the package before purchase: in-car screens, Tesla app/account, window sticker, service menu, software page, screenshots, dealer documentation, or Tesla support.
- Whether a dealer’s written statement is enough, or whether a screenshot from the car/account is needed.
- Whether Tesla can remove EAP/FSD after ownership transfer if it was listed by a third-party dealer.
- How much resale value EAP adds in practice in 2026, and whether buyers pay for it.

Deliver a yes/no gate: what exact proof must we get before relying on EAP value?

### 4. Battery, Warranty, And Mechanical Risk

For a 2020 Model 3 Standard Range Plus, determine:

- Original battery/drive-unit warranty length and mileage cap for this trim.
- Expected remaining battery/drive-unit warranty in April 2026 for VIN `5YJ3E1EA2LF805901`, assuming normal original in-service date patterns.
- Whether 2020 SR+ uses LFP or NCA/NMC chemistry in the US, and why that matters for longevity, charging habits, winter range, and resale.
- Expected real-world range today at 42,888 miles.
- How to estimate battery health before purchase: Tesla screen rated range, service mode, Recurrent report, Tessie/TeslaFi history, charging behavior, DC fast charge exposure, or dealer-provided data.
- Known 2020 Model 3 issues: control arms/suspension, water intrusion, cabin noise, heat pump absence, chrome/pre-refresh interior, charging port, 12V battery, tires, brakes, touchscreen/MCU, Autopilot hardware version.
- Recalls/open service campaigns to check by VIN.

### 5. Total Cost Of Ownership And Financing/Cash Tradeoff

Analyze likely ownership cost over 2 and 4 years:

- Insurance in NJ for a 2020 Model 3 SR+ versus Sonata/Elantra fallback.
- Tires, alignment, suspension, brakes, 12V/low-voltage battery, charging accessories.
- Home charging assumptions versus Supercharging.
- Depreciation and likely resale/trade-in after 2 years and 4 years.
- Cash purchase versus financing at Roadster’s illustrative terms (`$500` down, 84 months, 6.99% APR, `$346.59/month`).
- Whether buying a cheaper older SR+ is better than paying more for a newer 2021/2023 Tesla with LFP/heat pump/warranty advantages.

### 6. Resale Value And Exit Risk

Estimate realistic resale/trade-in/private-party value for `169193` after:

- 12 months / about 55k miles
- 24 months / about 65k miles
- 48 months / about 85k miles

Assess the effect of:

- 2020 pre-refresh status versus 2021+ refresh
- Standard Range Plus versus Long Range AWD
- Enhanced Autopilot if transferable
- Battery warranty remaining or expired
- Clean one-owner history
- EV market depreciation and Tesla price cuts
- Lack of federal used EV credit in 2026, if confirmed

Answer plainly: if the owner needs to resell quickly, how much downside risk is there?

### 7. Dealer / Contract / Fee Risk

Identify what to be careful with before clicking further in checkout:

- Mandatory add-ons, protection plans, ceramic coating, GAP, VSC, theft/etch, LoJack, reconditioning, delivery, or financing-only pricing.
- Whether Easterns’ `$799` processing fee is included in the displayed total and whether it affects any incentive calculation.
- Whether delivery to NJ changes total, registration, taxes, or return rights.
- Whether the 7-day return policy allows full unwind or only exchange/store credit; mileage/condition limits; delivery/pickup costs; credit/refund timing.
- Whether the 30 day / 1,000 mile warranty excludes EV battery/drive unit or only covers limited items.
- Whether “every car available at every location” means they can move it closer before purchase, after deposit, or only after paperwork.
- Whether deposit/order/checkout step is refundable.
- Whether final written buyer’s order must show no optional products and preserve the advertised price.

### 8. Should We Buy `169193`, Switch To A Different Easterns Tesla, Or Wait?

Compare `169193` with `169314`, `169302`, `168439`, and Automotive Avenues `61610A`.

Answer:

- Best buy if EAP transfers.
- Best buy if EAP does not transfer.
- Best buy if no federal/state credit exists.
- Best buy if the owner values Long Range AWD more than EAP.
- Best buy if resale protection is the top priority.
- Best buy if total cash outlay and downside risk are the top priority.

---

## Required Deliverables

Return a concise but evidence-rich memo with these sections:

1. **Recommendation:** Buy / buy only if specific gates pass / do not buy / switch target.
2. **Decision Matrix:** Score `169193`, `169314`, `169302`, `168439`, and `61610A` across price, software confidence, warranty/battery, resale, credit eligibility, and dealer risk.
3. **Credit/Incentive Finding:** Exact current federal/state/local credit status with citations. Explicitly state whether the April 2026 federal used clean vehicle credit is available or not.
4. **EAP Verification Standard:** Exact proof we must obtain before relying on Enhanced Autopilot value.
5. **Buyer’s Order Red Flags:** What line items/contract terms should stop the purchase.
6. **Max Price Guidance:** Recommended max all-in cash price for `169193` with EAP confirmed, and max all-in cash price if EAP does not transfer.
7. **Resale Outlook:** Expected resale/trade-in ranges at 1, 2, and 4 years, with assumptions.
8. **Final Questions For Dealer:** A short list of questions the buying agent should ask in writing. Keep this list minimal and decision-changing only.
9. **Citations:** Links and quotes/summaries for all credit rules, Tesla transfer-policy claims, market comps, warranty rules, and resale estimates.

Use confidence labels for each major finding: **High / Medium / Low**. If a source is forum-based or anecdotal, label it as such.

---

## Constraints And Safety Rules

- Do not contact Easterns, Automotive Avenues, Tesla, or any dealer/seller. Research only.
- Do not submit lead forms, credit forms, insurance forms, financing applications, deposits, or purchase commitments.
- Do not assume the `$4,000` used EV credit exists. Verify it first.
- Do not assume Enhanced Autopilot transfers just because a listing says it exists.
- Do not recommend relying on verbal dealer promises. Written confirmation or objective proof is required.
- Do not recommend a live call unless written channels fail and the lane is strong enough for the owner himself to call.
- Do not ignore the owner’s Tesla preference; weigh it explicitly against risk and resale.
- Do not over-optimize for theoretical resale if the current deal is genuinely under-market and usable.

---

## Useful Source Targets

Start with these source categories:

- IRS used clean vehicle credit page and dealer requirements page.
- Treasury / IRS FAQs on 2025 clean vehicle credit termination.
- New Jersey Treasury / MVC / Charge Up New Jersey / utility incentive pages.
- Tesla used vehicle warranty and Model 3 warranty documentation.
- Tesla account/software transfer discussions from Tesla official docs where available, plus Tesla Motors Club / Reddit / forums only as anecdotal support.
- Market listings from Cars.com, Autotrader, CarGurus, Edmunds, KBB, Tesla used inventory, Carfax, Recurrent.
- Model 3 known-issues resources from Tesla Motors Club, NHTSA recalls, CarComplaints, Consumer Reports, and reputable EV ownership guides.
- Easterns/Roadster page evidence for the specific VIN/stock, but treat dealer page data as provisional until confirmed in writing.

---

## Background Documents Included For Process Context

The standard external-research bundle includes the five persistent background documents below. They explain the owner’s personal secretary system and why this request is being delegated, but the vehicle decision must be answered from this directive and external automotive/tax sources.

1. `docs/research/background/01-system-overview.md`
2. `docs/research/background/02-architecture-infrastructure.md`
3. `docs/research/background/03-backend-engine.md`
4. `docs/research/background/04-integrations-dashboard.md`
5. `docs/research/background/05-current-state-roadmap.md`

---

## Expected Bottom Line

The output should let the buying agent answer this in plain English:

> “Given the real current credits, market price, EAP transfer risk, battery/warranty status, dealer fees, and resale outlook, should Eliyahu buy this exact Tesla today, and what must be true before we click further?”
