lakewoodphone/tesla-lin-chip/research/responses/019-tesla-purchase-due-diligence-synthesis.md

# Response Synthesis 019: Tesla Model 3 Purchase Due Diligence

**Date:** 2026-04-27
**Directive:** `docs/research/directives/019-tesla-purchase-due-diligence.md`
**External inputs reviewed:**

- `C:\Users\ezabz\Code\tutor\compass_artifact_wf-5a4e68c9-61a7-4bee-b768-043f58b753ec_text_markdown.md`
- `C:\Users\ezabz\Code\tutor\Tesla Model 3 Purchase Due Diligence.txt`

## Bottom Line

Do **not** buy Easterns stock `169193` at the current `$23,298` Roadster cash signal as a clean buy-now decision. Treat it as **conditional / negotiation only**.

Both external reports agree on the most important economics:

- The federal used clean vehicle credit is not available for an April 2026 purchase.
- New Jersey's ZEV sales-tax exemption is gone; expect full NJ sales tax.
- The car is a 2020 pre-refresh Model 3 SR+ with NCA battery chemistry and no heat pump.
- Enhanced Autopilot must be verified from the actual in-car Tesla software screens; dealer listing text is not enough.
- Mandatory add-ons, protection packages, duplicate fees, or vague return/warranty terms should kill the deal.

The reports differ on price tolerance. One says `169193` is an average/fair conditional buy up to roughly `$23,500` OTD if permanent EAP is verified and the buyer's order is clean. The stricter report says to switch targets unless Easterns drops the total to about `$21,800` and writes EAP/no-add-ons into the deal.

Given the owner's stated goal to buy this week without getting trapped, use the stricter operating rule:

> **Switch target by default. Keep `169193` alive only if Easterns confirms permanent EAP with screenshots, no add-ons, clean NJ OTD, and a materially better price.**

## New Decision Rule For `169193`

Proceed only if all gates pass:

1. **EAP proof:** timestamped in-car screenshot from this VIN showing `Enhanced Autopilot: Included Package` or equivalent permanent included-package language.
2. **No add-ons:** written buyer's order has only vehicle price, one doc/processing fee, NJ tax, title/registration/DMV, and no mandatory protection products.
3. **No credit assumption:** numbers must work without the federal `$4,000` used EV credit and without NJ sales-tax exemption.
4. **Battery/warranty proof:** original in-service date, remaining battery/drive-unit warranty, rated range at 100%, tread depth, and no obvious suspension/control-arm issue.
5. **Price:** target all-in cash price around `$21,800`; do not exceed the current `$23,298` signal without explicit owner approval after EAP proof and buyer's order review.

## Preferred Pivot

Search immediately for a better Tesla lane:

- 2021+ Model 3 Standard Range / SR+ with heat pump and preferably LFP battery.
- Clean title, no accidents, under roughly `$24k` list or under roughly `$26k` all-in.
- In-state NJ options preferred to reduce tax/title/friction and avoid Easterns return-policy risk.
- Explicit EAP/FSD is valuable, but 2021+ hardware/battery/warranty can outrank a 2020 EAP listing if the software is not proven.

The stricter report specifically mentions possible better in-state comps around Little Egg Harbor and Rockaway, NJ. These should be located and verified before committing to Easterns `169193`.

## Dealer Questions To Use If Keeping `169193` Alive

Keep the ask short and decision-changing:

1. Please send today's in-car screenshot for VIN `5YJ3E1EA2LF805901` at Controls > Software > Additional Vehicle Information showing whether Enhanced Autopilot is an included paid package.
2. Please send the itemized buyer's order to `08701`, with no protection packages, LoJack, ceramic, GAP, VSC, theft etch, reconditioning, or other mandatory add-ons.
3. Please confirm the original in-service date, remaining Tesla battery/drive-unit warranty, current tread depth, and rated range at 100% charge.
4. If the above is clean, what is the best all-in cash price? The current number only works for us if the software is proven and the contract is clean.

## Practical Recommendation

Do not click deeper into Roadster checkout, submit credit, upload ID, pay deposit, or commit funds on `169193` yet.

The next move is to pursue better 2021+ / in-state Tesla options while keeping Easterns warm as a fallback/negotiation lane. If Easterns responds with hard EAP proof and a clean buyer's order, then re-evaluate against live alternatives.
