lakewoodphone/tesla-lin-chip/research/responses/2026-05-18-urgent-tesla-lin-bench-mock-and-parts-research-ndate-2026-05-18-n-nwe-are-return-6242f52c.md

---
job_id: 6242f52c-723b-4e96-8ea3-65252ec0fc1a
directive_id: urgent-tesla-lin-bench-mock-and-parts-research-ndate-2026-05-18-n-nwe-are-return
title: Urgent Tesla LIN Bench Mock And Parts Research\nDate: 2026-05-18\n\nWe are returning a 2025 Tesla Model X today after passive steering-wheel LIN captures. We need to order parts so we can fully build the LIN interface and mock the LIN network on the bench without needing the Tesla back. Research practical orderable hardware and required pre-return vehicle measurements/data. Known facts: LIN bus 19200 bps; ID 0x0C/PID 0x4C; 8 data + enhanced checksum; vehicle low-voltage rail measured about 15.4V; white SW wire is LIN, green LV power, black ground; target MCU is Seeed XIAO ESP32-C3 3.3V UART; cheap TJA1021 TTL-UART-to-LIN module candidate exists on Amazon B0F31584W1; avoid CAN modules. Produce concise recommendations: parts to order, bench mock topology, what readings/captures/photos to take before vehicle leaves, and safety warnings. Prefer authoritative manufacturer/datasheet facts where possible.
domain: automotive_re
sensitivity: no_refusal_required
model_used: sonar-deep-research
provider: perplexity
status: complete
completed_at: 2026-05-18T17:37:14.435313+00:00
cost_usd: 0.4655
input_tokens: 376
output_tokens: 13309
reasoning_tokens: 60824
search_count: 30
citation_count: 29
verifier_status: passed
schema_version: 1
---

# Designing a Bench LIN Mock for a Tesla Steering-Wheel Network Using XIAO ESP32‑C3 and TJA1021‑Class Transceiver

Before the vehicle is returned, you have a narrow window to capture the electrical, protocol, and physical details required to reproduce the steering‑wheel LIN network on the bench. The goal is to use a Seeed XIAO ESP32‑C3 as a 3.3 V LIN master controller, a 12–15 V bench supply to emulate the vehicle low‑voltage rail, and an automotive‑grade LIN transceiver such as the NXP TJA1021 (or its pin‑compatible MC33662 family) as the LIN physical layer. The Tesla steering‑wheel module then operates on the bench as a LIN slave. The key findings are that the XIAO ESP32‑C3 provides a suitable 3.3 V UART and GPIO environment for a software LIN master implementation[1], the TJA1021‑class transceivers are explicitly specified as LIN 2.x/ISO 17987 compliant with up to 20 kBd speed, 12 V system operation, integrated slave termination, and 3.3 V compatible logic interfaces[2][11], and the LIN electrical topology requires a single‑wire bus with a defined master pull‑up network and per‑node 30 kΩ pull‑ups with a series diode for slaves[19][27][7]. To reconstruct the Tesla environment, you should measure the effective LV rail at the steering‑wheel module under operating conditions (you have already seen approximately 15.4 V), confirm that the LIN bus runs at 19.2 kbit/s (which is within the LIN‑legal 1–20 kbit/s range and a documented “fast” LIN rate[3][19]), record full frame traces (including break, sync 0x55, PID 0x4C, eight data bytes and enhanced checksum) for all relevant driver inputs, and document connector pinouts and module part numbers via high‑resolution photographs. With these data in hand, you can order a TJA1021 or MC33662‑based breakout, a suitable 12–15 V supply, protection components, and measurement tooling, and then build a safe bench topology where the XIAO ESP32‑C3 speaks LIN as master, the transceiver handles 12 V physical signaling, and the Tesla steering‑wheel electronics behave identically to in‑vehicle, all without needing further access to the car. Throughout, you should treat the steering‑wheel area as airbag‑adjacent, respect low‑voltage and ESD precautions, ensure you never back‑feed any Tesla wiring from the bench, and validate your bench setup incrementally with scoped waveforms before attempting full control of the module.

## Context and Objectives

The immediate practical objective is to continue work on a reverse‑engineered Tesla steering‑wheel LIN interface after the 2025 Model X leaves your possession. You have already performed passive captures on the steering‑wheel LIN bus, confirmed basic parameters for at least one frame of interest (19200 bps, ID 0x0C with protected ID 0x4C, eight data bytes plus enhanced checksum), and identified the low‑voltage wiring to the steering‑wheel electronics, where the white wire carries the LIN signal, the green wire is low‑voltage power, and the black wire is ground. The measured low‑voltage supply in the vehicle is approximately 15.4 V, consistent with a 12 V nominal automotive system under charge. The question now is how to translate these empirical observations into a self‑contained laboratory bench mock that lets you continue development, testing, and experimentation with the steering‑wheel module without the vehicle.

To achieve this, the bench environment must minimally replicate three aspects of the vehicle: the electrical supply conditions at the steering‑wheel module connector; the LIN physical‑layer characteristics, including idle and dominant voltages, slew rates, and termination; and the LIN protocol timing and content as seen by the module. For electrical supply, this means using a 12–15 V regulated bench source with adequate current capacity and proper over‑current protection. For the LIN physical layer, it implies using a dedicated LIN transceiver compliant with ISO 17987 / LIN 2.x, operating in a 12 V system, providing a bidirectional single‑wire interface and built‑in slave pull‑up, and translating between 12 V bus levels and 3.3 V logic suitable for the Seeed XIAO ESP32‑C3 microcontroller[2][11][19]. For protocol behavior, it requires implementing a LIN master schedule on the XIAO’s UART, generating correct breaks, sync bytes, protected IDs, and enhanced checksums, and matching the bus speed used in the vehicle[3][12][19].

In addition to identifying the correct bench topology, you must immediately decide what to measure, capture, and photograph in the time remaining with the car. This is critical because any ambiguity in wiring, missing message types, undocumented wake‑up behavior, or unmeasured supply properties could later block the bench reproduction. For example, LIN nodes can participate in sleep and wake‑up sequences, and the module’s wake behavior may depend on ignition state or CAN gateway messages. LIN frames are composed of a break field, a sync field 0x55, and a protected ID for the header, followed by a response of up to eight data bytes and a checksum, usually an enhanced checksum in LIN 2.x[12][19]. Confirming which IDs appear, at what cadence, and which data bits map to which steering‑wheel functions will determine how complete your bench mock can be.

The constraints on hardware selection are also clear. You have specified a Seeed XIAO ESP32‑C3 as the target MCU. This mini‑board integrates the Espressif ESP32‑C3 SoC with a 32‑bit RISC‑V core up to 160 MHz, on‑chip 400 KB SRAM, 4 MB flash, and Wi‑Fi/BLE radios[1]. It exposes one UART, one I²C, and one SPI along with 11 GPIO pins and several ADC channels[1]. Importantly, its logic domain is 3.3 V; the board’s 3.3 V pin can source up to approximately 700 mA from the onboard regulator, and the UART TX/RX pins are clearly marked (D6 as GPIO21 for TX, D7 as GPIO20 for RX)[1]. This makes it straightforward to drive a LIN transceiver whose digital pins are specified as compatible with both 3.3 V and 5 V logic[2][11]. You have also identified an inexpensive TJA1021‑based TTL‑to‑LIN module available via a retail marketplace; this is a reasonable candidate for the bench build as long as it uses an authentic, compliant transceiver and exposes TXD/RXD pins referenced to 3.3–5 V logic, plus LIN, VBAT, and ground.

Within this context, the report will first review the relevant aspects of LIN and the XIAO ESP32‑C3, then outline a robust bench topology, propose a concrete set of parts to order, specify the exact in‑vehicle measurements and captures you should prioritize before returning the Tesla, and conclude with safety guidance and a recommended validation sequence.

## Technical Background: LIN, Physical Layer, and Target Hardware

### LIN protocol and frame structure

The Local Interconnect Network (LIN) is a low‑cost automotive serial network standardized as ISO 17987 and described in detail by major semiconductor and test‑equipment manufacturers[19][27][12]. LIN was conceived as a complement to the higher‑performance CAN bus, targeting simple, low‑bandwidth, non‑safety‑critical functions such as door locks, seat controls, window lifts, and many steering‑wheel button assemblies. In such contexts, the cost of full CAN nodes would be prohibitive, whereas LIN can be implemented with a single wire, modest microcontrollers, and minimal transceiver circuitry. LIN uses a master‑slave topology in which there is exactly one master node and one or more slave nodes; the master arbitrates bus access by transmitting headers that grant each slave the opportunity to respond with data in predefined time windows[19][21].

At the logical level, a LIN frame is the basic unit of communication on the bus[12][19]. It comprises two major phases: the header, always transmitted by the master, and the response, transmitted by a slave or by a master’s own slave task, depending on message direction[12]. The header begins with a break field consisting of at least 13 dominant bits (logical zeros on the bus) followed by at least one recessive bit as a break delimiter[12]. This extended low interval serves as a clear start‑of‑frame marker that all nodes can detect, even with relaxed timing tolerances. After the break, the master transmits a synchronization field, defined as a single byte 0x55, whose pattern of alternating zeros and ones allows slave nodes to measure the bit timing and adjust their local baud‑rate generators[12][3]. Following the sync comes the identifier field, or ID, which is 6 bits wide and then combined with two parity bits to form an 8‑bit protected identifier (PID). The two parity bits, P0 and P1, are calculated from specific ID bits per the LIN specification to form a simple parity check that can detect certain bit errors in the ID field[12][19].

After the header is transmitted, the designated responder for that ID transmits the response field, consisting of a data payload of 1, 2, 4, or 8 bytes and a checksum byte[12][19]. LIN 2.x introduced the enhanced checksum, which covers the protected ID as well as the data bytes, whereas the earlier “classic” checksum covered only data bytes[12][16][19]. Enhanced checksums are now standard for all frames except a few legacy diagnostic frames. From the data you have, the frame of interest uses eight data bytes and an enhanced checksum, consistent with typical modern in‑vehicle LIN 2.x use[19][12]. LIN uses a UART‑compatible framing format at the bit level, specifically NRZ data, 8 data bits, no parity, and one stop bit (8N1), with a baud‑rate range typically from 9600 to 19200 bit/s[3]. Application notes show that LIN can tolerate up to around ±5 % deviation between nominal and actual baud rates due to the sync field’s periodic resynchronization[3].

Crucially for your bench mock, the master is responsible for the schedule that determines which IDs are transmitted and how often. Typical LIN masters periodically send headers for each “unconditional” frame in a schedule table, ensuring deterministic update rates for each signal[12][19]. The slave nodes do not spontaneously transmit; instead, they react when their configured IDs appear in a header. This design implies that to fully mock the Tesla steering‑wheel module on the bench, your XIAO ESP32‑C3 must reproduce the relevant headings for ID 0x0C (PID 0x4C) and any other IDs that the module expects, even if you only care about capturing responses from a subset of them. Understanding which IDs are present in the cluster, and which ones are critical for wake‑up, keep‑alive, or reporting, is therefore an important pre‑return data‑collection task.

### Physical layer and voltage levels

The LIN physical layer is defined around a single‑wire bus that carries both recessive and dominant states as analog voltage levels referenced to the system supply voltage and ground[19][27]. All nodes connect in parallel to the LIN line (often called LIN or BUS) and share a common supply voltage line, VBAT, typically 12 V in light vehicles or 24 V in heavy vehicles, plus a common ground. For 12 V LIN networks, the bus operates between ground and approximately VBAT, but the actual bus supply VSUP can deviate due to wiring drops and local regulation[19][27]. To maintain a defined idle state, nodes include pull‑up networks between LIN and VBAT. Inside each LIN node, the LIN and VBAT lines are usually connected by a relatively weak pull‑up resistor (around 30 kΩ) in series with a diode[19][27]. This arrangement ensures that if a node loses power, the diode prevents current back‑feeding from the LIN bus into the node’s VBAT domain, and the weak resistance prevents excessive current draw when multiple nodes are powered down[19]. In addition to these per‑node pull‑ups, the master node implements a stronger pull‑up, typically around 1 kΩ in series with a diode, from VBAT to LIN[19][7][27]. This strong pull‑up keeps the bus in a recessive high state when no node is driving a dominant low, improving noise immunity and guaranteeing that the recessive level is close to VBAT.

The key voltages defining logical states are asymmetric between transmitters and receivers, which is intentional to provide noise margins. In a 12 V LIN system, a transmitter must drive the bus low enough that the bus voltage is below approximately 20 % of VBAT to ensure a dominant logic 0 at the receiver, while a receiver must interpret a bus voltage below 40 % of VBAT as a dominant logic 0[27][19]. For recessive highs, a transmitter is expected to drive the bus above about 80 % of VBAT, while receivers must recognize anything above about 60 % of VBAT as a recessive logic 1[27][19]. For a nominal 12–15 V system, this means dominant lows on the order of a few volts above ground or less, and recessive highs approaching 9–12+ V, well above typical digital logic thresholds. Because of this wide swing and the need for robust EMI performance and ESD protection, LIN transceivers such as the NXP TJA1021 and NXP/Freescale MC33662 integrate level shifting, wave‑shaping, and protection structures, presenting 3.3/5 V‑compatible digital pins to the microcontroller while directly driving the single‑wire bus to 12 V levels[2][11][27].

The TJA1021, for example, is described as an interface between a LIN commander or responder protocol controller and the physical bus[2][2]. It is compliant with LIN 2.x and ISO 17987‑4:2016 for 12 V systems, supports baud rates up to 20 kBd in its /20 and B variants, and provides low electromagnetic emission and high immunity[2]. The transceiver’s TXD pin accepts the transmit data stream from the microcontroller, which is then converted into a bus signal with optimized slew rate and wave‑shaping driving the LIN output pin[2]. The RXD pin returns the received data back to the microcontroller, representing recessive bus levels as logic high and dominant bus levels as logic low[2]. NXP’s datasheet explicitly notes that the digital input levels are compatible with devices powered at 3.3 V and 5 V, eliminating the need for separate level‑shifting when interfacing with a 3.3 V MCU like the XIAO ESP32‑C3[2]. The MC33662 series, which is pin‑compatible with the TJA1021, similarly supports 12 V LIN 2.0/2.1/2.2/2.2A and provides digital inputs compatible with 3.3 V and 5.0 V without external components[11]. Both families incorporate integrated slave termination resistors and offer different variants optimized for 10.4 kBd or 20 kBd, aligning with the documented LIN range of 1–20 kbit/s and the typical common choices of 9.6, 10.4, and 19.2 kbit/s[11][3][19].

In terms of bus termination, authoritative notes from NI and TI clarify that LIN cables themselves require no external termination resistors, because each node is internally terminated at the transceiver[7][27]. In a slave node, the bus is typically pulled up from LIN to VSUP through the aforementioned 30 kΩ resistor and a series diode; this is usually integrated within the transceiver package[7][19][27]. The master node, however, requires an external network: a roughly 1 kΩ resistor and series diode between the LIN bus and VSUP, with this stronger pull‑up often selectively enabled in some lab equipment via software[7][19]. In practice, when you create a master node on the bench using a transceiver module, you either rely on the module to provide this master termination network or you attach your own 1 kΩ plus diode from your 12–15 V supply to the LIN line, carefully matching polarities and reference points per the transceiver data sheet and reference designs[2][11][27]. Since your target bench network will likely consist of one master (your bench MCU plus transceiver) and one Tesla steering‑wheel slave node, ensuring correct implementation of the master‑side pull‑up is critical to reproduce proper recessive voltages and bus idle behavior.

### The XIAO ESP32‑C3 as LIN master controller

The Seeed Studio XIAO ESP32‑C3 is a compact development board exposing the capabilities of the Espressif ESP32‑C3 SoC, which implements a RISC‑V 32‑bit single‑core CPU with a four‑stage pipeline up to 160 MHz[1]. The board provides 400 KB of SRAM and 4 MB of on‑chip flash in a 21 x 17.8 mm package, making it suitable for embedded and IoT applications. It supports IEEE 802.11 b/g/n Wi‑Fi and Bluetooth Low Energy 5.0, though these are not directly required for LIN interfacing. In terms of I/O, the XIAO ESP32‑C3 offers one UART, one I²C port, one SPI port, 11 multifunctional GPIOs that can serve as PWM outputs, and 4 ADC channels[1]. The board includes a linear (or switch‑mode, depending on revision) regulator providing 3.3 V to the ESP32‑C3 and to a 3V3_OUT pin, which Seeed documentation indicates can source up to around 700 mA for external circuits[1]. Power input can be through a 5 V VIN pin or via a single‑cell Li‑ion interface at around 3.7–3.8 V; the XIAO includes a charging circuit with typical charge currents of several hundred milliamps[1].

The relevant pins for your LIN application are the UART pins and general GPIOs, which must interface with the LIN transceiver’s TXD and RXD pins. The XIAO ESP32‑C3 maps its UART0 signals to D6 and D7, where D6 corresponds to GPIO21 / U0TXD (UART transmit) and D7 corresponds to GPIO20 / U0RXD (UART receive)[1]. These pins are brought out on the board edge and can be used with Arduino‑style “Serial1” or custom UART mappings in the ESP32 environment. On closely related Seeed XIAO ESP32‑S3 boards, documentation demonstrates how to configure additional hardware serial ports and remap their RX/TX pins using the HardwareSerial class, with examples showing mapping of TX to D6 and RX to D7, or mapping to other digital pins by specifying GPIO numbers[18]. Although that particular example concerns the ESP32‑S3 variant, the underlying approach of using the ESP32 family’s flexible UART pin routing remains applicable and is well supported in Espressif’s Arduino core.

Most importantly, the XIAO’s digital I/O is strictly 3.3 V tolerant. The board’s documentation identifies the 3V3_OUT pin as the regulated output and indicates that you can draw up to 700 mA from it, while cautioning that inputs and outputs are referenced to this 3.3 V domain[1]. This fits the TJA1021 and MC33662 families, which explicitly support 3.3 V compatible digital input thresholds[2][11]. This means that you can drive the transceiver’s TXD pin directly with the XIAO’s UART TX, and you can connect the RXD pin back to the XIAO’s UART RX, without additional level shifting, provided that both devices share a common logic ground. The XIAO’s 5 V VIN pin can be used purely to power its onboard 3.3 V regulator from USB or another 5 V source; it should not be tied directly to the vehicle’s 12–15 V rail, which must instead power the LIN transceiver’s VBAT pin and the Tesla steering‑wheel module. Using the XIAO as the LIN master’s protocol controller, you will generate LIN headers over the UART at 19200 bps, including software‑generated breaks and enhanced checksums, and rely on the TJA1021‑class transceiver to perform the analog interfacing to the 12–15 V LIN bus.

## Hardware Architecture for the Bench LIN Mock

### Choice and configuration of LIN transceiver

For a robust bench topology, the LIN transceiver must meet several criteria: it must be compliant with LIN 2.x and ISO 17987‑4 for 12 V systems, support 19.2 kbit/s operation, offer 3.3 V compatible digital interfaces, and handle common automotive conditions like load dump and ESD. The NXP TJA1021 series is a strong candidate, widely used in industry and well documented in its data sheet[2][2]. It is explicitly advertised as a LIN 2.x/ISO 17987‑4:2016 (12 V) and SAE J2602 compliant transceiver, with variants optimized up to 20 kBd baud rate, passive behavior when unpowered, very low electromagnetic emission, high electromagnetic immunity, and integrated termination resistor for LIN responder applications[2]. The TJA1021’s TXD input receives the microcontroller’s transmit data stream, turning it into single‑wire bus signaling with controlled slew rates on the LIN output, while the RXD output returns received data to the microcontroller, mapping recessive bus levels to logic high and dominant bus levels to logic low[2]. The device includes modes such as Normal, Sleep, and Standby, with very low current in Sleep and wake‑up detection via bus activity or local inputs[2]. For your bench mock, you will operate the transceiver in Normal mode most of the time, optionally exploring Sleep and Wake‑up behavior if the Tesla module expects certain wake sequences.

An alternative is the NXP/Freescale MC33662, whose data sheet emphasizes that it is suited for automotive bus systems and is compliant with LIN 1.3 through 2.2A, SAE J2602‑2, and ISO 17987‑4:2016 for 12 V[11]. It offers variants optimized for 20 kbit/s normal baud or specialized faster baud selections, includes active bus wave shaping, sustains high ESD levels on LIN, WAKE, and VSUP pins, provides high EMI immunity, and supports low standby current in Sleep mode[11]. Importantly, it notes that digital inputs are compatible with both 5.0 V and 3.3 V logic without external components, which reduces design complexity when using 3.3 V MCUs like the XIAO ESP32‑C3[11]. The MC33662 is pin‑to‑pin compatible with TJA1021, meaning that any breakout board or module designed for TJA1021 can often be re‑populated with MC33662 variants if necessary, although for your use a TJA1021‑based module is perfectly adequate as long as it is genuine.

In practice, you propose to use an off‑the‑shelf TTL‑to‑LIN module advertised as using the TJA1021. Such modules typically expose a VBAT pin (for 7–18 V supply), a LIN pin, a ground reference, and logic pins labeled TXD and RXD for UART interfacing. To integrate them into your bench setup, you will power VBAT from your 12–15 V bench supply (not from the XIAO), connect ground to the common ground shared with both the steering‑wheel module and the XIAO, connect LIN to the white wire that goes to the Tesla module’s LIN input, and wire TXD/RXD to the XIAO’s UART pins. You should verify, by referencing the module’s PCB or seller documentation, that the module is intended for 3.3–5 V logic; however, the underlying TJA1021/MC33662 digital levels are by design 3.3 V friendly[2][11], so if the module does not introduce incompatible level shifting, direct connection is safe.

An important configuration aspect concerns whether the module implements master‑side strong pull‑up termination. As discussed earlier, a LIN master needs an external 1 kΩ resistor and series diode between VSUP and LIN, whereas slaves rely on weaker 30 kΩ pull‑ups integrated in the transceiver[7][19][27]. Some lab‑oriented LIN interface boards expose a jumper or software setting to enable master termination, as seen in NI’s XNET LIN products, which allow the 1 kΩ pull‑up and diode to be enabled or disabled via software[7]. Many TJA1021 breakout modules targeted at Arduino or generic MCU usage hard‑wire the master termination network, thereby making them permanent masters. Others may be configured as either masters or slaves depending on link options. Because your bench network will contain only one master and one slave, and you are implementing the master yourself, it is acceptable and even preferable for your transceiver module to include the 1 kΩ plus diode between VBAT and LIN, so the Tesla module sees the expected bus idle voltage and bias.

### Power supply architecture and protection

The bench mock must replicate the electrical boundary conditions of the Tesla steering‑wheel LIN cluster, which in your observations features a low‑voltage rail around 15.4 V at the steering‑wheel module. This is consistent with a charging 12 V system, where alternator or DC‑DC converter outputs often sit between 13.5 and 15.5 V depending on temperature, state of charge, and load. LIN standards and transceiver data sheets typically specify an operating range for VBAT or VSUP from about 5.5 V up to 18 V, with transient handling for load dump and other conditions[2][11][27]. For example, the TJA1021 is specified for VBAT between 5.5 V and 18 V in normal operation, with typical datasheet curves given at VBAT = 12 V[2][2]. The MC33662 similarly supports 12 V LIN, handling up to 40 V during load dump and withstanding ESD surges of 15–25 kV on different pins[11]. In the bench, you do not need to reproduce extreme load‑dump conditions; instead, you want a stable, clean DC supply mimicking 12–15 V behavior.

To this end, an adjustable lab power supply that can output in the 12–16 V range with at least several amperes of current capability is ideal. High‑powered supplies based on 12 V server PSUs or commercial bench supplies can provide this, with some designs allowing software‑controlled adjustment of output voltage between 1 and 12 V[15]. For example, Power‑One FNP600 or FNP850 modules used in IT equipment provide 12 V output rails at tens of amperes and can be controlled via a microcontroller interface on a custom PCB that includes an MCU, display, and remote sense connections[15]. While you do not necessarily need such high current for a steering‑wheel module—which likely draws well under an ampere—you benefit from the robustness and stable regulation of these PSU‑based solutions. Alternatively, a conventional laboratory bench supply with adjustable output, foldback current limiting, and over‑voltage protection can be used. In all cases, your wiring between supply, transceiver module, and Tesla steering‑wheel module should be fused close to the supply, with a moderate fast‑acting automotive blade fuse (for example, 2–5 A) in series with the positive rail to mitigate the risk of a short in the module or wiring.

On the low‑voltage logic side, the XIAO ESP32‑C3 board must be powered at 5 V on its VIN pin or via USB; it includes its own regulator for 3.3 V[1]. That 3.3 V rail can be used to power any logic‑level accessories such as a logic analyzer input buffer or status LEDs, but it should not power the LIN transceiver’s VBAT pin, which must see 12–15 V. However, the transceiver’s digital supply is usually derived internally, and its TXD/RXD pins are referenced to its own ground and thresholded to tolerate 3.3 V logic directly without separate VDDIO rails[2][11]. Care must be taken that the transceiver module does not try to draw too much current from a 3.3 V logic reference pin; if it exposes a VCC pin labeled 3.3–5 V, that is typically a logic supply input or output for its onboard level‑shifting, not the 12 V VBAT for the bus. Therefore, you must carefully inspect the module’s documentation or PCB labeling to connect VBAT only to your 12–15 V bench rail and use the module’s VCC pin, if present, appropriately with the XIAO’s 3.3 V output.

Because LIN bus levels can swing close to the full automotive supply, and transceivers must handle large ESD discharge events[11][27], you should also practice ESD precautions in your lab when handling the Tesla steering‑wheel module unmounted from the vehicle. On the bench, the steering‑wheel module’s low‑voltage power pins should be connected to your bench supply with correct polarity, and the ground of this setup must be tied to the ground of the XIAO and the transceiver. Under no circumstances should the XIAO’s ground be left floating relative to the 12–15 V domain, because the TXD/RXD logic signaling then becomes undefined and may exceed device ratings. To further protect the XIAO from accidental exposure to the high‑voltage bus, you might interpose series resistors or opto‑isolated logic‑level conversion modules, though the core requirement for LIN is that the microcontroller does not directly see the 12–15 V bus.

### Bench network topology and terminations

On the bench, the LIN network topology will be simple: one master node composed of the XIAO ESP32‑C3 and the TJA1021‑class transceiver module, and one slave node composed of the Tesla steering‑wheel electronics that you have removed or reproduced. This is consistent with LIN’s design as a single‑master, multiple‑slave bus[19][3]. The physical wiring can be described as a three‑wire harness: LIN bus line, low‑voltage power supply (green wire in your vehicle), and ground (black wire). In the vehicle you have identified the white wire as LIN, green as LV power, and black as ground; these mappings must be rigorously documented through photos and continuity tests before the vehicle is returned, because they will govern how you wire your bench harness.

In terms of termination, you will rely on the master node’s strong pull‑up and the slave node’s internal termination. As TI and NI’s documentation indicates, LIN bus cables do not require additional external termination, because each node incorporates the necessary pull‑ups and the signalling is not differential but single‑ended to VBAT and ground[7][27]. The master’s 1 kΩ with diode network between LIN and VBAT ensures that the bus sits in a recessive high state when idle, while the slave’s weaker 30 kΩ plus diode feedback into VBAT prevents loading and back‑feeding[19][7][27]. Since TJA1021 and MC33662 transceivers for slave configurations often integrate this resistor, and board‑level master nodes implement the external strong network, you must verify whether your transceiver module includes the master network. If it does not, you can add a discrete 1 kΩ resistor and diode between your bench 12–15 V rail and the LIN line, oriented such that current flows from VBAT into LIN when the diode is forward‑biased, consistent with LIN reference designs[2][11][27]. The Tesla module should then behave as a normal slave, with its internal 30 kΩ plus diode providing additional but much smaller pull‑up strength.

The logical topology also requires that the master send headers at the correct baud rate and times. You already know that the bus speed is 19200 bps, which is within the typical upper end of the LIN range and supported by transceivers rated to 20 kBd[3][2][11][19]. ESP32’s UART hardware can be reliably configured for 19200 bps, 8N1 framing. Generating the LIN break field may require non‑standard UART usage, because a LIN break is longer than a normal start bit and involves at least 13 bit times of dominant low[12][3]. Common techniques include lowering the UART baud rate for a single 0x00 character to generate a long low pulse, then restoring the normal baud for sync and data, or directly driving the transceiver’s TXD line low via a GPIO for the appropriate duration outside of UART control. Application notes on LIN‑over‑USART demonstrate methods for automatic baud‑rate detection and break detection using timer capture units and interrupts[3], and similar techniques can be used on ESP32 if you wish to implement full LIN compliance. For your bench mock, where you are the only master and have a single known slave, a pragmatic solution is acceptable: generate a break with a TXD‑line‑low pulse of at least 13 bit periods at 19200 bps (which is about 676 microseconds), then send the standard 0x55 sync byte, protected ID 0x4C, and then read or write the eight data bytes and enhanced checksum.

The Tesla steering‑wheel module is likely passive in the sense that it does not drive the bus except when responding to polled IDs. This means your bench master must periodically send the header for ID 0x0C, and possibly others, to elicit responses and maintain module readiness. If the Tesla LIN cluster contains multiple nodes in the steering column in the real vehicle, you may need to emulate the presence or frames of other nodes to fully wake and operate the module you have removed. For example, if the module expects a certain wake‑up frame on another ID to transition out of Sleep, you will need to generate that on the bench as well. Consequently, your pre‑return captures should include power‑up sequences, sleep/wake cycles, and a log of all active LIN IDs on the bus, not just 0x0C, so that you can later emulate at least the subset that appears causally related to the steering‑wheel module’s behavior.

## Practical Parts Selection and Procurement Plan

### Core communication chain: MCU, transceiver, cabling

With the target topology defined, you can now identify specific categories of parts to order for the bench build. At the core is the communication chain: the Seeed XIAO ESP32‑C3 microcontroller board, the TJA1021‑class LIN transceiver module, and appropriate cabling and connectors to mate with the Tesla steering‑wheel module harness. Because you already own or have selected the XIAO ESP32‑C3, its specifications govern the logic domain and UART interface. As noted earlier, the XIAO provides a UART mapped by default to D6 (TX) and D7 (RX)[1], powered at 3.3 V from an onboard regulator that can source up to approximately 700 mA[1]. This is more than sufficient to power the digital side of a LIN transceiver module, which typically draws only a few mA for its digital control logic; the high‑current domain for the LIN bus is explained by the VBAT pin, powered from your 12–15 V bench supply[2][11].

The LIN transceiver module you referenced, a TJA1021‑based TTL‑to‑LIN adapter, should be chosen in a variant that exposes separate pins for the bus’s VBAT supply and the module’s logic interface (TXD/RXD/VCC). It is important to verify that the module is not designed as a USB LIN analyzer with isolated logic levels beyond your control, but rather as a simple breakout board for embedding in a microcontroller system. If the module expects a VCC of 3.3–5 V, you can drive that from the XIAO’s 3V3_OUT, while powering VBAT from the bench supply and sharing a common ground. The LIN pin then connects to the Tesla module’s LIN wire via a bench harness. To maintain flexibility and avoid permanently modifying the Tesla harness, you may wish to create a mating connector or pigtail using a salvaged Tesla steering‑wheel harness or an intermediate connector assembly that can be plugged into the back of the steering‑wheel module on the bench.

To complement the communication path, you will also want a USB isolation strategy or at least USB surge protection for the XIAO when used on the bench. Since the LIN bus sits at 12–15 V and can generate ESD or inductive spikes, grounding and shield routing must be carefully considered. However, because the TJA1021 and MC33662 families are designed to withstand up to 15–25 kV ESD on relevant pins and to survive load dumps up to 40 V[11][27], most of the harshness of the automotive environment is contained within the transceiver and the Tesla module. On the bench, your static environment is usually much more benign; nonetheless, following standard ESD handling and using a grounded wrist strap when touching the steering‑wheel module is prudent.

### Power, protection, and measurement accessories

A complete bench build needs more than just MCU and LIN transceiver. It must include a reliable power source, basic wiring protection, and measurement and analysis tools. For power, an adjustable DC bench supply set to around 14.5–15.0 V for nominal operation, with the ability to step down to 12.0–13.0 V for margin testing, matches your observed ~15.4 V in‑vehicle rail[27][19]. As long as the supply can provide a few amperes and has accurate current limiting, it will safely power both the Tesla steering‑wheel module and the LIN transceiver VBAT. While you could in theory adapt a high‑power server PSU as described in hobbyist projects that repurpose Power‑One FNP600/FNP850 modules with custom microcontroller control boards[15], a commercial bench supply with adjustable output, front‑panel current control, and clear numeric readouts is more straightforward. Alternatively, a 12 V automotive battery coupled with a DC‑DC converter to fine‑tune the voltage could be used, though at the cost of bulk and reduced control.

Protection devices should include an inline automotive fuse on the positive LV rail to the Tesla module, as well as optional resettable polyfuses on the transceiver’s VBAT input. The fuse rating must exceed the expected normal current of the steering‑wheel module (which you should measure in the vehicle with a DC clamp meter or by reading bench supply current once it is on the bench) but be low enough to blow quickly under short‑circuit conditions. A 2–5 A fast‑acting fuse is a reasonable starting point for a steering‑wheel module that likely draws less than an ampere. Additionally, simple transient voltage suppressor (TVS) diodes rated for automotive 12 V rails can be added across VBAT and ground near the module to clamp any unexpected spikes, though your controlled bench supply and the internal protection of both the Tesla module and transceiver should already mitigate most such risks.

Measurement tools are equally important. A basic digital multimeter is necessary to verify supply voltages, polarity, continuity, and fuse health. Automotive electronics tutorials highlight using a DMM in DC volts mode to verify constant and ignition‑switched 12 V rails, checking that the ignition line drops to 0 V when the vehicle is off[29]. In your context, the DMM will be used on the bench to confirm that your supply is at the intended 14–15 V, that the Tesla module’s power pins are wired correctly, and that the LIN bus idle voltage matches expectations (above about 60 % of VBAT)[19][27]. To analyze LIN waveforms and confirm protocol correctness, a logic analyzer or digital oscilloscope with LIN decode capability is strongly recommended. Vendors such as Tektronix offer protocol decode software for LIN that, in combination with an automotive trigger module, can transform an oscilloscope into a tool that captures and decodes LIN messages[22]. Setup typically involves connecting probes to the LIN line, configuring the bus type as LIN, and setting the bit rate to match the target bus, e.g., 19200 bps, after which the application can display decoded frames and their fields[22]. More compact tools like the Saleae logic analyzer also offer LIN protocol analyzers for digital captures[21]. Having at least one such tool on the bench will allow you to validate that the XIAO’s UART output indeed produces valid LIN breaks, sync bytes, IDs, data, and checksums as recognized by the Tesla module.

Finally, for reverse‑engineering and step‑by‑step control of vehicle LIN networks, there are specialized LIN bus daughter boards and analyzers that can sniff and replay LIN frames by connecting 12 V, ground, and the LIN signal wire to the device and then using PC software to monitor traffic in real time[8]. Demonstrations show using such boards in real vehicles to sniff LIN traffic, correlate frame IDs with actuator actions (like lights or washer systems), and then replay captured frames to control actuators[8]. While you already have some passive captures, ordering or re‑using such a tool could complement your XIAO‑based bench setup, especially if you later want to confirm that your bench environment conforms to actual in‑vehicle behavior.

The summary of core components for the bench could be expressed as follows:

| Subsystem | Example component | Key requirements and rationale |
|---|---|---|
| MCU and logic | Seeed Studio XIAO ESP32‑C3 | 3.3 V RISC‑V MCU with UART on D6/D7; provides 3.3 V logic supply and Wi‑Fi/BLE for future remote control or logging[1]. |
| LIN transceiver | TJA1021‑based TTL‑to‑LIN module or MC33662‑based breakout | LIN 2.x/ISO 17987 compliant, 12 V system, up to 20 kBd, integrated slave termination, 3.3 V compatible digital interfaces[2][11]. |
| Power supply | Adjustable DC bench supply, 0–20 V, ≥3 A | Emulates 12–15 V automotive rail; current limiting and numeric readout; optionally built using server PSU modules as in high‑power lab supply projects[15]. |
| Protection | Automotive fuse holder with 2–5 A blade fuses; optional TVS diodes | Limits fault current to Tesla module; clamps transients on VBAT; improves safety. |
| Measurement | Digital multimeter; logic analyzer or DSO with LIN decode | Verifies voltages and currents[29]; captures and decodes LIN waveforms at 19200 bps[22][21]. |
| Cabling and fixtures | Harness pigtails, breadboard or proto‑board, screw terminals | Provides robust connections between XIAO, transceiver module, power supply, and Tesla steering‑wheel module. |

This table is illustrative rather than exhaustive, but it encapsulates the main categories of hardware you should have in hand to continue your development without the vehicle available.

## Vehicle‑Side Data Collection Before Return

### Electrical measurements to replicate supply and loading

Before the vehicle leaves, you must capture electrical measurements that will allow you to accurately emulate the conditions at the steering‑wheel module on the bench. The first and most important measurement is the low‑voltage supply as it appears at the module. You have already measured roughly 15.4 V on the relevant green wire in at least one operating state; you should confirm whether this voltage changes with ignition state, drive state, HVAC load, or other factors. Using a DMM in DC volts mode, measure the voltage between the green wire (LV power) and black wire (ground) with the vehicle in several states: fully off (no key or card present), accessory mode, drive mode, and any specific mode in which steering‑wheel functions are heavily used. Car audio tutorials on DMM usage emphasize verifying that ignition‑switched wires drop to 0 V when the car is off, while constant wires remain at 12 V or above[29]. In your case, it is plausible that the steering‑wheel module is powered from a constant LV rail that remains live for monitoring, or from an ignition‑switched rail that goes off in deep sleep. Recording these behaviors will inform what you must do with your bench supply to reproduce module wake‑up and sleep cycles.

The second key electrical measurement is the LIN bus idle voltage and swing under normal operation. With the DMM or oscilloscope, measure the voltage of the white LIN wire relative to ground when the bus is idle (no visible activity, or at least between frames), and when the bus is active, capturing min and max voltages. LIN specifications and application notes suggest that recessive high levels should be above 60–80 % of VSUP, while dominant low levels should be below 20–40 % of VSUP[27][19]. Thus, in a 15.4 V system, you might expect recessive near 12–15 V and dominant near 0–5 V. Confirming these values in the Tesla environment ensures that your bench master with its transceiver and termination network is configured correctly. If your measured idle voltage is significantly lower than 60 % of VBAT, it might indicate additional loading, nonstandard termination, or measurement error; replicating such conditions on the bench could require adjusting your pull‑up network.

Third, if time and access allow, measure the steering‑wheel module’s current consumption under typical and peak loads. This could be done with an inline current measurement using a clamp meter around the green wire or by inserting a calibrated shunt resistor and measuring voltage drop. Even an approximate number will help you select appropriate bench fuses and confirm that your bench supply’s current limit setpoint is above normal consumption. If the module draws, for example, 0.1 A at idle and 0.3 A with all buttons active and backlighting on, a 1 A limit would be sufficient. If it draws more, you will adjust accordingly. Having these current profiles will also allow you to detect abnormal behavior on the bench, where an unexpectedly high current draw could signal miswiring or internal module faults.

### Protocol captures and semantic labelling

Your earlier work includes passive steering‑wheel LIN captures, but to build a fully functional bench mock you should extend and structure these captures carefully. The protocol documentation from NI and others makes clear that every LIN frame on the bus starts with a break field, followed by sync 0x55, and an ID field that is combined with parity bits to form a protected ID[12][19]. The ID’s lower six bits represent the raw message ID, while the upper two bits carry parity. In your case, you have confirmed an ID 0x0C with PID 0x4C, which is consistent with the LIN parity algorithm. Each response for ID 0x0C consists of 8 data bytes and an enhanced checksum that covers the protected ID and these data bytes[12][19]. Tools like online checksum calculators can be used later to validate captured data[16].

On the vehicle, you should capture sequences of frames around specific driver actions. For instance, press each steering‑wheel button individually and record the corresponding LIN traffic. Reverse‑engineering tutorials for LIN networks in real vehicles demonstrate how to enter sniffing mode on a LIN analyzer, capture all frames, then correlate frame IDs and data bytes with actuator actions like turning lights on or off or triggering the washer pump[8]. The same principle applies here: you want to know which bits or bytes in the ID 0x0C frame change when, for example, you press the left turn signal, the right turn signal, flash high beams, adjust wipers, navigate menus, use scroll wheels, etc. For each such action, record not only the changed bytes but also the context: which ID responded, whether the frame is initiated by the master at fixed intervals or in response to CAN commands, and how long the change persists. You should also log baseline traffic with no button activity, to see which frames are periodic “keep‑alive” or status frames and which are event‑driven.

In addition to ID 0x0C, scan for other LIN IDs in use on the same bus. A complete view of the bus can reveal whether the steering‑wheel module also participates in other frames as publisher or subscriber, including possible diagnostics or configuration frames. The NI description of LIN frames refers to various frame types, including unconditional frames (normal periodic data), sporadic frames (master‑to‑slave data when needed), event‑triggered frames (where multiple slaves can respond), diagnostic frames, and reserved frames[19]. While Tesla’s implementation details are proprietary, patterns in the traffic can show whether your module expects other IDs or whether ID 0x0C is its sole communication path. Capturing several minutes of traffic during typical use, then decoding and grouping frames by ID, will let you see update intervals, frame lengths, and response behavior. Logic analyzers such as Saleae’s can decode LIN frames after you specify the bit rate and identify the break and sync fields[21]. Tektronix’s CAN/LIN decode software for DSOs similarly allows capturing and decoding LIN packets by configuring the channel source, bus type, and bit rate, then running a measurement that displays decoded frame details[22]. Use whichever tool you have on hand to annotate your captures in real time or saved offline.

Semantic labelling is just as important as raw binary data. For each captured frame type of interest, note the mapping between byte and bit positions and specific controls. For example, “byte 3 bit 2 goes high when left turn signal is latched on,” or “byte 1 increments as a counter each frame, regardless of button state.” You can use this mapping later to build a bench control interface where you or your software can interpret the steering‑wheel module’s responses. If time is limited, prioritize mapping all safety‑related and critical user‑interface functions (turn signals, high beam, wipers) before mapping infotainment controls.

### Physical documentation: connectors, harness, and module metadata

Finally, you should thoroughly document the physical layer of the steering‑wheel module and its connections. This includes taking high‑resolution photographs of the steering‑wheel module from all angles, with particular focus on the low‑voltage connector, pin labels, and any embossed or printed part numbers, QR codes, or barcodes. These identifiers can later be cross‑referenced with online parts databases or service documentation to find additional information about the module’s expected environment. Tesla’s own service manuals for other components, such as the high‑voltage controller, emphasize the importance of correctly handling wiring harnesses, connector levers, and ground straps, and of noting that some connectors have very little slack[17]. While the steering‑wheel module is low‑voltage, the same principle applies: improper handling of its harness or connectors may damage delicate pins or strain limited wire slack, so thorough documentation reduces the need for rework.

You should also capture clear images or hand sketches of the connector pinout, including which pin corresponds to the white LIN wire, the green LV power wire, and the black ground wire. If possible, identify any additional pins that may carry other signals, such as wake lines, diagnostics, or redundant grounds. Use a DMM in continuity mode to map the harness wires to connector pins and confirm color‑to‑pin mapping. It is advisable to mark the harness and module with non‑destructive tags or labels that indicate orientation and pin numbering. Once the vehicle is gone, these physical references will be your only guide when wiring the module on the bench.

Because Tesla vehicles often integrate multiple functions in single assemblies and may share or repurpose harnesses, documenting the relationships between steering‑wheel LIN wiring and the rest of the vehicle harness is also helpful. For example, some enthusiasts have documented connecting Model S steering‑wheel panels on a workbench and querying specific sub‑panels over LIN at particular IDs (such as ID 0x4C) based on harness reverse‑engineering[9]. They observe that certain control panels are simple resistor matrices while others (such as gear selectors) use more complex hall effect sensing and LIN communication[9]. This illustrates that even within the steering‑wheel area, different components may have very different electrical interfaces. For your Model X steering‑wheel module, your earlier identification of the white/green/black wires as LIN, LV power, and ground respectively should be complemented by confirming whether any other wires are present, whether they carry CAN, discrete signals, or additional power rails, and whether they must be connected for the LIN module to operate normally.

## Safety, Risk Management, and Validation Strategy

### Low‑voltage and airbag‑related precautions

Working in the steering‑wheel area of a modern vehicle entails safety risks beyond those of ordinary low‑voltage electronics because of the presence of airbags and the proximity of steering controls to critical driving functions. Airbag systems store significant energy in capacitors and pyrotechnic actuators, and accidental deployment can cause serious injury. While your work has focused on the low‑voltage LIN wiring for the steering‑wheel controls, the general rule in automotive service manuals is to adhere to all safety procedures for nearby systems and to disconnect and wait an appropriate time after power removal before working on airbag‑related components[17]. Tesla’s own high‑voltage controller service procedures emphasize that only technicians trained in high‑voltage awareness and wearing appropriate PPE should handle high‑voltage components, and that connectors often have little slack, requiring careful manipulation[17]. Although your steering‑wheel work does not directly involve the high‑voltage battery, these cautions underscore the need for methodical, cautious handling.

On the bench, the main hazard is low‑voltage shock and fire. A 12–15 V rail, even if not usually lethal, can source considerable current from a bench supply or automotive battery and can cause wire overheating, connector melting, or fire if miswired. Therefore, fusing the positive LV line to the Tesla steering‑wheel module is essential, and verifying correct wiring with a DMM before energizing the system is prudent. Additionally, the XIAO ESP32‑C3’s inputs are rated for 3.3 V; connecting them directly to the 12–15 V rail, even through moderate resistance, can damage the microcontroller. Discussions on electronics forums emphasize that although series resistors can limit current into protection diodes on MCU pins, they do not substitute for proper voltage regulation or division when interfacing to higher voltages[25]. For logic input sensing, voltage dividers or dedicated regulators are required to reduce 12 V signals down to within 3.3 V limits, while power supplies for 3.3 V rails must be handled by integrated regulators[25]. In your LIN setup, you avoid this issue by never letting the XIAO see the 12–15 V bus directly; all interface is through the TJA1021‑class transceiver, with its digital pins staying within safe logic levels[2][11].

ESD handling is another relevant safety concern. LIN transceivers and automotive modules are hardened against ESD and EMI, with MC33662 advertising ESD immunity of at least 15 kV on LIN, 20 kV on WAKE, and 25 kV on VSUP pins[11]. Nevertheless, small steering‑wheel sub‑PCBs, MCU pins, and connectors may not share the same level of robustness. On the bench, you should discharge yourself, use grounded work surfaces if possible, and avoid touching exposed component leads except when unavoidable. When connecting and disconnecting the Tesla module from the bench supply, always power down first, and never hot‑plug if you suspect the module’s connectors are not designed for live insertion.

### Bring‑up and validation on the bench

Once you have the Tesla steering‑wheel module on the bench, the XIAO ESP32‑C3 wired to the TJA1021‑class transceiver module, and your 12–15 V supply connected through fuses and a power switch, you should proceed with a cautious bring‑up sequence. Initially, power the XIAO from USB only, leaving the 12–15 V supply off. Verify that the XIAO boots, that serial communication from your development PC to the board works, and that you can toggle its UART TXD pin and read from its RXD pin in a loopback configuration. Then, with the LIN transceiver module connected to the XIAO and ground shared, but with the Tesla module still disconnected, power VBAT on the transceiver from your bench 12–15 V supply. Use your logic analyzer or DSO to probe the transceiver’s LIN pin and verify that, with no Tesla module attached, the bus sits at a recessive high level close to VBAT, as expected from the master’s 1 kΩ plus diode pull‑up network[19][7][27]. If the bus idle voltage is significantly lower than VBAT, inspect your termination network and module configuration.

Next, implement a minimal LIN master routine on the XIAO. This routine should generate a periodic frame with the correct bit rate and structure: a break (13+ bit times of dominant low), a sync byte 0x55, and the protected ID 0x4C, followed by dummy data bytes and a correct enhanced checksum[12][3][16]. Calculate the checksum using LIN formulas or an online calculator[16], ensuring compatibility with LIN 2.x. With the Tesla module still disconnected, observe the LIN waveform on your scope and confirm that the timing and voltage levels match expectations for a LIN master: clearly discernible break, correct 0x55 pattern, and eight data bytes plus checksum at 19200 bps. Oscilloscope decode packages like Tektronix’s TDSVNM show how to configure the instrument to interpret LIN bit streams and display decoded fields based on user‑specified bit rates and thresholds[22]. Use such tools if available to ensure your master implementation is syntactically correct before introducing the Tesla module.

Once you are confident in your master’s behavior, power down the bench, connect the Tesla steering‑wheel module’s LIN, LV power, and ground to the transceiver and bench supply, double‑check polarity and continuity, and then bring the system up again. Initially, run the master at a very low polling rate, sending only periodic ID 0x0C headers and watching for any responses from the Tesla module on the LIN line. The presence of any valid response with the correct data and checksum is a strong indicator that your supply, wiring, and transceiver are correctly configured. From there, you can start sending simulated button‑press sequences or interrogating the module based on your in‑vehicle captures. Specialized LIN data loggers and analyzers show that once the LIN speed, activation frames, and IDs are correctly specified, replaying captured frames on a bench or off‑vehicle node can reliably reproduce actuator behavior[8][20]. You will be applying the same principle, but with a custom MCU‑based master instead of a commercial analyzer.

Throughout this process, keep a log of each configuration change and result. If the Tesla module fails to respond, consider whether in‑vehicle there were additional wake‑up sequences, such as CAN messages or other LIN IDs, that preceded module activity. The LIN specification includes Sleep and Wake‑up behavior whereby a node can be driven into low‑power mode and then woken by a specific bus pattern or wake pin signal[19][27]. If your earlier captures included power‑up sequences, you can replicate those on the bench, sending any observed pre‑0x0C frames at startup to coax the module into an active state. In the absence of such details, methodical experimentation, guided by your captures, will eventually reveal the minimal necessary handshake.

## Conclusion

For your purposes—continuing Tesla steering‑wheel LIN reverse‑engineering work without the vehicle—it is both feasible and practical to construct a bench LIN mock centered on a Seeed XIAO ESP32‑C3 and an automotive‑grade LIN transceiver such as NXP’s TJA1021 or the pin‑compatible MC33662. The XIAO provides a capable 3.3 V microcontroller with a hardware UART and GPIOs suitable for implementing a software LIN master, while the TJA1021‑class transceiver translates between the XIAO’s logic levels and the 12–15 V single‑wire LIN bus used by the Tesla module[1][2][11]. By powering the transceiver and the steering‑wheel module from a regulated 12–15 V bench supply, using appropriate fusing and protection, and ensuring correct termination (master 1 kΩ plus diode pull‑up and integrated slave 30 kΩ pull‑ups in each node), you can faithfully recreate the electrical environment prescribed by the LIN specification and observed in the vehicle[19][27][7].

Before returning the vehicle, it is essential to collect a comprehensive set of measurements and observations. These include verifying the low‑voltage supply behavior at the steering‑wheel module under various vehicle states, confirming LIN idle and dominant voltage levels, and measuring approximate current draw of the module to guide bench fuse selection. Equally crucial are detailed protocol captures for all relevant LIN IDs—especially ID 0x0C with protected ID 0x4C at 19200 bps—and semantic mapping of data bytes to driver actions, following techniques demonstrated in LIN tutorials where sniffed frames are correlated with actuator changes and then replayed[8][12][19]. Finally, thorough physical documentation of the module, connectors, harness, and wire color‑to‑pin assignments through photographs and continuity tests will prevent wiring ambiguities on the bench.

Once these data are secured and suitable parts are ordered—XIAO ESP32‑C3, TJA1021‑class transceiver module, adjustable 12–15 V bench supply, fuses, DMM, and ideally a logic analyzer or DSO with LIN decode—you can bring up the bench environment incrementally. Start by validating the XIAO and transceiver behavior in isolation, then introduce the Tesla module under controlled conditions, always respecting low‑voltage safety and ESD precautions. The rich body of LIN documentation from semiconductor vendors and test‑equipment manufacturers provides a solid reference for expected electrical and protocol behavior at each step[2][11][19][27][12]. With this approach, you will be able to continue decoding, simulating, and ultimately controlling the steering‑wheel LIN module entirely off‑vehicle, preserving development momentum long after the 2025 Model X has been returned.

## Citations

1. https://wiki.seeedstudio.com/XIAO_ESP32C3_Getting_Started/ - https://wiki.seeedstudio.com/XIAO_ESP32C3_Getting_Started/
2. https://www.nxp.com/docs/en/data-sheet/TJA1021.pdf - https://www.nxp.com/docs/en/data-sheet/TJA1021.pdf
3. https://www.infineon.com/dgdl/Infineon-AN205324_FR_CY91460_LIN-USART-ApplicationNotes-v03_00-EN.pdf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 - https://www.infineon.com/dgdl/Infineon-AN205324_FR_CY91460_LIN-USART-ApplicationNotes-v03_00-EN.pdf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
4. https://teslamotorsclub.com/tmc/threads/downgrading-headlights-how-do-i-read-lin-signals.253307/page-2 - https://teslamotorsclub.com/tmc/threads/downgrading-headlights-how-do-i-read-lin-signals.253307/page-2
5. https://www.youtube.com/watch?v=rXAZBHpzm8g - https://www.youtube.com/watch?v=rXAZBHpzm8g
6. https://www.mouser.com/c/semiconductors/interface-ics/lin-transceivers/?series=TJA1021 - https://www.mouser.com/c/semiconductors/interface-ics/lin-transceivers/?series=TJA1021
7. https://www.ni.com/docs/en-US/bundle/trc-8546-getting-started/page/termination-resistors.html - https://www.ni.com/docs/en-US/bundle/trc-8546-getting-started/page/termination-resistors.html
8. https://www.youtube.com/watch?v=lMymTyLS0mo - https://www.youtube.com/watch?v=lMymTyLS0mo
9. https://teslamotorsclub.com/tmc/threads/work-in-progress-stalks-on-2021-model-s-and-optional-round-y-wheel.242853/page-23 - https://teslamotorsclub.com/tmc/threads/work-in-progress-stalks-on-2021-model-s-and-optional-round-y-wheel.242853/page-23
10. https://www.aliexpress.com/i/1005005772796484.html - https://www.aliexpress.com/i/1005005772796484.html
11. https://www.nxp.com/docs/en/data-sheet/MC33662.pdf - https://www.nxp.com/docs/en/data-sheet/MC33662.pdf
12. https://www.ni.com/docs/en-US/bundle/ni-xnet/page/lin-frame-format.html - https://www.ni.com/docs/en-US/bundle/ni-xnet/page/lin-frame-format.html
13. https://keenlab.tencent.com/en/whitepapers/Experimental_Security_Research_of_Tesla_Autopilot.pdf - https://keenlab.tencent.com/en/whitepapers/Experimental_Security_Research_of_Tesla_Autopilot.pdf
14. https://forum.arduino.cc/t/arduino-lin-using-software-serial/1082451 - https://forum.arduino.cc/t/arduino-lin-using-software-serial/1082451
15. https://www.mattmillman.com/projects/building-an-extremely-high-powered-1-12v-lab-power-supply-on-the-cheap/ - https://www.mattmillman.com/projects/building-an-extremely-high-powered-1-12v-lab-power-supply-on-the-cheap/
16. https://linchecksumcalculator.machsystems.cz - https://linchecksumcalculator.machsystems.cz
17. https://service.tesla.com/docs/ModelX/ServiceManual/Palladium/en-us/GUID-70A86EC2-4187-4152-BD2F-11982A234CD4.html - https://service.tesla.com/docs/ModelX/ServiceManual/Palladium/en-us/GUID-70A86EC2-4187-4152-BD2F-11982A234CD4.html
18. https://wiki.seeedstudio.com/xiao_esp32s3_pin_multiplexing/ - https://wiki.seeedstudio.com/xiao_esp32s3_pin_multiplexing/
19. https://www.csselectronics.com/pages/lin-bus-protocol-intro-basics - https://www.csselectronics.com/pages/lin-bus-protocol-intro-basics
20. https://www.csselectronics.com/pages/lin-bus-data-logger - https://www.csselectronics.com/pages/lin-bus-data-logger
21. https://www.saleae.com/support/protocol-analyzers/learn-digital-protocols/local-interconnect-network-lin - https://www.saleae.com/support/protocol-analyzers/learn-digital-protocols/local-interconnect-network-lin
22. https://download.tek.com/manual/TDSVNMReference.pdf - https://download.tek.com/manual/TDSVNMReference.pdf
23. https://www.linengineering.com/resources/wiring-diagrams - https://www.linengineering.com/resources/wiring-diagrams
24. https://store.diagnosticinnovations.com/usblink.aspx - https://store.diagnosticinnovations.com/usblink.aspx
25. https://forum.arduino.cc/t/reducing-12v-to-3-3v/432339 - https://forum.arduino.cc/t/reducing-12v-to-3-3v/432339
26. https://forum.arduino.cc/t/voltage-sensor-analog-with-esp32/953852 - https://forum.arduino.cc/t/voltage-sensor-analog-with-esp32/953852
27. https://www.ti.com/lit/pdf/slla383 - https://www.ti.com/lit/pdf/slla383
28. https://www.youtube.com/watch?v=BeZd4gBuL28 - https://www.youtube.com/watch?v=BeZd4gBuL28
29. https://www.youtube.com/watch?v=929Qb7sGk50 - https://www.youtube.com/watch?v=929Qb7sGk50
