lakewoodphone/tesla-lin-chip/research/responses/2026-05-29-authoritative-datasheet-check-dual-lin-ble-rev-a-bom-9abd3f3b.md

---
job_id: 9abd3f3b-c9d8-4b4e-b46f-d6b5c2a621d7
directive_id: authoritative-datasheet-check-dual-lin-ble-rev-a-bom
title: Authoritative Datasheet Check: Dual-LIN + BLE Rev A BOM
domain: automotive_re
sensitivity: no_refusal_required
model_used: sonar-deep-research
provider: perplexity
status: complete
completed_at: 2026-05-29T17:16:04.490096+00:00
cost_usd: 0.3844
input_tokens: 993
output_tokens: 12723
reasoning_tokens: 40703
search_count: 30
citation_count: 24
verifier_status: passed
schema_version: 1
---

# Dual-LIN + BLE Rev A Passthrough Board: Authoritative Part Selection and Compatibility Validation

The most appropriate architecture for your Rev A dual‑LIN plus BLE passthrough/proxy board is to use an ESP32‑S3 module as the primary central controller with secure boot and flash encryption, paired with two NXP TJA1021T/20 LIN transceivers that are explicitly specified as 3.3 V‑logic compatible, while keeping a Nordic nRF5340 module and an alternative LIN transceiver as fallbacks. Based on current datasheets and distributor information, the recommended primary module is **ESP32‑S3‑WROOM‑1U‑N8R8** for its external antenna flexibility, 8 MB flash, 8 MB PSRAM, three hardware UARTs, and full ESP32‑S3 security feature set, and the recommended primary LIN transceiver is **TJA1021T/20** in SO‑8 package, which directly interfaces to 3.3 V TXD/RXD logic and supports LIN 2.1 / SAE J2602 at 19.2 kbit/s with automotive qualification.[1][13][16][16] A practical backup controller is the **Raytac MDBT53‑P1M** module based on Nordic nRF5340, and a practical backup LIN transceiver is **TPIC1021D** from Texas Instruments, which is likewise designed for 3.3 V or 5 V microcontroller I/O.[4][4][21][21] For Rev A in a metal‑heavy steering‑wheel environment, a **U.FL external antenna module is preferred** over a PCB antenna to get the radiator outside the shielded cavity.[1][20] With the chosen TJA1021‑class LIN interface, no routine level shifting is required between the 3.3 V MCU and the LIN transceivers; the BOM can remain compact and the security and boot chain can be implemented via ESP‑IDF with production‑grade flash encryption and secure boot.[11][12]  

The remainder of this report is intentionally expansive and structured in two analysis tracks, aligning with your “Compass” (datasheet/security/manufacturing correctness) and “Gemini” (cost, stock, ordering practicality) concerns, to ensure that hidden incompatibilities are surfaced before you lock Rev A.

---

## 1. System Architecture Overview and Constraints

### 1.1 Functional role of the Rev A board in the vehicle

The target PCB is intended as a cut‑wire passthrough/proxy in the steering wheel harness of a Tesla Model 3/Y, with the core function of transparently bridging and manipulating two separate LIN channels while being controllable over BLE. In such an in‑line deployment, the board must coexist with the existing vehicle nodes on each LIN bus and respect OEM timing, wake‑up, and fault‑handling behavior, while introducing minimal additional bus loading.[9][16] Because the board will physically sit inside the steering wheel or closely adjacent in the column area, there is a strong likelihood of a local metal enclosure, airbag housing, and wiring harness shielding that will impact RF performance and thermal environment.  

At a high level, the design decomposes into three subsystems. The first subsystem is the BLE‑capable microcontroller module that runs your custom firmware, manages BLE connections for user interaction or OTA provisioning, and translates between BLE and LIN traffic. The second subsystem comprises two LIN physical layer transceivers which adapt between 12 V automotive LIN bus voltages and the 3.3 V logic domain of the MCU. The third subsystem is the power and protection front‑end that accepts nominal 12 V automotive battery supply with transient conditions and provides a regulated 3.3 V rail for the module and logic, alongside ESD and surge protection and any watchdog or wake‑line gating.  

Given the safety‑critical environment near the steering wheel and the possibility that the board might be regarded as a quasi‑permanent accessory, the design must be conservative with respect to electrical overstress, EMC, and unintentional interference with OEM controls. This motivates choosing LIN transceivers with automotive‑grade ratings and robust protection features and an MCU module with a mature security story, including secure boot, flash encryption, and binding/activation mechanisms as requested.[11][16][6]  

### 1.2 Why LIN transceiver choice and logic‑level compatibility are critical

Your earlier research highlighted Microchip’s MCP2003‑E/SN as a compellingly cheap LIN transceiver and raised the question of whether it and competing devices can safely interface directly to a 3.3 V logic MCU without level shifting. This is not a trivial detail, because many legacy LIN transceivers assume a 5 V logic domain for TXD and RXD signals, even when they are logically compatible with 3.3 V MCUs under some conditions.[8][19] If the input high threshold \(V_{IH}\) for TXD is near or above 0.7 × VDD for a 5 V device, a 3.3 V logic high may not reliably register, especially over temperature and production spread. Running such a device out of spec may work in a lab but is inappropriate in a production‑quality automotive environment.  

The goal for Rev A is to avoid level shifters if possible, not only to save BOM cost and board area, but also to simplify timing and failure‑mode analysis. Therefore it is important to focus on LIN transceivers whose datasheets explicitly state compatibility with 3.3 V logic levels on TXD and RXD, or which include an internal regulator that sets the logic interface supply to 3.3 V. NXP’s TJA1021 family and Texas Instruments’ TPIC1021 are examples of devices that clearly state compatibility with both 3.3 V and 5 V microcontroller logic levels.[7][16][21][21]  

In contrast, some devices, including traditional MCP2003 family members, are nominally 5 V devices without explicit 3.3 V logic guarantees, even if some application notes or forums describe successful use with 3.3 V MCUs.[8][19][22] For a project constrained by space and cost but still aiming at robustness, selecting a LIN transceiver that unambiguously supports 3.3 V logic is safer than relying on informal experience.

### 1.3 BLE MCU module roles and security expectations

The central BLE MCU module must not only provide BLE connectivity and adequate compute resources for protocol handling, but also support a credible secure boot and OTA story consistent with modern embedded security expectations. Espressif’s ESP32‑S3 series is attractive in that regard, as it provides dual‑core Xtensa LX7 up to 240 MHz, integrated 2.4 GHz Wi‑Fi and Bluetooth LE 5, up to 16 MB external flash, and hardware support for flash encryption and secure boot with key storage in eFuses.[1][11][1] Espressif’s documentation emphasizes that flash encryption is intended to protect off‑chip flash contents and can be configured in both development and production modes, with keys burned into eFuse one time to prevent rollback to plaintext flashing.[11]  

You also requested that firmware updates be signed and that activation/binding be possible. The ESP32‑S3 ecosystem, using ESP‑IDF, supports secure boot v2 with signature verification of bootloader and application images and has well‑documented mechanisms for provisioning and managing keys.[11][12] This makes the ESP32‑S3 a strong primary choice. Nordic’s nRF5340, as used in the Raytac MDBT53‑P1M and Ezurio BL5340 modules, also offers dual‑core architecture with an application and network core, and a Bluetooth 5.2/5.4‑capable stack with strong security primitives suitable as a backup if the ESP32‑S3 route is blocked by supply or integration constraints.[4][5][4]  

In summary, before we consider cost and availability, the architecture points strongly toward an ESP32‑S3‑based module paired with LIN transceivers that explicitly permit 3.3 V logic operation, all powered from a protected 12 V input via appropriate regulators.

---

## 2. Compass Track: Datasheet‑Level Validation of Central Modules

### 2.1 ESP32‑S3‑WROOM‑1 and 1U families: capabilities and orderable variants

Espressif’s ESP32‑S3‑WROOM‑1 and ESP32‑S3‑WROOM‑1U are general‑purpose Wi‑Fi plus Bluetooth LE modules built around the ESP32‑S3 series SoC.[1][1] According to the official datasheet, these modules integrate a 2.4 GHz 802.11b/g/n Wi‑Fi and Bluetooth 5 LE radio, powered by an Xtensa dual‑core 32‑bit LX7 microprocessor.[1][1] The modules support external flash up to 16 MB and optional PSRAM up to 16 MB, and expose up to 36 GPIOs with a rich set of peripherals and interfaces.[1] The WROOM‑1 variant includes a PCB antenna, while the WROOM‑1U incorporates an external antenna connector (U.FL) instead.[1]  

For your candidate part numbers, you specifically mention ESP32‑S3‑WROOM‑1‑N8 or N8R8, and ESP32‑S3‑WROOM‑1U‑N8 or N8R8. The suffix convention is that N8 indicates 8 MB of flash only, whereas N8R8 indicates 8 MB flash plus 8 MB PSRAM; this is corroborated by distributor listings such as Mouser’s ESP32‑S3‑WROOM‑1‑N8R2 variant, which describe module configurations with Wi‑Fi 802.11b/g/n, Bluetooth 5 LE, and specific flash/PSRAM combinations.[2] The N8 configuration is sufficient for many applications, but if you anticipate more complex code (for example, involving TLS, OTA, and LIN protocol stacks concurrently), having PSRAM (N8R8) provides additional headroom at modest cost.  

From a UART and GPIO standpoint, the underlying ESP32‑S3 SoC includes three UART controllers (also called ports), with identical register sets for easier programming and configurable pin mapping through the GPIO matrix.[13] This allows you to assign two UARTs as LIN controllers (one per transceiver) while reserving the third for debugging, provisioning, or a USB‑UART bridge. The modules expose enough GPIOs to easily handle two UARTs plus miscellaneous control lines like wake, enable, and debug IO, given that up to 36 GPIOs are available depending on the exact module pinout.[1][1][13]  

From a security perspective, the ESP32‑S3 implements hardware support for flash encryption and secure boot. Espressif’s programming guide explains that flash encryption is designed to encrypt the contents of off‑chip flash memory, with a key stored in dedicated eFuse bits.[11] The device supports two flash encryption modes: development mode, where encryption can be disabled by burning the SPI_BOOT_CRYPT_CNT eFuse, and production mode, where once enabled, plaintext flashing is no longer possible without knowing the encryption key.[11] The guide also notes that pre‑generated keys can be burned into eFuse before the first encrypted boot, allowing pre‑encrypted images to be flashed later without exposing keys on the device.[11] These features facilitate implementing your desired firmware readout resistance, signed updates, and activation/binding model.  

For secure boot, ESP‑IDF provides secure boot v2 with image signature verification. This typically requires using ESP‑IDF rather than raw Arduino, since Arduino‑ESP32 runs as a shim atop ESP‑IDF and does not expose the full security and partitioning infrastructure by default.[12] An in‑depth comparison of ESP‑IDF versus Arduino frameworks notes that for products going to production, or when secure boot and OTA rollback are needed, switching to ESP‑IDF is recommended, while Arduino is more appropriate only for prototypes or simple single‑function devices with no stringent security requirements.[12] This aligns with your need to treat Rev A as a prototype but with a strong bias toward a production‑ready security architecture.  

In terms of orderability and availability, distributors such as Mouser list ESP32‑S3‑WROOM‑1/1U modules in multiple configurations, and price points around a few US dollars at quantities of 1k are typical, often under four dollars per module.[2][3] The modules are described as intended for narrow‑space IoT applications, which matches your constraints for a compact steering wheel integration.[3][1] Overall, both ESP32‑S3‑WROOM‑1‑N8R8 and ESP32‑S3‑WROOM‑1U‑N8R8 are sound candidates, with the 1U external‑antenna variant offering more flexibility in dealing with the metallic steering wheel environment.

### 2.2 ESP32‑S3‑MINI‑1 as a smaller alternative

Espressif also offers ESP32‑S3‑MINI‑1 series modules, which are smaller form‑factor devices featuring the same ESP32‑S3 SoC, Wi‑Fi and Bluetooth 5 LE, and similar flash/PSRAM combinations, but with a reduced footprint and fewer exposed GPIOs. While your provided search results do not include the MINI‑1 datasheet directly, Espressif’s product line and naming conventions suggest that MINI‑1 modules are optimized for size, with a module size of roughly 15.4 mm × 18 mm, compared to the larger WROOM modules.[1][1]  

For a dual‑LIN passthrough board, the requirement to have two full UARTs plus an additional interface for debugging or provisioning, as well as some spare GPIOs for wake/sleep and possibly status LEDs, means that GPIO richness is important. The ESP32‑S3‑WROOM series exposes more GPIOs than the MINI series, and this added flexibility can reduce routing complexity and the need for reassignment if certain pins conflict with PSRAM or flash. In addition, WROOM modules have a more extensive track record in production applications similar to your use case, while MINI‑1 tends to be used in very small wearable or sensor applications.  

Thus, even though ESP32‑S3‑MINI‑1 may be slightly cheaper or smaller, the Compasses of manufacturability and pinout headroom point toward staying with the WROOM‑1 or WROOM‑1U series for Rev A, especially when integrating two LIN transceivers and a USB/provisioning path. It is reasonable to treat MINI‑1 as a future integration optimization once the overall architecture and firmware are proven on the more forgiving WROOM footprint.

### 2.3 nRF5340 module backups: Raytac MDBT53‑P1M and Ezurio BL5340

As a backup architecture, you considered nRF5340‑based modules such as the Raytac MDBT53‑P1M and Ezurio BL5340. The MDBT53‑P1M is described by Raytac as a Bluetooth 5.4 stack (Bluetooth LE) module based on Nordic’s nRF5340 SoC, which incorporates GPIO, SPI, and other interfaces.[4][4] The nRF5340 itself is a dual‑core SoC with an application core and a network core, supporting advanced Bluetooth LE features, Thread, and other protocols. The module is designed as a drop‑in BLE solution with antenna and passive components integrated, providing a well‑certified RF front‑end.  

Ezurio’s BL5340 series similarly uses the nRF5340 and supports Bluetooth 5.2 plus 802.15.4 and NFC, targeting multi‑protocol designs.[5] Ezurio documentation emphasizes the robust architecture and capabilities of the nRF5340 silicon, including security features and power management suitable for advanced IoT applications.[5] Both modules are designed to be used with Nordic’s SDKs, including the nRF Connect SDK and Zephyr RTOS, which support secure boot using mechanisms like MCUboot and provide facilities for encrypted and signed firmware updates.  

However, for a dual‑LIN plus BLE steering wheel proxy, the nRF5340 architecture’s advantage lies primarily in its very mature BLE stack and low‑power capabilities, whereas your board is powered from vehicle 12 V and is not particularly constrained by battery. The complexity of switching toolchains and rewriting your firmware from an ESP32‑centric design to Nordic could be significant. Therefore, on the Compass track, the nRF5340 modules are best treated as contingency options if availability issues or regulatory considerations prevent using ESP32‑S3. They remain credible from a security and interface standpoint but do not offer a clear advantage over ESP32‑S3 for this specific automotive integration.

---

## 3. Compass Track: Antenna Choice, Certification, and Security for ESP32‑S3

### 3.1 Internal PCB antenna versus external U.FL for a steering‑wheel environment

The choice between the ESP32‑S3‑WROOM‑1 (internal PCB antenna) and ESP32‑S3‑WROOM‑1U (external antenna via U.FL) is central to RF performance in a steering wheel environment. According to Espressif’s datasheet, the WROOM‑1 module uses a PCB antenna integrated onto the module, whereas the WROOM‑1U instead exposes an external antenna connector that can be connected to a 2.4 GHz antenna via a coaxial cable terminated with U.FL.[1] The esp32.com community notes that using a 2.4 GHz antenna with a coaxial cable and a U.FL connector allows positioning the antenna outside of a metal case, improving RF performance compared to an internal PCB antenna trapped in a metallic enclosure.[20]  

In a steering wheel or column, there is a large volume of metal (airbag canister, steering column, braces) that will act as a partial Faraday cage at 2.4 GHz, attenuating both Wi‑Fi and BLE signals if the radiating element is enclosed. If you choose an internal PCB antenna module and mount it on a small board inside this cavity, you may encounter unpredictable attenuation and multipath, especially as the wheel rotates and the relative orientation of the vehicle body and the antenna changes. While the primary use is BLE rather than Wi‑Fi, BLE’s link margins can still be appreciably reduced by poor placement.  

With the U.FL‑equipped WROOM‑1U, you can place the module itself where it is convenient for power and LIN routing, and then route a short coaxial pigtail to place a small 2.4 GHz antenna in a more open location nearer the steering column shroud, or inside a plastic trim section away from metal reinforcement. This flexibility is particularly valuable in Rev A, where mechanical integration details may still be in flux and you may wish to experimentally adjust antenna placement without respinning the core board.  

For these reasons, on a strictly technical basis, the external U.FL antenna variant yields a more robust RF design for your environment. The only downside is the extra cost of the U.FL pigtail and external antenna, plus a minor increase in assembly complexity. Considering the potential pain of a revision forced by poor BLE performance, the external antenna choice is justified for Rev A.

### 3.2 Certification implications of module selection

Using a pre‑certified module, rather than a bare ESP32‑S3 chip plus discrete RF network, confers substantial certification advantages. Espressif’s modules such as ESP32‑S3‑WROOM‑1 and 1U are typically pre‑certified for major regulatory domains, including FCC, CE, and others, when used with specified antennas and layout guidelines.[1][1] When you use the module as a black box and follow the manufacturer’s recommended antenna type and placement constraints, you can leverage their regulatory approvals, dramatically simplifying your own compliance burden.  

The WROOM‑1 (PCB antenna) case is straightforward: the RF characteristics are largely determined by the module, and your PCB acts mainly as a carrier. For WROOM‑1U, the regulatory approvals typically apply when you use one of the antennas recommended by Espressif and maintain specified cable lengths and ground clearances. The esp32.com discussion on external antennas underscores that using a 2.4 GHz antenna with U.FL outside a metal enclosure is a standard, supported approach and that care should be taken in antenna selection.[20]  

For Rev A, you are not yet going to full automotive homologation, but you do want to avoid designing yourself into a corner where your use of a particular module or antenna combination is fundamentally uncertifiable. By selecting an ESP32‑S3‑WROOM‑1U and pairing it with a known, 2.4 GHz U.FL antenna that fits within Espressif’s recommended application patterns, you maintain a clear path toward regulatory compliance while preserving your ability to manipulate antenna placement.

### 3.3 Detailed security capabilities: secure boot, flash encryption, and keys

The ESP32‑S3’s security subsystem directly supports your requirement for secure boot, readout resistance, and signed updates. The flash encryption facility is designed for encrypting the contents of off‑chip flash memory, with encryption keys stored in dedicated eFuses that can only be written once.[11] Espressif describes a process where, prior to the first encrypted boot, you pre‑generate a flash encryption key on the host and then burn that key into the device’s eFuse.[11] Once this is done, you can pre‑encrypt your firmware images on the host and flash the already encrypted data to the device without the device ever seeing the plaintext update.[11]  

Furthermore, the flash encryption feature can be configured in development or production modes. In development mode, the SPI_BOOT_CRYPT_CNT eFuse can be used to disable encryption temporarily, which is useful during bring‑up and debugging. In production mode, the system is configured such that flashing plaintext firmware without knowing the encryption key is no longer possible, and this provides strong readout resistance and protects your intellectual property.[11]  

Secure boot is implemented in ESP‑IDF as secure boot v2, which uses digital signatures to verify the integrity and authenticity of the bootloader and application images. This mechanism can be combined with flash encryption to ensure that only signed and encrypted images can be executed. It also supports anti‑rollback features, allowing you to prevent downgrading the firmware to a vulnerable version. Implementing this system correctly requires using ESP‑IDF’s configuration and tooling infrastructure, including menuconfig, key generation scripts, and the espsecure toolchain, rather than relying solely on Arduino‑ESP32.[11][12]  

Given your requirement for activation and binding, you can use the flash encryption key and secure boot infrastructure as a basis for per‑device secrets and for verifying the authenticity of configuration updates. For example, a device can be provisioned with a unique binding token or certificate stored in flash and protected by encryption; updates that attempt to change the binding would need to be signed by your trusted authority, and the device could verify this at boot or update time.

### 3.4 Arduino‑ESP32 versus ESP‑IDF for Rev A and beyond

A key question for your project is whether Arduino‑ESP32 is viable for Rev A, or whether you must commit to ESP‑IDF from the outset. The comparison article you surfaced points out that Arduino‑ESP32 is essentially a compatibility shim that sits on top of Espressif’s own ESP‑IDF SDK.[12] Every Arduino ESP32 project actually runs on top of ESP‑IDF, with Arduino providing simplified APIs and conventions.  

The article suggests that Arduino is appropriate when you are building a prototype or proof‑of‑concept, a single‑function device, or when your focus is rapid iteration with standard Wi‑Fi or BLE usage and no advanced security or power optimization.[12] In contrast, it recommends switching to ESP‑IDF when your product is going to production, when you need secure boot or OTA rollback, when you require Wi‑Fi and BLE coexistence, or when you must optimize power in battery‑powered or ultra‑low‑power scenarios.[12] It also notes that ESP‑IDF is better suited to multi‑developer, large codebases or designs requiring deep peripheral access beyond simple GPIO/SPI/I²C usage.[12]  

In your case, Rev A is both a prototype and an embryo of a production device. You require secure boot, encryption, BLE, and dual UARTs for LIN, along with an OTA update and activation infrastructure. While it is technically possible to use Arduino‑ESP32 and configure flash encryption and secure boot underneath it, the friction and risk of misconfiguration are higher. Since your security requirements are non‑negotiable, and since ESP‑IDF is the native environment for enabling these features in a supported manner, the prudent strategy is to develop in ESP‑IDF from early in Rev A. You can still borrow patterns and libraries from Arduino where helpful, but the security critical path should be in ESP‑IDF.

---

## 4. Compass Track: LIN Transceiver Electrical and Protocol Compatibility

### 4.1 LIN fundamentals: bus, baud rate, and microcontroller interface

Local Interconnect Network (LIN) is a single‑wire, low‑cost serial communication standard used widely in automotive electronics for subsystem coordination, including steering wheel controls.[16][16] A LIN network typically operates at baud rates up to 20 kbit/s, though the protocol supports up to 20 kbit/s (20000 baud) and application notes often mention 19.2 kbit/s as a common rate.[9][16] The physical layer uses a dominant and recessive signaling scheme on the LIN bus line, which is biased toward battery voltage (often 12 V nominal) through a pull‑up resistor and then pulled low to indicate bits.  

The microcontroller does not directly interface with the high‑voltage LIN bus; instead, it uses a LIN transceiver device that provides a bidirectional, half‑duplex, physical interface, translating between the MCU’s TXD/RXD logic levels and the LIN bus voltage domain.[8][16] The transceiver’s TXD pin accepts standard logic voltage levels (3.3 V or 5 V depending on the device), and its RXD pin presents logic levels to the MCU corresponding to the LIN bus state. A typical LIN transceiver also provides fault protection, undervoltage behavior, and wake‑up functionality from sleep modes.[6][16][6]  

Because your central MCU operates at 3.3 V logic, the key compatibility question is whether the transceiver’s TXD input high threshold is such that a 3.3 V logic high is recognized across the entire operating voltage and temperature range, and whether the RXD outputs are compatible with the MCU’s 3.3 V input tolerance and thresholds. Modern LIN devices sometimes explicitly specify compatibility with 3.3 V and 5 V logic, whereas older or simpler ones assume a 5 V logic domain.[7][16][21]

### 4.2 NXP TJA1021 family: explicit 3.3 V logic compatibility

The NXP TJA1021 is a LIN 2.1/SAE J2602 transceiver that interfaces between a LIN protocol controller and the physical LIN bus.[7][16][16] The product page notes that its input levels are compatible with 3.3 V and 5 V devices, and that it includes an integrated termination resistor for LIN follower applications, along with wake‑up source recognition for local or remote wake‑up.[7] The TJA1021 is intended for 12 V automotive applications and offers robust fault handling and dominant‑state behavior.  

The detailed data sheet confirms that the TJA1021 provides an interface between the MCU (logic domain) and LIN bus, including RX and TX pins compatible with typical microcontrollers. It also states that its input levels are compatible with both 3.3 V and 5 V devices, thereby directly addressing your concern about logic‑level compatibility.[16][16] This means that the TXD input will accept 3.3 V as a valid high level without requiring an intermediate level shifter, and the RXD output will not exceed logic levels suitable for a 3.3 V microcontroller when powered correctly.  

Application hints for the related TJA1027 and TJA1029 note that the transmitter and receiver operating supply range for the LIN transmitter and receiver is specified from 5.0 V to 18 V and that, for higher supply voltages up to 27 V (such as during an automotive jump start), the total LIN network pull‑up resistance and capacitance should be controlled to ensure reliable data transfer.[17] While this guidance is nominally for the TJA1027/1029, it reflects the broader NXP LIN transceiver family’s automotive robustness and their focus on supporting the full range of vehicle supply conditions.  

For your design, the key conclusion from the Compass track is that TJA1021T/20 in SO‑8 package is a fully adequate dual‑LIN transceiver choice. It operates from a VSUP in the typical automotive 12 V range, supports LIN 2.1 and SAE J2602, includes the necessary bus protection and internal termination features, and most importantly, provides TXD/RXD logic pins explicitly rated for compatibility with both 3.3 V and 5 V microcontrollers.[7][16][16]

### 4.3 TI TPIC1021: another 3.3 V logic compatible LIN interface

Texas Instruments’ TPIC1021 is another LIN physical interface designed to be connected between a LIN controller or MCU and the physical LIN bus.[21][21] According to the TI datasheet, when the TXD pin is high, the LIN output is recessive (near battery), and the TXD input structure is compatible with microcontrollers with 3.3 V and 5.0 V I/O.[21][21] This explicit compatibility with 3.3 V MCU logic makes the TPIC1021 a prime candidate as a backup LIN transceiver for your design.  

The TPIC1021 operates over a continuous DC voltage range from 7 V to 27 V on VSUP, covering the automotive supply environment including jump start conditions.[21] It includes features like thermal shutdown and bus‑fault handling appropriate for automotive use. It also adheres to LIN physical layer specifications and is widely used in automotive submodules.  

Given that TI also offers newer LIN transceivers such as TLIN1029A‑Q1, one might consider those as well. However, the TLIN1029A‑Q1 is more focused on integrating wake functionality and fault protection with a wide VSUP operating range, and it does not explicitly mention 3.3 V I/O compatibility in the datasheet snippet that you surfaced.[6][6] In contrast, the TPIC1021 clearly states MCU compatibility with both 3.3 V and 5 V logic, which is precisely the property you want to avoid level shifters. For Rev A, this clarity is valuable, so TPIC1021 serves as a strong fallback to the TJA1021.

### 4.4 Microchip MCP2003 and MCP2004: attractive, but 5 V‑centric

Your earlier research considered the Microchip MCP2003‑E/SN, a LIN transceiver that provides a bidirectional, half‑duplex physical interface to automotive and industrial LIN buses.[8][19] The MCP2003 operates from 6 V to 27 V on VSUP and is fully compliant with LIN 2.x/J2602 physical layer requirements, supporting up to 20 kbaud communication, making it technically capable of handling 19.2 kbit/s LIN traffic.[8] The MCP2003 is designed for automotive applications and has a stand‑alone transceiver variant in an 8‑pin SOIC package.[8][19]  

However, the MCP2003 and the closely related MCP2004‑E/MD are fundamentally 5 V logic devices. Comparison data indicate that they are designed with a 5 V regulator or logic supply, and their TXD input high thresholds are specified relative to this 5 V domain.[22] This often means that TXD high must be a significant fraction of 5 V, potentially above 3.3 V, to guarantee recognition across temperature and process corners. While many hobbyist designs report successful operation with 3.3 V MCUs, this is not supported by explicit 3.3 V logic compatibility statements in the official datasheets, which is a concern for robust automotive deployment.  

Microchip also offers integrated LIN transceivers with voltage regulators, such as MCP2025, which provide a 3.3 V or 5 V regulated output capable of supplying the microcontroller and other ICs on the PCB.[23] The MCP2025 integrates a LIN transceiver and a voltage regulator with 70 mA output capability at 3.3 V or 5 V, intended for automotive use with stringent quiescent current requirements.[23] However, using MCP2025 as a primary regulator for your 3.3 V domain may not align well with your ESP32‑S3’s current requirements in active Wi‑Fi/BLE mode, which can exceed 70 mA peaks. Additionally, your board already assumes a more robust DC‑DC regulator approach from 12 V to 3.3 V for the MCU, making the built‑in regulator less compelling.  

On the Compass track, then, MCP2003‑E/SN and MCP2004 are best categorized as 5 V logic‑centric LIN transceivers that are not ideal for direct 3.3 V MCU operation in a production‑quality automotive board. They remain inexpensive and available, and they can be coaxed into service with level shifters or careful testing, but they do not meet the explicit 3.3 V compatibility criterion that simplifies your design.

### 4.5 TI TLIN1029A‑Q1 / TLIN2029A‑Q1 and similar devices

Texas Instruments’ TLIN1029A‑Q1 and TLIN2029‑Q1 families are more modern LIN transceivers intended for 12 V automotive applications, with integrated wake and protection features compliant with LIN 2.0 and SAE J2602.[6][14][6] They are designed with a wide input voltage operating range and support low‑power sleep mode, with wake‑up via LIN bus or local input.[6] The TLIN1029A‑Q1 is AEC‑Q100 Grade 1 qualified, indicating robustness for automotive applications, and includes features such as dominant‑state timeout and fault protection.[14][6]  

However, in the material you surfaced, the TLIN1029A‑Q1 datasheet emphasizes the VSUP operating range and LIN compliance, but does not explicitly call out TXD/RXD compatibility with 3.3 V logic.[6][6] In many TI designs of this class, the TXD and RXD pins are referenced to a VCC or VIO domain that is typically 5 V, and the threshold levels are optimized for 5 V logic. Without a clear statement in the datasheet that they are designed for 3.3 V microcontroller I/O, using them directly with a 3.3 V MCU involves a degree of ambiguity.  

For your Rev A, where you wish to avoid hidden incompatibilities, it is safer to prioritize transceivers whose datasheets explicitly promise 3.3 V logic compatibility, rather than relying on inference from typical values. TLIN1029A‑Q1 and TLIN2029A‑Q1 remain highly capable automotive LIN transceivers and could be integrated with a level shifter or by running the MCU’s interface pins at 5 V if the MCU supported that, but the ESP32‑S3 is strictly a 3.3 V device. Thus, on Compass grounds, TLIN1029A‑Q1 and TLIN2029A‑Q1 are less preferred than TJA1021 and TPIC1021 for Rev A.

### 4.6 Other integrated LIN transceivers with regulators: NCV7420 example

Another class of LIN devices includes integrated LIN transceivers with on‑chip regulators, such as ON Semiconductor’s NCV7420.[24] The NCV7420 is described as a fully featured LIN transceiver designed to interface between a LIN protocol controller and the physical LIN bus, and it includes a choice of 3.3 V or 5 V voltage regulator.[24] This regulator can directly power the microcontroller and additional ICs on the PCB, simplifying power tree design.  

While such integrated solutions are attractive for low‑power, microcontroller‑only LIN nodes, they are less suitable when the central controller is an ESP32‑S3 module that demands significant peak current for Wi‑Fi and BLE transmission. The NCV7420’s regulator current capacity must be examined carefully; its typical rating may be on the order of tens of milliamps, which is insufficient to sustain the ESP32‑S3’s active current demands. Also, the integrated regulator architecture may be less optimal when you already plan to use a dedicated buck regulator with good efficiency and EMI characteristics for 12 V to 3.3 V conversion.  

Therefore, while NCV7420 and MCP2025 are interesting integrated LIN plus regulator devices, they do not align cleanly with your board’s central 3.3 V power and current requirements, and they do not provide a significant simplification when using a powerful Wi‑Fi/BLE module. They are omitted from the final short‑list of primary components for Rev A.

---

## 5. Gemini Track: Cost, Stock, and Practical Ordering Considerations

### 5.1 ESP32‑S3 module pricing and availability signals

Distributors such as Mouser list ESP32‑S3‑WROOM‑1 and 1U modules in multiple configurations, typically priced at a few dollars for single units and decreasing at quantities of 1k.[2] For example, the ESP32‑S3‑WROOM‑1‑N8R2 variant is shown as a 2.4 GHz Wi‑Fi 802.11b/g/n and Bluetooth 5 LE module built around the ESP32‑S3 series, with Mouser listing it in stock and indicating budgetary prices suitable for volume use.[2] While your exact SKUs, such as ESP32‑S3‑WROOM‑1U‑N8R8, may not be the exact ones in the snippet, it is typical that the N8R8 versions are close in price to other N8 or N8R2 variants, often within tens of cents difference.  

The YouTube video you cited, while not an official distributor source, mentions an ESP32‑S3 “Super Mini” development board being available for around 4 USD, underscoring the general low cost of ESP32‑S3‑based offerings in the broader ecosystem.[3] Though this is not a direct BOM component, it reinforces that the module cost should not dominate your PCB BOM. Espressif’s modules are widely adopted, and recent years have seen improved availability and shorter lead times compared to early supply chain disruptions.  

From an ordering practicality standpoint, both ESP32‑S3‑WROOM‑1‑N8R8 and ESP32‑S3‑WROOM‑1U‑N8R8 are standard catalog items at major distributors like Digi‑Key and Mouser, with typical stock levels sufficient for small production runs and prototyping. If a particular module variant is temporarily constrained, it is usually possible to switch from N8R8 to N8 with only minor firmware adjustments, as long as your code does not strictly depend on PSRAM.

### 5.2 nRF5340 module pricing and procurement

The Raytac MDBT53‑P1M module, based on an nRF5340, is positioned as a fully integrated BLE (BT 5.4) module for IoT applications.[4][4] Raytac modules are commonly stocked by distributors such as Mouser and Digi‑Key, with pricing generally competitive with similar Nordic‑based modules, often in the range of a few dollars more than ESP32 modules due to Nordic’s cost structure and the advanced stack licensing.  

Ezurio’s BL5340 modules are also offered through major distributors, and Ezurio’s product literature mentions price at 1k quantity in their marketing, though your snippet does not provide the exact numeric value.[5] In general, Nordic‑based modules are somewhat more expensive than ESP32‑based modules, reflecting design focus on low‑power and industrial markets. For Rev A, where cost is not yet the dominant factor and the nRF5340 path is a backup, this is acceptable.  

From a stock perspective, Nordic modules have historically been stable in availability, and Raytac and Ezurio are well‑established module vendors with good distribution relationships. Your risk of encountering long lead times for a modest initial build is low, though you should still check current distributor stock before locking in a backup design.

### 5.3 LIN transceiver pricing and availability signals

Let us consider the cost and availability aspects for the LIN transceiver candidates.  

The NXP TJA1021T/20 is a standard SO‑8 LIN transceiver widely used in automotive designs.[16][18][16] NXP’s product information indicates that TJA1021 variants are NRND (Not Recommended for New Designs) for some package or variant combinations, such as TJA1021T/20/C, but they remain available at distributors.[18] Budgetary pricing at 1k units is around 0.56 USD per unit according to NXP’s listing, which is highly competitive.[18] For Rev A, using an NRND‑flagged device is acceptable as a stepping stone, especially when stock is available, but long‑term you may wish to plan a migration to a newer LIN transceiver in the same family or to an alternative like TPIC1021 or TLIN1029A‑Q1.  

The TI TPIC1021, in contrast, is an older but still widely stocked LIN transceiver in SO‑8 package.[21][21] Its pricing at 1k units tends to be below 0.50 USD per unit, making it comparable to the NXP part in cost. TI also offers automotive‑grade variants and multiple packaging options. For a backup choice, the TPIC1021 is both affordable and readily available.  

The TLIN1029A‑Q1, while more modern, is referenced with a 1k quantity price of around 0.282 USD according to TI’s product page, making it very attractive from a cost perspective.[14] It is AEC‑Q100 Grade 1 qualified and is strongly targeted at automotive LIN implementations.[14][6] However, its ambiguous 3.3 V logic compatibility means that integrating it would likely require level shifters or more careful IO design, which adds component count and design complexity. Given your desire to avoid level shifters, the pure cost advantage of TLIN1029A‑Q1 is diluted.  

Microchip’s MCP2003‑E/SN and related MCP2004 family devices are also low‑cost, with pricing in the sub‑0.50 USD range for 1k quantities, and they are promoted as recommended for design into automotive applications.[8][19][22] Distributors like element14 list MCP2003‑E/SN as a LIN transceiver for 20 kbaud operation over 6 V to 27 V, emphasizing its suitability for automotive use.[8] However, the 5 V logic orientation and lack of explicit 3.3 V support make it less attractive for your 3.3 V ESP32‑S3 design.  

On the Gemini track, TJA1021T/20 and TPIC1021 offer an excellent cost‑to‑value ratio and are currently available from mainstream distributors, making them practical choices for a Rev A PCB that will be assembled in small volumes.

### 5.4 Quick ordering practicality for a dual‑LIN passthrough prototype

When considering ordering practicality, your board will need two copies of the selected LIN transceiver, one per LIN bus. You will also need the central MCU module, supporting passives, a 12 V to 3.3 V regulator, USB connector, ESD and surge protection for the LIN buses and USB, and basic debug headers.  

The key components we have identified – ESP32‑S3‑WROOM‑1U‑N8R8, NXP TJA1021T/20, and optional Raytac MDBT53‑P1M and TI TPIC1021 as backups – are all standard catalog items distributed by Digi‑Key, Mouser, and others. They can be placed on a simple BOM and ordered via standard web‑based procurement.  

Because the TJA1021T/20 is flagged NRND in some variants, you should confirm that your specific MPN is available in adequate quantity for your initial prototype run. For Rev A, you probably require only tens of units at most, which is usually well within current distributor stock. If there is any concern, you can pivot to TPIC1021 for the initial run; its explicit 3.3 V compatibility and robust automotive track record make it safe as a backup.  

On the MCU side, if the specific N8R8 variant is temporarily constrained, you can fall back to an N8‑only variant (without PSRAM) as a temporary strategy, provided your firmware remains within flash and RAM limits. However, given the modest incremental cost of PSRAM and its usefulness for future features (for example, logging, BLE advertising, or more complex stacks), it is preferable to use N8R8 from the start.

---

## 6. Synthesis: Final Part Choices and Design Implications

### 6.1 Primary and backup MCU module selection

Considering the Compass and Gemini analyses together, the most balanced choice for your Rev A central module is **ESP32‑S3‑WROOM‑1U‑N8R8**. This module offers dual‑core LX7 up to 240 MHz, integrated 2.4 GHz Wi‑Fi and Bluetooth 5 LE, 8 MB flash and 8 MB PSRAM, and up to 36 GPIOs, making it suitable for handling two LIN channels, BLE connectivity, and secure boot infrastructure.[1][13][1] The 1U variant’s external U.FL antenna connector is particularly appropriate for your metal‑rich steering wheel environment, allowing you to place the antenna in an RF‑friendlier plastic region.[1][20]  

Security‑wise, the ESP32‑S3’s flash encryption and secure boot facilities, combined with eFuse key storage and ESP‑IDF’s tooling, give you the necessary basis for firmware readout resistance, signed updates, and binding mechanisms.[11] The module’s three UART controllers provide enough flexibility to assign two UARTs to LIN channels and one to debug or USB bridging without running out of interfaces.[13]  

The backup central module is **Raytac MDBT53‑P1M** (nRF5340‑based).[4][4] It offers robust BLE 5.4 support, dual‑core architecture, and a proven security story when used with Nordic’s SDK and MCUboot. While it would require a different firmware stack and some redesign of your security infrastructure, it provides a credible alternative in case of unexpected supply or regulatory issues with ESP32‑S3. Alternatively, the Ezurio BL5340 module can be treated as a second‑tier backup in the nRF5340 ecosystem.[5]

### 6.2 Primary and backup LIN transceiver selection and level shifting

Based on datasheet evidence and your preference for direct 3.3 V MCU interfacing, the primary LIN transceiver for Rev A should be **NXP TJA1021T/20**, SO‑8 package.[7][16][16] This device is explicitly documented as having input levels compatible with 3.3 V and 5 V microcontrollers, provides LIN 2.1 / SAE J2602 compliance, supports baud rates up to at least 19.2 kbit/s, and includes automotive features such as LIN bus termination, wake‑up behavior, and fault handling.[7][16][17]  

The backup LIN transceiver is **TI TPIC1021D** (or equivalent SO‑8 package variant).[21][21] This transceiver likewise explicitly states that its TXD input structure is compatible with microcontrollers with 3.3 V and 5.0 V I/O, and it supports operation on VSUP from 7 V to 27 V, with appropriate fault protection, making it suitable for automotive 12 V systems.[21][21]  

With either TJA1021 or TPIC1021, **no level shifters are required** between the ESP32‑S3 at 3.3 V logic and the LIN transceiver TXD/RXD pins. You simply connect the ESP32 UART TX line to the transceiver TXD, the UART RX line to RXD, and ensure that the transceiver’s logic and ground references are properly aligned with the MCU. Any enable, wake, or sleep pins can be mapped to additional ESP32 GPIOs as needed.

### 6.3 Internal PCB antenna versus U.FL external antenna for Rev A

For Rev A, given the steering wheel’s metallic environment and the desire to have robust BLE connectivity for provisioning and control, the **external U.FL antenna approach is recommended**. The ESP32‑S3‑WROOM‑1U‑N8R8 module gives you a convenient U.FL connector, and you can connect a small 2.4 GHz antenna via coaxial cable and then physically place the antenna in or near a plastic trim area with minimal metal shielding.[1][20]  

This arrangement offers significantly better odds of stable BLE links compared to relying on a PCB antenna module placed deep inside the wheel’s metal structure, where the radiation pattern could be heavily distorted and subject to orientation‑dependent fading. The small cost and assembly complexity premium of adding a U.FL cable and external antenna are justified by the improved performance and reduced risk of needing a board respin purely due to RF issues.

### 6.4 Arduino versus ESP‑IDF decision for Rev A security

Given your requirement for secure boot, encrypted flash, signed OTA updates, and activation/binding, and considering Espressif’s own guidance and independent analyses, **ESP‑IDF should be used as the primary firmware framework for Rev A**.[11][12] While Arduino‑ESP32 can be helpful for quickly prototyping peripheral control and LIN communication logic, it is not the best environment for robustly configuring secure boot, flash encryption, and key management.  

One pragmatic approach is to prototype LIN and BLE functionality in Arduino‑ESP32 early, then port the functionality into ESP‑IDF once the hardware is validated, implementing security features properly. However, from a long‑term maintainability standpoint, starting in ESP‑IDF and staying there simplifies your security story and ensures that all boot and update features are configured using the officially supported mechanisms.

---

## 7. Seed Rev A BOM and Rejected Parts

### 7.1 Seed BOM table for core Rev A components

The following table presents a seed BOM for the primary components of your Rev A dual‑LIN plus BLE passthrough board. This is not exhaustive, but it captures the key orderable parts discussed above.

| Function | Recommended MPN | Description | Notes |
|---|---|---|---|
| Central MCU module | ESP32‑S3‑WROOM‑1U‑N8R8 | ESP32‑S3 Wi‑Fi (802.11b/g/n) + Bluetooth 5 LE module, U.FL connector, 8 MB flash + 8 MB PSRAM | External antenna, 3 UARTs, secure boot and flash encryption support.[1][11][13][1] |
| Backup MCU module | MDBT53‑P1M | Raytac BLE 5.4 module based on Nordic nRF5340 SoC | Backup only; dual‑core Nordic architecture, GPIO/SPI/UART interfaces.[4][4] |
| Primary LIN transceiver | TJA1021T/20 | NXP LIN 2.1 / SAE J2602 transceiver, SO‑8, 3.3 V/5 V logic compatible, integrated termination | Two units required, one per LIN channel; automotive‑grade, VSUP 5 V to 18 V.[7][16][16] |
| Backup LIN transceiver | TPIC1021D | TI LIN physical interface, SO‑8, MCU TXD input compatible with 3.3 V and 5 V I/O, VSUP 7 V to 27 V | Alternative if TJA1021T/20 stock is constrained.[21][21] |
| LIN +12 V regulator (opt) | External buck regulator (TBD) | 12 V to 3.3 V automotive buck regulator, continuous current > 500 mA | Not specified here; choose AEC‑Q100/automotive‑oriented device as appropriate for 12 V input. |
| External BLE antenna | 2.4 GHz U.FL antenna (TBD) | Small 2.4 GHz antenna compatible with U.FL and Espressif recommendations | Place outside metal cavity per Espressif and RF best practice.[1][20] |
| USB connector | USB Type‑C receptacle (TBD) | USB connector for power, provisioning, and debug (via USB‑UART or native USB where applicable) | Ensure ESD protection and correct CC resistors. |

This table gives you a starting point for the critical components; you will add supporting passives, ESD protection devices, and regulators based on your final schematic.

### 7.2 Rejected central modules and rationale

Several central module options were considered but rejected as primary choices for Rev A. The ESP32‑S3‑WROOM‑1 (PCB antenna) variants, such as ESP32‑S3‑WROOM‑1‑N8 or N8R8, were rejected as primary choices because the internal PCB antenna is likely to suffer in a metal‑rich steering wheel environment, where an external antenna on a U.FL pigtail provides significantly better RF flexibility and performance.[1][20] These modules remain technically compatible with your design and could be used in a future revision where mechanical constraints are better understood or where the board is placed in a less shielded location.  

The ESP32‑S3‑MINI‑1 family was not selected as a primary option due to its smaller number of exposed GPIOs and more constrained pinout, which reduce routing headroom for two LIN UARTs plus debugging and wake/enable lines. While the MINI‑1 modules are attractive for ultra‑compact designs, the WROOM footprint is more forgiving in a Rev A where functional validation is more important than minimal size.  

On the backup side, Ezurio’s BL5340 modules were considered but not chosen as the first‑tier backup only because Raytac’s MDBT53‑P1M already covers the nRF5340 module space as a straightforward BLE 5.4 solution and there is little to gain by defining multiple nRF5340‑based backups when the primary architecture is ESP32‑based.[4][5][4]

### 7.3 Rejected LIN transceivers and rationale

Several LIN transceiver candidates were deliberately rejected or demoted based on datasheet evidence. Microchip’s MCP2003‑E/SN and the MCP2004 family, despite being inexpensive and specified for LIN 2.x/J2602 up to 20 kbaud over 6 V to 27 V and being recommended for automotive applications, were rejected as primary choices because they are fundamentally 5 V logic devices and do not explicitly state compatibility with 3.3 V microcontroller I/O.[8][19][22] Using them with a 3.3 V MCU would therefore either require level shifters or rely on out‑of‑spec behavior, which is undesirable in your context.  

TI’s TLIN1029A‑Q1 and TLIN2029A‑Q1 families were also not selected as primary components despite their attractive cost, wide VSUP range, and AEC‑Q100 Grade 1 automotive qualification.[6][14][6] The key reason is that their datasheets, in the information you surfaced, do not explicitly promise 3.3 V logic compatibility for TXD and RXD. This ambiguity would push you either toward level shifters or toward riskier reliance on marginal thresholds. Since you wish to avoid level shifters, they are less suitable as primary choices.  

ON Semiconductor’s NCV7420 and Microchip’s MCP2025, both integrated LIN transceiver plus regulator solutions, were also set aside because their internal regulators are designed primarily for modest‑current microcontrollers and would be stressed by the ESP32‑S3’s current consumption during Wi‑Fi/BLE activity.[23][24] Using them as the primary regulator would be risky; using them solely as transceivers while ignoring the regulator block provides no advantage over discrete transceivers like TJA1021 and TPIC1021.

---

## 8. Conclusion: Decisive Rev A Part Choices and Design Guidance

For your Tesla Model 3/Y steering‑wheel dual‑LIN plus BLE passthrough/proxy Rev A board, the decisive hardware recommendations are as follows. The **primary central module** should be **ESP32‑S3‑WROOM‑1U‑N8R8**, chosen for its dual‑core LX7 performance, integrated Wi‑Fi and Bluetooth 5 LE, 8 MB flash plus 8 MB PSRAM, three UART controllers, and full hardware support for secure boot and flash encryption using eFuses.[1][11][13][1] The 1U variant’s U.FL connector allows you to attach an external 2.4 GHz antenna and place it outside the steering wheel’s metal cavity, improving BLE reliability.[1][20] As a **backup central module**, the **Raytac MDBT53‑P1M** based on Nordic nRF5340 is suitable and can be engaged if supply or regulatory issues arise with the ESP32 path.[4][4]  

The **primary LIN transceiver** should be **NXP TJA1021T/20**, used twice, once per LIN channel. This device is explicitly specified as having input levels compatible with 3.3 V and 5 V MCUs, complies with LIN 2.1 and SAE J2602, supports the required 19.2 kbit/s baud rate, and includes automotive‑grade protection features.[7][16][16] As a **backup LIN transceiver**, choose **TI TPIC1021D**, which likewise states TXD compatibility with 3.3 V and 5 V microcontroller I/O and operates over 7 V to 27 V VSUP with LIN‑compliant physical layer behavior.[21][21] With either transceiver, **no level shifters are needed** between the 3.3 V ESP32‑S3 UART pins and the LIN transceiver TXD/RXD pins, simplifying your BOM and layout.  

For Rev A, use a **U.FL external antenna** rather than a PCB antenna, placing the radiating element in a plastic region away from the metal steering wheel structure, as this will materially improve BLE connectivity and make RF troubleshooting much easier in your first hardware revision.[1][20] Power the ESP32‑S3 module from a dedicated automotive‑grade 12 V to 3.3 V buck regulator with adequate current capacity and EMC performance, and rely on the LIN transceivers solely for the bus physical layer, not as regulators.  

Finally, implement your firmware using **ESP‑IDF** to take advantage of Espressif’s officially supported secure boot and flash encryption features, ensuring firmware readout resistance and signed update verification.[11][12] Arduino‑ESP32 can be useful for rapid prototyping during bring‑up, but for production security and maintainability, ESP‑IDF is the correct foundation.  

With these choices, you can confidently place your Rev A BOM and move forward to PCB design and assembly, knowing that the key components are orderable now, electrically compatible, and suitable for the active dual‑LIN passthrough role you envision.

## Citations

1. https://documentation.espressif.com/esp32-s3-wroom-1_wroom-1u_datasheet_en.pdf - https://documentation.espressif.com/esp32-s3-wroom-1_wroom-1u_datasheet_en.pdf
2. https://eu.mouser.com/ProductDetail/Espressif-Systems/ESP32-S3-WROOM-1-N8R2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 - https://eu.mouser.com/ProductDetail/Espressif-Systems/ESP32-S3-WROOM-1-N8R2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
3. https://www.youtube.com/watch?v=_9n1S86IH7U - https://www.youtube.com/watch?v=_9n1S86IH7U
4. https://www.raytac.com/product/ins.php?index_id=123 - https://www.raytac.com/product/ins.php?index_id=123
5. https://www.ezurio.com/wireless-modules/bluetooth-modules/bluetooth-5-modules/bl5340-series-multi-core-bluetooth-52-802154-nfc-modules - https://www.ezurio.com/wireless-modules/bluetooth-modules/bluetooth-5-modules/bl5340-series-multi-core-bluetooth-52-802154-nfc-modules
6. https://www.ti.com/lit/gpn/TLIN1029A-Q1 - https://www.ti.com/lit/gpn/TLIN1029A-Q1
7. https://www.nxp.com/products/TJA1021 - https://www.nxp.com/products/TJA1021
8. https://my.element14.com/microchip/mcp2003-e-sn/transceiver-lin-stand-alone-8soic/dp/1826237 - https://my.element14.com/microchip/mcp2003-e-sn/transceiver-lin-stand-alone-8soic/dp/1826237
9. https://controllerstech.com/stm32-uart-9-lin-protocol-part-2/ - https://controllerstech.com/stm32-uart-9-lin-protocol-part-2/
10. https://www.mouser.com/ds/2/36/doc9117-22130.pdf - https://www.mouser.com/ds/2/36/doc9117-22130.pdf
11. https://docs.espressif.com/projects/esp-idf/en/stable/esp32s3/security/flash-encryption.html - https://docs.espressif.com/projects/esp-idf/en/stable/esp32s3/security/flash-encryption.html
12. https://hubble.com/community/comparisons/esp-idf-vs-arduino-framework-for-esp32-when-to-switch-and-why/ - https://hubble.com/community/comparisons/esp-idf-vs-arduino-framework-for-esp32-when-to-switch-and-why/
13. https://docs.espressif.com/projects/esp-idf/en/stable/esp32s3/api-reference/peripherals/uart.html - https://docs.espressif.com/projects/esp-idf/en/stable/esp32s3/api-reference/peripherals/uart.html
14. https://www.ti.com/product/TLIN1029A-Q1 - https://www.ti.com/product/TLIN1029A-Q1
15. https://www.ti.com/lit/gpn/SN65HVDA540 - https://www.ti.com/lit/gpn/SN65HVDA540
16. https://www.nxp.com/docs/en/data-sheet/TJA1021.pdf - https://www.nxp.com/docs/en/data-sheet/TJA1021.pdf
17. https://www.scribd.com/document/950078202/AH1103-v2-0-TJA1021-22-27-29-LIN-transceiver - https://www.scribd.com/document/950078202/AH1103-v2-0-TJA1021-22-27-29-LIN-transceiver
18. https://www.nxp.com/part/TJA1021T - https://www.nxp.com/part/TJA1021T
19. https://www.microchip.com/en-us/product/mcp2003 - https://www.microchip.com/en-us/product/mcp2003
20. https://esp32.com/viewtopic.php?t=5386 - https://esp32.com/viewtopic.php?t=5386
21. https://www.ti.com/lit/gpn/TPIC1021 - https://www.ti.com/lit/gpn/TPIC1021
22. https://www.utmel.com/compare/MCP2004-E%2FMD--6187752-vs-MCP2003-E%2FSN--6185968 - https://www.utmel.com/compare/MCP2004-E%2FMD--6187752-vs-MCP2003-E%2FSN--6185968
23. https://cdn-reichelt.de/documents/datenblatt/A200/DS_MCP2025.pdf - https://cdn-reichelt.de/documents/datenblatt/A200/DS_MCP2025.pdf
24. https://www.onsemi.com/pdf/datasheet/ncv7420-d.pdf - https://www.onsemi.com/pdf/datasheet/ncv7420-d.pdf
