lakewoodphone/tesla-lin-chip/research/responses/2026-05-29-cost-optimized-rev-a-dual-lin-esp32-s3-pcba-bom-research-8380af65.md

---
job_id: 8380af65-3661-4293-8873-9adbd23de7d4
directive_id: cost-optimized-rev-a-dual-lin-esp32-s3-pcba-bom-research
title: Cost-Optimized Rev A Dual-LIN ESP32-S3 PCBA BOM Research
domain: general
sensitivity: standard
model_used: sonar-deep-research
provider: perplexity
status: complete
completed_at: 2026-05-29T20:52:59.165166+00:00
cost_usd: 0.17893
input_tokens: 489
output_tokens: 15994
reasoning_tokens: 0
search_count: 10
citation_count: 0
verifier_status: passed
schema_version: 1
---

# Cost‑Optimized Rev A Dual‑LIN ESP32‑S3 Steering‑Wheel Board: BOM and Design Strategy

Designing a cost‑optimized, dual‑LIN, ESP32‑S3‑based inline board for Tesla Model 3/Y steering‑wheel integration at a 10–100 unit scale requires balancing automotive‑style robustness with the realities of low‑volume manufacturing and Chinese turnkey PCBA services. This report develops a practical Rev A bill of materials and design strategy around the already‑locked core components—ESP32‑S3‑WROOM‑1U‑N8R8 module, dual NXP TJA1021T/20/C LIN transceivers, USB‑C service connector, and a protected 12 V automotive input feeding a 3.3 V rail of at least 500 mA—while optimizing for assembly via JLCPCB, LCSC, and PCBWay. The analysis proposes specific candidate MPNs and LCSC‑friendly part numbers for input protection, reverse polarity protection, resettable fusing, TVS and load‑dump protection, 3.3 V buck conversion, USB ESD, LIN ESD, mechanical switching, test interface, and common passives. Two coherent paths are outlined: a low‑cost, “good enough” Rev A path suitable for early vehicle testing with reasonable safety margins, and a more robust path that selectively upgrades to automotive‑grade or higher‑performance components where the added cost materially improves safety, reliability, or noise immunity. The discussion further distinguishes which items should be machine‑assembled versus hand‑placed, estimates order‑of‑magnitude BOM plus assembly costs at 10 and 100 units, and highlights risk areas and validation gates to hit before committing to a 10‑unit run. Throughout, the emphasis is on a realistic, implementable Rev A that you can send to a typical turnkey PCBA house today, while leaving clear upgrade options for later spins once field data and diagnostics inform design refinements.

---

## System Context and Design Constraints

### Application and Functional Requirements

The target application is an inline dual‑LIN interface board that sits within the steering‑wheel harness path of a Tesla Model 3/Y. Functionally, this board must act as a dual‑channel LIN node and pass‑through device, integrating with and not compromising the existing OEM wiring. The ESP32‑S3‑WROOM‑1U‑N8R8 module provides a Wi‑Fi/BLE‑enabled microcontroller core with substantial flash and PSRAM, allowing the firmware to implement protocol translation, logging, remote diagnostics, or higher‑level user functions. The two NXP TJA1021T/20/C,118 LIN transceivers are fixed choices, thereby defining much of the LIN electrical interface behavior, including typical input voltage range, LIN bus pin characteristics, and fault handling at the physical layer.

Because the board is placed in‑line with the steering‑wheel harness, it must be both electrically and physically unobtrusive. The LIN wiring in Tesla vehicles is typically 12 V‑domain signaling with standard LIN protocol characteristics; while direct OEM specifications may be proprietary, the board must respect the usual LIN node behavior regarding recessive and dominant levels, bus impedance, and ESD/EMC robustness. From a system reliability standpoint, the design must minimize the chance that a board failure compromises steering‑wheel controls, airbags, or any safety‑critical function. That constraint primarily affects power path protection, isolation of the LIN lines via the transceivers and series resistors, and safe default behavior when the ESP32‑S3 resets or is unpowered.

The existing locked core choices strongly influence the rest of the design. The ESP32‑S3‑WROOM module dictates the need for a 3.3 V rail of at least 500 mA, acknowledging that radio transmissions and peak CPU load can create short current spikes that are significantly higher than the average draw. The NXP TJA1021T/20/C transceivers have specific supply and bus requirements, indicating a typical 5 V or battery‑related domain, depending on how you power them and what configuration is selected. For an inline board in a modern vehicle, a common approach is to power the LIN transceivers from the vehicle 12 V via internal regulation or from a local 5 V rail if one is generated. In the interest of simplicity and cost, and given the Rev A nature of this design, you can accept that the LIN transceivers are powered from a modestly filtered version of the 12 V battery input (or a simple 5 V linear stage if needed), while the logic domain is at 3.3 V for the ESP32‑S3. The locked requirement for USB‑C service suggests that the board will be accessed via a wired cable at least during development and possibly for firmware updates or diagnostics in the field.

The design also requires a physical LIN arm gate, which is best interpreted as a hardware‑level enable/disable or bypass mechanism for the LIN passthrough behavior. This can be implemented as a slide switch, jumper, or small mechanical selector that either isolates or bridges the LIN lines, or alternatively controls the transceiver enable pins in conjunction with routing that still ensures a safe default state. Finally, bottom pogo pads and a KiCad 10 CLI workflow indicate that test and firmware programming through padded contacts is needed, and that the design should be DFM‑friendly for command‑line CI pipelines that generate Gerbers, fabrication outputs, and assembly files.

### Automotive Electrical Environment and Protection Implications

Although this board will not undergo full automotive qualification in Rev A, it will be installed in a real vehicle electrical environment, which imposes non‑negotiable protections. The nominal 12 V battery rail can see a range of conditions, including cold‑crank dips down to approximately 6–7 V, normal operation in the 13.5–14.5 V range while charging, and load dump events that can exceed 40–60 V for tens or hundreds of milliseconds. Vehicles also exhibit overvoltage transients on inductive loads, as well as ESD events from user interaction, harness plugging, or static discharge from the cabin.

For a low‑volume, early‑stage design, you are not obligated to meet the full severity of ISO 7637 or ISO 16750 tests, but you should still design for a credible subset. A robust strategy includes reverse polarity protection (to guard against miswiring or service mistakes), a resettable fuse or sacrificial fuse element to limit catastrophic overcurrent, and transient voltage suppressors that clamp large transients. In a Tesla steering‑wheel harness, the immediate environment is somewhat shielded from starter‑motor load dumps and extreme conditions seen at the main 12 V bus, but the board should still be designed as if it is directly on that rail, particularly if you intend to reuse the design in different vehicles or locations.

Because this is an inline board, it should not introduce large voltage drops or excessive inrush currents that might confuse OEM modules. At the same time, it must protect its own electronics, which include a relatively sensitive ESP32, from the worst of automotive noise. That pushes the design towards an input stage that combines a series element (polyfuse), reverse polarity protection, and a suitably rated TVS diode, followed by a buck regulator that steps down to 3.3 V while tolerating input transients. The overall strategy can be adapted into two levels: a low‑cost path that uses a general‑purpose TVS, a non‑AEC‑Q buck converter, and basic MOSFET‑based reverse polarity protection; and a more robust path that substitutes automotive‑qualified TVS and buck regulators with extended input range and tested transient behavior.

### Manufacturing Context and PCBA Service Constraints

The design goal includes explicit optimization for JLCPCB, LCSC, and PCBWay. All three act as turnkey PCB plus assembly services, although their assembly capabilities, stock libraries, and pricing differ somewhat. In practice, JLCPCB and PCBWay both heavily encourage use of LCSC or their own in‑house stock libraries for economical assembly. This implies that component selection should favor parts that are common in those ecosystems and marked as “basic” where possible, thereby reducing placement fees and avoiding extended lead times or manual sourcing.

At 10–100 units, you are well below the threshold where customizing reels or negotiating special pricing makes sense, so you should favor components that are widely available and have off‑the‑shelf availability from LCSC in cut tape or shared reels. That also suggests that, where feasible, you should pick a single footprint and value for many passives (such as 0603 resistors and capacitors) rather than mixing 0402 and 0603 or unusual sizes that could complicate assembly or supply. This is particularly relevant for ESD diodes, USB components, and minor support circuitry, where there may be multiple credible MPNs and you can choose the one that is flagged as a “basic” or “preferred” component at the PCB assembler.

The requirement to avoid “hand‑solder loose‑chip workflows” means that Rev A should not depend on you reflowing QFN buck regulators or discrete 0402 TVS arrays by hand for every board. Instead, those parts should be included in the PCBA BOM and placed by the vendor. However, a reasonable compromise is to leave non‑critical mechanical items, large connectors that might be customized per vehicle, or a few simpler through‑hole parts for manual installation post‑assembly. The division between machine‑placed and hand‑placed components will be discussed in more detail in a dedicated section, but the overall target is to have all critical fine‑pitch and high‑pin‑count parts placed by the assembly house.

### Architectural Overview of the Power and Interface Subsystems

Within this context, the board architecture can be broken down into several functional areas, each of which maps to specific BOM selections.

The first area is the input protection and power front‑end. This consists of the automotive 12 V input connector, a reverse polarity protection element, a resettable fuse, a TVS diode for transient and load‑dump protection, and a filter stage feeding the buck regulator or regulators. For the low‑cost path, this may be a single buck converter that directly generates 3.3 V from the 12 V input. For the robust path, you may add a small pre‑regulation or at least select a buck converter with an extended input range and automotive qualification.

The second area is the 3.3 V rail generation and decoupling system. The ESP32‑S3‑WROOM module, as well as any supporting logic or sensors, will be powered from this rail. The 3.3 V rail must provide at least 500 mA dynamically, with good transient response, low output ripple, and sufficient EMC performance. The buck regulator design, inductor selection, and output capacitor network will dominate this behavior.

The third area is the USB‑C service connector and its ESD protection, CC configuration, and data interface to the ESP32. Because this is a “service” port, you may only require USB 2.0 data rates and 5 V bus power, without any power delivery beyond the standard 5 V. The connector choice must be easy to assemble and mechanically robust, and you should include an ESD protection array on the D+ and D− lines.

The fourth area is the LIN physical interface, including the two NXP TJA1021T/20/C transceivers, their supply rails, termination and filtering on the LIN pins, and additional ESD or surge protection devices. The physical LIN arm gate will sit logically adjacent to this subsystem, ideally implemented as a robust slide switch that can either disconnect the board from the LIN lines or control the transceivers’ enable pins.

The fifth area encompasses test and programming support, including bottom‑side pogo pad arrays, test points for key nets such as 3.3 V, 12 V, ground, and LIN lines, as well as fiducials for assembly alignment. These features are essential for a KiCad 10 CLI‑driven workflow and for reliable manufacturing.

Finally, the board will include the ubiquitous common passives and mechanical features: resistors, capacitors, indicator LEDs, mounting holes, and any optional features you decide to implement, such as a status LED or a simple pushbutton reset. Selecting standard, widely stocked 0603 components with typical values will minimize cost and complexity.

Having established the context and constraints, the next sections will move into concrete component recommendations, comparing low‑cost and robust variants, and making explicit decisions about which items should be installed by the PCBA vendor versus manually.

---

## Input Power Protection and 12 V Front‑End Design

### Reverse Polarity Protection Strategies and Candidate Components

Reverse polarity protection is a fundamental requirement in any automotive‑adjacent design, even if you personally intend to control installation and know that the connector is keyed. Service conditions, harness modifications, or mistakes during development can lead to accidental reverse connections. A simple series diode is the most straightforward solution, but it incurs a forward voltage drop that wastes power and can reduce the effective input voltage, especially under heavy load. For a 3.3 V, 500 mA system, this might not be catastrophic, but for a design with aspirations of robustness, you should prefer a MOSFET‑based solution.

For the low‑cost path, a P‑channel MOSFET “ideal diode” arrangement is a suitable compromise between protection and complexity. In this configuration, a P‑channel MOSFET is oriented so that its intrinsic body diode allows current flow in the correct direction, while an appropriate gate‑source bias fully enhances the MOSFET under normal conditions, thereby minimizing voltage drop. When the polarity is reversed, the MOSFET’s body diode is reverse‑biased, and the gate is not driven, preventing current flow. At LCSC, suitable P‑channel MOSFETs in SOT‑223, DPAK, or SO‑8 packages with adequate voltage rating and low Rds(on) are widely available. A practical candidate for this function is the AO4407A or an equivalent P‑channel MOSFET rated at around −30 V with Rds(on) on the order of a few tens of milliohms at the expected gate drive and current. While the exact LCSC part number may vary over time, you can select a P‑channel automotive‑oriented MOSFET such as AO4407A or FDN306P type devices from the LCSC catalog, ensuring a drain‑source voltage rating above 30 V and continuous current capability above 2–3 A to provide ample margin.

For the more robust path, you can consider an integrated ideal diode controller or reverse battery protection IC, but at a 10–100 unit scale, the cost and sourcing complexity may outweigh the benefits. Instead, a higher‑voltage P‑channel MOSFET with an AEC‑Q101 rating and lower Rds(on) may be substituted. Components like the Infineon IPD50P04P4L‑11 or similar automotive‑grade devices offer better thermal performance and documented behavior under automotive transients. Many of these are available in DPAK or D2PAK footprints and can be sourced from general distributors, though their presence as “basic” parts at JLCPCB may be limited. For Rev A, the incremental benefit of a fully automotive‑qualified MOSFET is arguably limited, so it is reasonable to keep the MOSFET in the “semi‑robust” category and spend robustness budget elsewhere, such as on TVS and buck conversion.

When designing the reverse polarity MOSFET arrangement, ensure that the MOSFET is placed immediately downstream of the input connector and upstream of any sensitive components. A modest gate‑source resistor will keep the MOSFET off when unpowered or reversed. The gate drive can be as simple as tying the gate to ground through a resistor, leveraging the input voltage across source and gate to enhance the device when polarity is correct. Careful layout is important: the high‑current path from input to the MOSFET source and then from drain to the rest of the circuit should be kept short and wide, with generous copper pour where feasible.

### Resettable Fuse and Overcurrent Protection Strategy

After reverse polarity protection, the next line of defense is overcurrent limiting. In a Tesla steering‑wheel harness environment, overcurrent is more likely to arise from internal faults on the board itself, such as shorted components or assembly defects, than from external conditions. A resettable polyfuse (PTC) is well suited to this scenario, as it can restrict current to a safe level during a fault and reset once the fault is removed.

For the low‑cost path, a standard resettable fuse such as the MF‑MSMF050 series (for example, MF‑MSMF050 or MF‑MSMF075) is an appropriate choice. These devices have hold currents on the order of 0.5–0.75 A and trip currents perhaps in the 1.0–1.5 A range, which is entirely adequate for a small board drawing less than 1 A under normal conditions. At LCSC and similar distributors, you will find numerous MF‑MSMF or RXEF series resettable fuses in 1206 or 1812 packages that are simple to place and inexpensive. For instance, an 1812 0.75 A hold polyfuse is a good starting point, providing enough headroom for the board to operate while still tripping under a short.

In the more robust path, you may opt for a slightly higher voltage rating and a device with a datasheet that provides more detailed derating curves for automotive temperature ranges. However, the incremental value of a fully AEC‑Q200‑qualified PTC in Rev A is modest if you are not yet committing to full automotive qualification. Another option is to use a conventional fuse instead of a polyfuse, sacrificing automatic reset in favor of a clearly blown, replaceable component. This may be desirable if you are concerned about hidden latent faults. For low volume and prototyping, though, a resettable fuse is very convenient and should be retained.

The polyfuse should be placed immediately after the reverse polarity MOSFET, so that in the event of a fault, the MOSFET sees limited stress and the rest of the board is protected. In a typical chain, the connector leads to reverse polarity protection, then to the polyfuse, and then to downstream TVS and buck stages.

### TVS Diode Selection and Load Dump Considerations

Protecting against load dump and other high‑energy transients is the most demanding aspect of the 12 V front‑end. In a fully automotive‑qualified design, you would choose an AEC‑Q101‑qualified TVS diode with a breakdown voltage tailored to the expected operating range and clamp voltage level. For Rev A, you can choose between a general‑purpose TVS diode with sufficiently high power rating and a dedicated automotive TVS that may or may not be flagged as “basic” in the JLCPCB library.

For the low‑cost path, a popular choice is the SMBJ24A or SMBJ26A series TVS diode in an SMB package. A nominal stand‑off voltage around 24–26 V is appropriate for clamping 12 V automotive transients while accommodating normal charging voltages. Devices such as SMBJ24A, SMBJ26A, or SMBJ33A have been used in many hobbyist and semi‑professional designs for 12 V protection. They are inexpensive and widely available at LCSC. A TVS diode of this class can clamp load dump‑like events sufficiently to protect the downstream buck regulator and other electronics, even if it does not provide full compliance with ISO load dump tests at the highest severity levels.

In the robust path, you might upgrade to an automotive‑grade TVS such as the SM8S36A or SM8S33A series, which have higher surge power ratings (often 6000 W or more) and are explicitly designed for load dump protection in automotive systems. These components are larger and more expensive and may not be offered as “basic” at JLC, but they provide substantial margin against worst‑case transients. Another robust option is to add a small series resistor between the polyfuse and the TVS, or to incorporate an LC filter that reduces surge energy reaching the TVS. At a 10–100 unit scale, the additional cost of a higher power TVS is often justified if you intend to deploy the board in real vehicles for extended periods, especially if failure in the field is difficult or costly to rectify.

The TVS diode should be placed close to the input connector, ideally between the post‑polyfuse node and ground, with short, wide traces to minimize inductance. Ground return from the TVS should be tied to a solid ground plane and avoid sharing thin traces with sensitive analog or digital grounds. If the board includes mounting hardware grounded to vehicle chassis, you can consider separating “chassis ground” and “logic ground” with appropriate bonding, but for Rev A, a single ground plane is simpler and acceptable, provided you are cautious about ground currents.

### Front‑End Filter and Power Distribution Topology

Between the TVS diode and the buck regulator, you should include a modest LC or RC filter to reduce conducted noise and protect the buck from fast transients. A simple series inductor or ferrite bead combined with a bulk input capacitor can significantly improve EMI performance and transient suppression. For example, a ferrite bead rated at several hundred milliamps with low DC resistance can be placed in series with the buck input, and a 10–47 µF electrolytic or ceramic capacitor can be placed at the buck input to smooth the supply.

For the low‑cost design, a single series ferrite bead in 1206 or 0805 size (such as 600 Ω at 100 MHz, 2 A rated) combined with a 22 µF, 25 V ceramic capacitor is an effective and economical filter. LCSC offers numerous such beads and capacitors under generic MPNs, and using 1206 or 0805 packages simplifies assembly. It is advisable to keep the buck input traces short and broad, with the input capacitor as close as possible to the regulator’s VIN and GND pins to reduce ringing and noise.

In the robust path, you might add a small LC filter where the series element is an inductor of a few microhenries rated for the full input current and the shunt element is a low‑ESR capacitor bank. However, that is more typical of higher‑power designs. For a sub‑1 A board, a single bead with good layout is usually sufficient. You could also consider up‑rating the input capacitor to a higher voltage and selecting a capacitor series that offers better temperature and voltage derating behavior.

Power distribution beyond the buck regulator should be carefully planned. The 3.3 V rail should be fed through separate traces to the ESP32 module and to other subsystems. A star distribution pattern is often beneficial, with local decoupling at each load. If you add a separate 5 V rail for USB or LIN transceivers, it can be derived either from the same buck (in a dual output design) or from another regulator stage, but for simplicity and cost, many Rev A designs choose to power the LIN transceivers directly from the filtered 12 V input, especially when the specific LIN transceiver is designed to operate from the battery domain and has its own internal regulation.

---

## 3.3 V Buck Regulator and Power Rail Design

### Requirements for the 3.3 V Rail

The ESP32‑S3‑WROOM‑1U‑N8R8 module is the primary load of the 3.3 V rail. It can draw peak currents approaching or exceeding 400–500 mA during Wi‑Fi transmissions, especially when all cores and radios are active. Additional loads may include indicator LEDs, logic devices, and any sensors you integrate later. Designing for at least 500 mA continuous capability with some headroom is prudent. If you anticipate more peripheral expansion, designing for 800 mA or 1 A provides margin without significantly increasing cost.

The rail must maintain regulation across the full expected input voltage range, which for automotive environments can span from about 9 V (during low battery or cold crank) to 16 V or more (with charging). The buck regulator should therefore have an input voltage rating of at least 24 V to provide adequate headroom. Efficiency is desirable but not paramount at these power levels; a modern synchronous buck regulator with around 85–90 percent efficiency is typical. Quiescent current is a secondary consideration, but if the board is powered for long periods without active operation, a regulator with low shutdown current and a controllable enable pin is useful.

Noise and ripple on the 3.3 V rail must be controlled to avoid affecting the ESP32’s RF performance or causing unintended resets. The ESP32 modules are reasonably robust, but good decoupling and layout are important. The regulator’s switching frequency should be high enough to allow small inductors and capacitors without pushing the noise into sensitive bands. Frequencies between 500 kHz and 1 MHz are common and practical.

### Low‑Cost Buck Regulator Options and MPN Candidates

For a cost‑optimized Rev A, you can select a widely used general‑purpose buck regulator in a SOIC‑8 or DFN package that is stocked as a “basic” component at JLCPCB. The MP1584EN is a classic example used in many inexpensive modules. It supports up to 3 A, accepts inputs up to 28 V, and is available in line with typical Chinese manufacturing libraries. Another near‑drop‑in candidate is the MP2307, which offers similar parameters. However, both are somewhat over‑specified for a 0.5–1 A load and may not be the most efficient at low currents, though they are extremely cost‑effective and easy to source.

If you prefer a more modern, compact device, the MP2459 or similar 1 A buck regulator from MPS or Richtek families offers a good balance. These parts frequently appear in JLC’s basic library and LCSC’s catalog as standard options. A typical MP2459 device supports up to 36 V input, 1 A output, and switching frequencies around 1.2 MHz, allowing the use of small inductors and capacitors. The Bill of Materials around such a regulator includes a single inductor, a few ceramic capacitors, a feedback resistor divider, and optionally a compensation network depending on the regulator design.

To make the selection concrete, consider using a device like MP2459DT‑LF‑Z or an equivalent 1 A, 36 V, synchronous buck regulator that is flagged as a basic component at your chosen assembly house. For LCSC, these parts typically have specific catalog codes, and you would select an entry that is available in volume and indicates standard packaging. You can configure the output to 3.3 V with a simple resistor divider, using 0603 resistors that match your passive strategy.

In selecting the inductor, target a saturation current of at least 1.5–2 times the maximum expected load, and choose an inductance value aligned with the regulator’s datasheet recommendations for your input and output conditions. An inductor in the 4.7–10 µH range is commonplace for 12 V to 3.3 V conversion at around 1 MHz. LCSC carries many shielded inductors in 4x4 or 5x5 packages rated for 1–2 A, which are inexpensive and straightforward for the PCBA house to place.

Input and output capacitors should use ceramic capacitors in X7R or X5R dielectric. For the input, a 10–22 µF, 25 V or 35 V capacitor close to the regulator input is recommended. For the output, a combination of a 22 µF and one or two 4.7 µF 6.3 V or 10 V capacitors close to the regulator’s output pin and ground return will provide low ripple and good transient response. The ESP32 module itself should have its own decoupling capacitors, but adding a local 10 µF capacitor at the module’s 3.3 V pin cluster is beneficial.

### More Robust Buck Options: Automotive‑Grade and Extended Range

For a more robust path, consider using an automotive‑oriented buck regulator with AEC‑Q100 qualification and datasheet characterization for automotive transients. Devices from Texas Instruments, STMicroelectronics, Onsemi, or NXP often fit this description, such as TI’s LM2596‑Q1, LM2841‑Q1, or TPS54202‑Q1, or ST’s L7986A‑Q or similar. Many of these regulators support up to 40 V or even 60 V input, explicitly covering load dump scenarios without relying solely on the TVS diode for protection.

However, the availability of these automotive‑grade regulators as basic parts at JLCPCB is more limited, and they are often more expensive. At 10–100 units, the incremental cost per board may be tolerable if you are particularly concerned about load dump or want to gather data with a design that could scale into a more formal automotive deployment. For Rev A, though, you might choose to adopt such a regulator only if you can confirm that your PCBA vendor can source and assemble it without excessive extra charges. It may eventually be more practical for Rev B once you have verified the rest of the design.

If you do choose an automotive‑grade regulator, follow its datasheet recommended layout carefully, particularly the placement of input capacitors, catch diodes, and the switching node. These regulators often have more restrictive layout guidelines to meet EMI limits. For example, TI’s TPS54202‑Q1 uses an internal MOSFET and runs at a fixed switching frequency, with recommended values for the inductor and capacitors to achieve stable operation. The datasheet usually includes a formula or a reference design that you can follow, simplifying the design process.

From a purely functional standpoint, a general‑purpose MP2459‑class buck combined with a decent TVS diode can be perfectly adequate for a steering‑wheel inline board, especially if your board is not directly exposed to the worst‑case load dump conditions at the main battery bus. For this reason, many designers favor the low‑cost buck for Rev A and reserve the automotive‑grade regulator for a later iteration if testing indicates that transients are more severe than expected.

### Decoupling and Layout for the 3.3 V Rail and ESP32‑S3

Regardless of the buck choice, the implementation of the 3.3 V rail and its connection to the ESP32 module is critical for reliable operation. The ESP32‑S3‑WROOM module integrates RF circuitry, an oscillator, and internal regulators, all of which can be sensitive to supply noise and ground bounce. A well‑designed decoupling network and ground strategy will reduce the risk of resets, RF performance degradation, or sporadic behavior.

At the module’s 3.3 V supply pins, place at least one 10 µF and one 0.1 µF ceramic capacitor as close as possible to the pins, minimizing trace length and loop area. If the module footprint allows, place these capacitors on the same side of the board with short, direct traces. Additional 0.1 µF capacitors near other high‑speed digital pins can also be beneficial.

The 3.3 V trace from the buck regulator to the ESP32 should be reasonably wide, especially if it also feeds other loads. If the board is small, you can use a solid 3.3 V plane on one layer with a matching ground plane on the other. If you route in two layers without a dedicated plane, use thick traces for the main rail and avoid sharp corners and unnecessary vias that might introduce impedance.

Ground layout should prioritize a solid reference under and around the ESP32 module. Avoid routing noisy switching nodes or high‑current paths under the module if possible. The buck regulator’s switching loop should be compact and located away from the module. Place the inductor, input and output capacitors, and diode (if external) close together, and ensure the high di/dt loop is minimized.

If you include a power LED on the 3.3 V rail, choose a moderate series resistor to limit current and avoid unnecessary power consumption. For example, a standard 0603 LED with a 3.3 V rail and a 4.7–10 kΩ resistor will provide a visible but not overly bright indicator, drawing a fraction of a milliamp rather than several milliamps. If you expect to leave the board powered for long periods, these small power savings add up.

---

## USB‑C Service Interface and ESD Protection

### USB‑C Connector Selection and Mounting Considerations

The USB‑C service connector is primarily intended for development and potentially for field diagnostics or firmware update. For a low‑volume board, you want a connector that is robust, easy to assemble, and well supported in your PCBA vendor’s library. Many low‑cost designs use the “TYPE‑C‑31‑M‑12” style USB‑C receptacle supplied by various manufacturers such as Korean Hroparts, which is widely stocked on LCSC and often listed as a basic part at JLCPCB.

This style of connector is a mid‑mount surface‑mount receptacle with through‑hole mechanical tabs for strength. It typically supports USB 2.0 signals (D+ and D−) and provides multiple VBUS and GND pins for high current if needed. For a service‑only port, you likely only need 5 V VBUS and USB 2.0 D+/D− connectivity; you do not plan to implement full USB‑C power delivery or alternate modes. Therefore, you can wire the CC pins with simple pull‑down resistors as a device‑only implementation, or follow common reference designs that present an Rd resistor on each CC line to indicate that the board is a sink.

The choice of connector footprint affects assembly yield and mechanical reliability. A connector like TYPE‑C‑31‑M‑12 has fine‑pitch SMT pins but still falls within the range that JLCPCB and PCBWay handle routinely. You should ensure that the footprint in KiCad matches the manufacturer’s recommended pattern, including the solder mask and paste mask settings. It is often wise to slightly reduce the paste aperture size for the SMT pins to reduce the risk of solder bridging.

The connector should be placed at the edge of the board in a way that makes it accessible in the installed location. If the board is hidden inside steering‑wheel trim, you might bring the connector out to a concealed but reachable access panel. For Rev A, however, you might accept that the connector is only easily accessible during development and not worry about final ergonomics.

### USB 2.0 Data Path and ESD Protection Components

To protect the USB data lines and the device’s internal ESD structures, you should include a small, low‑capacitance ESD diode array near the connector. Devices such as USBLC6‑2SC6 (from STMicroelectronics) or TPD2E001 (from TI) are classical choices, but there are numerous equivalents available at LCSC and JLC. Look for a two‑line ESD protection device in SOT‑23‑6 or SOT‑23‑5 package optimized for high‑speed data lines, with low capacitance (less than about 3 pF per line) and fast clamping. An example MPN you can target is USBLC6‑2SC6 or an LCSC‑stocked clone with similar characteristics.

Place the ESD array between the USB connector and the ESP32’s USB interface pins, as close to the connector as possible. Route the D+ and D− lines as a differential pair with controlled impedance if possible, though for short runs and USB 2.0 full‑speed (12 Mbps) or even high‑speed (480 Mbps) with short trace lengths, precise impedance control is less critical on a small board. Keep the pair length‑matched, avoid sharp angles, and minimize stubs. The ESD array’s ground pin should be tied to the local ground via a short connection to minimize inductance.

VBUS should be routed through a modest‑current path to the board’s power domain. Since your board is primarily powered by the automotive 12 V rail, you might use VBUS only for communication and not for powering the whole system. However, you should still protect VBUS with an appropriate fuse or current‑limiting element and possibly a dedicated ESD or surge diode. A small single‑line TVS diode rated for 5 V, such as an SMBJ5.0CA or an ESD5V diode, can be used for VBUS. In simple service‑only designs, you can also include a 500 mA resettable PTC on VBUS if you want to guard against cable faults.

### CC Configuration and Power Role

Because this is a device‑only USB‑C port, you do not need a USB‑C power controller or complicated PD chipset. Instead, you can configure the CC pins with standard Rd resistors to indicate a downstream‑facing port (sink). Typical values are 5.1 kΩ from each CC pin to ground. In most service applications, a simple implementation with two 5.1 kΩ 0603 resistors is adequate. Some designs choose to only connect one CC pin (CC1) and tie CC2 to ground through a large resistor, but for robustness, especially with reversible cables, it is better to implement both CC1 and CC2 as sinks.

If you want the board to be able to function even when the automotive 12 V is absent, you might design the system so that it can optionally draw power from USB VBUS. In that case, you need a power path that allows either the automotive 12 V buck regulator or the USB 5 V to feed the 3.3 V regulator. For Rev A, this adds complexity and may not be necessary. A simpler approach is to require the automotive 12 V for full operation and use USB for communication only, with the board unpowered when the vehicle is off. Alternatively, you can design a small ORing scheme that chooses between 12 V and 5 V input, but that will complicate the front‑end.

For the purpose of this Rev A design aimed at simplicity and cost, you can assume that the board will be primarily powered by the vehicle 12 V and that USB VBUS is used only for logic‑level interactions, with the microcontroller still running off the 3.3 V rail derived from 12 V. If you want limited functionality over USB‑only power, you could design the 3.3 V regulator to accept 5 V as input as well, or include a small linear regulator from 5 V to 3.3 V that is enabled only when 12 V is absent.

---

## LIN Transceiver Protection, ESD, and Physical Arm Gate

### LIN Transceiver Power and Interface Basics

The NXP TJA1021T/20/C LIN transceivers are fixed components in your design, and their datasheet specifies typical operating conditions. They are designed to interface a microcontroller’s UART or LIN controller to the LIN bus, providing level shifting, slew rate control, and fault protection. The devices typically accept a supply voltage in the range of about 7–18 V, allowing direct connection to the vehicle battery. They provide a bus pin (LIN) that connects to the LIN line in the harness, as well as TXD, RXD, EN, and possibly other control pins that interface with the microcontroller.

For a dual‑LIN board, you will have two such transceivers, each connected to its own LIN line pair. In an inline configuration, you may route the OEM harness LIN line through the board, connecting each side to a separate node, or you may have one transceiver that acts as a pass‑through or gateway. The exact logical configuration depends on your intended firmware and system behavior. Electrically, though, each LIN bus pin should have ESD protection, series resistance as recommended by the datasheet, and possibly a common‑mode choke or filter if EMI is a concern.

The transceivers should be powered from a stable supply that tracks the vehicle battery but is filtered and protected. A common approach is to connect Vsup of each transceiver to the post‑protection 12 V bus, possibly through a small series resistor or LC filter. Decoupling capacitors (typically 100 nF and 1 µF) should be placed close to the Vsup pin and ground.

### LIN ESD and Surge Protection Components

While many LIN transceivers include some degree of ESD and surge protection on the bus pin internally, adding a dedicated ESD protection diode can significantly enhance robustness, especially in an inline installation where the harness may be exposed to user interaction during service or modifications. Devices specifically tailored for LIN, CAN, or automotive bus protection are ideal. For example, NXP, Nexperia, and other vendors produce PESD1LIN series devices, which are single‑line ESD protection diodes optimized for LIN bus lines. These diodes typically clamp ESD events to safe levels while presenting minimal additional capacitance or leakage.

At LCSC, you may not find exactly PESD1LIN, but you can locate single‑line automotive ESD diodes with similar parameters, often in SOD‑323 or SOT‑23 packages. An example class of components are PESD1CAN, PESD1LIN, or SDxx series ESD diodes. For the low‑cost path, you can choose a generic unidirectional 24 V TVS in a tiny SMD package that is specified for automotive lines. For the robust path, you can seek out an explicitly AEC‑Q101‑qualified LIN ESD diode from a major vendor, even if it costs slightly more.

Place the ESD diode as close as possible to the connector or harness entry point, with its ground connection returning to the ground plane via a short path. Series resistors recommended by the transceiver datasheet can be placed between the LIN pin and the connector. In some designs, additional filtering such as RC snubbers or small inductors are added, but for a Rev A cost‑optimized board, a simple ESD diode plus proper layout is usually sufficient.

### Physical LIN Arm Gate: Hardware Bypass or Enable Control

The requirement for a physical LIN arm gate implies a hardware‑level mechanism to enable or disable the board’s interaction with the LIN bus. There are two broad approaches: a hard bypass that connects the OEM LIN line directly, bypassing the board entirely, or a transceiver enable gate that controls whether the transceivers are active or in a high‑impedance state.

A hard bypass approach uses a mechanical switch or relay to connect the upstream and downstream LIN lines directly when in “bypass” mode and to route them through the transceivers when in “armed” mode. This approach offers maximum safety because, in bypass mode, the board cannot interfere with the LIN communication at all; the OEM harness is effectively restored to its original state. However, implementing this with a simple slide switch can be challenging because it requires at least a double‑pole configuration per LIN channel and may require more complex routing.

A more practical Rev A approach is to implement a transceiver enable gate. In this scheme, the LIN transceivers’ enable pins (such as EN or STB) are controlled by a mechanical slide switch that either allows the transceivers to operate or forces them into a standby or high‑impedance state. Coupled with a firmware design in which the microcontroller tri‑states or appropriately handles the LIN control pins when disabled, this can effectively “disarm” the board from actively participating on the bus. However, the transceivers are still physically in the bus path, which means that, in the unlikely event of a failure, they could still affect the bus. For Rev A, this trade‑off between absolute safety and simplicity is often acceptable, especially if you choose a reliable LIN transceiver and test extensively.

For the switch itself, a small surface‑mount slide switch with a clear actuation feel is appropriate. At LCSC, a common type is the SS‑12D07 or its many derivatives, which are miniature slide switches with various pole configurations. For a single “arm/disarm” function controlling a logic‑level EN signal, a simple SPDT or SPST slide switch suffices. If you eventually decide to implement a hard bypass, you might adopt a DPDT or 4PDT slide switch with appropriate current ratings, but that becomes mechanically larger and more expensive.

From a cost perspective, the difference between low‑end and mid‑range slide switches is not large at 10–100 units, so choosing a slightly more robust, metal‑frame switch may be worthwhile. Ensure the footprint is supported by your PCBA vendor, or plan to hand‑solder the switch after assembly, given that mechanical parts are often better placed manually to avoid damage in transit. This is one of the few components where manual installation is quite reasonable, which will be discussed later.

### LIN Line Termination and Filtering

LIN buses typically require line termination at the master node, consisting of a pull‑up resistor and a series diode to the 12 V battery, as specified in the LIN standard. Slave nodes do not usually add termination, instead relying on the master’s termination. In an inline board, you must respect the existing termination in the vehicle system and avoid adding additional terminations that could distort the signal. Therefore, your LIN transceivers should be connected to the bus with minimal additional loading, aside from the transceiver’s internal circuitry and any small series resistors or ESD diodes.

The NXP TJA1021 datasheet often recommends a small series resistor on the LIN pin to dampen ringing and provide some protection against short‑circuit currents. Values around 1–10 Ω are common. You should implement these resistors as 0603 parts, located close to the transceiver LIN pins. If you include ESD diodes, they should be placed between the series resistor and the connector so that they protect the transceiver as well.

If your board layout and environment are particularly noisy, you could add a small RC snubber from LIN to ground, but this is not strictly necessary for a Rev A. It is often better to keep the design simple and rely on the transceiver’s internal slew rate control and integrated protections, then evaluate signal integrity during bench testing and early vehicle trials.

---

## Test Infrastructure, Fiducials, and Common Passives

### Bottom Pogo Pads and Programming Interface

The requirement for bottom pogo pads aligns well with a production‑oriented workflow where boards are programmed and tested via a bed‑of‑nails fixture. For an ESP32‑S3‑based design, the minimum required programming pads typically include 3.3 V, GND, EN (reset), IO0 (boot mode), TXD, and RXD, depending on your chosen programming method. You might also add pads for the LIN bus lines, 12 V input, and any diagnostic signals you wish to monitor.

The pogo pads themselves do not require complex MPNs; they are simply exposed copper pads on the PCB, with perhaps some ENIG plating and appropriate size and spacing. However, if you want to include optional test pins or through‑hole test points, you can select components such as Keystone Electronics test points or generic 1 mm diameter loop test points. At LCSC, test point components in simple SMT styles (cylindrical pads with a raised contact) are available and can be machine‑placed if desired.

For a cost‑optimized Rev A, it may be sufficient to expose bare pads sized for pogo contact, arranged in a row or small cluster, and rely on a custom test fixture or a manual jig for programming. KiCad 10’s CLI workflow allows you to incorporate these pads as standard footprints with net associations, ensuring that the test fixtures can be designed using the same netlist and coordinate data.

### Fiducials and Assembly Alignment

Fiducials are required for automated optical alignment during PCBA. You should include at least three global fiducials on the board, ideally one in each corner or in positions that allow the pick‑and‑place machine to orient the board reliably. Additionally, you might include local fiducials near fine‑pitch components like the ESP32 module and the USB‑C connector. In KiCad, fiducials can be implemented as simple SMD pads with defined copper and solder mask clearance, and they do not require BOM entries.

Ensure that the fiducials are not covered by silkscreen or solder mask and that they are positioned with sufficient clearance from the board edge and other components. Many PCB houses have guidelines for fiducial design; following these guidelines will increase assembly yield.

### Common Passive Component Strategy

To minimize supply and assembly complexity, adopt a uniform passive component strategy. Using 0603 sizes for all resistors and capacitors is a good compromise between ease of assembly and board density for a board of this scale. 0603 components are easy to hand‑solder if needed, yet small enough for compact layouts. You may choose 0402 for decoupling capacitors near the ESP32 to reduce inductance, but for Rev A and low‑volume assembly, 0603 throughout is often easier.

Resistors should be 1 percent tolerance for most applications, with a few 0.1 percent parts if you have any analog sensing circuits. In this board, most resistors will serve as pull‑ups, pull‑downs, feedback dividers, series resistors, and LED currents, all of which are well served by 1 percent 0603 resistors. LCSC’s catalog contains many generic resistor series at very low cost, and JLCPCB marks some of them as “basic” components, meaning you should explicitly choose values and series from that subset when possible. For instance, using a standard series such as “RC0603FR‑0710KL” style for a 10 kΩ resistor, or its equivalent from UniOhm or Yageo, will often line up with basic parts.

Capacitors should be X7R or X5R dielectric, with voltage ratings appropriate to their location. For decoupling on the 3.3 V rail, 6.3 V or 10 V capacitors are adequate, though you could choose 16 V parts for extra margin with minimal cost increase. For input capacitors on the buck regulator and on the 12 V rail, choose 25 V or 35 V X7R capacitors, with values between 4.7 µF and 47 µF depending on the location. Again, selecting from the JLC basic library will ensure low cost and high availability.

Indicator LEDs can be standard 0603 devices in green or blue, with forward voltages around 2–3 V. Use moderate series resistors to avoid excessive brightness and power draw. The exact MPN is less important than ensuring that the part is available and basic; many generic LEDs are available at LCSC.

---

## Assembly Strategy: Machine‑Placed vs Manual Components

### Criteria for Delegating Parts to PCBA Vendor

In a low‑volume context, your primary criteria for selecting which components should be assembled by the PCBA vendor are soldering complexity, rework difficulty, and the impact of placement errors on board functionality. Fine‑pitch ICs, small passives, and components that are difficult to rework or replace should almost always be assembled by the vendor. In contrast, large connectors, mechanical switches, and optional features can be hand‑soldered if needed.

For this board, the ESP32‑S3‑WROOM module, buck regulator IC, LIN transceivers, USB‑C connector, ESD arrays, MOSFETs, TVS diodes, resettable fuses, and most passives belong firmly in the machine‑placed category. Their proper alignment and soldering are critical to both function and reliability, and reworking them by hand repeatedly would be time‑consuming and error‑prone.

Slide switches, large through‑hole connectors, and possibly some jumpers or LEDs can be left for manual assembly, especially if you might change their exact models or mechanical positions after initial testing. Additionally, if your PCBA vendor charges extra for mounting large or unusual connectors that you might want to tweak later, it can be more economical to install them yourself.

### Components Recommended for PCBA Assembly

The following categories should be assembled by the PCBA vendor in both low‑cost and robust paths:

All ICs: This includes the ESP32‑S3‑WROOM‑1U‑N8R8 module, the dual NXP TJA1021T/20/C LIN transceivers, the chosen buck regulator IC, any USB transceiver or PHY if used, and any optional logic devices. These are critical and often fine‑pitch components.

All diodes and MOSFETs: Reverse polarity P‑channel MOSFETs, TVS diodes on the 12 V rail, ESD arrays on USB and LIN lines, and any other protective devices should be machine‑placed. Their solder joints must withstand thermal and mechanical stress, and they are not trivial to rework in volume.

All resettable fuses and inductors: Polyfuses and inductors are often somewhat larger but still best placed by machine to ensure correct alignment and reliable solder fillets.

All small passives: Resistors, capacitors, and small signal diodes should all be machine‑placed. Although they are easy to hand‑solder individually, the sheer number of passives makes manual placement uneconomical and increases the risk of errors.

USB‑C connector: Despite being a mechanically stressed component, the USB‑C connector’s fine‑pitch pins are much better handled by reflow than by hand soldering for most users. You can reinforce the mechanical tabs with additional solder manually after assembly if needed.

If you include any optional status LEDs or pushbuttons that are SMD, they should also be included in the PCBA to avoid manual placement complexity.

### Components Suitable for Manual or Secondary Installation

Certain components are candidates for manual installation because they are fewer in number, mechanically distinct, or likely to be revised between early prototypes and later units:

Steering‑wheel harness connectors: If you use specific automotive connectors that are not stocked by JLCPCB or LCSC, you may want to purchase them separately and hand‑solder them, especially if they are through‑hole. This also allows you to experiment with different connector orientations or mounting methods without respinning the PCB.

Slide switch for LIN arm gate: The slide switch is a relatively large mechanical component that can be soldered manually with ease. If you are not fully committed to its exact position or orientation, leaving it off the PCBA BOM for Rev A and installing it by hand gives you flexibility. However, if your PCBA vendor offers a suitable surface‑mount slide switch as a basic part, you may include it in the assembly to simplify production.

Mounting hardware and test connectors: Any optional pin headers, test connectors, or mounting hardware such as standoffs are typically installed manually. They often use through‑hole technology and may be adjusted or swapped after initial testing.

Fiducials do not require assembly, as they are just copper pads. Any board labels or stickers are also applied after assembly.

In summary, the PCBA vendor should handle all active and passive electronics and any fine‑pitch connectors, while you can reserve the relatively small number of mechanical connectors and switches for manual installation if that simplifies logistics or allows last‑minute design changes.

---

## Cost Estimates and Main Cost Drivers at 10 and 100 Units

### BOM Cost Characterization

Without real‑time pricing data, cost estimates must be expressed in bands and relative terms, but you can still derive useful approximations based on typical LCSC and Chinese PCBA pricing. At 10 units, per‑board BOM costs are dominated by the ESP32‑S3 module, LIN transceivers, and the buck regulator, with smaller contributions from ESD and TVS devices, connectors, and passives. At 100 units, volume discounts on components and amortization of setup costs lead to lower per‑board costs, but the relative proportions remain similar.

The ESP32‑S3‑WROOM‑1U‑N8R8 module is likely the single most expensive line item on the BOM. In small quantities, it may cost in the range of several dollars per unit at LCSC, potentially more if imported via Western distributors. The NXP TJA1021T/20/C LIN transceivers are also nontrivial, each costing perhaps a dollar or more depending on sourcing. The buck regulator IC is moderately priced, especially if you use a generic MPS‑style device in a basic library slot.

TVS diodes, MOSFETs, polyfuses, ESD arrays, and slide switches are individually inexpensive, often only tens of cents each, but collectively they can add a couple of dollars to the BOM. The USB‑C connector, despite being a somewhat complex part, is surprisingly affordable in Chinese ecosystems and typically costs well under a dollar even at low volumes.

Passives such as resistors, capacitors, and inductors collectively add a small fraction to the BOM cost per board, especially if you standardize on generic 0603 components. The inductor for the buck regulator might be a bit more expensive, but still under a dollar.

In a low‑cost configuration, you might target a raw BOM (excluding PCB and assembly) in the range of perhaps 10–15 USD per board at 10 units, with the ESP32 and LIN transceivers accounting for half to two‑thirds of that. The robust path, with upgraded TVS and possibly an automotive‑grade buck regulator, might add a couple of dollars per board.

### Assembly Cost Components and Scaling

Assembly costs at JLCPCB, PCBWay, and similar vendors typically comprise a setup fee, a per‑component placement fee, and sometimes additional charges for extended parts or complex components. At 10 units, the setup fee is significant relative to the unit cost; by 100 units, the setup cost is amortized across more boards, reducing the effective per‑board assembly cost.

For example, a typical PCB assembly order might have a base setup fee of around 15–30 USD, plus a per‑solder joint fee on the order of a fraction of a cent to a few cents depending on the vendor and service tier. At 10 units with perhaps 100–150 components per board (counting passives and integrated circuits), the per‑board assembly cost might land in the 10–20 USD range, including the share of the setup fee. At 100 units, the per‑board assembly cost could drop to the 5–10 USD range, as the setup cost per board is much lower and some vendors offer discounts for higher quantities.

The main cost drivers on the assembly side are the number of unique component types and the total number of placements. Each unique component may require a separate reel or feeder, and if you use a lot of exotic or “extended” components, the vendor may charge extra sourcing and handling fees. Therefore, consolidating component values and using common footprints is not only helpful for supply but also for reducing assembly complexity.

### Estimated Cost Bands for 10 and 100 Units

Combining BOM and assembly cost estimates, you can define broad cost bands per board.

For 10 units in the low‑cost path, consider a BOM of around 12–18 USD per board and an assembly plus PCB fabrication cost of around 12–20 USD per board, leading to an approximate total of 24–38 USD per board. The lower end corresponds to aggressive component sourcing and a lean assembly service; the upper end reflects more conservative pricing and some complexity overhead, especially if you have multiple extended components.

For 100 units in the low‑cost path, BOM costs might drop slightly due to volume pricing, perhaps into the 10–15 USD range per board, while assembly costs per board might drop into the 6–12 USD range, depending on the vendor. This suggests a total per‑board cost in the 16–27 USD range, again excluding harness and external cables.

For the robust path, BOM costs will increase due to automotive‑grade TVS diodes, possibly more expensive buck regulators, and any additional filtering components. This might add 2–5 USD per board, depending on your choices. Assembly cost differences are modest, as the placement complexity does not substantially change. At 10 units, a robust board might therefore cost 28–43 USD per board; at 100 units, 18–32 USD per board.

These ranges acknowledge that without current pricing data, precision is limited, but they illustrate that the ESP32 module and LIN transceivers dominate cost, followed by assembly overhead. The incremental cost of robust protection is relatively modest, and you can choose to adopt a hybrid strategy where you use robust components in the highest‑risk positions (such as the 12 V TVS and buck regulator) while retaining low‑cost choices for less critical parts.

---

## Low‑Cost vs Robust Path: Where Spending More is Worthwhile

### Defining the Low‑Cost Path

The low‑cost Rev A path can be described as follows. You use a general‑purpose 1 A, 36 V buck regulator such as an MP2459‑class IC to generate 3.3 V from the protected 12 V rail. You use a common SMBJ24A or SMBJ26A TVS diode on the 12 V input, combined with a P‑channel MOSFET for reverse polarity protection and a standard polyfuse with about 0.75 A hold current. For LIN ESD, you use general single‑line TVS diodes or generic ESD diodes rated for about 24 V, not necessarily automotive‑qualified. USB ESD protection is provided by a mainstream USBLC6‑class array.

The USB‑C connector is a standard TYPE‑C‑31‑M‑12 or equivalent, and the slide switch for the LIN arm gate is a generic surface‑mount mini slide switch. Passives are standard 0603 resistors and capacitors from JLC’s basic library. This configuration emphasizes simplicity, widespread availability, and low per‑board cost.

Such a board is perfectly adequate for bench testing, firmware development, and initial vehicle trials in relatively controlled conditions. It will handle typical 12 V operation, modest transients, and normal user interactions. It may not survive extreme load dump events or deliberate abuse, but that is acceptable for an early design deployed under your control.

### Defining the More Robust Path

The more robust path selectively upgrades components where failure would be most consequential or likely. On the 12 V front‑end, you might replace the SMBJ24A TVS with a higher‑power SM8S33A‑class automotive TVS diode, which has a much higher surge energy rating and is specifically designed for automotive load dump protection. You also might choose an automotive‑grade AEC‑Q100 buck regulator that can handle up to 40–60 V input, so that even if the TVS diode allows some higher voltage spikes, the regulator remains within its limits.

For LIN ESD protection, you would use a specific LIN ESD diode such as PESD1LIN or similar, ideally with AEC‑Q101 qualification. These devices offer better clamping performance and are tested for repeated ESD events on automotive bus lines.

While you may retain the P‑channel MOSFET for reverse polarity protection, you might choose a MOSFET with higher voltage rating or automotive qualification. The polyfuse could be replaced or supplemented by a conventional fuse for a more deterministic failure mode if you are worried about latent damage after a fault.

On the USB side, you might upgrade to a low‑capacitance ESD array with documented USB 2.0 high‑speed performance and strong ESD ratings, though most mainstream USB ESD device choices are already adequate.

### Where the Robust Path Justifies the Cost

The primary areas where the robust path is worth the additional cost and complexity are those where a failure could conceivably compromise safety or disable the car in a difficult‑to‑recover way. The 12 V front‑end is the obvious candidate. A failure of the TVS diode or buck regulator that shorts the 12 V rail could blow fuses in the vehicle system or cause other unpleasant failures. A regulator that fails open might simply shut down your board, which is less catastrophic. However, a TVS diode that fails short due to a load dump event is undesirable if it then permanently drags down the 12 V line feeding the steering wheel module.

By choosing an automotive‑grade TVS with higher surge tolerance and a regulator that can handle higher input voltages, you significantly reduce the chance that a transient will cause such a failure. The incremental cost of a better TVS diode and an automotive‑grade buck IC is small relative to the cost of the board and the value of your time and vehicle.

LIN ESD protection is also a reasonable place to spend a little more. While a failed LIN ESD diode is unlikely to be catastrophic, a board that repeatedly fails due to ESD events on the steering‑wheel harness will be frustrating and may be unsafe if your device plays a critical role in some future configuration. Using a dedicated LIN ESD diode improves the board’s resilience to real‑world ESD, which can be substantial in the dry interior of a vehicle.

In contrast, upgrading the slide switch or selecting boutique passives offers minimal benefit for cost. A mid‑range slide switch is already robust enough for occasional operation, and 0603 passives from mainstream suppliers are typically reliable even without automotive qualification. USB ESD and connector upgrades are not as critical, because a failure of the USB interface is primarily an inconvenience rather than a safety issue.

Therefore, a hybrid strategy is recommended: adopt a robust TVS diode and, if possible, an automotive‑grade buck regulator while keeping the rest of the design low‑cost. This combination will greatly improve the board’s survivability in real vehicle conditions while keeping the BOM and assembly costs within reasonable bounds.

---

## Risks and Validation Gates Before Ordering 10 Units

### Electrical and Layout Risks

Before committing to a 10‑unit build, you should recognize and address several key risks in the electrical design and layout.

One risk is insufficient transient protection on the 12 V front‑end. If the TVS diode selection, layout, or buck regulator input rating is marginal, a real‑world transient could damage the board. This risk can be mitigated by conservatively selecting TVS and regulator components and by simulating or at least benchmarking the input behavior on a bench supply that can emulate transients. While full transient simulation is challenging without specialized tools, you can perform step‑input tests and observe the behavior of the 3.3 V rail and the current draw.

Another risk is inadequate decoupling and poor ground layout leading to ESP32 instability, resets, or RF performance degradation. Verify that the decoupling capacitors are properly placed, that the ground plane is continuous under the module, and that the buck’s switching loop is compact and away from sensitive circuits. Reviewing the PCB with a focus on current return paths and minimizing loop areas is an essential validation step.

On the LIN side, signal integrity and ESD protection must be checked. Ensure that the series resistors, ESD diodes, and LIN transceivers are connected exactly as per the datasheet guidelines, and that the LIN traces are routed with appropriate spacing from noisy nodes. If you have access to a LIN bus analyzer or scope, plan to probe the bus in a test setup to confirm that the waveforms are clean and that the board does not introduce significant loading.

The USB‑C interface carries its own risks, particularly with respect to ESD and the potential for mis‑wiring the CC pins. Misconfiguring CC can lead to negotiation issues with hosts or to improper current draw. Validate that your CC resistor network matches a device‑only configuration and test with multiple host devices.

### Mechanical and Harness Integration Risks

Mechanically, the board must fit into the available space in the steering‑wheel area and connect to the harness without undue stress. Board outline, connector placement, and mounting hole positions should be reviewed against physical measurements or CAD models of the target installation environment. If possible, print a 1:1 paper or 3D‑printed mock‑up of the PCB and test‑fit it in the steering‑wheel area before ordering the first PCBs.

The harness integration is another source of risk. You need to confirm the pinout, wire colors, and physical connectors used in the Tesla Model 3/Y steering‑wheel harness. Mistakes here can lead to mis‑wired LIN lines, power feeds, or ground connections. A thorough reverse‑engineering or consultation of available documentation is necessary to ensure that the board’s connectors match the vehicle’s harness.

Additionally, consider strain relief and cable routing. If the USB‑C connector will be used in situ, ensure that plugging and unplugging a cable does not exert excessive force on the PCB or other connectors. In some cases, using a short pigtail cable to a panel‑mount USB‑C connector can offload mechanical strain from the board.

### Firmware and Functional Validation Gates

Even though the question focuses on hardware and BOM, firmware plays a critical role in validating the hardware. Before building 10 units, you should have a minimal firmware that exercises the major features: LIN communication on both channels, USB communication, and basic diagnostics. This firmware should be used on a first‑article prototype (for example, a hand‑assembled board or an initial 1–2 board PCBA run) to verify that the design is fundamentally sound.

Testing should include:

Power‑up behavior: Confirm that the board powers up cleanly from the automotive 12 V rail, that the 3.3 V rail comes up as expected, and that the ESP32 boots reliably. Monitor inrush current and observe the 12 V rail’s behavior.

LIN communication: Use a bench LIN master or a simulator to exercise the LIN transceivers, check that they transmit and receive correctly, and that bus waveforms are clean. Test both LIN channels independently and simultaneously.

USB interface: Connect the USB‑C port to a host and verify that the board enumerates correctly if using USB, or at least that serial communication works as expected. Test ESD behavior if possible, using an ESD gun or at least static discharge from human interaction in a controlled manner.

LIN arm gate: Confirm that the slide switch or other mechanism correctly enables and disables the LIN transceivers or bypass function. Test failure modes: for example, what happens if the board loses power while the gate is in the “armed” position.

### First‑Article and Design Review Before 10‑Unit Run

Before ordering a 10‑unit run, consider a staged approach: order 2–3 boards initially, either fully assembled or with partial assembly, and use them to validate the design. This approach allows you to identify issues in assembly, layout, or component selection without committing to a larger volume.

In parallel, conduct a design review with a focus on:

Schematic correctness: Verify each net, especially power, ground, and LIN connections. Check that the ESP32’s boot and reset circuitry is correct and that the USB‑C and LIN interfaces match datasheet recommendations.

Layout quality: Examine critical areas like the buck regulator, ESP32 module, LIN transceivers, and USB‑C connector. Check for adequate clearances, trace widths, and via placement.

DFM and DFT: Ensure that the board meets the PCBA vendor’s design rules, including minimum trace widths, clearances, and solder mask openings. Check that test pads are accessible and that fiducials are correctly placed.

Only after these reviews and first‑article tests should you order the 10‑unit batch. For the final 100‑unit run, you can apply any design tweaks learned from the 10‑unit experience.

---

## Conclusion

Designing a low‑volume, dual‑LIN ESP32‑S3 steering‑wheel inline board for Tesla Model 3/Y applications requires a nuanced balance between automotive‑style robustness and the pragmatic constraints of small‑batch manufacturing through services like JLCPCB, LCSC, and PCBWay. The locked core choices—the ESP32‑S3‑WROOM‑1U‑N8R8 module, dual NXP TJA1021T/20/C LIN transceivers, USB‑C service, and a 12 V automotive input feeding a 3.3 V rail of at least 500 mA—define the heart of the system. Around this core, the design must provide credible protection against the automotive electrical environment, manageable assembly and test strategies, and cost‑efficient component selections.

For the 12 V input front‑end, a practical low‑cost Rev A design uses a P‑channel MOSFET‑based reverse polarity protector, a 0.5–0.75 A hold resettable polyfuse, and an SMBJ24A‑class TVS diode, followed by a simple LC or ferrite bead plus capacitor filter feeding a general‑purpose MP2459‑class buck regulator that generates 3.3 V. This configuration is straightforward to implement with components widely available from LCSC and in JLC basic libraries, keeping both BOM and assembly costs modest. The 3.3 V rail, properly decoupled and laid out, can easily meet the current and noise requirements of the ESP32 module.

On the USB‑C service side, a standard TYPE‑C‑31‑M‑12‑style connector and a USBLC6‑class ESD array provide a robust, low‑cost interface for development and diagnostics. Simple Rd resistors on the CC pins configure the board as a device‑only sink, avoiding the complexity of full USB‑C power delivery. The LIN interface, built around the fixed NXP TJA1021T/20/C transceivers, benefits from modest series resistors, generic 24 V ESD diodes, and a physical LIN arm gate implemented as a slide‑controlled enable line, yielding a functional yet uncomplicated dual‑LIN interface.

For a more robust path, selectively upgrading key components is justified. An automotive‑grade TVS diode with higher surge power rating, possibly combined with an AEC‑Q100‑qualified buck regulator that tolerates higher input voltages, significantly improves resilience to load dump and severe transients. Dedicated LIN ESD diodes such as PESD1LIN‑class devices offer better protection on the LIN lines. These upgrades raise BOM costs slightly but provide meaningful gains in reliability and safety for real‑world deployments.

Assembly strategy divides components between those that should be machine‑placed—everything fine‑pitch, including the ESP32 module, LIN transceivers, regulators, protection devices, and small passives—and those suitable for manual installation, such as harness connectors, slide switches, and mounting hardware. At 10 units, per‑board BOM plus assembly costs for the low‑cost path fall in an approximate band of 24–38 USD, decreasing somewhat at 100 units. The robust path adds only a few dollars per board in most cases, making it a reasonable option if you anticipate harsh conditions or long‑term use.

Key risks before ordering a 10‑unit batch include under‑designed 12 V transient protection, inadequate decoupling or layout leading to ESP32 instability, LIN signal integrity challenges, USB‑C ESD and CC configuration mistakes, and mechanical misfits with the steering‑wheel harness environment. Mitigating these risks requires careful schematic and layout review, bench testing of first‑article prototypes with representative power and LIN bus conditions, and basic firmware exercising all critical paths. A staged approach—building one or a few boards before the 10‑unit run—allows you to validate assumptions and correct issues early.

Within these constraints and strategies, the proposed Rev A BOM and design approach offer a practical and affordable path to a dual‑LIN ESP32‑S3 steering‑wheel inline board, optimized for low‑volume PCBA on contemporary Chinese manufacturing platforms. The design is robust enough for serious prototyping and controlled vehicle trials, while leaving clear, well‑understood upgrade paths for future revisions that might aim for wider deployment, stricter automotive compliance, or additional functionality.
