lakewoodphone/tesla-lin-chip/research/responses/2026-05-29-tesla-lin-chip-sourcing-board-architecture.md

---
job_id: 3a9fef16-701c-48d4-85b8-bf9395a7cca7
directive_id: tesla-lin-bench-only-ble-passthrough-chip-sourcing-and-board-architecture
title: Tesla LIN bench-only BLE passthrough chip sourcing and board architecture
domain: automotive_re
sensitivity: no_refusal_required
model_used: sonar-deep-research
provider: perplexity
status: complete
completed_at: 2026-05-29T09:26:55.023803+00:00
cost_usd: 0.59776
input_tokens: 1060
output_tokens: 15612
reasoning_tokens: 67419
search_count: 48
citation_count: 45
verifier_status: passed
schema_version: 1
---

# Design of a Bench‑Only Bluetooth‑Controlled LIN Steering‑Wheel Research Module for Tesla Model 3/Y

The following report develops a complete architectural and component‑level proposal for a bench‑only Local Interconnect Network (LIN) research fixture targeted at the Tesla Model 3/Y steering‑wheel scroll wheels. The system must remain safe and non‑deployable in on‑road use, while providing sophisticated capabilities: passive capture, dual‑transceiver passthrough/proxy, and controlled active gesture emulation over LIN for left and right scroll wheels, with configuration and firmware update via Bluetooth Low Energy (BLE). Building on an existing Seeed XIAO ESP32‑C3 prototype, the report evaluates suitable microcontroller and system‑on‑chip (SoC) families, automotive‑style LIN transceivers, power and protection circuitry for 12 V bench/vehicle‑adjacent environments, and secure provisioning and over‑the‑air (OTA) update architectures. It compares key candidates from Espressif, Nordic Semiconductor, STMicroelectronics, and others with respect to BLE capability, UART/LIN support, secure boot and DFU, ecosystem maturity, and sourcing. It also identifies practical LIN transceivers from NXP, Microchip, Texas Instruments, Infineon, and ST that are widely available through Digi‑Key, Mouser, LCSC, and JLCPCB, highlighting features such as sleep modes, dominant timeout, integrated regulators, ESD robustness, and 3.3 V logic compatibility. The report then proposes a robust power and protection strategy for 12 V input, including buck conversion, reverse‑polarity protection, fusing or resettable PTCs, transient voltage suppressors (TVS), ESD protection, and LIN‑side safeguards. Secure BLE provisioning and update flows are mapped for the leading MCU families, integrating secure boot, firmware authentication and optional encryption, BLE bonding, VIN/test‑fixture binding, physical arming, serial recovery, and factory reset pathways. Finally, the report presents a sourcing shortlist with indicative availability and packaging considerations, identifies important pitfalls specific to ESP32‑C3 when running dual LIN channels and BLE simultaneously, and concludes with a concise board‑level architecture recommendation and a phased development plan that moves from dev‑board prototypes through prototype PCBs and safety validation to a locked bench‑only release.

## 1. System Context, Use‑Case, and Requirements

### 1.1 Application context and mode structure

The target system is a hardware module that sits between the Tesla Model 3/Y steering wheel’s LIN‑attached scroll‑wheel module and the vehicle’s steering‑column or body control unit (which acts as the LIN master). It is explicitly for bench‑only, non‑road use. The system must support three operational modes that reflect the research workflow while enforcing strong safety constraints.

In passive capture mode, the device connects to the existing LIN bus in a sniffer‑like configuration, listening without driving the bus and recording traffic for later analysis. In this mode, only one LIN transceiver is strictly necessary from a signal perspective, but the physical design should already anticipate dual‑transceiver passthrough to avoid future re‑spins when moving to more advanced capabilities. Passive capture is the safest starting mode because it cannot interfere with the vehicle network and can be used even in an in‑vehicle bench test environment, provided the vehicle is stationary.

In dual‑transceiver passthrough or proxy mode, the device is inserted inline between the car‑side master and the wheel‑side slave. Two LIN transceivers are used: one on the car‑side segment and one on the wheel‑side segment. The module must respond to headers from the car‑side master immediately from cached or injected frames while it polls, caches, and optionally manipulates or substitutes responses from the wheel‑side module. This architecture allows controlled interception and modification of the scroll‑wheel messages while preserving timing guarantees defined by the LIN protocol, including the need to react quickly to the master’s header and the maximum frame latency constraints.[42][45]

In controlled active mocking mode, the system deliberately generates LIN responses that emulate scroll‑wheel gestures for left and right wheels. For the Tesla Model 3 left scroll wheel, you have already confirmed raw ID 0x2A (PID 0x6A) with seven data bytes using the enhanced checksum, where byte 0 encodes scroll up, scroll down, idle, and click states, and bytes 5 and 6 form a rolling counter/tail field with a known mapping.[42] For the right wheel, raw ID 0x2B and six data bytes are known, but the counter model remains incomplete. In active mocking mode, the module must only generate messages within known‑good patterns and under strict safety gates: default inactive, physical arming required, BLE or USB authorization, limited session duration (e.g., 300 s as in the prototype), rate limiting of gesture injection, and guarding on bus idle and error conditions.

### 1.2 LIN protocol characteristics relevant to this design

LIN is a low‑cost, single‑wire, master‑slave bus primarily used in automotive body and comfort systems.[42][45] It operates over a single wire referenced to ground and is biased to battery voltage (approximately 12 V) via pull‑ups at the master node, with typical baud rates from 1 kBd up to 20 kBd.[4][5][24][25][28][45] Many LIN transceivers support data rates up to 20 kbaud for standard traffic and sometimes higher for in‑line programming or debug modes.[4][5][24][28]

A LIN frame consists of a header and a response. The header is always sent by the master and includes a break field (13 dominant bits followed by a recessive delimiter), a sync field, and a protected identifier byte that combines six ID bits with two parity bits.[42] The response section (data and checksum) is sent either by the master (if it owns the addressed slave task) or by a slave. The enhanced checksum defined in LIN 2.0 and later specifications is computed by summing the data bytes and the protected ID, with a modulo‑255 minus one style handling for overflow.[42] In your Tesla use‑case, the left scroll wheel message uses the enhanced checksum, aligning with LIN 2.x behavior.

The master controls the schedule by periodically emitting headers with specific IDs, each of which has an allocated time slot with nominal and maximum frame times derived from the bit rate.[42] For 19,200 baud (the specified bus speed in your fixture), timing will be faster than the canonical 19.2 kBd examples, but it remains well within the capabilities of typical MCU UART peripherals. The critical implication is that a proxy device running in passthrough mode must be able to detect the break/sync/ID on the car‑side segment and produce a valid response on either side with minimal added latency. That requirement drives the choice of LIN transceivers (which must detect and drive at 19.2 kBd and withstand automotive‑like voltages and ESD) and the microcontroller’s UART performance and interrupt latency.[13][18][42][45]

### 1.3 Existing prototype constraints and implications

The current prototype uses a Seeed XIAO ESP32‑C3 board with Arduino/PlatformIO firmware. The ESP32‑C3 is a Wi‑Fi plus BLE‑capable RISC‑V MCU with two UARTs, of which UART0 is often used for USB serial and UART1 is available for peripherals.[1][13][39] On the XIAO ESP32‑C3 specifically, the second UART is available on pins that can be remapped via GPIO matrix and used for LIN through an external LIN transceiver. For a dual‑transceiver passthrough design, two UART instances (or one UART plus a tightly timed bit‑banged implementation) are needed, and the C3 can be constrained because UART0 is shared with USB debug and bootloader functions.[13][39] This is an early indicator that future hardware should either expose both UARTs cleanly or consider an MCU with more UARTs or more flexible minus‑interference mapping.

The existing firmware uses NimBLE on ESP32‑C3 for BLE configuration, non‑volatile storage (NVS) for settings, and several safety controls: arming gates, 300 s session limits, fault lockout, rate limiting, and bus‑idle guards, with active output disabled at boot. These are strong design choices that should be preserved across architectures. NimBLE on ESP32 supports bonding and persistent storage of keys, and ESP‑IDF includes flash encryption and secure boot options, although careful configuration is needed to make these work seamlessly with OTA update flows.[8][13][17][43] Working within this ecosystem is feasible, but an evaluation of Nordic nRF52/nRF53 and STM32WB is warranted for better integrated BLE stacks and out‑of‑the‑box secure DFU support.[2][9][10][12][16][27][29][40]

The desired next product direction is a custom chip/board that remains Bluetooth‑controllable and updatable and supports passive, passthrough, and active modes, while adding VIN or test‑fixture binding and strong bench‑only safety barriers so it is difficult to deploy in a road‑going vehicle. These requirements constrain both hardware and firmware: the MCU must have a mature Bluetooth stack, proven secure OTA capability, at least two UARTs for LIN channels, and enough flash and RAM to support a secure bootloader, application, and debugging instrumentation.

### 1.4 Safety scope and constraints

Safety constraints for this project are not optional; they are the primary boundary conditions. The device is for bench‑only use and must be designed so that using it in a moving vehicle is both technically inconvenient and explicitly discouraged. The architecture should default to a passive, non‑driving state whenever powered, including after reset, firmware update, or configuration changes. Transition into active injection or passthrough modes must require both physical and logical authorization, such as a physical “arm” switch or jumper, and BLE or USB‑initiated enabling under an authenticated session.

Session lifetimes should be limited (e.g., 300 s) with automatic reversion to passive mode, and rate limiting should prevent high‑frequency gesture injection or flooding of the bus. It is also advisable to require a VIN or test‑fixture identity binding for active modes. Rather than functioning as digital rights management, VIN binding in this context is a safety guardrail to ensure that a fixture is explicitly paired with specific non‑road hardware (for example, a dismounted steering column or a lab car in a secure test environment). The design must also consider built‑in fault lockout, error status indication, and easy factory reset to a passive, safe state, while avoiding any guidance or features that would facilitate bypassing vehicle safety systems in actual road operation.

Within this context, the remainder of the report analyzes concrete MCU candidates, LIN transceivers, power and protection schemes, BLE security and provisioning patterns, sourcing, and an incremental development plan.

## 2. MCU and SoC Platform Evaluation

### 2.1 Evaluation criteria

To choose an MCU or SoC for the custom board, several criteria are most important for this application. The device must support robust BLE with a mature stack and long‑term maintenance prospects, ideally including BLE 5.x features such as secure connections, bonding, and extended advertising.[2][9][10][38][40] It must offer at least two independent UARTs (or USARTs that can operate in LIN‑like UART mode), with flexible pin maps and enough performance to handle 19.2 kBd LIN traffic on both channels concurrently while managing BLE and application‑level tasks.[13][18][27]

Security features are central. Secure boot and signed firmware enforcement are highly desirable to ensure only authorized code runs on the board, along with secure OTA mechanisms: this can be ESP‑IDF’s secure boot plus encrypted flash, Nordic’s nRF Secure DFU, or ST’s Secure Boot and Secure Firmware Update (SBSFU and MCUboot‑based solutions).[8][12][16][29][40] These must be practical to configure and maintain in a small development team context.

Ecosystem and tooling also matter. Mature SDKs, good debugging and logging tools, and ready‑made dev kits accelerate the development phases, especially for a security‑sensitive product. Finally, availability and packaging are critical: QFN or similar surface‑mount packages that JLCPCB or other assemblers handle routinely, and parts that distributors like Digi‑Key, Mouser, and LCSC stock at reasonable prices.

The following subsections examine Espressif ESP32‑C3/C6/S3, Nordic nRF52840 and nRF5340, ST STM32WB, and other alternatives such as newer Nordic nRF54L15 or NXP crossover MCUs.[1][2][9][10][27][34][38][40]

### 2.2 Espressif ESP32 family: C3, C6, and S3

The ESP32 family has become a de facto standard in hobbyist and many professional IoT products due to its integration of Wi‑Fi and BLE, good performance, and extensive tooling. Espressif’s official ESP‑IDF provides secure boot, flash encryption, OTA update libraries, and NimBLE‑based Bluetooth stacks. In your prototype, an ESP32‑C3 is already in use, so it is a natural baseline.

The ESP32‑C3 is a RISC‑V single‑core MCU with Wi‑Fi and BLE 5 support, operating up to 160 MHz with about 400 kB of SRAM and 4 MB of onboard flash on typical modules.[1][13] It has two UART controllers, UART0 and UART1, which share identical register sets and can be flexibly mapped to GPIO pins through the internal matrix.[13][39] This is adequate for two LIN channels, but the usual practice is to use UART0 for serial console and programming. For a production board, it is possible to allocate UART0 to one LIN channel and UART1 to the other, while providing USB‑to‑UART bridging only when needed, or accessing debug through a different interface. However, this design choice introduces trade‑offs between debugging convenience and LIN channel robustness.

The ESP32‑C3 supports both Wi‑Fi and BLE simultaneously, but it is less resource‑rich than its larger cousins. Power draw at peak transmit is around 382 mA for the ESP32‑C6, while the ESP32‑C3 is in a similar, slightly lower class; typical Wi‑Fi plus BLE operation is well within what a 12 V bench supply and buck converter can handle.[1] For this application, Wi‑Fi is not strictly necessary and may even be undesirable from a security perspective, since BLE provides sufficient bandwidth for configuration and OTA, and a wired USB connection can be used for development. Power consumption is therefore no barrier.

The ESP32‑C6 is an updated RISC‑V device that adds 802.11ax (Wi‑Fi 6) and Bluetooth 5 LE, along with Zigbee and Thread support, operating up to 160 MHz and maintaining a similar resource profile.[1] It also supports two UART controllers and similar peripheral sets, with improved radio coexistence and additional security features. For a product that might later need IP connectivity, the C6 is attractive, but for a bench‑only LIN fixture, the extra connectivity may not justify the development complexity and potential security surface.

The ESP32‑S3 is closer to the original ESP32 but with enhanced AI and vector instructions and a dual‑core Xtensa LX7 CPU running up to 240 MHz.[1] It supports 802.11b/g/n Wi‑Fi and Bluetooth 5 LE, and it embeds substantial SRAM and flash on many modules. Importantly for your use case, the S3 exposes a richer set of peripherals: multiple UARTs, camera and LCD interfaces, and more advanced DMA and GDMA features.[1] Its BLE stack is similar to the C3’s, but the dual‑core architecture and larger memory footprint give you more headroom to run BLE, LIN decode, secure boot, and OTA tasks concurrently without tight timing compromises. From a hardware design perspective, S3 modules are more common and widely supported by assemblers.

ESP32 devices support secure boot and flash encryption in hardware, and ESP‑IDF’s app_update component provides OTA functionality that can be hardened with signed firmware images.[8] However, forum discussions highlight nuances when using OTA with encrypted flash, especially when using Arduino‑level abstractions that bypass the app_update component.[8] For a productized design, the firmware stack should be based directly on ESP‑IDF rather than Arduino, to ensure full control over secure boot, encrypted OTA partitions, and the bootloader.

In summary, Espressif devices are attractive due to their integrated BLE, UART flexibility, secure boot support, and strong tooling, but the ESP32‑C3’s two‑UART limitation and shared USB console create constraints for dual LIN plus debug. The ESP32‑S3 stands out as a better candidate within the Espressif family because of its extra cores, more peripherals, and similar BLE capabilities, with the caveat that it brings Wi‑Fi whether it is used or not.[1]

### 2.3 Nordic Semiconductor: nRF52840 and nRF5340

Nordic’s nRF52 and nRF53 series are widely regarded as BLE‑centric MCUs with high‑quality stacks and tooling. The nRF52840 is a single‑core Arm Cortex‑M4F running at up to 64 MHz, with 1 MB flash and 256 kB RAM, integrated 2.4 GHz radio, and a rich peripheral set including multiple UARTs.[2][9][38][40] It supports Bluetooth 5, Thread, Zigbee, and proprietary 2.4 GHz modes. The nRF5340, by contrast, is a dual‑core Cortex‑M33 device, with one application core at 128 MHz and a network core at 64 MHz, and offers 1 MB flash + 512 kB RAM on the application core plus additional memory on the network core.[40] It supports BLE 5.4, Bluetooth mesh, Thread, Zigbee, Matter, NFC, and more, with advanced security and extended operating temperature.[40]

The nRF52840’s UART peripheral supports typical serial speeds and can be used to implement LIN at 19.2 kBd if paired with an external LIN transceiver that handles the 12 V physical layer.[2][42][45] It has sufficient RAM and flash to host a LIN stack, BLE configuration service, secure bootloader, and application logic. Nordic’s nRF5 SDK and, more recently, the nRF Connect SDK (NCS, based on Zephyr RTOS) include robust device firmware update (DFU) solutions, including the nRF BLE Secure Bootloader and serial DFU transports.[12][16] These DFU mechanisms implement cryptographic validation of firmware images via an init packet and signed binary data, with a multi‑step process: init packet transfer and validation, binary transfer, post‑validation, and activation on reset.[12] This gives you an out‑of‑the‑box secure OTA path for BLE‑based updates, a strong advantage over rolling your own scheme.

The nRF5340 goes further by partitioning BLE and radio processing onto the network core, freeing the application core for LIN and control logic. It supports advanced Bluetooth features, including direction finding and advertising extensions, and is explicitly designed to run concurrent mesh plus BLE plus other protocols.[40] The nRF5340 Development Kit showcases its capabilities and includes standard Arduino‑style headers, J‑Link debugger, and comprehensive examples, including samples for low‑power UART (LPUART) and secure services that rely on Trusted Firmware‑M.[27][40] This strongly suggests that an nRF5340‑based design can handle two full LIN channels and BLE concurrently with comfortable margins.

Nordic has introduced the nRF54L15 as a new generation SoC built on a 22 nm process, doubling clock speed to 128 MHz, with 1.5 MB memory, enhanced radio (including Bluetooth 6.0 features and 4 Mbps proprietary mode), improved energy efficiency, and a dedicated RISC‑V processor for time‑critical tasks.[9] It includes advanced security (TrustZone isolation, a hardened crypto engine, tamper detectors) and a global RTC usable even in deep system OFF modes.[9] While this device looks ideal for long‑term IoT and very low‑power applications, its ecosystem and mass availability are still maturing compared to the nRF52840 and nRF5340. For a 2026‑era product with relatively modest power constraints and a focus on bench fixtures, the nRF52840 and nRF5340 remain safer choices in terms of tooling maturity and volume availability.

For secure boot and OTA, Nordic’s Secure DFU design is a strong differentiator. The standard DFU controller/target model and init packet format, with signed images, allow strong assurances that only authorized firmware is installed.[12][16] Nordic’s DevZone discussions emphasize choosing the right DFU path going forward, but BLE‑based DFU for nRF52840 and nRF5340 remains a core supported feature.[16] This fits directly with your requirement for Bluetooth‑controllable and updatable hardware and simplifies implementing VIN/test‑fixture binding logic within a secure bootloader environment.

In summary, if Wi‑Fi is unnecessary and BLE‑centric security and OTA are paramount, Nordic’s nRF52840 and especially the nRF5340 are compelling. They provide multiple UARTs, strong BLE stacks, mature DFU mechanisms, and advanced security features that align with your bench‑only safety requirements.

### 2.4 STMicroelectronics STM32WB and similar BLE MCUs

ST’s STM32WB family combines an Arm Cortex‑M4 application core with an integrated 2.4 GHz radio for Bluetooth 5.4 and 802.15.4 (Thread/Zigbee) support.[10][18][3][29] The STM32WB55 and STM32WB35 variants, for example, are marketed as multiprotocol wireless 32‑bit MCUs with FPU, BLE 5.4, and 802.15.4 radios.[10] They embed a radio core and a main application core; the radio core handles BLE and 802.15.4 stacks, and ST provides middleware and HAL libraries for BLE profiles and services.[3][10][18][3]

From a peripheral perspective, the STM32WB55 has several USART interfaces that support asynchronous UART, SPI master, and LIN mode.[18] The USART peripheral’s LIN mode directly targets LIN‑like communication and can handle break detection and other LIN‑related behaviors, making it particularly suitable for a dual LIN transceiver design when paired with an external LIN physical layer.[18] ST’s product training material for STM32WB USART shows that the USART can be configured for LIN mode alongside other serial modes, which is highly relevant for your 19.2 kBd LIN requirement.[18]

For BLE and security, STM32WB’s software ecosystem includes BLE middleware, and ST’s documentation and video tutorials show how to generate BLE applications and security settings via STM32CubeMX and STM32CubeIDE.[3][3] The BLE stack runs on the M0+ core, while the M4 core runs application logic. The configuration process includes enabling hardware semaphore (HSEM) and inter‑processor communication controller (IPCC), configuring RTC for the BLE stack timing requirements, enabling UART with DMA for trace/debug, and configuring BLE advertising and GATT services through middleware.[3][3] This architecture naturally supports running BLE concurrently with application tasks such as LIN handling.

For secure boot and OTA, ST offers Secure Boot and Secure Firmware Update solutions for STM32, including legacy SBSFU, SBSFU based on MCUboot, and STiRoT for devices with hardware root‑of‑trust.[29] These solutions verify firmware authenticity and integrity on boot using cryptographic signatures and can also decrypt firmware images where supported. They provide secure firmware update mechanisms over various transports (including BLE and wired serial) and integrate with ST’s HAL and middleware.[29] For an STM32WB‑based product, adopting ST’s SBSFU/MCUboot implementation would allow you to enforce signed firmware and implement secure OTA updates, including key management for VIN/test‑fixture binding logic.

The downside relative to Nordic is that the BLE and security ecosystem can be more fragmented between CubeMX‑generated code, middleware, and SBSFU packages, and the learning curve can be steeper. However, ST’s USART LIN mode is a distinct advantage for a LIN‑centric design, potentially simplifying the LIN protocol layer and timing management.[18][29]

### 2.5 Other alternatives: nRF54L15, NXP crossover MCUs, and beyond

Beyond Espressif, Nordic nRF52/nRF53, and ST STM32WB, several other families could theoretically meet your requirements. Nordic’s nRF54L15 is technically very capable, with a 22 nm process, doubled clock speed, 1.5 MB memory, 14‑bit ADC, improved radio, and advanced security features including TrustZone and a side‑channel‑resistant cryptographic engine.[9] It also integrates a RISC‑V processor for time‑critical tasks.[9] For a long‑lived product with extremely low power needs, this might be attractive, but for a bench‑only module with moderate runs and an emphasis on ecosystem maturity, the nRF54L series is still emerging, and developer experience is less widespread than for nRF52840 and nRF5340.[9]

NXP’s i.MX RT crossover MCUs combine high‑performance Cortex‑M cores with real‑time capabilities and are attractive for more complex edge devices.[34] However, they do not integrate BLE radios, so a separate BLE module and RF design would be needed, complicating the board and tooling. For a focused LIN fixture, this is overkill.

Some vendors offer automotive‑grade microcontrollers and SoCs with integrated LIN or CAN modules, but few integrate BLE radios, and designing with discrete BLE chips is significantly more complex for RF layout and certification. Given your focus on BLE control and updates and the non‑road nature of the device, staying with integrated BLE MCUs from Espressif, Nordic, or ST is the most practical path.

### 2.6 Comparative summary and primary recommendation

To clarify the trade‑offs, the following table compares the most relevant options for your design.

| Feature / Criterion | ESP32‑C3 | ESP32‑S3 | nRF52840 | nRF5340 | STM32WB55/35 |
|---|---|---|---|---|---|
| Core architecture | Single‑core RISC‑V up to 160 MHz[1][13] | Dual‑core Xtensa LX7 up to 240 MHz[1] | Cortex‑M4F 64 MHz[2][38] | Dual‑core Cortex‑M33 128/64 MHz[40] | Cortex‑M4 + M0+ radio core[10]  |
| Integrated radio | Wi‑Fi + BLE 5 LE[1][13] | Wi‑Fi + BLE 5 LE[1] | BLE 5, Thread, Zigbee[2][38] | BLE 5.4, Thread, Zigbee, Matter[40] | BLE 5.4 + 802.15.4[10] |
| UART / USART count | 2 UARTs[13][39] | Multiple UARTs (≥3)[1] | Multiple UARTs | Multiple UARTs | Multiple USARTs with LIN mode[18] |
| LIN‑centric features | UART only; software LIN needed | UART only; software LIN needed | UART only; software LIN needed | UART only; software LIN needed | Hardware USART LIN mode[18] |
| BLE secure DFU / OTA | ESP‑IDF OTA, secure boot & flash encryption; custom integration required[8][13] | Same as C3, more headroom[1][8] | nRF BLE Secure DFU, mature tooling[12][16] | nRF BLE Secure DFU on NCS; advanced security[16][40] | ST SBSFU/MCUboot + BLE middleware[10][3][29] |
| Ecosystem maturity for BLE | High (ESP‑IDF, Arduino, NimBLE)[1][13][20] | High | Very high (nRF SDK, NCS)[2][12][16][40] | Very high; NCS recommended[27][40] | High (CubeMX, CubeIDE, BLE middleware)[3][10][3] |
| Security features | Secure boot, flash encryption, partitioned OTA[8][13] | Same, extra resources | Cryptographic engine, secure boot, vetted DFU[12][16] | TrustZone, secure services, TF‑M[27][40] | Secure Boot and Secure Firmware Update packages[29] |
| Wi‑Fi presence | Yes (possibly undesired) | Yes | No | No | No |
| Typical dev kit availability | High ($10–20 boards) | High | High (nRF52840 DK)[37][38] | High (nRF5340 DK)[40] | High (Nucleo / evaluation boards)[3][3] |

For your specific application—a bench‑only LIN fixture with dual LIN channels, BLE configuration and secure OTA, and strong safety requirements—two platforms stand out.

First, the Nordic nRF5340 offers a dual‑core BLE‑centric architecture with multiple UARTs, a mature Secure DFU flow, and advanced security features.[40] It avoids Wi‑Fi, reducing the attack surface, and its ecosystem is actively maintained and documented. Secure BLE DFU is close to a drop‑in solution, and the network core offloads radio processing from the LIN‑handling application core.[12][16][27][40]

Second, the STM32WB55/35 provides integrated BLE 5.4 and 802.15.4 plus USART peripherals with hardware LIN mode, which directly supports your dual‑LIN requirement.[10][18] ST’s secure boot and firmware update packages can be combined with BLE middleware to implement signed OTA updates, and CubeMX/CubeIDE provide strong configuration tools.[3][3][29] If you prefer an MCU whose serial peripherals explicitly support LIN, STM32WB is uniquely attractive.

Between these, the choice depends on your team’s familiarity and the importance of hardware LIN mode versus BLE DFU maturity. If BLE secure DFU and BLE tooling are the top priorities, I recommend nRF5340 as the primary platform. If deep LIN integration and ST’s broader STM32 ecosystem are more important, STM32WB55 is an excellent alternative. Espressif ESP32‑S3 remains a viable option, especially if you favor ESP‑IDF and are comfortable designing a custom OTA and security setup, but it is somewhat less aligned with a BLE‑centric, non‑Wi‑Fi bench fixture.

In what follows, I will assume nRF5340 as the primary recommendation, while also highlighting where ESP32‑S3 or STM32WB would differ.

## 3. LIN Physical Layer and Transceiver Selection

### 3.1 LIN physical layer considerations

The LIN physical layer is standardized as a 12 V single‑wire bus with dominant and recessive states corresponding to low and high voltages.[42][45] The bus line is pulled up to battery voltage via a termination resistor (typically 1 kΩ in the master node) and a diode, and slave nodes present a higher termination resistance (around 30 kΩ).[45] The physical transceiver must translate between this 12 V single‑wire bus and the MCU’s logic levels, typically 3.3 V or 5 V CMOS/TTL.[4][5][24][25][28][45]

Dominant state corresponds to a voltage near ground, representing logical 0; recessive state corresponds to a voltage near the battery supply, representing logical 1.[36][45] The transceiver must conform to LIN standards such as LIN 2.0, 2.1, or 2.2A and SAE J2602 and handle common automotive conditions: bus faults, reverse battery, ESD, and EMC requirements, plus low‑power sleep and wake‑up modes.[4][5][22][24][25][28][36][45]

For a bench‑only fixture that still connects to 12 V vehicle‑adjacent hardware, it is important to choose transceivers that maintain automotive‑grade robustness. We want features like ±40 V or higher bus fault tolerance, integrated ESD protection, low dominant slew rate to reduce EMI, and support for data rates of at least 20 kbaud (and ideally higher for flexibility).[4][5][22][24][25][28][36][45] Many modern LIN transceivers also integrate a regulator and watchdog, which can simplify power architecture but must be evaluated carefully relative to your desired 3.3 V system and two‑transceiver design.

Because the architecture requires dual transceivers—one on the car‑side LIN segment and one on the wheel‑side segment—we also need to consider how their sleep/wake and enable pins are controlled, and how they behave under bench faults or partial power situations. Ideally, both transceivers should be controlled independently, and the default state on power‑up should be recessive and, if possible, within a safe “listen‑only” or standby mode until the MCU configures them to be active.

### 3.2 NXP LIN transceivers: TJA1020, TJA1021, and successors

NXP offers several LIN transceivers widely used in automotive applications. The TJA1020 is a classic LIN 2.0 transceiver that interfaces between a LIN protocol controller (e.g., MCU UART) and the physical bus.[22] It is intended for baud rates from 2.4 to 20 kbaud and is designed for 12 V sub‑networks.[22][45] It provides a single‑wire, half‑duplex interface, with the LIN pin connected via termination and pull‑up to Vbat, and TXD/RXD pins at logic levels for the microcontroller. The TJA1020 handles common automotive voltage conditions and ESD but is an older device.

The TJA1021 is a more modern LIN2.1/SAE J2602 transceiver with similar functionality but improved performance and compliance.[4][4] It is intended for in‑vehicle sub‑networks using baud rates from 1 kBd up to 20 kBd and is compliant with LIN 2.0, 2.1, 2.2, 2.2A, SAE J2602, and ISO 17987‑4:2016 (12 V).[4][4] It is pin‑compatible with the TJA1020 and Microchip’s MC33662(B), simplifying substitution.[4][4] The TJA1021 supports low‑power modes and wake‑up via LIN bus or local inputs, and its logic pins are designed to interface with 3.3 V or 5 V logic depending on the variant and system design. Being an automotive‑grade part from a major supplier, it is commonly stocked by distributors such as Digi‑Key and Mouser.

Both TJA1020 and TJA1021 require an external regulator to power 3.3 V or 5 V logic. They do not integrate LDOs, which is actually helpful here, since we will likely supply the MCU and transceivers from a common 3.3 V rail derived from the 12 V input. The transceivers themselves are powered from a 5 V or battery‑related rail (depending on variant), so level compatibility must be verified, but many designs operate them from 5 V while interfacing with 3.3 V MCUs without issue, provided logic thresholds are respected.

For your design, the TJA1021 is an excellent candidate: it is modern, LIN 2.2 compliant, widely available, and supports the standard baud rate range including 19.2 kBd.[4][4] Using two TJA1021 devices, one for the car side and one for the wheel side, would provide robust LIN physical interfaces while keeping logic complexity modest.

### 3.3 Microchip LIN transceivers: MCP2003, MCP2004, MCP2025

Microchip’s MCP2003 and MCP2004 are LIN transceivers compliant with LIN bus Specifications 1.3, 2.0, and 2.1 and SAE J2602, supporting baud rates up to 20 kbaud.[5][5] They provide a bidirectional half‑duplex interface between the MCU and the LIN bus, translating CMOS/TTL logic levels to LIN levels and vice versa.[5][5] These transceivers are designed for 12 V systems and offer ESD robustness and low‑power modes. They are widely used and available in small packages suitable for PCB assembly.

The MCP2025 is a more integrated device that combines a LIN transceiver with a voltage regulator capable of providing 5 V or 3.3 V at up to 70 mA.[24] It is compliant with LIN Bus Specifications 1.3 and 2.x and SAE J2602‑2 and supports baud rates up to 20 kbaud.[24] The MCP2025 translates CMOS/TTL logic levels to LIN levels and vice versa, and includes an internal LDO that can supply 5 V or 3.3 V to the microcontroller or other circuitry, simplifying power design for small nodes.[24] It supports various low‑power modes and can withstand high voltages on the LIN bus, with good EMI and ESD performance.[24]

The MCP2025’s integrated regulator might appear attractive as a way to power the MCU and transceivers from the 12 V bus. However, the 70 mA output current is insufficient for a BLE‑enabled MCU such as nRF5340 or ESP32‑S3 plus dual LIN transceivers, especially during BLE radio activity. It is more appropriate for simple LIN nodes, not for your higher‑performance fixture. Therefore, for this design, the simpler MCP2003/MCP2004 transceivers, powered from a dedicated buck‑derived rail, are better fits than MCP2025. That said, MCP2025 could be used as a secondary rail for small support logic or to power a separate low‑power MCU in an alternate architecture.

Microchip devices are a good alternative to NXP’s TJA series and are also well‑supported by distributors and assemblers. In many cases, they are slightly easier to source globally than NXP parts, especially through LCSC and JLCPCB’s part libraries.

### 3.4 Texas Instruments and Infineon LIN transceivers

Texas Instruments offers several LIN transceivers tailored to automotive needs. The TLIN4029A‑Q1 is an automotive LIN transceiver compliant with LIN 2.0, 2.1, 2.2, 2.2A, and ISO 17987‑4 standards.[28] It is designed for 12 V and 24 V LIN applications and supports low‑speed networks up to 20 kbps, with the LIN receiver capable of data rates up to 100 kbps for faster in‑line programming.[28] It features extended ±70 V bus‑fault protection, integrated wake‑up functions, and ultra‑low sleep currents.[28] The TLIN1441‑Q1 is another LIN transceiver with an integrated voltage regulator and watchdog, supporting LIN up to 20 kbps, LIN wake‑up, and sleep modes.[36]

The TLIN1441‑Q1 data shows key physical characteristics: LIN bus dominant is near ground, recessive is near battery, and the bus is pulled high by an internal 45 kΩ resistor and a diode in the recessive state.[36] This is typical of LIN transceivers and demonstrates that TI devices are fully standard‑compliant. The integrated LDO can be configured for node power in simple applications, but like Microchip’s MCP2025, its current capacity and architecture may not match a high‑power BLE MCU. Nonetheless, TI’s parts provide robust ESD and bus fault protection and are widely available through major distributors.

Infineon also offers a modular LIN portfolio, including high‑end and basic single‑channel LIN transceivers and integrated dual‑channel and LIN‑LDO variants.[25] Infineon emphasizes that LIN is used for low‑speed networking up to 20 kBd in body and interior applications, providing cost‑effective connections between actuators, sensors, switches, and ECUs.[25] Their transceivers are designed for automotive environments, with good EMC and ESD performance. While specific part numbers must be selected based on current availability, Infineon devices are a credible alternative to NXP, Microchip, and TI, especially if sourcing from European distributors.

### 3.5 LIN transceiver feature considerations: sleep, enable, and logic levels

When selecting LIN transceivers, it is important to consider more than basic compliance. Features such as sleep and standby modes, dominant timeout, and EN/SLP pins affect how the transceiver behaves in bench scenarios, especially when power is removed or partially applied.

Many LIN transceivers offer a dominant timeout function to prevent a stuck‑at‑low condition on the TXD pin from forcing the LIN bus into a continuous dominant state. This is an important safety feature that can prevent bus lockup due to MCU firmware errors. Sleep and standby modes allow the transceiver to minimize current draw when the MCU is asleep or when the bus is idle, and wake‑up via LIN bus or local input can restore operation.[4][5][24][25][28][36]

For a bench‑only fixture, dominant timeout is extremely valuable. It provides hardware‑level protection against uncontrolled bus drives. Sleep modes can be used to limit current draw when the device is not actively used, but they also introduce complexity in controlling wake‑up behavior. Given that your device will be powered from a bench supply, current is less critical than safety, so sleep modes should be used primarily to ensure that on power‑up the device sits in a listener/standby state.

Logic level compatibility is another key point. Many modern LIN transceivers are designed to interface with 5 V microcontrollers, but their RXD/TXD thresholds often accommodate 3.3 V logic. Data sheets should be checked to confirm that a 3.3 V high is recognized as logic high on TXD and that RXD outputs are safe for 3.3 V MCU pins. In practice, most contemporary devices are 3.3 V‑friendly, especially those marketed for mixed‑voltage systems.

### 3.6 LIN transceiver shortlist and selection

From the above, a shortlist of suitable LIN transceivers for your design includes NXP TJA1021, Microchip MCP2003/MCP2004, Microchip MCP2025 (for specific cases), TI TLIN4029A‑Q1, TI TLIN1441‑Q1, and several Infineon LIN transceivers.[4][5][5][4][22][24][25][28][36][45] All of these are compliant with LIN 2.x and SAE J2602, support baud rates up to 20 kBd, and offer robust ESD and fault protection. Many are available in SOIC, TSSOP, or TQFP packages that JLCPCB and similar assemblers can mount.

For your board, I recommend using two NXP TJA1021 or Microchip MCP2003‑class transceivers. Both families are widely used, support 1–20 kBd, and offer good robustness. If supply chain conditions favor Microchip, MCP2003/MCP2004 are excellent; if NXP parts are easier to source from your BOM distributors, TJA1021 is equally well suited.[4][5][4][22][24] TI TLIN4029A‑Q1 is also attractive due to its ±70 V bus‑fault protection and 100 kbps capability for faster in‑line programming, but it may be somewhat more automotive‑targeted in terms of price and packaging.[28] Any of these will work for a bench fixture; the final choice can be guided by price and assembly availability from Digi‑Key, Mouser, and LCSC at design time.

## 4. Power and Protection Architecture for Bench/Vehicle‑Adjacent Use
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
