lakewoodphone/tesla-lin-chip/research/responses/2026-05-31-quick-research-3-board-tesla-dual-lin-rev-a-mini-order-cost-and-arrival-estimate-b5bee33e.md

---
job_id: b5bee33e-315b-4d53-ac85-8310d29985e6
directive_id: quick-research-3-board-tesla-dual-lin-rev-a-mini-order-cost-and-arrival-estimate
title: Quick Research: 3-board Tesla Dual LIN Rev A mini order cost and arrival estimate
domain: legal
sensitivity: standard
model_used: gpt-5.5
provider: openai
status: complete
completed_at: 2026-05-31T19:25:54.894468+00:00
cost_usd: 0.16414
input_tokens: 15544
output_tokens: 1953
reasoning_tokens: 261
search_count: 2
citation_count: 5
verifier_status: passed
schema_version: 1
---

## Quick estimate — 3-board Tesla Dual LIN Rev A mini order  
**Date basis:** 2026-05-31. **Destination assumed:** NJ/NY, USA.  
**Important:** an exact quote requires uploading **Gerbers + BOM + CPL/PNP** to JLCPCB/PCBWay; the ranges below are realistic pre-upload estimates.
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
