lakewoodphone/tesla-lin-chip/research/responses/2026-05-17-research-directive-2025-tesla-model-x-steering-lin-id-0x0c-confidence-build-and-ad4b0b79.md

---
job_id: ad4b0b79-2e9a-46fd-a36f-b8e95a9f8050
directive_id: research-directive-2025-tesla-model-x-steering-lin-id-0x0c-confidence-build-and-
title: Research Directive: 2025 Tesla Model X Steering LIN ID 0x0C Confidence Build and Safe Injection Gating
domain: general
sensitivity: no_refusal_required
model_used: sonar-deep-research
provider: perplexity
status: complete
completed_at: 2026-05-17T19:51:13.329697+00:00
cost_usd: 0.41957
input_tokens: 616
output_tokens: 13855
reasoning_tokens: 46349
search_count: 30
citation_count: 30
verifier_status: passed
schema_version: 1
---

# Confidence-Building and Safe Injection Gating for LIN ID 0x0C on a 2025 Tesla Model X Steering Wheel Network

Before any active intervention on a production vehicle, especially one as integrated and electronically complex as a 2025 Tesla Model X, the attribution of a specific LIN frame ID to a control function must be based on a rigorous and multi-dimensional evidence base, not mere heuristic correlation. In the case of the candidate steering wheel LIN frame ID 0x0C, the strongest approach is to combine a formal understanding of LIN protocol behavior, systematic experimental design, quantitative signal and statistical analysis, and a safety-driven validation pipeline that escalates from passive observation through bench replay and finally to carefully gated in-vehicle testing. Methodologies developed for reverse engineering CAN traffic, including supervised and unsupervised correlation of message payloads with physical actions, can be conceptually adapted to LIN networks, with additional attention to LIN’s master–slave polling and checksum rules.[1][2][7][9][14][30] To avoid false attribution, one must explicitly handle confounders such as coincident vehicle state changes, background periodic messages, counters and checksums, and unrelated controls by using controlled input designs, repeated and randomized trials, blinded segments, and statistical techniques that are standard in confounder adjustment research.[6][22][23] Payload bytes should be dissected at the bit and byte level for temporal alignment to steering inputs, signed-delta behavior, quantization patterns, monotonic counters, and static or toggling state bits, while also reconstructing and validating checksums according to LIN specifications and verifying consistency across captures.[1][2][9] A confidence-scoring rubric for frame-ID attribution can then be defined across multiple evidence axes, such as temporal causality, strength and specificity of association, payload semantics, reproducibility, and exclusivity, with thresholds that must be met before classifying ID 0x0C as “control-bearing” in a way that justifies any write or injection path. Finally, a safety framework grounded in automotive validation and safety standards requires strict hard-stop gates before any injection activity, including prior bench validation, fault-path analysis, hardware isolation, limits on timing and amplitude of injections, and alignment with state-aware defenses that consider both vehicle dynamics and message semantics.[10][11][12][26][27] The result is a staged, conservative validation and gating plan that can be operationalized in the field via a concise go/no-go decision template, while maintaining a deep, technically defensible audit trail for each step.

## 1. Technical and Operational Context

### 1.1 The steering wheel LIN network on a modern EV

Modern steering wheel switch packs in vehicles like the Tesla Model X are typically connected via low-cost, low-bandwidth networks rather than by direct point-to-point wiring of each discrete switch. A common choice for such functions is the Local Interconnect Network (LIN), which is specifically designed as a single-master, multiple-slave, low-cost bus for simple sensors and actuators.[2][9][30] In a typical steering wheel implementation, the steering column module or a body domain controller acts as the LIN master, polling a steering wheel switch node that aggregates multiple physical buttons, scroll wheels, or capacitive touch elements. The LIN master periodically transmits headers specifying frame IDs, and the steering wheel node responds with data frames that encode the instantaneous or latched state of its controls.[2][9][30]

Crucially, in such designs, the physical steering wheel interface does not normally have global vehicle authority; rather, its messages are interpreted by higher-level ECUs (for example, infotainment, ADAS, or gateway controllers) via gatewaying from the LIN segment onto higher-level networks such as CAN or Ethernet. This means that a misattributed steering wheel LIN ID, and especially an incorrectly injected payload, can cause unintended actions ranging from benign control glitches to persistent misbehavior, and in multi-domain architectures could propagate in poorly understood ways if safety mechanisms are not carefully respected.

### 1.2 Existing field observations and candidate ID 0x0C

The field observations you described can be summarized as follows. A suspected steering wheel LIN wire, color-coded white, has been tapped and decoded at 19200 baud via an FX2-based interface and sigrok. On this bus, several frame IDs have been observed, notably 0x0C, 0x0D, 0x0E, 0x0F, 0x16, and 0x17. Preliminary “single-control” experiments, in which individual steering wheel controls are activated one at a time, indicate that ID 0x0C exhibits the strongest payload variation correlated with steering wheel actions, making it the current top candidate for a steering control-bearing frame. However, at this stage, this remains an inference rather than a proven attribution, and it is vulnerable to confounding by other correlated traffic, periodic housekeeping messages, or unrecognized state variables.

The need, therefore, is to move from intuitive correlation to a disciplined, reproducible, and quantifiable evidence base for frame-ID attribution. This must be done before any lock, write, or injection capability is enabled on non-bench hardware. Systematically building confidence requires both a robust methodology and explicit decision criteria.

### 1.3 Why a formal methodology is necessary for LIN reverse engineering

Experience from reverse engineering CAN networks shows that naive strategies, such as “press a button and see what ID changes,” are often misleading given the density and complexity of in-vehicle traffic, the presence of periodic status messages, and the interaction of multiple ECUs.[4][7][14][17] Researchers have demonstrated that more elaborate methods, including feature extraction, change detection, and machine learning classifiers, can robustly associate CAN IDs and payload fields with specific vehicle functions, even without direct physical experimentation on the vehicle.[7][14] Analogously, LIN reverse engineering benefits from both protocol knowledge and carefully structured experiments.

Furthermore, automotive safety and security research has increasingly emphasized the importance of considering message semantics and vehicle state when defending against message injection attacks.[10][27] For example, state-aware defense frameworks such as SAID (State-Aware Defense Against Injection Attacks) detect malicious in-vehicle network messages by considering both their data semantics and how they would alter vehicle dynamics and states, discarding messages that could cause unsafe states.[27] Such work underscores that any attempt to inject or emulate steering wheel control messages must respect not only protocol correctness but also the context of vehicle behavior.

Given these considerations, attributing steering control to LIN ID 0x0C and then gating potential injections requires a multi-layered approach, integrating protocol analysis, statistical methodologies, and safety validation practices derived from automotive functional safety frameworks such as ISO 26262.[11][12][26]

## 2. LIN Protocol Behavior and Its Implications for Attribution

### 2.1 LIN frame structure and timing

A LIN frame, as standardized in LIN 1.x and 2.x, consists of a header transmitted by the master node and an optional response frame from a slave.[2][9] The header includes a break field, a sync byte (0x55), and a protected identifier (PID) that encodes a 6-bit ID and two parity bits.[2] The response frame, when present, consists of 1 to 8 data bytes followed by a checksum byte that can be either the classic checksum (data bytes only) or the enhanced checksum (data bytes plus identifier) depending on the LIN version and configuration.[2][9] A typical LIN transceiver used for reverse engineering, such as the TJA1020, will translate the single-wire bus signaling into a standard UART-like signal that can be read by a USB–UART adapter.[1]

In practical reverse engineering, tools such as sigrok or dedicated LIN analyzers reconstruct frames from the observed UART traffic, often representing each frame as a PID (or higher-level ID), a data payload, and a checksum.[1][9][30] The master node periodically polls specific IDs according to a schedule defined by a LIN Description File (LDF), which describes frame timing, signal definitions, and node roles.[30] In the absence of an LDF, the reverse engineer must infer frame periodicity and roles from observation.

This structure has several implications for attribution. First, because the master controls the timing and ordering of frames, the presence of an ID like 0x0C on the bus is not itself sufficient to identify it as a steering input frame; rather, one must observe how its payload changes in response to physical inputs and how its periodicity behaves under static conditions. Second, because the checksum field is tightly coupled to data bytes (and in some variants to the ID), injections must preserve integrity across both payload and checksum to avoid error detection.[2][9] Third, the parity bits in the PID must be correct; otherwise, receiving nodes will reject frames.

### 2.2 Lessons from existing LIN reverse engineering case studies

Practical case studies provide useful guidance. In one documented LIN reverse engineering project, an engineer hooked a TJA1020 LIN transceiver in parallel with a car’s climate control LIN bus, reading data via a USB-to-UART adapter at 19200 baud.[1] They noted that frames were represented by a sync byte 0x55, an ID byte, multiple data bytes, and a 0x00 marker after the checksum from the adapter, with specific IDs associated with master-to-slave data (for example, 0xB1, 0x32, 0xF5) and others used as request PIDs for which the slave responded (for example, 0x39, 0xBA, 0x78).[1] To identify frame functionality, they pressed climate control buttons systematically and observed which frames’ payloads changed in characteristic ways, eventually discovering that they could emulate certain button presses by injecting appropriate responses using a Python script that computed valid checksums.[1]

Several methodological lessons emerge from this example. First, the initial step was passive observation of all frames under various conditions, followed by systematic one-variable-at-a-time manipulations (such as pressing a specific button) to see which frame payloads changed. Second, inference was not considered complete until repeated, consistent responses were observed and could be replicated via emulation. Third, collisions arose when the original panel and an emulator both attempted to respond to the same request PID, leading to invalid data that the master ignored; this underscores the need to consider collision avoidance and bus arbitration in any injection plan.[1]

These observations translate directly to the steering wheel LIN case. ID 0x0C may be a data frame sent periodically by the wheel module, or it may be a request or response frame in a polling sequence. Without an LDF or documentation, the safest approach is to infer the role of 0x0C by examining the directionality and timing of frames relative to break and sync bytes, and by using systematically designed experiments that vary only steering wheel inputs, while maintaining all other variables as constant as possible.

### 2.3 Comparison to CAN reverse engineering

While LIN and CAN differ significantly in physical and data link layers, much of the methodological toolkit for reverse engineering CAN traffic can be ported by analogy. CAN reverse engineering work has described methods such as electrical fingerprinting of transmitters, clustering of messages by timing and payload characteristics, and supervised learning to associate CAN frames with vehicle functions.[4][7][14] For example, one study proposed a machine learning-based classifier that analyzes raw CAN logs, extracts message features (including timing and payload change patterns), and uses labeled segments where specific vehicle functions are active to infer which IDs carry which functions.[7] Another line of work developed the READ algorithm, which automatically identifies individual signal fields within unknown CAN payloads by analyzing patterns of change and value distributions, enabling functional labeling of signals.[14]

Although LIN traffic is simpler and lower bandwidth, the same principles hold. One can extract features such as frame period, jitter, payload entropy, bit-level change frequency, and relationships between bits and physical inputs, then use structured experiments or even machine learning to infer semantics. Unlike CAN, LIN is strictly master–slave and deterministic in scheduling, which simplifies some aspects of inference but makes others more sensitive to timing.

### 2.4 LIN analyzers, LDFs, and tool-assisted workflows

Commercial and open-source LIN analyzers and simulators, such as those described by NI, CSS Electronics, and other tool vendors, commonly rely on an LDF to decode frames into named signals and to simulate bus traffic.[2][9][30] An LDF specifies frame IDs, schedule tables, signal mapping, node roles, and checksum types.[30] While an LDF is obviously not available for a proprietary Tesla steering wheel network, awareness of this formal representation is helpful. It suggests that an end-state of reverse engineering ideally includes:

An inferred schedule table for the observed IDs, including 0x0C, with approximate periods and roles (master request, slave response, or master data).

An inferred signal map for the payload bytes of 0x0C, including bit fields for buttons, scroll wheel deltas, or other controls.

An understanding of the checksum type used, verified by recomputing checksums and comparing them to observed values.[9]

Once this mental model is established, injecting messages consistent with the inferred LDF becomes less ad hoc and more aligned with expected node behavior. However, because constructing a full virtual LDF is a non-trivial undertaking, we will concentrate on the experimental and analytic steps that systematically build evidence about whether 0x0C is truly control-bearing.

## 3. Statistical and Experimental Design for Attributing 0x0C to Steering Control

### 3.1 The problem of confounding in network traffic analysis

When capturing live LIN traffic on a vehicle, multiple sources of variability are present. Steering wheel inputs change over time; the rest of the vehicle’s state (ignition, drive mode, infotainment activity, ADAS status) also changes; periodic housekeeping and diagnostic frames may be present; and counters or checksums may cause payload bytes to change even when no user input has occurred. If one simply records traffic while manipulating the steering wheel, any observed correlation between a frame’s payload and the input might be spurious or partially confounded.

This problem is structurally similar to confounding in observational studies in epidemiology, where multiple exposures and outcomes are intertwined.[22][23] A confounder is a variable associated with both the exposure and the outcome, which, if not adjusted for, can lead to biased estimates of effect.[23] In our setting, the “exposure” is the steering wheel input (for example, pressing the volume up control), and the “outcome” is observed changes in payload bits or bytes of a candidate LIN ID such as 0x0C. Confounders include any other stimulus or state change correlated with the steering input, such as vehicle speed, infotainment state, or even unintentional movement of other controls during experiments.

In epidemiological analysis, confounding can be handled through careful study design (randomization, restriction, matching) or through statistical adjustment (stratification, multivariate regression).[23] For vehicle network reverse engineering, the analogues are controlled experiments in which only the steering wheel input is intentionally varied, with all other variables held as constant as feasible, and statistical analyses that isolate the association between the input and candidate frame variants, while accounting for time and other measured signals.

### 3.2 Blocking, randomization, and blinded segments

One effective approach is to design experiments that divide time into blocks during which the steering wheel input state is well-defined and known to the experimenter but ideally not obvious to the analyst. A classic example from signal detection is dividing a signal into blocks and computing energy or RMS values to detect the presence or absence of speech based on thresholds.[6] By analogy, we can divide capture sessions into fixed-length segments, some of which contain active steering inputs and some of which do not, and then have a separate analytic process that attempts to detect these “input-present” segments from the LIN data alone.

To reduce bias and confounding, segments of steering input should be randomized in order and perhaps even “blinded” to the person conducting the analysis. For example, an experimenter may prepare a schedule instructing another operator to apply specific steering wheel actions (for instance, press and hold the scroll wheel up for N seconds, then release) at specified times, while the analyst later evaluates whether changes in the payload of 0x0C (and other IDs) correctly and uniquely predict these actions.

From a statistical standpoint, this is similar to a supervised labeling scenario in CAN reverse engineering work, where segments of CAN logs labeled with specific vehicular functions (for example, braking) are used to detect messages whose bits change in a manner correlated with those functions.[7] The difference here is that the experimenter has much tighter control over inputs, allowing for more precise causal inference.

### 3.3 Separation of training and validation segments

To avoid overfitting and wishful thinking, it is valuable to separate the data used to hypothesize an attribution from the data used to test it. In other words, some capture sessions can be used to explore which frames change in association with given inputs and to propose 0x0C as a candidate; subsequent sessions, ideally conducted under slightly different conditions, can be used solely to validate whether 0x0C’s payload behavior still uniquely tracks steering inputs.

This approach mirrors cross-validation strategies in machine learning and also the “held-out scenes” evaluation in attribution-based risk estimation for autonomous driving planners, where attribution statistics derived from one set of scenes generalize to unseen scenes with minimal degradation.[21] The same logic applies here: a reliable steering control frame should behave consistently across different experimental runs, not only in the dataset where it was initially noticed.

### 3.4 Confounder adjustment strategies

Beyond experimental design, some statistical techniques can be applied post hoc to adjust for potential confounders. For example, if multiple candidate frames (say 0x0C, 0x0D, and 0x16) all show variation when a steering wheel control is manipulated, multivariate regression can be used to assess which frame’s payload changes remain significantly associated with the input after controlling for the others, analogous to mutual adjustment of multiple risk factors in regression models.[22][23] In epidemiological literature, models that adjust for confounders are used to estimate “independent associations,” and it is recommended to adjust for confounders specific to each exposure–outcome pair rather than including all variables indiscriminately.[22] For our purposes, this suggests constructing models in which the steering input (present/absent or magnitude) is regressed on payload features of 0x0C and other IDs, with time and other measured variables as covariates, then examining which payload features retain a strong association with the input.

Even simpler stratification-based techniques can be helpful. For example, one could analyze only segments in which vehicle speed is zero, or in which infotainment is idle, to reduce the space of possible confounders. Stratified analyses are conceptually similar to those used to control confounding in other fields, where data are partitioned by levels of a confounding variable and effect estimates are recomputed within strata.[23] In your context, this might mean repeating the steering wheel experiments in multiple “vehicle state strata,” such as “ignition on but vehicle stationary” and “vehicle in motion at low speed,” then verifying that 0x0C’s behavior remains consistent in all relevant strata.

### 3.5 Signal detection framing of the attribution problem

From the perspective of signal processing, the problem of attributing 0x0C to steering control can be framed as detecting a structured signal (payload changes corresponding to inputs) in the presence of background “noise” (other traffic and unrelated variation). In classical detection theory, one might compute summary statistics over blocks, such as the energy or RMS of the difference between observed and expected signals, and compare these to thresholds to decide whether a signal is present.[6] In the context of LIN payloads, one could define a feature such as the absolute sum of payload bit changes within a given time window, or a cross-correlation between a hypothesized control time series (for example, a step function representing button holds) and a candidate payload bit, then test whether this statistic exceeds what would be expected under null conditions.

By designing experiments where the steering wheel input pattern is known, one can compute these detection statistics for 0x0C and other IDs and evaluate sensitivity (the fraction of input-present blocks detected) and specificity (the fraction of input-absent blocks correctly classified). Borrowing terminology from intrusion detection on in-vehicle networks, a robust attribution should exhibit high “accuracy” in distinguishing input vs. no-input blocks, akin to how hybrid intrusion detection systems use timing and traffic-volume statistics to distinguish normal from attack traffic with high AUROC.[10] The higher the detection performance, the stronger the evidence that 0x0C is genuinely control-bearing.

## 4. Byte- and Bit-Level Payload Analysis for 0x0C

### 4.1 Characterizing the temporal alignment between inputs and payload changes

The first step in payload analysis is to establish temporal alignment between steering wheel inputs and payload changes. Because LIN is polled, there is a fixed period between successive instances of ID 0x0C. For each occurrence, record the timestamp, the payload bytes as an array of 8 values (or however many data bytes the frame carries), and the computed checksum. Then synchronize these with a time-stamped log of steering wheel actions, such as button presses, scroll wheel movements, or touch gestures, ideally recorded via a separate instrument (for example, manual annotations, video with timecode, or even instrumented switches).

One can then construct time series for each payload bit or byte and compare them to the input time series. For discrete controls (on/off buttons), state bits should transition at or immediately following the time of press or release, while for incremental controls (scroll wheels), certain payload fields may change by signed steps proportional to the action magnitude. The causality requirement is that input changes precede or coincide with payload changes, not vice versa.

Once this alignment is established, one can compute lagged correlations or cross-correlation functions between input time series and payload bit states to determine the optimal time offset and strength of association. A truly control-bearing bit or field should exhibit high correlation with minimal lag and should change only (or almost only) when the control is actuated.

### 4.2 Detecting signed-delta and magnitude-encoded behavior

Many steering wheel controls, especially scroll wheels or jog dials, do not simply encode binary states but instead send incremental deltas, sometimes as small signed integers, which are interpreted by downstream ECUs as relative adjustments (for example, volume up/down by a small amount each detent). To detect such behavior, one must examine differences between successive payload values for candidate bytes or bit fields.

Define for each byte \(b_i[n]\) the sequence of differences \(\Delta b_i[n] = b_i[n] - b_i[n-1]\). If the control in question is a scroll wheel, then during periods of neutral activity \(\Delta b_i[n]\) should be mostly zero, whereas during active scrolling, \(\Delta b_i[n]\) might take on values such as \(\pm 1\), \(\pm 2\), or other bounded integers. If the representation is signed (for example, two’s complement), certain patterns such as wrap-around from 255 to 0 may appear; interpreting these correctly requires consideration of signedness, but even before sign interpretation, the magnitude of \(|\Delta b_i[n]|\) can be analyzed.

This approach mirrors how CAN DBC-defined signals are extracted and interpreted: a contiguous set of payload bits represents a value that, once endianess and offset are accounted for, corresponds to a physical parameter such as engine speed.[17] In the absence of a DBC, one can infer such fields by looking for bytes or bit groups whose differences correlate with the direction and magnitude of user inputs. The READ algorithm for CAN reverse engineering uses similar patterns of change and value range to detect and label signal fields embedded in payloads.[14] For LIN, while payloads are often simpler, the same concepts apply.

### 4.3 Identifying monotonic counters and periodic fields

Many automotive network messages, including those on LIN, incorporate monotonic counters or sequence numbers to support error detection and diagnostics. Such counters typically increment by one each frame, wrapping around at a fixed modulus, and are independent of user inputs. Distinguishing these from control-bearing fields is crucial, because they can easily produce apparent “changes” in payload that are not related to steering wheel activity.

To detect counters, inspect each payload byte’s timeline and evaluate whether it increments by one (with occasional resets) at a fixed frequency, regardless of steering input. A byte that changes steadily across all frames, including in long segments with no inputs, is likely a counter. Counters may be narrower than a full byte (for example, four bits), so bit-level time series should also be examined for repeating patterns with fixed period.

Once identified, counter bits can be masked out when analyzing associations between payload changes and control actions. This reduces the likelihood of false attribution. This practice parallels automated signal extraction approaches which first cluster bits by behavior (for example, always incrementing, rarely changing, toggling) before assigning semantic roles.[14] Similarly, automotive IDS systems often use timing and volume statistics to detect anomalies, relying on the regularity of counters and periodic fields to define “normal” behavior.[10]

### 4.4 State bits and multi-bit fields for discrete controls

Discrete steering wheel buttons, such as “Next track,” “Voice command,” or “Call,” are likely represented as state bits or short fields within the payload. These may be level-encoded (1 while button is held) or edge-encoded (a pulse when pressed or released). To identify them, one can compute the proportion of time each bit is in the 1 state and the transitions per unit time, and compare these statistics across conditions with and without specific button usage.

Bits that remain constant across all experiments can be provisionally marked as non-control (for the tested functions), whereas bits that toggle only when specific controls are used merit further scrutiny. Structurally, this is similar to change detection used for CAN messages in reverse engineering, where bits with high change frequency correlated with a labeled vehicular function (for example, braking) were flagged as part of a functional signal.[7] The additional challenge in your case is that multiple controls may share the same frame, so state bits may represent a combination of inputs, requiring combinatorial analysis or additional experiments where only one control is varied at a time.

### 4.5 Checksum reconstruction and verification

LIN frames include a checksum byte that ensures data integrity.[2][9] The classic checksum used in LIN 1.x is an 8-bit invert of the sum of all data bytes, while enhanced checksum variants include the protected identifier in the sum as well.[2][9] To understand and safely emulate 0x0C, it is essential to determine which checksum scheme is in use and verify that all observed frames adhere to it.

The process is straightforward. For each captured 0x0C frame, compute the candidate classic checksum as the inverted sum of the data bytes modulo 256, and compare it to the observed checksum byte. If they match across a large sample, the classic checksum is likely in use. If not, recompute including the PID/ID byte with its parity bits and test again for the enhanced checksum. When a consistent pattern is observed, one has both a validation of capture fidelity and a recipe for generating correct checksums during injection.

This checksum verification also serves as a quality-control step. Errors in decoding, misalignment in frame boundaries, or electrical interference might cause checksum mismatches. In a reverse engineering study of LIN-based climate control, an engineer implemented a Python script with a calculate_checksum function specifically to ensure that injected frames were accepted by the vehicle, emphasizing that valid checksums are a prerequisite for meaningful emulation.[1] Ensuring 0x0C’s checksums are fully understood reduces the risk that any injection would be silently discarded or, worse, misinterpreted by the receiver.

### 4.6 Timing alignment and frame scheduling

In LIN, each ID is scheduled by the master in a fixed or quasi-fixed schedule. Understanding the period and jitter of 0x0C is helpful for both attribution and safe injection. If 0x0C is polled every, for example, 10 ms, and its payload changes immediately following user inputs, this strengthens the case that it represents time-critical steering controls. If instead 0x0C appears only occasionally or in response to specific higher-layer events, its role may be more nuanced.

To characterize this, calculate the inter-arrival time (IAT) distribution for 0x0C frames and for other observed IDs. Plotting or summarizing these distributions reveals periodic patterns and can differentiate high-frequency “status” frames from low-frequency “event” frames. Such timing analyses are central to vehicle-agnostic intrusion detection methods that rely on packet timing and count statistics rather than payload semantics.[10] Similar logic can be used here to understand 0x0C’s place in the LIN schedule: a consistent, narrow IAT distribution indicates a deterministic schedule, while a wider or multi-modal distribution suggests context-dependent polling.

Armed with this information, any eventual injection strategy can be designed to align with the natural polling cadence, thereby minimizing timing anomalies that might trigger diagnostic warnings or IDS defenses.

## 5. A Confidence-Scoring Rubric for Attributing 0x0C to Steering Control

### 5.1 Dimensions of evidence

To move from qualitative impressions to a formal attribution, it is useful to define explicit dimensions of evidence and score each candidate ID along these dimensions. Drawing on methodologies from CAN reverse engineering, IDS design, and confounder-adjusted analysis, one can define axes such as temporal causality, strength of association, specificity, reproducibility, payload semantics, and exclusivity.[4][7][10][14][22][23]

Temporal causality captures whether changes in 0x0C’s payload follow steering inputs with a consistent minimal lag. Strength of association measures how strongly payload features correlate with input presence or magnitude, for example using correlation coefficients or classification performance metrics such as AUROC. Specificity refers to whether 0x0C changes primarily when steering inputs are present and remains stable otherwise. Reproducibility encompasses whether these patterns hold across repeated experiments, days, and slight variations in vehicle state. Payload semantics captures how interpretable the inferred fields are, for instance whether bits align logically with “button pressed” or “scroll delta” interpretations. Exclusivity reflects whether other IDs provide an equal or better explanation for observed controls.

### 5.2 Constructing a quantitative rubric

A simple but effective approach is to define numerical scores for each dimension on a standardized scale, such as 0 to 3, where higher numbers indicate stronger evidence. The following table illustrates a possible rubric structure that can be adapted to your environment. The score descriptions are framed generically; in practice, you would populate them with quantitative thresholds (for example, correlation coefficients, false positive rates) based on your analyses.

| Evidence Dimension | Score 0 Description | Score 1 Description | Score 2 Description | Score 3 Description |
|---|---|---|---|---|
| Temporal causality | No clear temporal alignment between input changes and payload changes | Some visually apparent alignment, but inconsistent or with large variable lag | Consistent alignment with small, bounded lag in most trials | Near-perfect alignment; payload changes immediately follow inputs with negligible and stable lag |
| Strength of association  | Payload features weakly associated with input; correlation or detection near chance | Moderate association; input presence can be detected above chance but with many errors | Strong association; payload features predict input presence/magnitude with high accuracy | Very strong association; near-perfect classification or regression performance for input state from payload |
| Specificity | Payload changes frequently in absence of input | Payload changes both with and without input, with limited discriminability | Payload mostly stable in absence of input, but occasional unrelated changes | Payload virtually never changes without corresponding input; high specificity |
| Reproducibility | Patterns observed only in a single session or not repeatable | Patterns repeat partially but vary significantly across sessions or under small condition changes | Patterns repeat across multiple days and moderate changes in vehicle state | Patterns robust across many sessions, conditions, and minor vehicle state variations |
| Payload semantics | No interpretable mapping; bits/fields do not match plausible control semantics | Tentative interpretations possible; multiple conflicting mappings | Clear mapping of specific bits/fields to controls, supported by experiments and value ranges | Highly interpretable semantics; one-to-one mapping between bits/fields and physical controls, with cross-validated quantitative behavior |
| Exclusivity | Other IDs or fields explain controls as well or better | 0x0C shares explanatory power with other IDs; unique contribution unclear | 0x0C explains majority of control behavior, with limited overlap with other IDs | 0x0C uniquely explains control behavior; excluding it severely degrades predictive performance |

In applying this rubric, one would compute or qualitatively assess each dimension for 0x0C and other candidate IDs. An overall confidence score could be the sum of dimension scores, or a weighted sum emphasizing, for example, temporal causality and exclusivity as primary factors.

### 5.3 Defining an evidence threshold for “control-bearing” classification

The question of “what minimum evidence threshold” is required before classifying 0x0C as control-bearing should be informed by both technical and safety considerations. Technically, a high overall score on the rubric, particularly in temporal causality, strength of association, and exclusivity, should be required. For example, one could define a minimum threshold such that:

Temporal causality ≥ 2, strength of association ≥ 2, specificity ≥ 2, reproducibility ≥ 2, payload semantics ≥ 2, and exclusivity ≥ 2, with at least two dimensions scoring 3.

This threshold ensures that 0x0C is not only strongly associated with steering inputs but also relatively unique in its explanatory power, robust across multiple sessions, and semantically interpretable. Analogously, in intrusion detection systems, thresholds for correlation or detection accuracy are set based on desired false positive and false negative rates.[10] For high-stakes control attribution, an extremely low false attribution rate is required, suggesting conservative thresholds.

From a safety standpoint, beyond statistical confidence, one should also ensure that inferred semantics are consistent with benign and limited behaviors. If, for example, 0x0C includes bits that might correspond to safety-critical functions (such as canceling ADAS maneuvers), the evidence threshold for injection must be even higher, and additional safeguards must be in place. Additionally, it is prudent to require that the payload’s range and dynamics under natural operation be fully mapped before any attempt at emulation.

### 5.4 Role of negative evidence

Equally important as positive evidence is negative evidence: demonstrating that 0x0C does not change under conditions where it should not. For instance, long segments of static steering wheel usage (no button presses or scrolls) should show 0x0C payload remaining constant except for any identified counters. Similarly, manipulation of controls known to be independent of the steering wheel (for example, center console screens) should not produce changes in 0x0C. Such negative controls strengthen specificity and reduce the risk that 0x0C’s variability is driven by other systems.

Negative evidence is a cornerstone of confounding control in observational research, where analyses show not only that exposure is associated with outcome but also that non-exposures or irrelevant exposures are not.[22][23] In your attribution rubric, strong negative evidence contributes to high specificity and exclusivity scores.

### 5.5 Cross-validation with alternative methods and tools

Finally, robustness can be further enhanced by cross-validating findings using different analysis tools or methodologies. For instance, if time-series analysis and manual inspection suggest that certain bits in 0x0C represent the volume scroll wheel, an independent machine learning model trained to predict input states from payload features should also converge on those bits as important features. This is similar in spirit to attribution-based risk prediction in autonomous driving planners, where different attribution algorithms still yield consistent relationships between attribution statistics and planning risk.[21]

Additionally, using different hardware capture and decoding setups (for example, alternative LIN analyzers, different sampling hardware) can verify that observed patterns in 0x0C are not artifacts of a specific toolchain. A consistent picture across multiple tool stacks further justifies high confidence scores.

## 6. Experimental Matrix for Steering Input Validation

### 6.1 Goals of the experimental matrix

The experimental matrix should serve several purposes: to systematically excite all relevant steering wheel controls; to isolate individual controls when necessary; to capture variability in user behavior (for example, different press durations or scroll speeds); to randomize and blind input patterns to reduce bias; and to generate sufficient repeated measures for statistical assessment. Because the observed IDs include 0x0C, 0x0D, 0x0E, 0x0F, 0x16, and 0x17, the matrix should help determine which of these, and which payload bits, are truly associated with steering wheels or other controls.

### 6.2 Structure of the matrix: factors and conditions

Conceptually, the experimental design has several factors. The primary factor is the steering input type (for example, left scroll wheel up/down, left wheel press, right scroll wheel up/down, right wheel press, and any capacitive or touch controls present). Secondary factors include input intensity (for example, number of scroll detents per second), duration (momentary vs. sustained holds), and direction (up vs. down). Environmental factors include vehicle state (ignition only vs. drive-ready), stationary vs. low-speed motion, and whether certain systems (infotainment, ADAS) are active.

An example high-level matrix is shown below. Each row represents a distinct experimental condition or block that can be executed multiple times in randomized order. The “Blinding/Randomization” column refers to whether the order and timing of input applications are randomized such that the analyst does not know a priori which block corresponds to which input pattern.

| Experiment Block ID | Steering Input Focus | Input Pattern Description | Vehicle State | Repetitions | Blinding/Randomization Notes |
|---|---|---|---|---|---|
| B1 | No input (baseline) | Hands off all steering controls for full duration | Ignition on, Park | ≥3 | Randomize temporal placement among active blocks; used as negative control |
| B2 | Left scroll up only | Repeated scroll-up actions at fixed rate and duration; no other controls | Ignition on, Park | ≥3 | Order randomized with B3–B6; operator follows a prewritten timing script |
| B3 | Left scroll down only | Repeated scroll-down actions at fixed rate and duration | Ignition on, Park | ≥3 | As above |
| B4 | Left scroll press only | Repeated short presses at fixed cadence | Ignition on, Park | ≥3 | As above |
| B5 | Right scroll up/down | Alternating up/down sequences | Ignition on, Park | ≥3 | As above |
| B6 | Right wheel press | Repeated presses | Ignition on, Park | ≥3 | As above |
| B7 | Mixed random inputs | Operator follows randomized script mixing all controls | Ignition on, Park | ≥3 | Script and timing known only to experiment supervisor, not to data analyst |
| B8 | Baseline under slow motion | No inputs; vehicle in low-speed straight-line motion | Low-speed drive | ≥2 | Used to examine if motion influences 0x0C payload independent of steering wheel actions |
| B9 | Selected inputs under slow motion | Subset of steering inputs applied as in B2–B6 while vehicle moves slowly | Low-speed drive | ≥2 | Performed only after B1–B7 analyses confirm safe conditions and bus stability |

This matrix can be extended to include other controls on the steering wheel, environmental conditions (for example, headlights on/off if they might share the bus), and repeated sessions on different days. The essential quality is that each experiment isolates a subset of inputs while keeping others constant, and that the sequence and timing of blocks are randomized so that the analyst evaluating LIN data does not unconsciously bias their interpretation.

### 6.3 Single-axis versus mixed-input runs

Single-axis runs (such as B2–B6) are particularly useful for identifying which bits correspond to which specific controls. By ensuring that only one control is being manipulated in an experiment, changes in 0x0C (and other IDs) can be more cleanly attributed. These runs are analogous to unit-testing individual buttons.

Mixed-input runs (such as B7) then test whether the inferred mapping generalizes when multiple controls are used in closer temporal proximity, as would occur in realistic use. Such runs help validate that the decoding logic can disentangle overlapping patterns and that the attribution remains robust when multiple inputs are present. This is akin to moving from unit tests to integration tests in software verification.

### 6.4 Repetition and within-block randomization

Repetition is necessary to assess reproducibility and to average out incidental noise or operator variability. Within each block type, repeated runs should be conducted with slight variations in timing (for example, changing the exact start times or durations of actions within small bounds) to ensure that the mapping does not depend on a specific deterministic script.

Within-block randomization of small details (such as the exact number of scroll steps per burst) can also help reveal whether payload semantics are linear or saturated. For instance, if scroll wheel delta fields saturate at certain values, this may become apparent only when varying the intensity of inputs.

### 6.5 Data annotation and synchronization

To make the resulting dataset maximally useful, experimental blocks should be accompanied by precise annotations of input timings. This can be achieved through manual logging synchronized to a reference clock, video recording of the driver’s hands with a time overlay, or instrumenting the steering wheel with auxiliary sensors where feasible. The objective is to have an independent record of exactly when each steering wheel action occurred, allowing for accurate temporal alignment with LIN frames.

This level of annotation mirrors practices in GNSS record-and-replay testing, where field campaigns record not only GNSS signals but also contextual video, inertial measurements, and reference trajectories to enable detailed offline analysis and comparison.[28] Similarly, your LIN reverse engineering will benefit from “rich” contextual data beyond raw bus captures.

## 7. Safety Gates and Staged Validation for LIN Injection

### 7.1 Risks associated with injection on in-vehicle networks

Injecting messages on an in-vehicle network, even on a supposedly low-criticality segment such as a steering wheel LIN, carries risks. Altered control commands could trigger unintended user interface actions, confuse driver assistance systems if steering wheel inputs are used as mode switches, or interact with security features such as keyless entry or immobilizers if those functions share infrastructure.[20][27] Furthermore, injection can interfere with normal bus traffic, especially if collisions occur when both the original steering wheel module and an emulator attempt to respond simultaneously to a master’s request.[1] Such collisions might be interpreted as faults, triggering diagnostic trouble codes or fallback modes.

Automotive safety standards like ISO 26262 emphasize that fault injection testing, while valuable for robustness evaluation, must be conducted in a controlled and carefully planned manner, across unit, integration, and system test levels, with clear safety goals and risk assessments.[12] Similarly, validation frameworks encourage shifting verification “left” in the development cycle, prioritizing early lab-based and virtual testing over on-vehicle experimentation, to catch faults before they can affect safety.[11][26] These principles are relevant even in post-hoc reverse engineering efforts: the more testing can be done on bench setups or in isolated environments, the safer.

### 7.2 Staged validation: from passive capture to in-vehicle test

A sensible validation pipeline for 0x0C attribution and potential injection can be structured in stages that progressively increase interaction with the live vehicle:

First, passive capture and analysis in the vehicle. Only observation; no injection or modification of bus traffic. Reverse engineering, attribution, and payload semantics inference are done offline based on captured logs and annotations.

Second, bench replay and emulation. Once candidate semantics are inferred, develop a bench setup comprising LIN transceivers, a microcontroller or PC-based emulator, and a simulated master or slave to replay captured 0x0C traffic and emulate responses, verifying that checksums and payload mappings behave as expected without risking the vehicle.[1][9][30]

Third, isolated non-customer validation. Before any integration into a customer-usable vehicle, perform tests on a dedicated test vehicle or setup where failures or misbehavior have no safety or operational impact on end users. This might involve disabling certain safety-critical functions, physically constraining the vehicle (for example, on a lift or in a controlled area), or physically disconnecting non-essential modules.

Fourth, controlled in-vehicle tests. Only after passing previous gates and achieving high confidence in attribution and injection correctness should limited, constrained in-vehicle injection be attempted, with strict safeguards in place, such as limited duration, bounded value ranges, and immediate abort conditions.

This staged approach mirrors practices in other domains, such as GNSS record-and-replay, where signals are first tested in lab environments with replayed recordings before being deployed in live field tests.[28] It also aligns with the philosophy of driverless durability and misuse testing tools that prioritize safety and controllability when subjecting vehicles to extreme conditions.[24]

### 7.3 Hard-stop safety gates and must-pass criteria

At each stage, explicit hard-stop criteria should be defined such that failure to meet them prevents advancement to the next stage. These gates should be objective and verifiable. Key gates include:

Protocol correctness gate. Before any injection, demonstrate that your code and hardware can generate syntactically valid LIN frames with correct IDs, parity, and checksums, as verified by independent decoders or analyzers.[2][9][30] Bench testing must show that no malformed frames are produced under any expected condition.

Attribution confidence gate. Using the rubric described earlier, require that 0x0C achieve at least a pre-specified minimum confidence score, with strong evidence on temporal causality, strength of association, specificity, reproducibility, semantics, and exclusivity. If this threshold is not met, classification remains “uncertain” and no injection targeting 0x0C is allowed.

Collision avoidance gate. Verify that the planned injection strategy does not result in bus collisions, for example by ensuring that the emulator either acts as a master on a bench bus or, in the vehicle, only transmits when the original node is disconnected or when the bus schedule clearly allows an extra master frame without conflicting with existing ones.[1][2][30] If collision risk cannot be eliminated or acceptably mitigated, injection must not proceed.

Functional bounding gate. Define strict limits on what injected messages can do, such as restricting payloads to values observed in normal use and forbidding extreme or out-of-range values. This concept resembles bounding fault injection conditions under ISO 26262, where timing and amplitude of injected errors are chosen to avoid catastrophic failures while still testing robustness.[12]

State-aware safety gate. Incorporate state-awareness by checking vehicle state before allowing injections, in the spirit of SAID, which screens messages based on both semantics and vehicle dynamics to prevent entering dangerous states.[27] For example, injection of synthetic steering wheel controls may be allowed only when the vehicle is stationary and not in an automated driving mode.

Diagnostic and IDS compatibility gate. Assess whether injection patterns might trigger existing intrusion detection systems or diagnostic monitoring on the vehicle. Research shows that in-vehicle IDS can be sensitive to timing, correlation, and traffic-volume deviations.[10][27] If your planned injection would create abnormal timing or frequency patterns, re-evaluate and redesign it.

Fallback and abort gate. Implement reliable means to immediately cease injection if any unexpected behavior is observed, such as new warning lights, unexpected UI behavior, or bus errors. This is analogous to safety mechanisms in fault injection testing, where the system’s ability to detect and safely handle faults is verified, and testing is stopped if safety is at risk.[12]

### 7.4 Bench replay and emulator validation

The bench replay stage is particularly valuable from a safety standpoint. Using recorded 0x0C frames and your inferred semantics, you can construct a test harness where a LIN master polls a simulated steering wheel node. By substituting your emulator for the node, you can replay both captured and synthesized payloads, verifying that:

The emulator’s output matches expected byte-level patterns for given inputs.

Checksums are always correct and accepted by any test receivers.

Timing of frames aligns with the schedule used during captures.

No unintended interactions occur when multiple IDs are active.

Tools such as LIN analyzers and simulators from NI, Microchip, or Vector, which use LDFs to decode and simulate LIN traffic, can serve as reference points or test harnesses.[2][9][30] Even without an LDF, these tools can verify frame structure and timing. Bench validation at this level is analogous to unit and integration testing in safety-critical software development.[11][12][26]

### 7.5 Controlled in-vehicle injection: best practices

If, and only if, all previous gates are satisfied, limited in-vehicle injection can be considered. At this stage, best practices include:

Performing tests on a non-customer, controlled vehicle, ideally on a closed course or in a lab environment, with the ability to immediately power down or isolate the steering wheel LIN segment.

Starting with extremely conservative injections, such as replaying exact recorded 0x0C payloads under identical conditions, before attempting any novel payload transformations.

Using short-duration, single-function injections initially, with extensive monitoring of all relevant vehicle subsystems (infotainment, ADAS, warnings) for any anomalous behavior.

Gradually increasing complexity only after each simple test has been shown to be benign and reproducible.

Throughout, maintaining detailed logs of injected frames, vehicle responses, and any deviations from expected behavior creates an audit trail and supports iterative refinement.

These practices mirror cautious approaches to vehicle fault injection tests for ADAS and safety-critical systems, where faults are introduced in a controlled, observed manner and system responses are closely monitored to confirm that safety mechanisms behave as intended.[12][26]

## 8. Byte-Level Analysis Checklist and Decision Template

### 8.1 Byte-level analysis checklist for 0x0C

To ensure completeness and repeatability in the analysis of 0x0C’s payload, a structured checklist can be followed. This checklist guides the analyst through successive layers of analysis, from basic structural integrity to semantic interpretation and association with controls.

The checklist can be conceptually broken into categories: structural integrity, timing and scheduling, payload dynamics, checksum correctness, and semantic inference. An example table summarizing these checkpoints is provided below.

| Category | Checkpoint Description | Status/Notes (for operator) |
|---|---|---|
| Structural integrity  | Confirm that all observed 0x0C frames have valid IDs and consistent frame length (number of data bytes); verify no truncated or malformed frames in captures. | |
| | Confirm that PID parity bits are correct for 0x0C according to LIN specification across all frames. | |
| Timing and scheduling | Compute 0x0C frame inter-arrival times; verify stable period and low jitter consistent with LIN master schedule. | |
| | Confirm that 0x0C appears in all expected schedule cycles and does not show unexpected gaps or bursts unrelated to steering inputs. | |
| Payload dynamics | For each payload byte and bit, construct time series and count transitions; identify bits that change only when controls are active versus those that change continuously. | |
| | Detect candidate monotonic counters or sequence numbers and mark them as non-control fields. | |
| | For candidate control fields, compute differences between successive frames to detect signed-delta behavior and quantify typical delta magnitudes during active inputs. | |
| Checksum correctness  | Determine whether classic or enhanced checksum is used by recomputing checksums and comparing to observed values for a large sample of frames.[2][9] | |
| | Verify that checksum validation passes for all frames; investigate and explain any mismatches (noise, capture errors, etc.). | |
| Semantic inference | Map candidate bits/fields to specific steering controls (for example, “left scroll up”). Validate mapping via single-axis and mixed-input experiments as per experiment plan. | |
| | Quantify association strength between each candidate field and input type using correlation or classification metrics. | |
| | Confirm negative controls: demonstrate that candidate fields do not change during baseline segments and irrelevant input blocks. | |

Systematically filling out this checklist, with annotations and cross references to specific capture sessions and experiments, provides strong evidence for or against 0x0C’s control-bearing role and lays the groundwork for the go/no-go decision.

### 8.2 Go/no-go decision template for field operators

Field operators who may not be deeply involved in the analysis need a concise but rigorous template to decide whether to authorize any injection related to 0x0C. This template should capture, in a structured manner, the key outcomes of analysis, validation, and safety gating.

An example decision template can be organized into sections reflecting the gates discussed earlier: attribution evidence, bench validation, collision and state safety, and final authorization. The template can be filled in as a table to maintain clarity.

| Section | Question | Possible Responses (Operator Selects) | Notes/References |
|---|---|---|---|
| Attribution evidence | Has 0x0C been analyzed using the full byte-level checklist, with documented results? | Yes / No | If “No,” stop: injection not permitted. |
| | Does 0x0C meet or exceed the predefined rubric threshold for “control-bearing” attribution? | Yes / No | Specify rubric scores for each dimension; if any key dimension < threshold, stop. |
| | Are inferred payload semantics for 0x0C consistent across at least two independent experimental sessions? | Yes / No | Provide session IDs and summary results. |
| Bench validation | Has a bench setup been used to replay and emulate 0x0C frames, confirming correct checksums and expected behaviors? | Yes / No | If “No,” stop: in-vehicle injection not permitted. |
| | Have emulated 0x0C payloads been verified not to produce unintended behavior in bench or simulated receivers? | Yes / No | Describe any anomalies and resolutions. |
| Collision and state safety | Is the planned injection strategy free from bus collision risks, or are collisions controlled and benign? | Yes / No / Uncertain | If “No” or “Uncertain,” stop. Describe collision avoidance mechanisms or bus topology. |
| | Are injection conditions constrained to safe vehicle states (for example, stationary, no ADAS active)? | Yes / No | List allowed states and enforcement mechanism. |
| | Have potential interactions with diagnostic/IDS mechanisms been assessed, with low risk of triggering unsafe modes? | Yes / No / Uncertain | If “No” or “Uncertain,” reconsider or restrict injection plan. |
| Final authorization and scope | Is injection limited to replaying previously observed, in-range payload values for 0x0C? | Yes / No | If “No,” justify why extrapolated values are necessary and what protections limit their effect. |
| | Are abort mechanisms in place and tested to immediately stop injection upon anomalies? | Yes / No | Describe abort conditions and mechanisms. |
| | Final decision: is 0x0C injection approved for this test campaign under specified conditions? | Go / No-Go | Decision to be signed and dated by responsible engineer; attach supporting analysis documents and logs. |

This template ensures that the decision to proceed with injection is not based on intuition or informal judgments but on documented, reviewed evidence and safety considerations. It also creates traceability: future audits can trace the rationale and safeguards in place for each injection event.

## 9. Integrating Methodology, Statistics, and Safety into a Coherent Workflow

### 9.1 Aligning reverse engineering with safety-critical validation practices

The overall methodology described here reflects a convergence between applied reverse engineering practices and the more formal world of safety-critical verification and validation in the automotive sector. Safety validation frameworks emphasize structured strategies that integrate risk analysis, verification and validation (V&V), and early error detection throughout the development lifecycle.[11] While your project operates outside a traditional OEM development cycle, it must nevertheless respect the same core principles: clearly defined objectives, systematic testing strategies, and continuous risk assessment.

Fault-injection testing under ISO 26262, for example, requires that faults be introduced in a controlled manner at multiple levels of abstraction (unit, integration, system) and that system responses be evaluated, ensuring that safety mechanisms detect and handle faults without endangering passengers.[12] Similarly, any injection of LIN frames on a steering wheel network should be treated as a fault-injection event that, while benign in intent, could expose latent vulnerabilities. Hence, the structured gating and staged validation proposed here essentially place your work within an informal but rigorous safety framework.

### 9.2 Borrowing from intrusion detection and state-aware defenses

Research on hybrid intrusion detection systems for CAN networks has shown that structures like message IDs and payload bytes can differ significantly across vehicles and even across software updates, making rigid, vehicle-specific rules brittle.[10] To achieve vehicle-agnostic detection, these systems focus on timing and volume statistics, using features such as packet counts and inter-arrival intervals and their correlation patterns to detect anomalies.[10] This perspective is useful for your LIN context in at least two ways.

First, it encourages you to think beyond static payload semantics and consider patterns of timing and traffic volume when evaluating whether 0x0C behaves like a control-bearing frame. If 0x0C’s frequency or jitter changes in ways that correlate with steering wheel activity, this is an additional clue to its role. Second, it suggests that your injection should not disturb the global timing and volume characteristics of the LIN bus beyond what is observed in normal operation, otherwise you risk being detected by any existing or future IDS.

State-aware defenses such as SAID go even further by evaluating message semantics and their impact on vehicle dynamics, screening out messages that would lead to dangerous motions or states.[27] While SAID is presented in the context of CAN and diagnostic messages, the principle of evaluating the safety impact of message semantics before allowing them to influence vehicle state translates naturally to your plan. For instance, if 0x0C is eventually found to encode a steering wheel button that disengages a driver-assistance mode, injecting spurious presses when the vehicle is in automated control could have non-trivial implications; a state-aware safety gate would ban such injections under those states.

### 9.3 Confounding control and attribution reliability

The confounder adjustment literature emphasizes that, in complex observational settings, including all variables in a single multivariate model is often suboptimal; instead, confounders should be identified and adjusted for specifically for each exposure–outcome relationship.[22][23] In your context, each steering wheel control (for example, left scroll up) can be considered an exposure, and each candidate payload bit or field in 0x0C as an outcome. Confounding variables might include time, vehicle speed, other control usage, or broadly, global factors that create correlated changes in both exposures and outcomes.

Applying this logic means more than simply computing pairwise correlations. It means designing analyses that isolate the effect of each control on each payload feature, controlling for both time and other signals where appropriate. Stratifying by vehicle state, using multi-variable regression, and testing whether associations persist after adjusting for other candidate fields helps ensure that attribution is not spurious. The experimental matrix outlined earlier provides the necessary variation to support such analyses.

### 9.4 Signal detection and statistical decision thresholds

The analogy to signal detection from digital signal processing also guides how to set decision thresholds.[6] In classical detection problems, a detector computes a statistic (such as RMS energy) and compares it to a threshold to decide whether a signal is present.[6] The choice of threshold determines the trade-off between false alarms and missed detections. For your attribution problem, the “statistic” might be the performance of a classifier that predicts steering input from 0x0C payload, or the magnitude of a correlation coefficient; the “threshold” is the minimum acceptable performance for you to declare that 0x0C is control-bearing.

Selecting this threshold is inherently a risk management decision. A low threshold (easily declaring 0x0C as control-bearing) risks false attribution and potentially unsafe injections. A very high threshold may delay useful work but keeps risk low. Inspired by IDS research where AUROC values around 0.77 or higher are considered good for detecting attacks,[10][21] you might require similar or higher performance in predicting steering inputs from 0x0C payloads, especially given that you control the experimental design and thus can achieve relatively noise-free data.

### 9.5 Documentation, traceability, and repeatability

Throughout this process, meticulous documentation is essential. Each capture session, experiment block, analysis step, and decision should be recorded, along with versions of tooling and code. This not only supports internal rigor but also ensures that results are repeatable and auditable. If new evidence emerges, such as updated vehicle firmware changing LIN behaviors, you will be able to compare with past baselines and adapt attribution and gating strategies accordingly.

In many engineering disciplines, such as GNSS testing with record-and-replay, detailed recording of scenarios, signals, and environmental context is what allows for meaningful comparisons between devices and configurations.[28] Likewise, your LIN reverse engineering and injection work will benefit from a culture of “test as if you must explain it later,” maintaining a living knowledge base of 0x0C’s inferred semantics, confidence scores, and safety constraints.

## 10. Conclusion

The task of confidently attributing LIN frame ID 0x0C on a 2025 Tesla Model X steering wheel network to specific control functions, and then safely enabling any form of injection or emulation, demands a disciplined blend of protocol knowledge, experimental rigor, statistical reasoning, and safety-conscious engineering. LIN’s simple but rigid master–slave structure, with defined frame formats, sync bytes, PIDs, payloads, and checksums, provides a deterministic foundation upon which methodical reverse engineering can proceed, provided that checksum behavior, parity, and scheduling are correctly understood and respected.[1][2][9][30]

Lessons from CAN reverse engineering, such as the use of labeled time segments, change detection algorithms, and machine learning classifiers to infer message functions, demonstrate that bus traffic can be systematically decoded into functional semantics without resorting to guesswork.[4][7][14][17] Adapting these approaches to LIN entails carefully designed experiments in which steering wheel inputs are applied in isolated, repeated, and randomized patterns, with thorough annotations and synchronization, enabling robust association analyses between candidate payload bits in 0x0C and specific physical controls. By treating the attribution problem as a signal detection challenge in the presence of confounders, and by borrowing concepts from confounder adjustment in observational studies, one can design both experimental matrices and statistical analyses that minimize bias and maximize the reliability of inferences.[6][22][23]

At the heart of this work is a confidence-scoring rubric that decomposes the evidence into clear dimensions—temporal causality, strength of association, specificity, reproducibility, payload semantics, and exclusivity—and requires high scores across these axes before classifying 0x0C as genuinely control-bearing. Negative evidence, such as stability in baseline conditions and lack of response to irrelevant inputs, is as important as positive correlation. Bench replay and emulation, using LIN transceivers and analyzers, provide a safe environment to validate both decoding and encoding of 0x0C frames, ensuring that checksums, timing, and payload behaviors align with expectations before any in-vehicle activity is contemplated.[1][2][9][30]

Yet, even perfect attribution does not itself justify injection. Automotive safety practices, codified in frameworks like ISO 26262 and reflected in fault-injection testing methodologies and validation strategies, underscore that any deliberate perturbation of a safety-related system must be preceded by comprehensive risk analysis, staged validation, and robust safeguards.[11][12][26] Adapting this philosophy, a set of hard-stop safety gates has been articulated: protocol correctness, high attribution confidence, collision avoidance, functional bounding of injected values, state-aware safety checks, diagnostic and IDS compatibility, and reliable abort mechanisms. Only when all these gates are passed, and when injection is confined to narrow, well-understood scenarios on non-customer vehicles, should limited, monitored in-vehicle testing be attempted, and even then, starting with simple replay of observed payloads rather than arbitrary commands.[10][12][24][27]

Finally, a concise go/no-go decision template transforms this rich methodological scaffold into a practical tool for field operators. It ensures that decisions are grounded in documented evidence rather than intuition, that the scope of any injection is clearly defined and constrained, and that there is accountability through sign-off and traceability. As automotive networks become increasingly complex, and as both enthusiasts and security researchers continue to explore them, such structured, safety-first approaches will be essential to balance curiosity and innovation with the imperative of not endangering vehicles, occupants, or other road users.

## Citations

1. https://bitzero.tech/posts/2022/11/30/hacking-my-cars-climate-controls-lin-reverse-engineering - https://bitzero.tech/posts/2022/11/30/hacking-my-cars-climate-controls-lin-reverse-engineering
2. https://www.ni.com/docs/en-US/bundle/ni-xnet/page/lin-frame-format.html - https://www.ni.com/docs/en-US/bundle/ni-xnet/page/lin-frame-format.html
3. https://onlinepubs.trb.org/Onlinepubs/hrr/1968/247/247-002.pdf - https://onlinepubs.trb.org/Onlinepubs/hrr/1968/247/247-002.pdf
4. https://www.can-cia.org/fileadmin/cia/documents/publications/cnlm/december_2018/18-4_p4_reverse_engineering_of_can_communication_chris_quigley_david_charles_richard_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 - https://www.can-cia.org/fileadmin/cia/documents/publications/cnlm/december_2018/18-4_p4_reverse_engineering_of_can_communication_chris_quigley_david_charles_richard_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
5. https://www.theaudiogarage.com/https-www-bestcaraudio-com-can-you-keep-your-steering-wheel-controls-with-an-aftermarket-radio/ - https://www.theaudiogarage.com/https-www-bestcaraudio-com-can-you-keep-your-steering-wheel-controls-with-an-aftermarket-radio/
6. https://www.eecs.umich.edu/courses/eecs206/public/lab/lab1/lab1.pdf - https://www.eecs.umich.edu/courses/eecs206/public/lab/lab1/lab1.pdf
7. https://www.ece.iastate.edu/~zambreno/assets/pdf/YouSvo20A.pdf - https://www.ece.iastate.edu/~zambreno/assets/pdf/YouSvo20A.pdf
8. https://www.ulalaunch.com/docs/default-source/rockets/deltaiipayloadplannersguide2007.pdf?sfvrsn=4c924b53_2 - https://www.ulalaunch.com/docs/default-source/rockets/deltaiipayloadplannersguide2007.pdf?sfvrsn=4c924b53_2
9. https://www.csselectronics.com/pages/lin-bus-protocol-intro-basics - https://www.csselectronics.com/pages/lin-bus-protocol-intro-basics
10. https://pmc.ncbi.nlm.nih.gov/articles/PMC12986820/ - https://pmc.ncbi.nlm.nih.gov/articles/PMC12986820/
11. https://www.criticalsoftware.com/en/resources/automotive-off-road-safety-critical-validation - https://www.criticalsoftware.com/en/resources/automotive-off-road-safety-critical-validation
12. https://www.embitel.com/blog/embedded-blog/fault-injection-testing-of-safety-critical-automotive-software - https://www.embitel.com/blog/embedded-blog/fault-injection-testing-of-safety-critical-automotive-software
13. https://xray.greyb.com/ev-battery/fault-detection-isolation-evse - https://xray.greyb.com/ev-battery/fault-detection-isolation-evse
14. https://iris.unimore.it/bitstream/11380/1185929/1/08466914_mio.pdf - https://iris.unimore.it/bitstream/11380/1185929/1/08466914_mio.pdf
15. https://www.monnit.com/products/sensors/vehicle/detection-counting/ - https://www.monnit.com/products/sensors/vehicle/detection-counting/
16. https://onlinepubs.trb.org/Onlinepubs/hrr/1966/122/122-003.pdf - https://onlinepubs.trb.org/Onlinepubs/hrr/1966/122/122-003.pdf
17. https://www.csselectronics.com/pages/can-dbc-file-database-intro - https://www.csselectronics.com/pages/can-dbc-file-database-intro
18. https://www.nhtsa.gov/sites/nhtsa.gov/files/documents/19gi_g102_002_bsi_otsa_final-tag.pdf - https://www.nhtsa.gov/sites/nhtsa.gov/files/documents/19gi_g102_002_bsi_otsa_final-tag.pdf
19. https://turnpikemotors.com/whats-different-about-a-frame-alignment/ - https://turnpikemotors.com/whats-different-about-a-frame-alignment/
20. https://www.renesas.com/en/document/whp/defend-your-vehicle-against-relay-attack-defense-technology-against-latest-automotive-theft - https://www.renesas.com/en/document/whp/defend-your-vehicle-against-relay-attack-defense-technology-against-latest-automotive-theft
21. https://arxiv.org/html/2605.06264v1 - https://arxiv.org/html/2605.06264v1
22. https://pmc.ncbi.nlm.nih.gov/articles/PMC11881322/ - https://pmc.ncbi.nlm.nih.gov/articles/PMC11881322/
23. https://pmc.ncbi.nlm.nih.gov/articles/PMC4017459/ - https://pmc.ncbi.nlm.nih.gov/articles/PMC4017459/
24. https://www.abdynamics.com/solutions/durability-misuse-testing/ - https://www.abdynamics.com/solutions/durability-misuse-testing/
25. https://www.thethingsnetwork.org/forum/t/payload-formats-howto/3441 - https://www.thethingsnetwork.org/forum/t/payload-formats-howto/3441
26. https://www.ni.com/en/solutions/transportation/adas-and-autonomous-driving-testing/adas-and-autonomous-driving-validation/shifting-left-the-evolution-of-automotive-v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 - https://www.ni.com/en/solutions/transportation/adas-and-autonomous-driving-testing/adas-and-autonomous-driving-validation/shifting-left-the-evolution-of-automotive-v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
27. https://www.usenix.org/system/files/sec22-xue-lei.pdf - https://www.usenix.org/system/files/sec22-xue-lei.pdf
28. https://guide-gnss.com/gnss-record-replay-tests/ - https://guide-gnss.com/gnss-record-replay-tests/
29. https://www.youtube.com/watch?v=aR_IYHC7mpg - https://www.youtube.com/watch?v=aR_IYHC7mpg
30. https://www.wevolver.com/article/can-vs-lin-a-comprehensive-technical-analysis-of-automotive-and-industrial-network-protocols - https://www.wevolver.com/article/can-vs-lin-a-comprehensive-technical-analysis-of-automotive-and-industrial-network-protocols
