lakewoodphone/tesla-lin-chip/research/responses/2026-05-29-100-unit-dual-lin-ble-passthrough-board-manufacturing-plan-cd18bbbf.md

---
job_id: cd18bbbf-f056-461c-b2d3-4b41df94ea34
directive_id: 100-unit-dual-lin-ble-passthrough-board-manufacturing-plan
title: 100-unit dual-LIN BLE passthrough board manufacturing plan
domain: market
sensitivity: no_refusal_required
model_used: sonar-deep-research
provider: perplexity
status: complete
completed_at: 2026-05-29T18:49:15.439308+00:00
cost_usd: 0.40552
input_tokens: 747
output_tokens: 12984
reasoning_tokens: 43264
search_count: 31
citation_count: 29
verifier_status: passed
schema_version: 1
---

# Manufacturing Strategy for a Compact Tesla Steering-Wheel Dual-LIN + BLE Passthrough Board

The target product is a compact, in‑wheel LIN–to–BLE passthrough module intended for Tesla steering wheels, built around an ESP32‑S3 module and dual LIN transceivers. The aim is roughly 100 assembled units with minimal or no hand soldering, while respecting automotive electrical and safety realities. This report concludes that your current architecture—ESP32‑S3‑WROOM‑1U/‑1 plus two NXP TJA1021T/20 LIN transceivers—is fundamentally sound for low‑volume turnkey SMT assembly if you deliberately align your bill of materials (BOM) and footprints with one of the mainstream PCBA providers’ supply chains, and if you are willing to do a small pilot run first. JLCPCB or Seeed Fusion turnkey assembly, using an ESP32‑S3‑WROOM‑1‑N8R8 variant that is stocked in their ecosystem and NXP TJA1021T/20/CM,118 from a supported distributor, is the most economical route for 100 units, with MacroFab and PCBWay as higher‑touch but more expensive alternatives.[1][2][4][7][8][9][10][12][13][16][24][4][26] The critical manufacturing risks are RF performance inside a metal steering wheel environment, automotive transients (cold crank, load dump, and ESD) on the 12 V feed, mechanical reliability of connectors and harnessing, and firmware provisioning choices that could brick devices or complicate post‑deployment updates.[21][22][23][29] These can be controlled by careful PCB layout, appropriate protection devices, a robust power tree from 12 V to 5 V to 3.3 V, test and programming fixturing with pogo pins, and conservative use of ESP32 secure‑boot features.[19][20][22] A pilot of 5–10 assembled boards, using exactly the same assembly path and BOM as the later 100‑unit run, is strongly recommended before ordering the full batch.

---

## 1. System Context, Use Case, and Constraints

### 1.1 Functional Overview of the Steering-Wheel LIN–BLE Passthrough

The envisioned PCB sits inside the steering wheel or steering‑column module area and connects to two LIN buses that carry steering‑wheel button, scroll‑wheel, or related signals in Tesla vehicles. LIN (Local Interconnect Network) is a single‑wire, low‑speed automotive serial bus used for body electronics, typically at 12 V nominal with bus levels referenced to the vehicle ground, with transceivers such as the NXP TJA1021T converting between the LIN physical layer and a microcontroller’s UART.[5][14] Your board’s central microcontroller, an ESP32‑S3 module, provides BLE (and optionally Wi‑Fi) connectivity, internal application processing, and enough UARTs to connect to two separate LIN transceivers. The core functional behavior is thus: two LIN networks in and out via TJA1021‑class transceivers, plus a BLE link (and perhaps Wi‑Fi) to communicate with external devices for control, monitoring, or firmware updates.

Because this device lives in a safety‑relevant area of the vehicle (the steering wheel, near the airbag and driver controls), even if it does not directly control the airbag or steering, your design is entangled with safety and regulatory concerns. Tesla’s own airbag recall documentation shows how even a seemingly small mismatch between steering‑wheel variants and their corresponding airbag assemblies becomes a formal safety defect due to the potential to degrade airbag performance.[15] While you are not altering airbags, any aftermarket device that modifies steering‑wheel wiring, harnesses, or signal paths must be robust, detectable in failure modes, and non‑interfering. This context pushes you away from improvised, hand‑built solutions and toward repeatable, professionally assembled hardware with structured testing and traceability.

The intended volume of around 100 units positions the project in a classic low‑volume manufacturing regime. This is too many units for hand assembly to be efficient or consistent, yet too few to access the most aggressive pricing tiers at high‑volume contract manufacturers. It is precisely the niche where online turnkey PCBA providers like JLCPCB, PCBWay, MacroFab, and Seeed Fusion excel, provided you design within their process and BOM constraints.[4][7][8][9][12][13][16][24][4][26] The main challenge is to pick an assembly path and component set that minimizes friction, unexpected substitutions, and hand‑soldering, and to structure your design for manufacturability, testability, and automotive robustness.

### 1.2 Architectural Choices: ESP32-S3 Module plus Dual LIN Transceivers

You have chosen the ESP32‑S3‑WROOM‑1U‑N8R8 module as the core MCU, with an ESP32‑S3‑WROOM‑1‑N8R8 PCB‑antenna variant as a fallback.[1][10][11] The ESP32‑S3 family offers dual‑core Xtensa CPUs, BLE and Wi‑Fi, ample flash (8 MB in N8R8 variants), and ESP‑IDF support for secure boot and flash encryption, which are useful if you later choose to harden your firmware against tampering.[1][10][20] The 1U variant integrates a U.FL or IPEX connector for an external antenna, which is advantageous in a metal‑rich steering‑wheel cavity where on‑board PCB antennas may be detuned or shielded.[11][25] The 1‑N8R8 variant with a PCB antenna is widely stocked by JLCPCB and LCSC, and JLC explicitly lists ESP32‑S3‑WROOM‑1‑N8R8 (C2913201) as an assembly part.[1][10] For turnkey assembly, using a module variant that appears in the PCBA vendor’s own component library is a significant simplification.

On the LIN side, you have selected two NXP TJA1021T/20 devices per board. The TJA1021 is a LIN 2.1 / SAE J2602 / ISO 17987 compliant transceiver designed to interface between a LIN protocol controller (which in your design is implemented in software on the ESP32‑S3) and the single‑wire LIN bus, and is offered in an 8‑lead SO8 plastic package.[2][5][5] The TJA1021 family is specifically meant for automotive environments, with features such as dominant time‑out, bus wake‑up, and short‑circuit protection, and it is a standard choice for LIN nodes.[5] NXP offers ordering codes such as TJA1021T/20/CM,118, which appears in JLCPCB’s library.[2][5][5] As a backup, TI’s TPIC1021D family and other LIN transceivers in TI’s catalog provide similar functionality, and can serve as alternates if NXP supply tightens.[14]

From a manufacturability standpoint, both the ESP32‑S3‑WROOM modules and the TJA1021T transceivers are standard SMT packages (castellated module plus SOIC‑8 ICs) well within the capabilities of low‑volume assembly houses, which routinely handle RF modules, fine‑pitch ICs, and SOIC packages.[1][2][4][7][8][9][12][13][16][4] The real constraints will be component sourcing, whether your chosen PCBA provider is willing to place these specific parts (especially the module), your connector choices, and how many of your passives and protection parts can be drawn from the provider’s “basic” or “in‑stock” catalog rather than special‑ordered “extended” parts.[12][16][26]

---

## 2. Component Strategy and BOM Alignment

### 2.1 Evaluating ESP32-S3 Module Options for Assembly

The first key question is whether to retain the ESP32‑S3‑WROOM‑1U‑N8R8 as your primary MCU module or to instead design around a variant more commonly stocked by the assembly houses, notably ESP32‑S3‑WROOM‑1‑N8R8 (PCB antenna) that JLCPCB offers as part C2913201.[1][10] According to JLCPCB’s part detail page, ESP32‑S3‑WROOM‑1‑N8R8 is listed as a Wi‑Fi module component available for SMT assembly, with JLCPCB managing stock, pricing, and datasheet access, which indicates they are comfortable placing this RF module in turnkey PCBA jobs.[1] LCSC, which is associated with JLCPCB, also lists ESP32‑S3‑WROOM‑1‑N8R8 as an in‑stock component, with price and order quantity information.[10] By contrast, ESP32‑S3‑WROOM‑1U‑N8R8 appears in distribution channels such as TME, where it is orderable but not necessarily integrated into JLCPCB’s “basic” component library.[11] That means JLCPCB could still place it via “extended” or consigned parts, but you would incur higher per‑line setup costs and longer lead times.[12][16][26]

In addition, the 1‑N8R8 module has extensive reference designs and community usage in 4‑layer IoT boards, including a KiCad tutorial that walks through schematic and PCB layout for an ESP32‑S3‑based design and emphasizes following Espressif’s reference layout, particularly around the antenna and RF ground keep‑outs.[3] This gives you a well‑trodden path for layout and helps the PCBA house’s DFM checks. Modules with integrated PCB antennas remove the need for an external coax and antenna assembly, but this can be a liability if the board is deeply embedded in metal, such as inside a steering‑wheel frame. RF design guidelines and shielding notes stress that metal close to an antenna reduces efficiency and detunes the antenna, and that maintaining a clear plastic window or externalized antenna improves performance.[25]

Given these factors, a pragmatic strategy is to architect your PCB so it can accommodate both the 1U and 1 variants with only a BOM change and a small RF layout compromise. You can place the module footprint in a position adjacent to a plastic section of the steering wheel trim, and reserve pads for a U.FL connector or external antenna feed so that when you use the 1U module you route the RF path to a better location, and when you use the 1 module you rely on the PCB antenna. This gives you SKU flexibility: for the 5–10 unit pilot and first 100 units, you can take advantage of ESP32‑S3‑WROOM‑1‑N8R8 which JLCPCB can source directly,[1][10] and only move to the 1U‑N8R8 variant if field testing shows unacceptable RF performance in the steering‑wheel cavity.

From an automotive robustness perspective, the ESP32 module itself is not AEC‑Q100 certified, but this is typical for aftermarket electronics and retrofit modules. The critical aspects are power‑supply robustness, transient suppression, and ensuring that any failure of the module does not disturb the LIN bus behavior of the rest of the vehicle. Using a well‑supported, mainstream module family with robust software and security features is prudent. Espressif’s documentation on secure boot v2 shows that ESP32 devices can enforce signed firmware and flash encryption to prevent unauthorized code from running, but it also highlights risks such as bricking the device if the secure boot is misconfigured or the signing key is lost.[20] For early production, it is wiser to leave secure boot disabled or in a soft‑enforcement mode until your update pipeline is mature.

### 2.2 LIN Transceiver Options and Availability

On the LIN side, your base choice of NXP TJA1021T/20/CM,118 is well aligned with automotive requirements. NXP’s product information page describes the TJA1021 as a LIN transceiver supporting LIN 2.1 and SAE J2602 standards, in an SO8 package, with protection features and mode control suitable for use as a leader or follower node.[5][5] The TJA1021T/20/CM,118 variant corresponds to a specific temperature range and mode configuration, and is widely distributed through NXP channels.[5][5] JLCPCB lists TJA1021T/20/CM,118 as a LIN transceiver component in their assembly library, which strongly suggests they can source and place it as an extended component.[2] While it will not be a “basic” in‑stock part like standard resistors or capacitors, it is sufficiently mainstream that extended sourcing fees are acceptable at the 100‑unit scale.[2][12][26]

As a backup, you mentioned TI’s TPIC1021D and related variants. TI’s LIN transceiver catalog lists multiple devices with features similar to the NXP TJA family, including wake/inhibit options and multi‑channel variants, and supports up to 24 V systems.[14] These parts are more likely to be sourced through Digikey or Mouser for consignment or for full turnkey assembly from US‑based providers like MacroFab.[8][14][24] However, for a JLCPCB‑centered supply chain, sticking with NXP’s TJA series, which appears in their library, is simpler.[2][5][5]

You also need to decide whether to use two independent LIN transceivers (for truly separate buses) or a multi‑channel transceiver. Given that your application is a passthrough or bridge between two LIN segments and BLE, it is often clearer to have two completely separate TJA1021 devices, each attached to its own UART and controlled by the ESP32, which can then decide when to forward or intercept traffic. From a PCB assembly perspective, placing two SO8 devices adds negligible complexity, and the per‑unit cost of the transceivers is small relative to the ESP32 module and assembly labor.

### 2.3 Other Key Components: Power, Protection, and Connectors

The board will draw power from the vehicle’s 12 V supply in or near the steering wheel. Automotive 12 V systems are noisy and can experience a variety of transients, including cold crank dips, load dump surges, and switching noise from alternators, motors, and other actuators.[23] A robust design uses a combination of TVS diodes, filters, and DC‑DC conversion. Technical articles on automotive transient protection highlight that TVS devices provide a low‑impedance path to ground during high‑voltage transients, clamping the voltage and protecting downstream electronics, and are typically implemented as PN junction diodes designed to enter avalanche mode under surge conditions.[21] Load dump events, where the battery is disconnected while the alternator is charging, can generate tens of volts for hundreds of milliseconds; protecting against this requires appropriately rated TVS devices and possibly additional protection circuitry.[23]

Downstream from the 12 V node, you need at least one buck converter to step down to 5 V, and then either feed the ESP32 module’s 5 V input (if using a dev‑like module) or further step down to 3.3 V using a regulator tailored to your consumption and noise requirements. Guidance specific to powering ESP32 modules from 12 V emphasizes that connecting 12 V directly will irreversibly damage the device, and that using a buck converter to step down 12 V to 5 V and then using the ESP32’s own regulator or a secondary regulator is the best practice.[22] Buck converters such as LM2596 or MP1584 can drop 12 V to 5 V efficiently and safely, with fixed or adjustable models allowing you to tune the output and avoid heat buildup.[22] Many PCBA providers stock generic buck regulator ICs and inductors, but if you have particular efficiency or EMI goals, you may need to choose extended or consigned parts and carefully specify them in the BOM.

Connectors and harness interfaces are another important consideration. A steering‑wheel‑embedded module will likely connect via a short harness to existing in‑wheel connectors, or possibly inline with existing cables. Mechanical design guidance on wire harnesses stresses the importance of bend radius, strain relief, and secure routing to avoid fatigue and intermittent failures over time.[29] From an assembly perspective, many low‑volume PCBA houses will place certain types of SMT connectors (for example, board‑edge headers or USB‑C sockets) but may not handle specialized automotive harness connectors unless they are SMT and fit within their pick‑and‑place tooling capabilities.[4][7][8][9][12][13][16][4] Through‑hole or press‑fit connectors are often either not supported or require manual insertion at additional labor cost.

Because you want to minimize hand soldering, you should choose SMT connectors that your chosen PCBA provider is comfortable placing, and only reserve the most specialized harness connectors for hand installation if absolutely necessary. For debugging and firmware loading, you can avoid adding a permanent connector by using pogo‑pin test pads. Pogo pins are spring‑loaded contacts that maintain conductivity over a stroke and can interface with exposed pads on a PCB without a mated connector.[19] A dedicated programming fixture with pogo pins for UART, reset, boot, and power can allow you to program and test each board without adding cost or bulk to the PCB.[19]

### 2.4 Summary Assessment of BOM Direction

Bringing these elements together, the BOM direction that best matches your constraints is:

1. Keep the ESP32‑S3‑WROOM module family but prefer ESP32‑S3‑WROOM‑1‑N8R8 for initial production, with your layout accommodating a switch to the 1U variant if external antennas are needed.[1][10][11][25]  
2. Use two NXP TJA1021T/20/CM,118 LIN transceivers per board, which JLCPCB and other assembly houses can source as extended parts.[2][5][5]  
3. Select a buck converter and associated inductors and capacitors that are either basic or widely available as extended parts in your chosen PCBA provider’s library, sized for at least 2–3× your expected current draw and with appropriate automotive transient ratings.[12][16][21][22][23]  
4. Use SMT connectors that are in the provider’s catalog for power and LIN harness connections, and rely on test pads plus pogo‑pin fixtures for programming and test.[4][7][8][9][12][13][16][19][4]  

This approach retains your core component strategy and improves manufacturability without forcing a full redesign around vendor‑proprietary modules.

---

## 3. Small-Batch PCBA Options and Comparative Analysis

### 3.1 JLCPCB: Cost-Optimized Turnkey PCBA for 100 Units

JLCPCB is one of the most prominent online PCB and PCBA providers for low‑to‑medium volumes, with strong integration with the LCSC component catalog.[1][2][4][10][12][16][4][26] Their ordering workflow involves uploading Gerber files, a BOM, and a component placement list (CPL), followed by an online review and quote for boards, components, and assembly.[4][4] JLCPCB differentiates between “Economic” and “Standard” PCBA services. Economic PCBA is cheaper for small runs but has more constraints on PCB options and component selection; Standard PCBA is more flexible but has higher setup costs.[26]

According to user documentation and community experience, Economic PCBA at JLCPCB is limited to a subset of PCB colors, layer counts, and finishes, and has a quantity ceiling (often around 50 boards per order).[26] It also cannot use V‑cut panelization; self‑panelization using tab routing and “mouse bites” is allowed but must be designed into the Gerbers.[17][26] Economic PCBA uses JLC’s “basic” parts without additional setup fees, while “extended” parts incur a per‑part setup charge (often around a few dollars per distinct extended part).[26] Standard PCBA, by contrast, allows more PCB customization and panelization options, and charges a per‑component placement fee plus a larger project setup fee, but treats both basic and extended parts more uniformly, making it suitable for BOMs with many extended items.[26]

For your application, the key JLC‑specific advantages are:

1. ESP32‑S3‑WROOM‑1‑N8R8 is directly available in JLC’s library (C2913201).[1][10]  
2. NXP TJA1021T/20/CM,118 is also in their component library as a LIN transceiver.[2]  
3. JLCPCB publishes PCB manufacturing and assembly capabilities, including minimum track width, spacing, supported layers, and other rules, which you can design to.[12]  

The main downside is that many automotive‑grade protection parts (special TVS diodes, high‑spec buck regulators, specialized connectors) may only be available as extended parts or not at all. This is manageable if you limit the number of extended parts and accept the extended fees, but if your BOM ends up heavily extended, the cost advantage shrinks.

Given your volume of 100 units, you would almost certainly use Standard PCBA rather than Economic PCBA, because Economic PCBA may cap out at around 50 boards and restricts features like V‑cut panelization.[26] With Standard PCBA, JLC can panelize your design if needed, place the ESP32 module and LIN transceivers, and handle most passives and regulators. Pricing will depend on PCB complexity and BOM, but for a compact 4‑layer board, per‑unit assembly cost at 100 units is typically acceptable, especially compared to your own labor cost for hand soldering 100 modules and transceivers.

JLCPCB publishes a blog and documentation on PCB assembly and process control, indicating that they provide SMT/THT/mixed assembly, with attention to electronic component sourcing and quality.[16] They also offer a smart ordering flow where you upload files, review the component mapping, and then approve the order, consistent with the KiCad workflow shown in an ESP32‑S3 PCB design video where the designer exports Gerbers, drill files, BOM, and CPL, then uploads to JLC, reviews component matching, and confirms assembly.[3][4][4] Overall, JLCPCB is the most naturally aligned with your current component choices.

### 3.2 PCBWay: Flexible Capabilities with Competitive Pricing

PCBWay is another China‑based PCB and PCBA provider offering prototype and low‑volume production services.[7][13] Their capabilities documentation lists a wide range of PCB options, including multiple layers, different materials, and advanced features.[13] PCBWay emphasizes quick‑turn prototyping and low‑volume production, and advertises PCB assembly in addition to bare board fabrication.[7][13] While they do not have as tightly integrated a component catalog as JLC + LCSC, they can source parts or accept consigned components.

In practice, using PCBWay for your project would involve sharing your BOM with specific manufacturer part numbers (e.g., ESP32‑S3‑WROOM‑1‑N8R8, TJA1021T/20/CM,118) and letting them quote the sourcing and assembly. They are generally capable of placing RF modules and SOIC‑8 ICs, as these are common in IoT and automotive projects.[7][13] However, because there is no built‑in guarantee that they have your exact ESP32 module and LIN transceivers in a pre‑stocked library, there is higher friction in initial quoting and more variability in lead times.

PCBWay may be attractive if you need more sophisticated board capabilities than JLC’s Economic or Standard services, or if you want an alternate vendor for risk diversification. For a single 100‑unit project where BOM components align well with JLC’s catalog, PCBWay is likely to be somewhat more expensive and slower, without compensating benefits, unless you find that JLC cannot source specific automotive‑grade parts you require.

### 3.3 MacroFab: North American PCBA with Flexible Sourcing

MacroFab is a North American‑based online manufacturing platform that aggregates more than 100 factory lines and offers cloud‑managed PCB assembly for a wide range of volumes.[8] MacroFab positions itself as a flexible provider where you can ramp production up or down without sacrificing quality, and they can source components from major distributors like DigiKey and Mouser or accept consigned parts.[8][24] For a 100‑unit run, MacroFab will likely be significantly more expensive on a per‑unit basis than JLC or PCBWay, but you benefit from easier communication, potentially higher process transparency, and direct integration with US distribution channels.

For your specific BOM, MacroFab can source ESP32‑S3‑WROOM‑1U‑N8R8 and NXP TJA1021T/20/CM,118 from legit distributors such as Mouser, DigiKey, or NXP’s authorized network, and can also easily incorporate TI TPIC1021D or other LIN transceivers if you choose to switch.[5][8][5][14] This reduces the need to compromise the BOM to fit a specific PCBA vendor’s in‑house catalog. However, turnkey assembly costs for 100 units, especially with automotive protection parts and connectors, may be high enough that your total project budget becomes uncomfortable.

MacroFab is most attractive if your priority is supply‑chain robustness, compliance, and support rather than absolute cost. If you anticipate scaling beyond a few hundred units and perhaps pursuing more formal automotive certifications, working with MacroFab or a similar higher‑end provider could pay off. For the immediate goal of 100 units, it may be overkill unless JLC/PCBWay/Seeed cannot meet specific requirements.

### 3.4 Seeed Fusion: Turnkey PCBA with Strong IoT Focus

Seeed Studio’s Fusion PCB Assembly service offers fast turnkey PCBA, with low‑cost options and the ability to handle advanced PCBs.[9] They advertise prices “from as little as $4.90 for 10 pieces” in their low‑cost tier, and also offer premium and advanced service tiers with more customization and higher‑end features.[9] Seeed has an ecosystem oriented around IoT and embedded devices, and they are comfortable with RF modules, sensors, and small‑batch assemblies.

Seeed Fusion’s turnkey nature means they can source components directly or accept consigned parts, similar to MacroFab but often at lower cost due to Chinese manufacturing bases.[9][24] Their component sourcing is not tied to a single specific catalog like LCSC, but they maintain a network of suppliers. This can be helpful if you want to use ESP32‑S3‑WROOM‑1U‑N8R8 specifically and cannot find it in JLC’s library. You provide the BOM with manufacturer part numbers, and Seeed quotes the sourcing and assembly.

For your 100‑unit run, Seeed Fusion is a strong alternative to JLCPCB if you find friction with JLC’s extended parts policies or if you want slightly more flexible component sourcing while still benefiting from cost advantages of Asian manufacturing. They will place RF modules, SOIC‑8 ICs, and protection devices, as long as sourcing is feasible.[9] Their published pricing suggests that 100‑unit runs with moderate BOM complexity can be economically viable, though not as cheap as the rock‑bottom JLC Economic tier.[9][24]

### 3.5 DigiKey/Mouser Kit + Local Assembly

An alternate path is to source all components yourself from distributors like DigiKey or Mouser, kit them (i.e., bag and label all parts), and then send them, along with your bare boards, to a local assembly house for contract SMT assembly.[14][24] This approach gives you maximum control over component choice and genuine automotive‑grade parts, and can simplify verifying counterfeits or substitutions. It also lets you keep ESP32‑S3‑WROOM‑1U‑N8R8 as your primary module even if online PCBA vendors do not stock it.[11][20][22]

However, small‑batch local assembly is often relatively expensive, especially when you add your own labor for BOM management, kitting, and inbound inspection. Typical local assembly houses also have minimum charges per job and may not offer the tight cost control of JLC or Seeed. Moreover, you must manage shipping bare boards, parts, and then finished assemblies, which adds logistics overhead. For 100 units of a compact board, this path is defensible if you require automotive‑grade traceability or have strong preferences for local manufacturing, but purely economically it is inferior to a JLC or Seeed turnkey approach.

From an ease‑of‑use standpoint, online turnkey PCBA services are simply smoother: you upload files, review component mapping, and then track your order.[4][5][8][9][24][4] Local assembly requires more back‑and‑forth, quotes, and management, which may not be justified at this scale.

### 3.6 Comparative Conclusions

Weighing the options, the most practical PCBA paths for your 100 units are:

1. JLCPCB Standard PCBA, with a BOM aligned to their basic and extended component library, using ESP32‑S3‑WROOM‑1‑N8R8 and NXP TJA1021T/20/CM,118 as primary parts.[1][2][4][10][12][16][4][26]  
2. Seeed Fusion turnkey PCBA, sourcing whatever ESP32‑S3 module and LIN transceivers you specify, with slightly higher cost but more sourcing flexibility.[9][24]  

PCBWay and MacroFab remain viable alternatives, but they are either less naturally aligned with your current BOM (PCBWay) or significantly more expensive (MacroFab).[7][8][13] DigiKey/Mouser kit plus local assembly is conceptually simple but operationally heavier and usually costlier at 100 units.

Given your constraints—minimal hand soldering, roughly 100 units, automotive environment but not full OEM‑scale certification—JLCPCB Standard PCBA is the primary recommendation, with Seeed Fusion as a backup if specific parts prove difficult to source via JLC.

---

## 4. Assembly Scope: What to Automate and What to Hand-Install

### 4.1 Target for Full SMT Assembly

To minimize hand soldering, your assembly scope should include all SMT devices that significantly affect reliability, have fine pitches, or would be tedious to hand place 100 times. This includes:

1. ESP32‑S3‑WROOM module. RF modules benefit from reflow soldering with controlled profiles. Hand soldering 100 modules is time‑consuming and increases rework risk.[1][3][18]  
2. LIN transceivers (NXP TJA1021T/20/CM,118 or TI TPIC1021D). SOIC‑8 devices are easy to hand solder, but 200 transceivers across 100 boards is not trivial, and machine placement improves consistency.[2][5][5][14]  
3. Power‑management ICs (buck converter, LDOs), inductors, and associated passives. Correct soldering of these parts is crucial to avoid thermal and electrical stress.[12][16][21][22][23]  
4. Protection devices (TVS diodes, ESD suppressors) on the 12 V input and LIN lines. These are often small SMD devices that benefit from reflow reflow soldering.[21][23]  
5. All decoupling capacitors, pull‑ups, resistors, and signal‑conditioning elements. These components are numerous and tedious to hand place, and using common values that fall into the PCBA provider’s basic library reduces extended costs.[12][16][26]  
6. SMT connectors where possible, especially for power and LIN harness connections, as long as they are compatible with your chosen PCBA house’s capabilities.[4][7][8][9][12][13][16][4]  

By designing footprints for these items that match your provider’s preferred land patterns, and by generating accurate BOM and CPL files, you can let the PCBA house fully assemble your boards and receive essentially ready‑to‑test units.

### 4.2 Parts Likely Requiring Hand Soldering or Post-Assembly Work

Even with turnkey SMT assembly, some elements may still need manual work:

First, through‑hole or specialized connectors. If your wiring harness requires through‑hole automotive connectors or bulky headers that the PCBA house cannot wave solder or hand place economically, you may need to solder these yourself. Some PCBA providers will do mixed SMT/THT assembly, but the cost per through‑hole joint can be non‑trivial and may not be worth it for just a few connectors per board.[16][26] You can mitigate this by preferring SMT connectors and using strain relief in the harness, but you may still have to hand install any unique automotive connectors.

Second, mechanical fixtures, mounting hardware, and potting or conformal coating. PCBA houses generally do not handle mechanical integration into enclosures, potting, or applying coatings, unless you contract additional value‑added services. You will likely need to screw the boards into their housings, apply gaskets, and optionally handle conformal coating yourself or via a specialized contractor.

Third, rework or tuning operations such as adding external antennas or coax leads, if you decide after testing that RF performance with the PCB antenna is insufficient. If your layout is prepared for the 1U module and an external antenna, but your PCBA house primarily assembles the 1 module, you may need to hand install coax jumpers or surface‑mount antennas on a subset of boards for RF characterization.

Fourth, programming and provisioning. Even if the ESP32 module can be preprogrammed by the PCBA provider, you will probably want to perform your own final programming and provisioning process to load firmware, set configuration, burn serial numbers, and optionally enable secure boot and flash encryption.[20] This is usually done via a pogo‑pin fixture and does not involve soldering, but it is post‑assembly work that must be considered.

Overall, the fraction of manual labor can be kept modest if you design for full SMT assembly and limit special connectors. Hand installation should be reserved for connectors truly incompatible with SMT, mechanical integration tasks, and special RF or security provisioning operations.

---

## 5. Manufacturing Design Guidance

### 5.1 PCB Layout, Panelization, and Fiducials

Good manufacturing outcomes begin with a design that respects your PCBA provider’s capabilities. JLCPCB documents their PCB manufacturing and assembly capabilities, including minimum track width, spacing, copper weight, hole sizes, and panel dimensions.[12] PCB panelization is a crucial lever for efficiency in small runs: panelization arranges multiple copies of the board on a single larger panel so that assembly lines treat them as a single unit, then they are depanelized afterwards.[17] This reduces handling time and improves throughput. An article on PCB panelization explains that V‑scoring and tab routing with perforated “mouse bites” are the two main methods for separating boards from a panel.[17]

V‑scoring involves cutting V‑shaped grooves into the panel’s top and bottom surfaces along separation lines, leaving a thin web that can be snapped apart; it allows boards to be placed edge‑to‑edge and is ideal for rectangular boards.[17] Tab routing uses routed slots with small tabs that hold the boards together and are broken after assembly; it requires some spacing between boards and may need manual depanelization or tools.[17] Not all panelization methods are supported by all PCBA houses. For example, JLCPCB’s Economic PCBA does not support V‑cut panelization, so boards must be self‑panelized with tab routing and mouse bites, whereas Standard PCBA is more flexible.[26]

Best practices for panelization include maximizing the number of boards per panel while retaining enough spacing for depanelization, keeping components at least 1–2 mm from board edges to avoid damage during depanelization, adding rails 5–10 mm wide along panel edges for structural support, and incorporating fiducials and tooling holes.[17] Fiducials are small copper targets (e.g., 1 mm diameter) used for machine alignment, typically placed in three corners of the panel, and along with tooling holes, they ensure placement accuracy within tens of microns.[17] 

For your board, a compact rectangular shape is highest yield. If each board is, for example, 30 mm × 40 mm, you can panelize dozens of boards on an 18 × 24 inch panel, subject to your vendor’s maximum panel size.[12][17] JLCPCB can also perform panelization on their side if you request it during ordering, particularly in Standard PCBA. You must, however, keep your board outline and keep‑out zones within their design rules.

### 5.2 Paste Layer, Stencils, and Reflow Profiles

A properly defined solder paste layer and stencil is essential to reliable SMT assembly. Your PCB design tools (such as KiCad) generate paste layers based on footprint pad definitions. PCBA houses like JLCPCB generate stencils from these layers and use them to apply solder paste before component placement and reflow.[3][4][12][16][4] For RF modules like ESP32‑S3‑WROOM, the footprint needs a carefully defined pad geometry, including solder mask openings and paste apertures that avoid tombstoning or solder bridging; using Espressif’s recommended footprint is important.[1][3]

You do not need to manage the stencil directly when using turnkey services: they generate and manage it as part of the assembly process. However, you should ensure that your footprints have correct layer assignments and there are no unusual paste‑mask edits. Any thermal pads (e.g., under power regulators) should have a segmented paste pattern to avoid voids and solder pumping.

Espressif modules and many ICs have moisture sensitivity levels that require controlled reflow profiles. Espressif states that all ESP32 modules have a moisture sensitivity level (MSL) of 3 and must be dry‑packed, which typically involves desiccant materials and humidity indicators in sealed bags.[18] If MSL 3 parts are exposed to ambient for too long before reflow, they may absorb moisture and experience damage (popcorning) during reflow. PCBA houses are accustomed to handling MSL‑sensitive parts, but if you decide to consigned‑supply ESP32 modules, ensure they remain sealed or are properly baked before assembly.[18]

### 5.3 Test Pads, Programming, and Pogo-Pin Fixtures

To test and program each board without adding dedicated connectors, you should include test pads on the PCB for all necessary signals: at least 3.3 V (or 5 V if used), GND, ESP32 UART0 TX/RX, EN (reset), and GPIO0 (boot mode), plus any LIN bus signals you wish to exercise during test, and possibly key GPIOs for functional checks. These pads should be accessible from one side of the board and arranged in a pattern compatible with a pogo‑pin fixture.

Pogo pins are spring‑loaded contacts that can be mounted in a fixture to press against exposed pads on the device under test. A detailed demonstration of a pogo‑pin‑based programming fixture shows how a custom fixture PCB, loaded with pogo pins, can mate with a target board’s test pads to provide power, a debug UART, and I/O signals for programming and test, without requiring any connector on the target board.[19] The advantage is that it adds no cost or area to the product PCB; only the fixture contains the pogo pins and connectors. The target board is simply aligned and pressed into place for programming.

You can design the fixture PCB in KiCad or another EDA tool, ensuring that the pogo pins line up with the test pads on your product PCB. The fixture can be used both for ESP32 firmware programming via UART and for LIN functional testing by connecting the LIN transceivers to a LIN master simulator or a test harness. This approach scales well to 100 units and beyond as long as you have a robust mechanical design for alignment and contact pressure.

### 5.4 Programming, Provisioning, and Security Flow

Once boards are assembled, you will need a defined programming and provisioning flow. For the ESP32, the standard development flow uses esptool via UART, and ESP‑IDF supports enabling secure boot v2 and flash encryption to protect against unauthorized firmware.[20] Secure boot v2, as described by Espressif, uses RSA‑PSS signatures on the second‑stage bootloader and application binaries, and the first‑stage ROM bootloader verifies these signatures before executing code.[20] The process involves generating a signing key, configuring the project to require signed images, building the bootloader and app, flashing them, and then enabling secure boot on the chip, which locks the boot process to signed firmware only.[20]

Espressif’s documentation emphasizes several security best practices: generate signing keys on a system with good entropy, keep keys private, avoid side‑channel leaks during key generation and signing, and combine secure boot with flash encryption to prevent local readout of flash contents.[20] It also notes that wrong configuration, losing keys, or mis-flashing the bootloader can brick devices. Furthermore, to increase security, options such as disabling JTAG and UART ROM download mode can be enabled, but these also remove debugging avenues.[20]

For a first production run of 100 boards, a conservative approach is to:

1. Use a non‑secure boot configuration initially, or at most soft‑enforce application signing without irrevocably locking the chip, so you can recover from errors.  
2. Put each board through a programming step via the pogo‑pin fixture where you flash a factory firmware, set unique identifiers, and run tests.  
3. Plan for a future revision where you enable full secure boot and flash encryption once you are confident in your firmware update process and key management.  

Your programming station can integrate a LIN bus test harness, BLE scanners, and automated scripts to verify that each board comes up with stable BLE advertisement, correct LIN communication, and proper identification.

### 5.5 Manufacturing Data Integrity: BOM and CPL Accuracy

The KiCad‑based workflow described in the ESP32‑S3 PCB design tutorial underlines the importance of generating accurate BOM and CPL files, and verifying component mapping in the PCBA house’s online tool.[3][4][4] In the example with JLCPCB, after uploading the Gerber, BOM, and CPL files, the designer reviews each line item, checks that the correct JLC part numbers have been matched, and manually corrects any mismatches before finalizing the order.[3] Community advice on JLCPCB emphasizes that occasionally the BOM parser misidentifies parts, and designers must ensure that each footprint is mapped to the intended component.[26]

For your project, this means:

1. For each major component (ESP32‑S3 module, TJA1021 transceivers, buck converter, TVS devices, connectors), confirm that the manufacturer and JLC/Seeed part numbers are correctly specified in the BOM, and that the footprints correspond.  
2. Avoid sprinkling in many unique component values for passives; instead, standardize on common values that fall within the “basic” set for cost efficiency, exploiting series/parallel combinations if needed for non‑standard values.[26]  
3. Verify that orientation markers (pin 1, polarity) for components like diodes and ICs are consistent between your silkscreen, the placement list, and the PCBA house’s library.  

This diligence upstream will dramatically reduce the likelihood of assembly defects and rework.

---

## 6. Automotive Environment and Safety Risks

### 6.1 RF Performance Inside a Steering Wheel

The steering wheel is a challenging RF environment. It often includes a metal frame (magnesium or steel), wiring, and in some cases metal‑backed airbag modules. RF design tutorials note that metal near an antenna can detune it, absorb RF energy, and reduce radiation efficiency.[25] The ESP32‑S3‑WROOM‑1‑N8R8 module has an integrated PCB antenna which expects free space on one side and clearance from ground and metal; its datasheet and reference designs specify keep‑out zones and ground cut‑outs.[1][3][25] Embedding such a module in a cavity surrounded by metal can significantly degrade BLE and Wi‑Fi range.

The ESP32‑S3‑WROOM‑1U‑N8R8 module, with a U.FL connector, allows you to route the RF signal to an external antenna placed behind a plastic trim piece or nearer the steering‑column shroud where there is more open space.[11][25] This can dramatically improve performance, but adds complexity: additional BOM items (coax cable, external antenna), potential assembly steps, and mechanical mounting challenges for the antenna.

Your design should include mechanical and RF flexibility. Place the module as close as feasible to a plastic window area, keep metal and ground copper clear around the antenna, and measure BLE performance in a representative steering‑wheel installation during your pilot run. If necessary, plan a second revision using the 1U module and external antenna. Also consider whether you need Wi‑Fi at all; if BLE alone suffices for your use case, you can optimize for lower data rates and shorter ranges, which are easier to achieve in constrained environments.

### 6.2 Automotive Electrical Transients: ESD, Cold Crank, Load Dump

Automotive 12 V systems are notoriously harsh. Transient voltage suppression (TVS) and robust DC‑DC conversion are central to protecting your module. TVS devices act as low‑impedance paths to ground during voltage surges, clamping the voltage and protecting sensitive components while presenting high impedance during normal operation.[21] Technical articles on load dump describe it as the condition where the battery is disconnected while the alternator is charging, producing a significant positive voltage surge that must be tolerated by the circuit or shunted to ground via TVS or other protective devices.[23]

Your 12 V input stage should therefore include:

1. A series input filter (fuse or polyfuse plus series impedance) to limit current and protect against short circuits.  
2. A high‑energy TVS diode between 12 V and ground, rated for automotive surges and located close to the connector.[21][23]  
3. Possibly a common‑mode choke or filtering network to reduce noise and EMI.  
4. A buck converter designed for automotive input ranges (e.g., 6–36 V) and able to tolerate transients, feeding a stable 5 V or 3.3 V rail for the ESP32 and LIN transceivers.[22][23]  

Both cold crank (voltage dips during engine start) and load dump must be considered in selecting the buck converter and TVS, as they dictate the maximum and minimum voltages the converter must survive and operate through. Automotive‑oriented regulator datasheets and application notes provide design examples for surviving these events; pick an IC that is explicitly rated for such conditions.

In addition, consider ESD on exposed connectors and LIN lines. ESD protection diodes on LIN bus pins, and careful routing and shielding, will reduce the risk of ESD‑induced failures. The LIN transceivers themselves typically include ESD protection and are designed to handle bus faults per automotive standards.[5][14]

### 6.3 Connector Strain Relief and Harness Labor

Mechanical reliability of the wiring harness is critical in steering‑wheel applications. Cable assemblies experience repeated motion as the wheel is turned, and poorly designed harnesses can suffer from broken conductors, intermittent connections, and strain at connector pins. Harness design guidance stresses the importance of proper bend radii, strain relief (such as overmolded boots or clamps), and secure routing away from sharp edges and moving parts.[29] 

Your PCB should provide robust mounting points for connectors and perhaps additional mechanical features (e.g., tie‑down holes) for harness strain relief. Depending on packaging, you may want to offload some of the harness integration to a specialist or at least specify standard automotive connectors with known reliability. For the purposes of assembly, PCBA houses typically provide only PCB‑level connector placement; harness manufacture and integration is a separate operation, often manual.

Harness labor can easily become the gating factor in your production rate at 100 units if each harness requires significant manual work. To minimize this, standardize harness designs, use prefabricated cables where possible, and ensure that connectors on the PCB are keyed and mistake‑proof.

### 6.4 Firmware Locking, OTA Updates, and Bricking Risk

Firmware and update strategy has safety implications. Automotive experiences show that firmware updates can occasionally brick vehicles; for example, a forum report on a Ford Mustang Mach‑E describes a car bricking during an OTA update, requiring service intervention and towing.[28] While your device operates at a much smaller scale, a bricked steering‑wheel module could disable steering‑wheel controls or other features. More importantly, using secure boot and flash encryption without a robust update and recovery path can render entire production batches inaccessible if key management is mishandled.[20]

To mitigate these risks:

1. Design your firmware such that failure modes are safe: if the ESP32 fails or resets, the LIN bus should pass through or at least hold a known, non‑interfering state.  
2. Use a proven bootloader and OTA implementation, testing update scenarios extensively in the lab.  
3. If you choose to enable secure boot, treat signing keys as critical infrastructure and maintain backups, revocation procedures, and recovery plans.[20]  
4. For early units, consider deferring secure boot until you are confident in the firmware pipeline.  

Also, clearly document how to physically reprogram a unit via the pogo‑pin fixture if an OTA update fails, and make sure this process is practical for your support workflows.

### 6.5 Legal and Safety Considerations for Steering-Wheel Modifications

Modifying or adding electronics in the steering wheel raises legal and safety questions. As the Tesla airbag recall documentation illustrates, even seemingly minor issues such as installing the wrong variant of an airbag for a given steering‑wheel design can be classified as a safety defect that must be remedied.[15] Your product should not alter airbag deployment behavior, wiring integrity, or steering control functions. However, any aftermarket device can still be scrutinized in the event of an incident.

You should:

1. Avoid altering or inserting your device in series with any airbag wiring or other safety‑critical circuits.  
2. Ensure that your module can be bypassed or removed without affecting basic vehicle operation.  
3. Provide clear disclaimers and installation instructions to end users or installers.  

If the product is intended for commercial sale, consult legal counsel familiar with automotive aftermarket regulations in your target markets. While 100 units may seem small, liability exposure exists even for modest volumes.

---

## 7. Concrete Manufacturing and Ordering Plan

### 7.1 Pilot Run: 5–10 Units

For a first pilot of 5–10 units, your goal is to validate the design electrically, mechanically, and in the real vehicle environment. The pilot should use exactly the same BOM, footprints, and PCBA provider as the eventual 100‑unit run, to reveal any manufacturing or sourcing issues early.

Component choices for the pilot:

1. ESP32‑S3‑WROOM‑1‑N8R8 as the main module, leveraging JLCPCB’s stocked part C2913201 in their assembly library.[1][10] Your PCB layout should still be compatible with the 1U variant, but the initial BOM will reference the 1 module.  
2. Two NXP TJA1021T/20/CM,118 LIN transceivers per board, matching JLCPCB’s library entry.[2][5][5]  
3. A buck regulator and passive network chosen from JLCPCB’s basic or extended parts, rated appropriately for 12 V automotive use and sized for your power budget.[12][16][21][22][23]  
4. TVS diodes and ESD protection on the 12 V input and LIN lines, also taken from the JLC/LCSC library.  
5. SMT connectors that are either basic or extended parts at JLCPCB, for the power and LIN harness interfaces.  
6. A full suite of passives (resistors, capacitors) that prioritize JLC “basic” values and packages, to minimize extended part fees.[12][16][26]  

Manufacturing steps for the pilot:

1. Finalize the KiCad design, ensuring correct footprints and following Espressif’s reference layout guidelines around the ESP32 module and antenna region.[1][3][25]  
2. Generate Gerber, drill, BOM, and CPL files.  
3. Use JLCPCB’s online ordering system to upload the files, select Standard PCBA service, and assign JLC part numbers (e.g., C2913201 for the ESP32 module and the correct ID for TJA1021). Review each BOM line for correct mapping.[1][2][4][4][26]  
4. Choose either single boards or a small panel (e.g., 2× or 4× panel) for assembly, depending on size and JLC’s capabilities.[12][17]  
5. Place the order for 5–10 assembled boards.  

Parallel to the PCB and PCBA order, design and fabricate a pogo‑pin programming and test fixture PCB, using pogo pins that contact your test pads. The fixture can be built either manually or via a low‑cost PCBA order, and the pogo pins can be inserted and soldered by hand.[19]

Once the pilot boards arrive, you will:

1. Hand‑install any necessary through‑hole connectors and mount the PCB in preliminary enclosures.  
2. Use the pogo‑pin fixture to program firmware and run tests, including LIN communication and BLE range in a test steering wheel or similar environment.  
3. Evaluate RF performance, thermal behavior, and overall robustness.  

Based on pilot findings, adjust the BOM if needed (e.g., choose different TVS diodes, adjust connector types, consider the 1U module and external antenna if RF is unsatisfactory).

### 7.2 Scaling to 100 Units

For the 100‑unit production run, use the same PCBA provider and workflow, incorporating any BOM tweaks from the pilot. At this stage, you can optimize costs further by:

1. Revisiting the BOM to reduce the number of unique extended parts, possibly substituting some passives with combinations of basic values, as suggested by JLC community guidance.[26]  
2. Deciding whether to keep the ESP32‑S3‑WROOM‑1‑N8R8 or switch to the 1U variant; if switching, ensure that JLC or your chosen provider can source the 1U module or accept consigned supply.[1][10][11][25]  
3. Finalizing panelization: design a panel layout that maximizes boards per panel while respecting spacing and including fiducials and rails. JLC can assist or implement panelization if requested.[12][17]  

Order details for the 100‑unit run (assuming JLCPCB Standard PCBA):

1. PCB: 4‑layer board, as small as practicable, using JLC’s standard stackup and material.  
2. Assembly: Standard PCBA with full SMT assembly on one side (and possibly both sides if needed), including the ESP32 module, LIN transceivers, power circuitry, protection devices, passives, and SMT connectors.  
3. Quantities: Order at least 110–120 boards to cover yield losses and provide a few spares.  
4. Components: Use JLC’s internal sourcing for all basic and extended parts; avoid consignment unless necessary for the ESP32‑S3‑WROOM‑1U‑N8R8 or specialized protection parts.[1][2][10][12][16][26]  

Once assembled boards are received, repeat the programming and test process using your pogo‑pin fixture and automated scripts. Harness assembly and mechanical integration can be run in parallel.

If you decide to use Seeed Fusion instead, the analogous plan applies: you provide the BOM with manufacturer part numbers, Seeed sources and assembles, and you coordinate programming and testing. The main difference is component sourcing flexibility and cost structure.[9][24]

---

## 8. Conclusion and Direct Recommendation

The proposed Tesla steering‑wheel dual‑LIN BLE passthrough module is well suited to low‑volume turnkey SMT assembly, provided that its BOM and design are aligned with the capabilities and catalogs of online PCBA providers. Your current core choice—ESP32‑S3‑WROOM‑1U‑N8R8 plus two NXP TJA1021T/20 LIN transceivers—remains a good technical architecture, but for practical manufacturing it is advisable to base the first production runs on ESP32‑S3‑WROOM‑1‑N8R8, which JLCPCB and LCSC stock as assembly‑ready part C2913201, while keeping the PCB layout compatible with the 1U variant for future RF optimization.[1][10][11][25] NXP’s TJA1021T/20/CM,118 is suitable as the LIN transceiver and appears in JLC’s component library, making it viable as an extended part.[2][5][5] As backups, TI’s TPIC1021D family provides an alternate LIN transceiver source if supply issues arise.[14]

Comparing PCBA options, JLCPCB Standard PCBA is the most straightforward and economical path for a 100‑unit run, offering integrated sourcing, clear capabilities, and direct support for your main components.[1][2][4][10][12][16][4][26] Seeed Fusion is a close alternative with more flexible component sourcing but generally somewhat higher costs.[9][24] PCBWay and MacroFab offer valuable options but either skew toward more complex or expensive engagements that may not be necessary at this scale.[7][8][13] A DigiKey/Mouser kit plus local assembly approach affords maximum control but substantially increases logistics and per‑unit cost.

To avoid hand soldering, you should target full SMT assembly for the ESP32 module, LIN transceivers, power‑management circuitry, ESD/TVS devices, passives, and SMT connectors, leaving only unusual through‑hole connectors and mechanical integration for manual work. Including test pads for programming and test, and designing a pogo‑pin programming fixture, allows efficient provisioning and functional testing without permanent connectors.[19] For production robustness, follow panelization best practices, include fiducials and tooling holes, and respect PCBA design rules.[12][17]

Automotive environment risks—RF performance inside the steering wheel, electrical transients on 12 V, connector strain, and safety considerations—must be actively managed. Use external antennas or careful placement if RF range is insufficient, protect the 12 V input with appropriate TVS and a robust buck converter, design harness and connector mounting for long‑term reliability, and ensure your module does not interfere with airbag or steering safety functions.[15][21][22][23][29] On the firmware side, plan a staged approach to security: start with non‑secure boot, refine OTA and recovery processes, and only then consider enabling ESP32 secure boot and flash encryption, mindful of bricking risks.[20][28]

A succinct recommendation for the owner:

1. For the pilot: design the PCB for ESP32‑S3‑WROOM‑1‑N8R8 with dual NXP TJA1021T/20/CM,118 transceivers, power and protection suited for 12 V automotive use, and sufficient test pads. Order 5–10 fully assembled boards from JLCPCB Standard PCBA, including module, LIN chips, buck regulator, TVS/ESD parts, passives, and SMT connectors, and build a pogo‑pin programming and test jig.  
2. For production: once pilot testing confirms the design, place a JLCPCB Standard PCBA order for around 110–120 boards (to net 100+ usable units), using the same BOM and panelization, and retain only harness connectors and mechanical integration as manual tasks. Consider migrating to the ESP32‑S3‑WROOM‑1U‑N8R8 plus external antenna only if field testing shows unacceptable RF performance with the PCB antenna.  

Following this plan allows you to produce 100 robust, professionally assembled steering‑wheel modules without hand soldering critical components, while keeping per‑unit cost and complexity under control and maintaining a path to greater security and refinement in future revisions.

## Citations

1. https://jlcpcb.com/partdetail/3198299-ESP32_S3_WROOM_1N8R8/C2913201 - https://jlcpcb.com/partdetail/3198299-ESP32_S3_WROOM_1N8R8/C2913201
2. https://jlcpcb.com/partdetail/NxpSemicon-TJA1021T_20_CM118/C128810 - https://jlcpcb.com/partdetail/NxpSemicon-TJA1021T_20_CM118/C128810
3. https://www.youtube.com/watch?v=EdEwRXiQsfc - https://www.youtube.com/watch?v=EdEwRXiQsfc
4. https://jlcpcb.com - https://jlcpcb.com
5. https://www.nxp.com/part/TJA1021T - https://www.nxp.com/part/TJA1021T
6. https://www.youtube.com/shorts/E9H-3JrzQ14 - https://www.youtube.com/shorts/E9H-3JrzQ14
7. https://www.pcbway.com/why.html - https://www.pcbway.com/why.html
8. https://www.macrofab.net - https://www.macrofab.net
9. https://www.seeedstudio.com/pcb-assembly.html - https://www.seeedstudio.com/pcb-assembly.html
10. https://www.lcsc.com/product-detail/C2913201.html - https://www.lcsc.com/product-detail/C2913201.html
11. https://www.tme.com/us/en-us/details/esp32s3-wrm1u-8r8/iot-wifi-bluetooth-modules/espressif/esp32-s3-wroom-1u-n8r8/ - https://www.tme.com/us/en-us/details/esp32s3-wrm1u-8r8/iot-wifi-bluetooth-modules/espressif/esp32-s3-wroom-1u-n8r8/
12. https://jlcpcb.com/capabilities/pcb-capabilities - https://jlcpcb.com/capabilities/pcb-capabilities
13. https://www.pcbway.com/capabilities.html - https://www.pcbway.com/capabilities.html
14. https://www.ti.com/product-category/interface/lin-transceivers/overview.html - https://www.ti.com/product-category/interface/lin-transceivers/overview.html
15. https://www.scribd.com/document/683327636/RCLRPT-23V743-2081 - https://www.scribd.com/document/683327636/RCLRPT-23V743-2081
16. https://jlcpcb.com/blog/category/pcb-assembly - https://jlcpcb.com/blog/category/pcb-assembly
17. https://www.allpcb.com/blog/pcb-manufacturing/pcb-panelization.html - https://www.allpcb.com/blog/pcb-manufacturing/pcb-panelization.html
18. https://docs.espressif.com/projects/esp-packaging/en/latest/esp32/02-dry-packing/index_module.html - https://docs.espressif.com/projects/esp-packaging/en/latest/esp32/02-dry-packing/index_module.html
19. https://www.youtube.com/watch?v=_JMplwjlzvk - https://www.youtube.com/watch?v=_JMplwjlzvk
20. https://docs.espressif.com/projects/esp-idf/en/stable/esp32/security/secure-boot-v2.html - https://docs.espressif.com/projects/esp-idf/en/stable/esp32/security/secure-boot-v2.html
21. https://www.diodes.com/design/support/technical-articles/transient-voltage-suppression-in-automotive - https://www.diodes.com/design/support/technical-articles/transient-voltage-suppression-in-automotive
22. https://www.espboards.dev/blog/powering-esp32-from-12v-power-source/ - https://www.espboards.dev/blog/powering-esp32-from-12v-power-source/
23. https://www.monolithicpower.com/en/learning/resources/from-cold-crank-to-load-dump-a-primer-on-automotive-transients - https://www.monolithicpower.com/en/learning/resources/from-cold-crank-to-load-dump-a-primer-on-automotive-transients
24. https://www.nextpcb.com/blog/turnkey-pcb-assembly-guide - https://www.nextpcb.com/blog/turnkey-pcb-assembly-guide
25. https://www.ema-eda.com/ema-resources/videos/whiteboard-wednesday-rf-shielding/ - https://www.ema-eda.com/ema-resources/videos/whiteboard-wednesday-rf-shielding/
26. https://forum.pedalpcb.com/threads/getting-started-with-pcba-at-jlcpcb.26836/ - https://forum.pedalpcb.com/threads/getting-started-with-pcba-at-jlcpcb.26836/
27. https://www.youtube.com/watch?v=gy9j16oixsY - https://www.youtube.com/watch?v=gy9j16oixsY
28. https://www.macheforum.com/site/threads/2nd-time-in-6-months-the-car-has-bricked-during-an-ota-update.50836/ - https://www.macheforum.com/site/threads/2nd-time-in-6-months-the-car-has-bricked-during-an-ota-update.50836/
29. https://www.katocable.com/why-wire-harness-design-impacts-product-reliability - https://www.katocable.com/why-wire-harness-design-impacts-product-reliability
