lakewoodphone/tesla-lin-chip/hardware/tesla-dual-lin-rev-a/build/autoroute-probe.kicad_pcb

## KiCad design hardware/tesla-dual-lin-rev-a/build/autoroute-probe.kicad_pcb (2026-06-17)

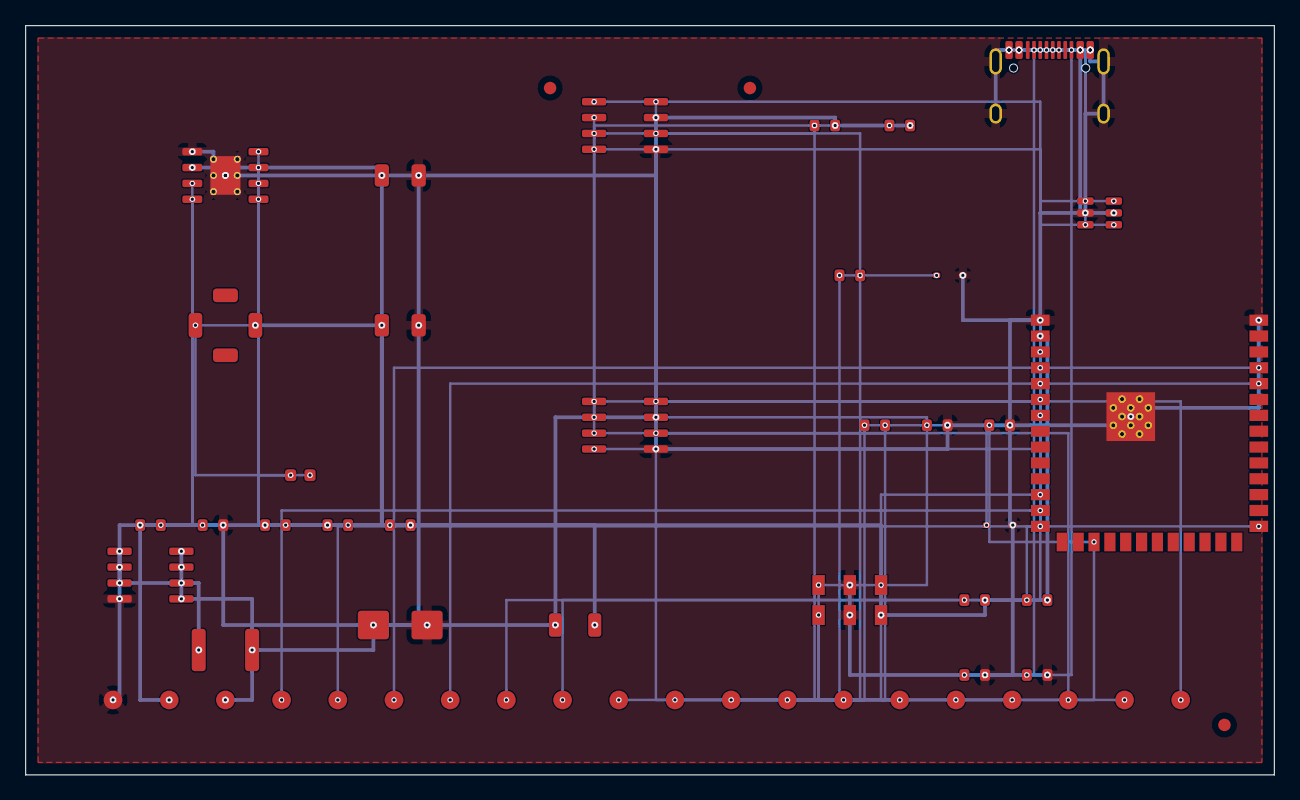
[picture p15: board autoroute-probe.kicad_pcb from above]

Board: 4 copper layers, 100.0 x 60.0 mm, 55 parts (0 on the bottom side), 35 nets.

Parts:
C_3V3: 22uF 10V; C_1206_3216Metric
C_BST: 100nF; C_0603_1608Metric
C_IN: 10uF 50V; C_1206_3216Metric
D1: SMBJ24A; D_SMB
D2: LIN_A ESD; D_SOD-323
D3: LIN_B ESD; D_SOD-323
D4: USB ESD; SOT-23-6
F1: 1812 PPTC; Fuse_1812_4532Metric
FB1: 1206 ferrite; L_1206_3216Metric
FID1, FID2, FID3: FID; Fiducial_1mm_Mask2mm
J1: USB-C; USB_C_Receptacle_HRO_TYPE-C-31-M-12
L1: 10uH; L_Bourns_SRU5016_5.2x5.2mm
Q1: AO4407A PFET; SOIC-8_3.9x4.9mm_P1.27mm
R_ARMSENSE_PD: 0603; R_0603_1608Metric
R_BOOT: 0603; R_0603_1608Metric
R_BUCK_EN: 0603; R_0603_1608Metric
R_BUCK_RON: 0603; R_0603_1608Metric
R_CC1, R_CC2: 0603; R_0603_1608Metric
R_EN: 0603; R_0603_1608Metric
R_FB_BOT: 0603; R_0603_1608Metric
R_FB_TOP: 0603; R_0603_1608Metric
R_LINA_SER: 0603; R_0603_1608Metric
R_LINB_SER: 0603; R_0603_1608Metric
R_LINEN_PD: 0603; R_0603_1608Metric
R_PGOOD_PU: 0603; R_0603_1608Metric
R_WAKE_A: 0603; R_0603_1608Metric
R_WAKE_B: 0603; R_0603_1608Metric
SW1: DPDT ARM; SW_DPDT_CK_JS202011JCQN
TP1: GND; TestPoint_Pad_D1.5mm
TP2: 3V3; TestPoint_Pad_D1.5mm
TP3: VBAT; TestPoint_Pad_D1.5mm
TP4: USB-; TestPoint_Pad_D1.5mm
TP5: USB+; TestPoint_Pad_D1.5mm
TP6: UART_TX; TestPoint_Pad_D1.5mm
TP7: UART_RX; TestPoint_Pad_D1.5mm
TP8: EN; TestPoint_Pad_D1.5mm
TP9: BOOT; TestPoint_Pad_D1.5mm
TP10: LIN_A; TestPoint_Pad_D1.5mm
TP11: LIN_B; TestPoint_Pad_D1.5mm
TP12: LIN_A_TJA; TestPoint_Pad_D1.5mm
TP13: LIN_B_TJA; TestPoint_Pad_D1.5mm
TP14: LIN_EN; TestPoint_Pad_D1.5mm
TP15: LIN_EN_DRV; TestPoint_Pad_D1.5mm
TP16: ARM; TestPoint_Pad_D1.5mm
TP17: WAKE_A; TestPoint_Pad_D1.5mm
TP18: WAKE_B; TestPoint_Pad_D1.5mm
TP19: INH_A; TestPoint_Pad_D1.5mm
TP20: INH_B; TestPoint_Pad_D1.5mm
U1: ESP32-S3-WROOM-1U
U2: TJA1021T car; SOIC-8_3.9x4.9mm_P1.27mm
U3: TJA1021T wheel; SOIC-8_3.9x4.9mm_P1.27mm
U4: LM5164DDA; HSOP-8-1EP_3.9x4.9mm_P1.27mm_EP2.41x3.1mm_ThermalVias

Connections:
3V3: C_3V3.1, L1.2, R_BOOT.2, R_EN.2, R_FB_TOP.1, R_PGOOD_PU.2, SW1.6, TP2.1, U1.2
ARM_SENSE: R_ARMSENSE_PD.1, SW1.4, TP16.1, U1.17
BOOT_GPIO0: R_BOOT.1, TP9.1, U1.27
BUCK_BST: C_BST.1, U4.7
BUCK_EN: R_BUCK_EN.2, U4.3
BUCK_FB: R_FB_BOT.1, R_FB_TOP.2, U4.5
BUCK_PGOOD: R_PGOOD_PU.1, U4.6
BUCK_RON: R_BUCK_RON.2, U4.4
BUCK_SW: C_BST.2, L1.1, U4.8
CC1: J1.A5, R_CC1.1
CC2: J1.B5, R_CC2.1
EN: R_EN.1, TP8.1, U1.3
GND: C_3V3.2, C_IN.2, D1.2, D2.2, D3.2, D4.2, J1.A1, J1.A12, J1.B1, J1.B12, J1.SH, Q1.4, R_ARMSENSE_PD.2, R_CC1.2, R_CC2.2, R_FB_BOT.2, R_LINEN_PD.2, SW1.2, SW1.5, TP1.1, U1.1, U1.40, U1.41, U2.5, U3.5, U4.1, U4.9
INH_A_TP: TP19.1, U2.8
INH_B_TP: TP20.1, U3.8
LIN_A: D2.1, R_LINA_SER.1, TP10.1
LIN_A_RXD: U1.4, U2.1
LIN_A_TJA: R_LINA_SER.2, TP12.1, U2.6
LIN_A_TXD: U1.5, U2.4
LIN_B: D3.1, R_LINB_SER.1, TP11.1
LIN_B_RXD: U1.6, U3.1
LIN_B_TJA: R_LINB_SER.2, TP13.1, U3.6
LIN_B_TXD: U1.7, U3.4
LIN_EN: R_LINEN_PD.1, SW1.1, TP14.1, U2.2, U3.2
LIN_EN_DRIVE: SW1.3, TP15.1, U1.12
UART0_RX: TP7.1, U1.36
UART0_TX: TP6.1, U1.37
USB_D_MINUS: D4.1, D4.6, J1.A7, J1.B7, TP4.1, U1.13
USB_D_PLUS: D4.3, D4.4, J1.A6, J1.B6, TP5.1, U1.14
USB_VBUS: D4.5, J1.A4, J1.A9, J1.B4, J1.B9
VBAT_FILTERED: C_IN.1, FB1.2, R_BUCK_EN.1, R_BUCK_RON.1, U4.2
VBAT_IN: F1.1, Q1.1, Q1.2, Q1.3
VBAT_PROTECTED: D1.1, F1.2, FB1.1, Q1.5, Q1.6, Q1.7, Q1.8, R_WAKE_A.2, R_WAKE_B.2, TP3.1, U2.7, U3.7
WAKE_A_N: R_WAKE_A.1, TP17.1, U2.3
WAKE_B_N: R_WAKE_B.1, TP18.1, U3.3
